OpeningDesign/CTR/XC_struct/calculation_report/ramp_wall/resLC/text/sectReport.tex

\begin{center}

\end{center}
\begin{center}

\end{center}
\newpage

\input{ramp_wall/resLC/text/sections/EBwallRCSects1.tex}
\begin{center}

\end{center}
\begin{center}

\end{center}
\input{ramp_wall/resLC/text/sections/EBwallRCSects2.tex}
\begin{center}

\end{center}
\begin{center}

\end{center}
\input{ramp_wall/resLC/text/sections/WBwallRCSects1.tex}
\begin{center}

\end{center}
\begin{center}

\end{center}
\input{ramp_wall/resLC/text/sections/WBwallRCSects2.tex}
\begin{center}

\end{center}
\begin{center}

\end{center}
\input{ramp_wall/resLC/text/sections/E1FwallRCSects1.tex}
\begin{center}

\end{center}
\begin{center}

\end{center}
\input{ramp_wall/resLC/text/sections/E1FwallRCSects2.tex}
\begin{center}

\end{center}
\begin{center}

\end{center}
\input{ramp_wall/resLC/text/sections/W1FwallRCSects1.tex}
\begin{center}

\end{center}
\begin{center}

\end{center}
\input{ramp_wall/resLC/text/sections/W1FwallRCSects2.tex}
\begin{center}

\end{center}
\begin{center}

\end{center}
\input{ramp_wall/resLC/text/sections/S1FwallRCSects1.tex}
\begin{center}

\end{center}
\begin{center}

\end{center}
\input{ramp_wall/resLC/text/sections/S1FwallRCSects2.tex}
\begin{center}

\end{center}
\begin{center}

\end{center}
