OpeningDesign/CTR/XC_struct/xc_models/wood_structure/stud_wall_design/anchor_bolts/regular_walls_anchor_bolts.ods

Anchor bolts for regular walls
5/8” GALV. BENT ANCHOR BOLT
@ 4’ O.C. (WITHIN 8” OF EVERY CORNER)
7” MIN. EMBEDMENT
