OpeningDesign/CTR/CA/Site Reports and Photos/20200724/20200724 - CTR - Site Report.md

<p align="right" style="" >

</p>

## The Current: Site Report: 07.24.2020

- Holddowns at the 2nd and 3rd floors, for both the east and west stair need to be installed.

- The inspector, will most likely require that this 'dead space' under the stairs be closed off with drywall.  Will most likely require a spinkler as well.  Confirm with Fire Protection engineer.
  
  - 

- Bear concrete slab on 3"x3"x1/4" galv angle attached with 5/8"x5" galv. anchor bolts at 24" o.c."
  
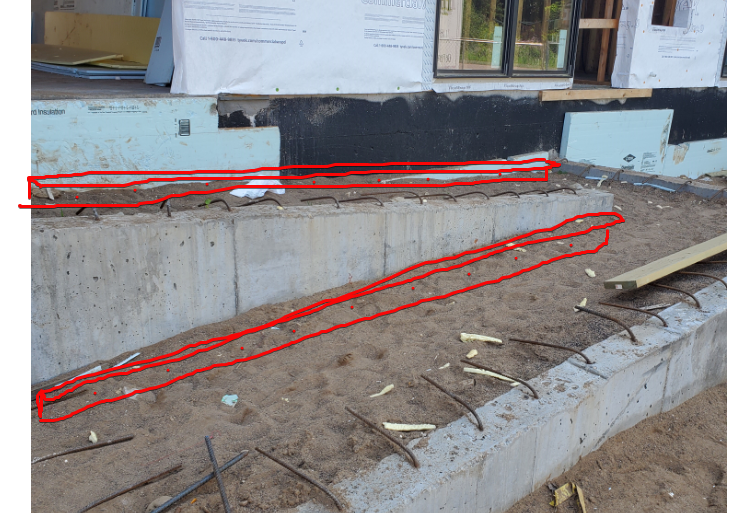
[picture p158: CA/Site Reports and Photos/20200724/2020-07-27_12-56-12_ApplicationFrameHostPhotosApplicationFrameHost.png]
  - 

- Assure the following clearances at Restroom 114
  
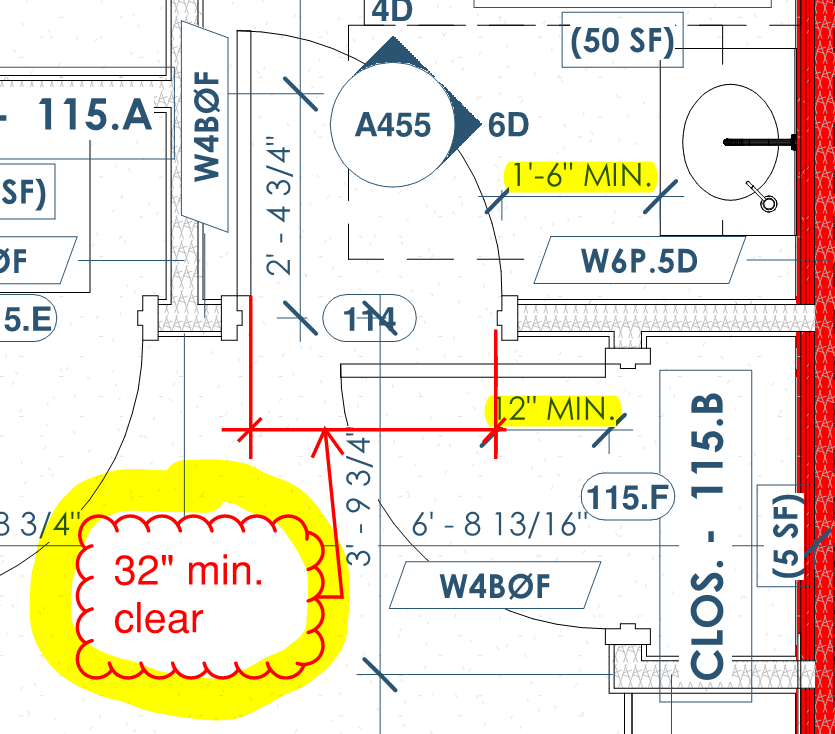
[picture p159: CA/Site Reports and Photos/20200724/2020-07-27_13-22-51_Revu_CTR_Binder_-_Bluebeam_Revu_x64Revu.png]
  - 

- Furr out wall to hide steel on the north elevation
  
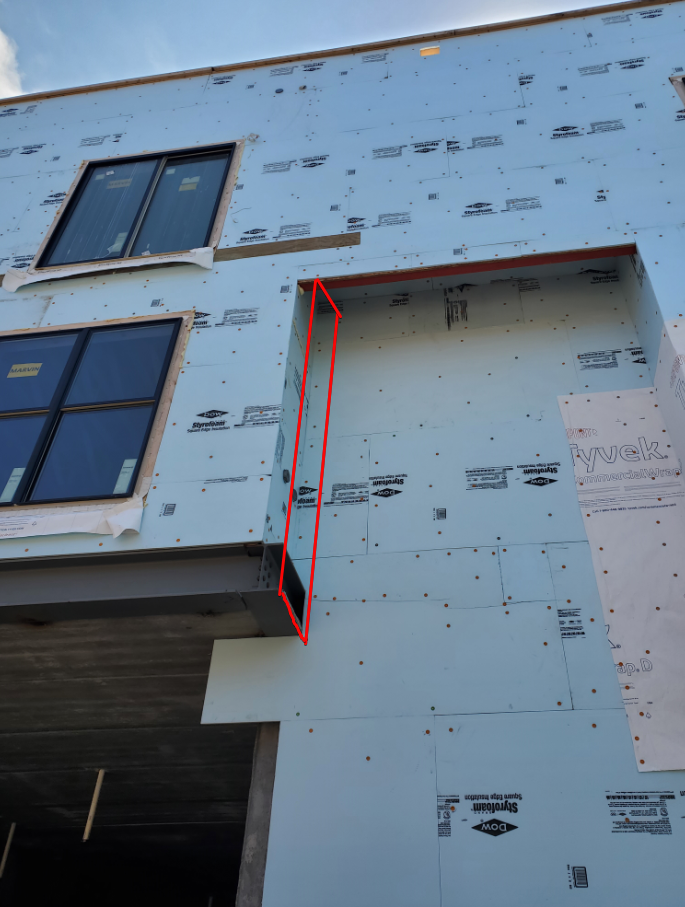
[picture p160: CA/Site Reports and Photos/20200724/2020-07-27_12-47-06_ApplicationFrameHost2020-07-24_13.30.31.jpg_‎-_PhotosApplicationFrameHost.png]
  - 

- Clean all the exposed CMU with wire brush to remove smears of surface mortar. 
  
  - 2020-07-24 13.21.52.jpg

- tighten bolts at all hold downs
  
  - 2020-07-24 13.18.43.jpg

- Missing fasteners at a few hanger locations throughout the various stair well stringers.
  
  - 2020-07-24 12.11.58.jpg

- Please take care to cover exposed concrete and/or CMU from over spray of stair paint. 
  
  - 2020-07-24 13.45.47.jpg

  ---
  
  ### 
  
  ### Outstanding from previous site report.

- Add additional sistered studs at column near LVL at elevator on 1st floor
  
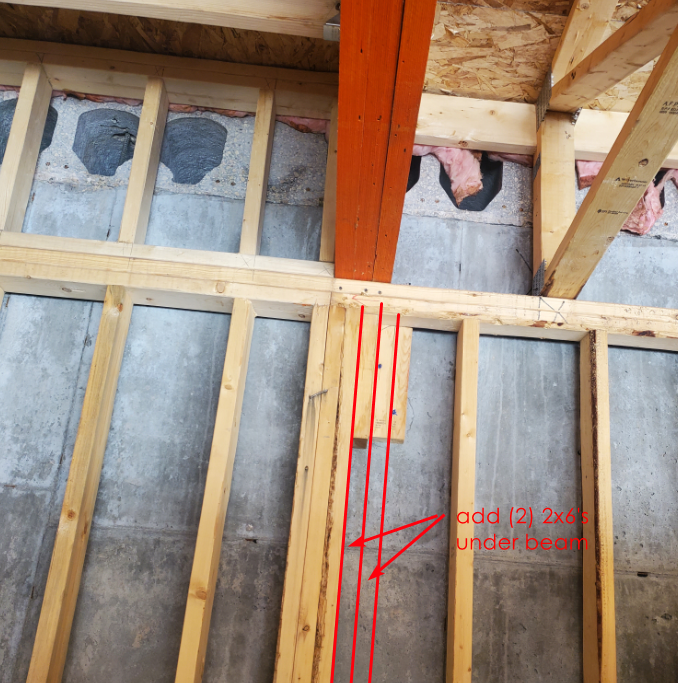
[picture p161: CA/Site Reports and Photos/20200724/2020-05-18-17-37-17-image.png]
  - 
  
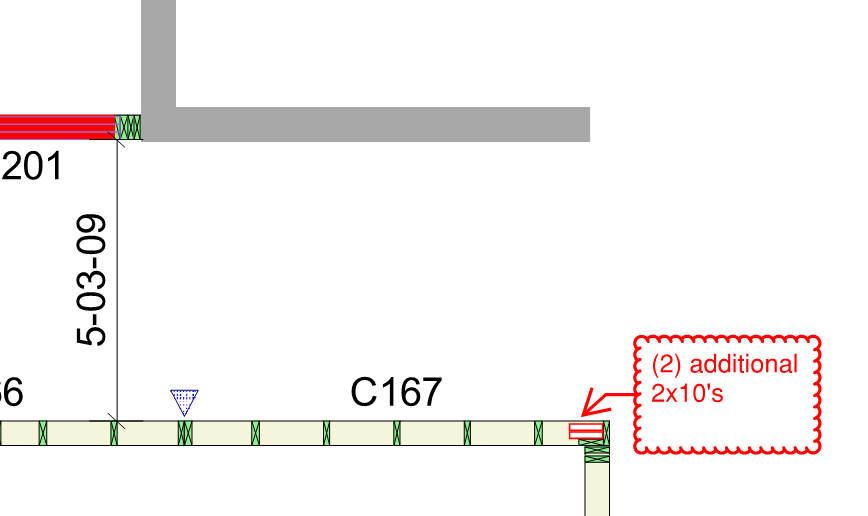
[picture p162: CA/Site Reports and Photos/20200724/2020-05-18-22-09-55-image.png]
  - 

- Add (2) additinal 2x10 at the following corner (near elevator) at both the 2nd and 3rd floors to transfer load down to 2nd floor steel beam
  
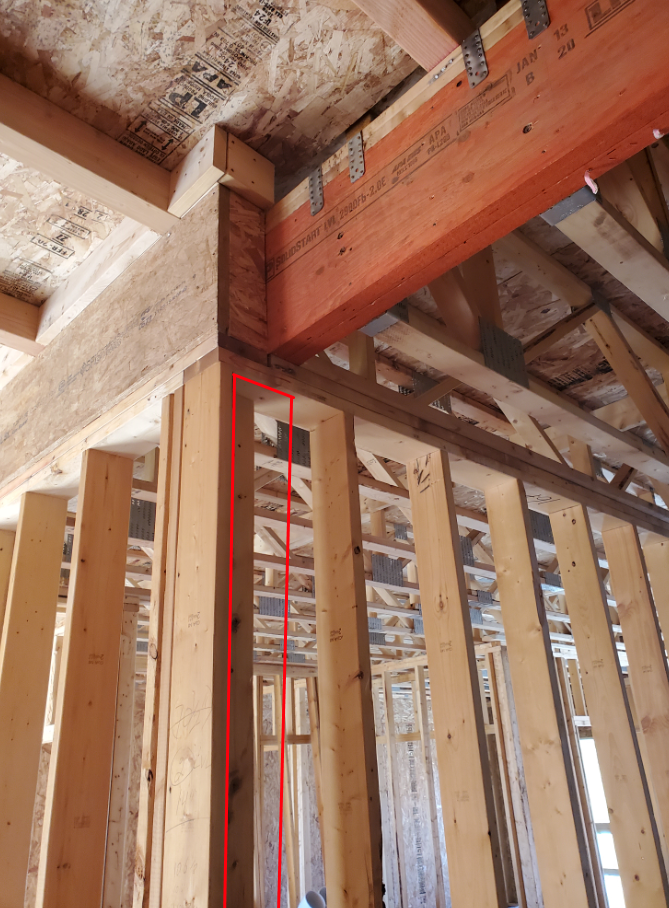
[picture p163: CA/Site Reports and Photos/20200724/2020-05-18-22-13-13-image.png]
  - 

- Add 2x ledger at elevator CMU to support floor sheathing
  
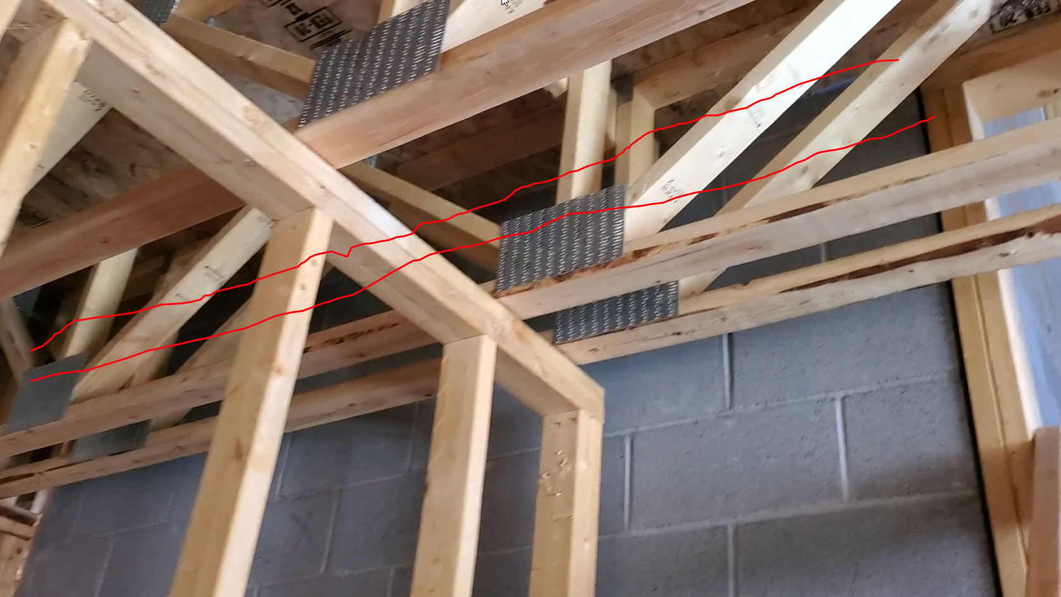
[picture p164: CA/Site Reports and Photos/20200724/2020-05-18-23-53-49-image.png]
  - 
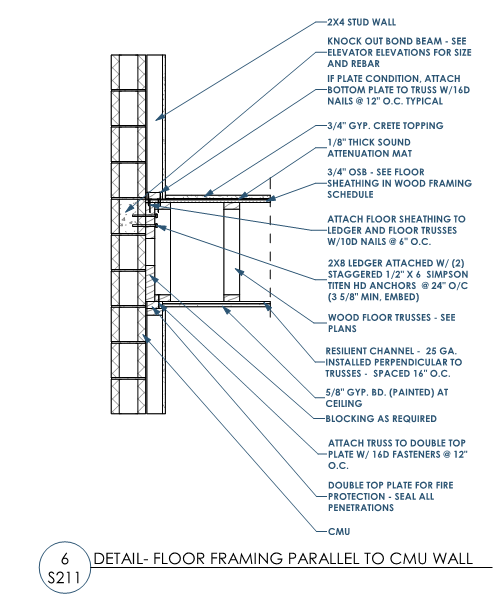
[picture p165: CA/Site Reports and Photos/20200724/2020-05-18-23-55-31-image.png]
  -
