OpeningDesign/CTR/CA/Site Reports and Photos/20200515/20200515 - CTR - Site Report.md

<p align="right" style="" >

</p>

## The Current: Site Report: 05.15.2020

- There were a number of conditions throughout the project where the girder truss that supports the jack trusses at the corner conditons was not sistered together (or it doesn't appear they were) as outlined in the truss shops.  See truss shops for exact detail for sistering

- There was a number of holddowns throughout the project that were missing.  Confirmed with GC that they are still in the process of installing
  
  <!--
  
  - Holddowns were not installed at the shear wall between U106 and U119.
  
  - Holddowns not installed on the west end of the shear wall between stair 108 and U110
  
  - No hold downs at shear wall between U126 and U124
  
  - missing holddowns at shearwall between U114 and U116
  
  - missing holddowns at shearwall between U114 and 105 and 104
  
  - missing holddowns at shearwall between 115 and U107
  
  - missing holddowns at shearwall between U125 and U123
  
  - missing holddowns at shearwall between U201 and 204
  
  - 
  -->

- Blocking above rim board needs (2) SDWS22500BD at each truss--all floors and at roof.  A number of locations only had (1) SDWS22500BD at each truss
  
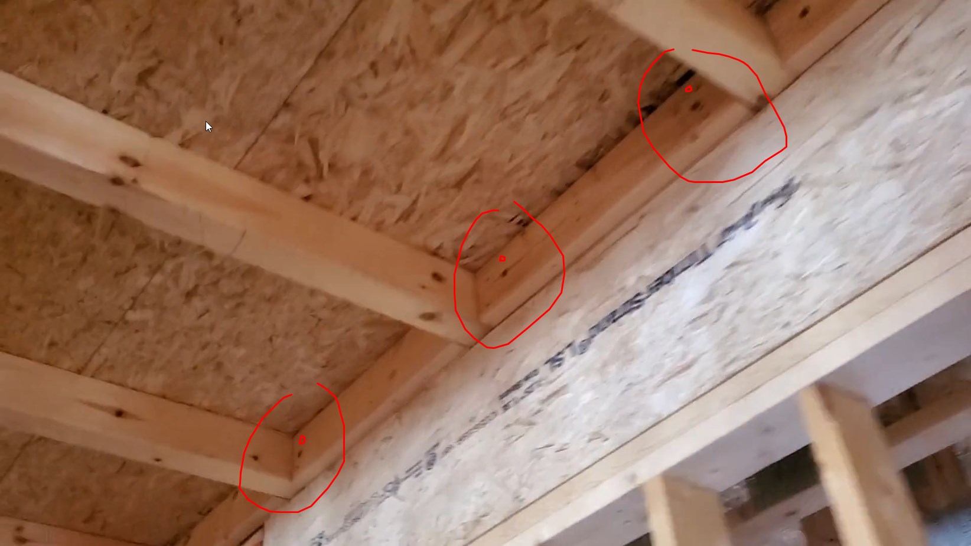
[picture p166: CA/Site Reports and Photos/20200515/vlc_YtFLORPniU.jpg]
  - 
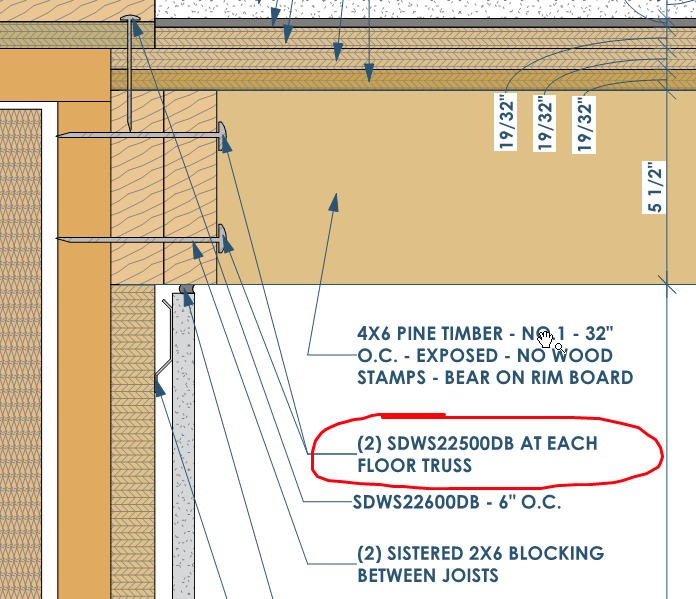
[picture p167: CA/Site Reports and Photos/20200515/2020-05-18-16-49-54-image.png]
  - 

- Install a built-up column of at least (3) 2x6's at all LVL beams throughout project.  Example condition...
  
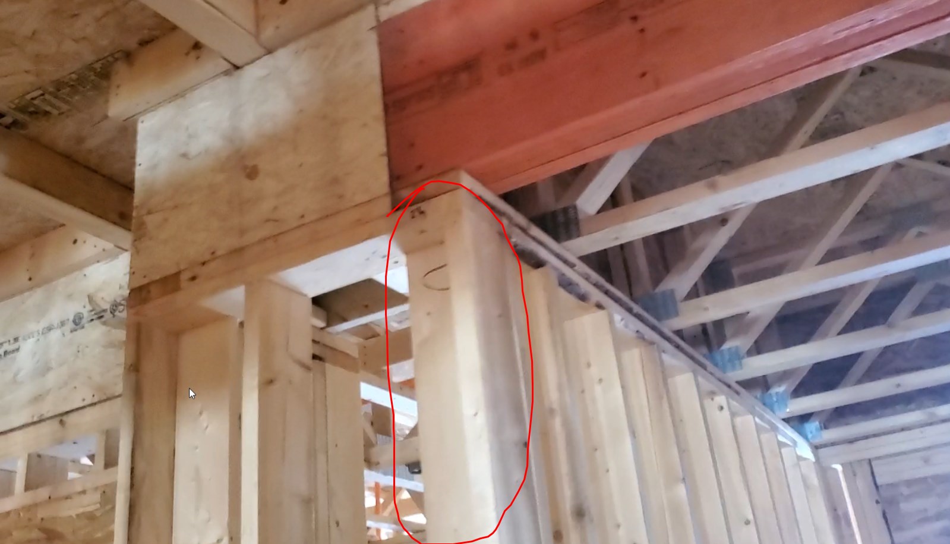
[picture p168: CA/Site Reports and Photos/20200515/ApplicationFrameHost_BQc5Hp7vTn.jpg]
  - 
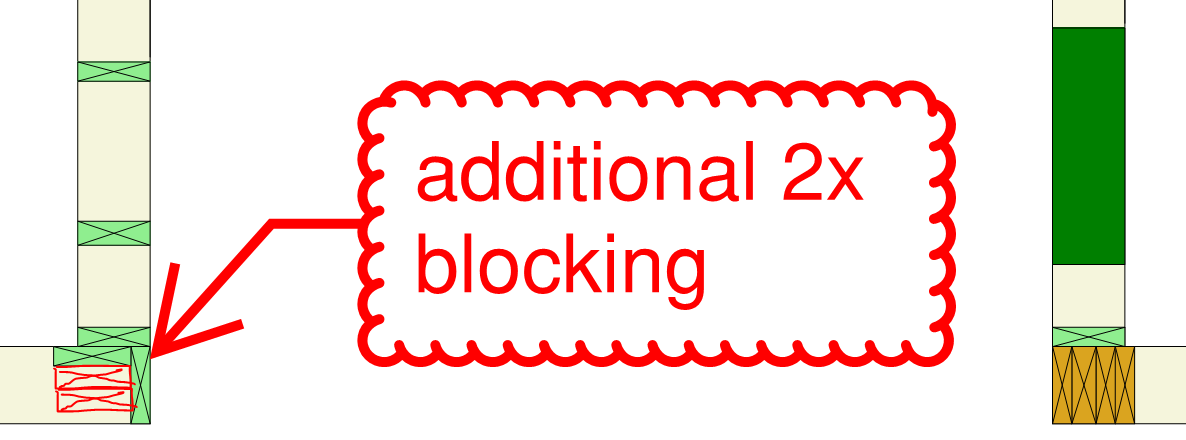
[picture p169: CA/Site Reports and Photos/20200515/2020-05-19-13-23-34-image.png]
  - 

- At Stairs
  
  - need (3) SDWS22600DB - SDWS STRUCTURAL SCREWS @ EACHVERTICAL STUD at the ledgers that bear multiple joists
  
  - need (2) SDWS22600DB - SDWS STRUCTURAL SCREWS @ EACH VERTICAL STUD at ledgers that do not bear joists
  
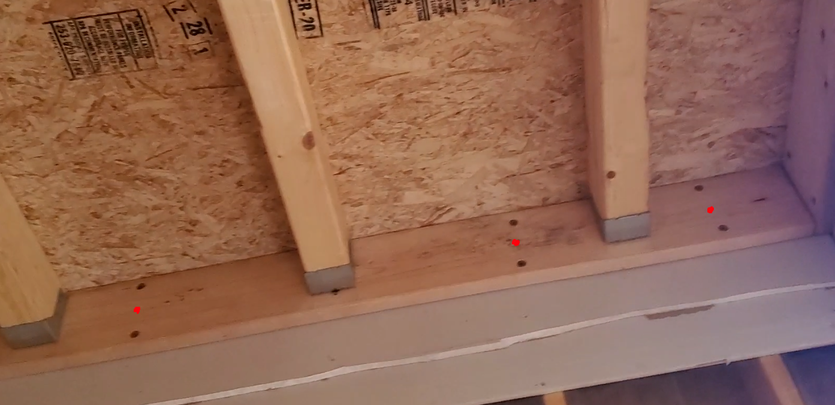
[picture p170: CA/Site Reports and Photos/20200515/vlc_ktL7A223v1.png]
  - 
  
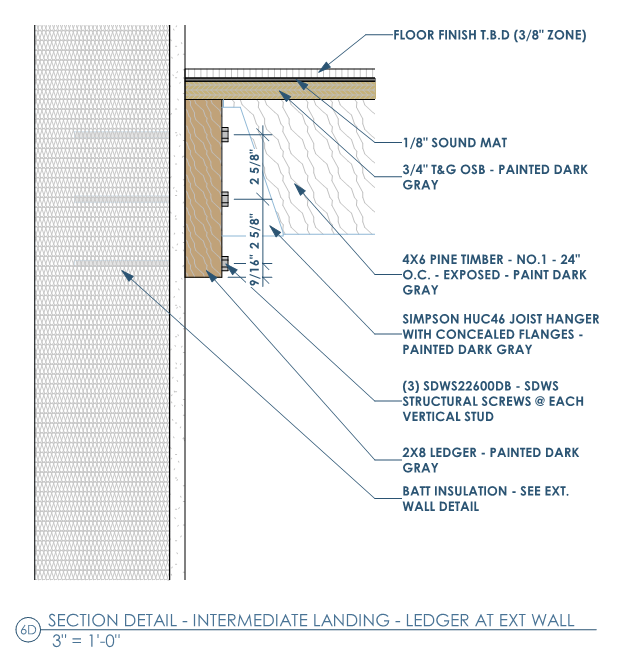
[picture p171: CA/Site Reports and Photos/20200515/Revu_8T4KtlkG9r.png]
  - 

- Add additional sistered studs at column near LVL at elevator on 1st floor
  
  - 

- At 3rd floor stair: Not enough room to slide (2) layers of drywall and 1/2" resilent channel between truss and stud.  Either move the truss or wrap truss with (2) layers of 5/8" Gyp. Bd--to continue 2hr wall up to deck.
  
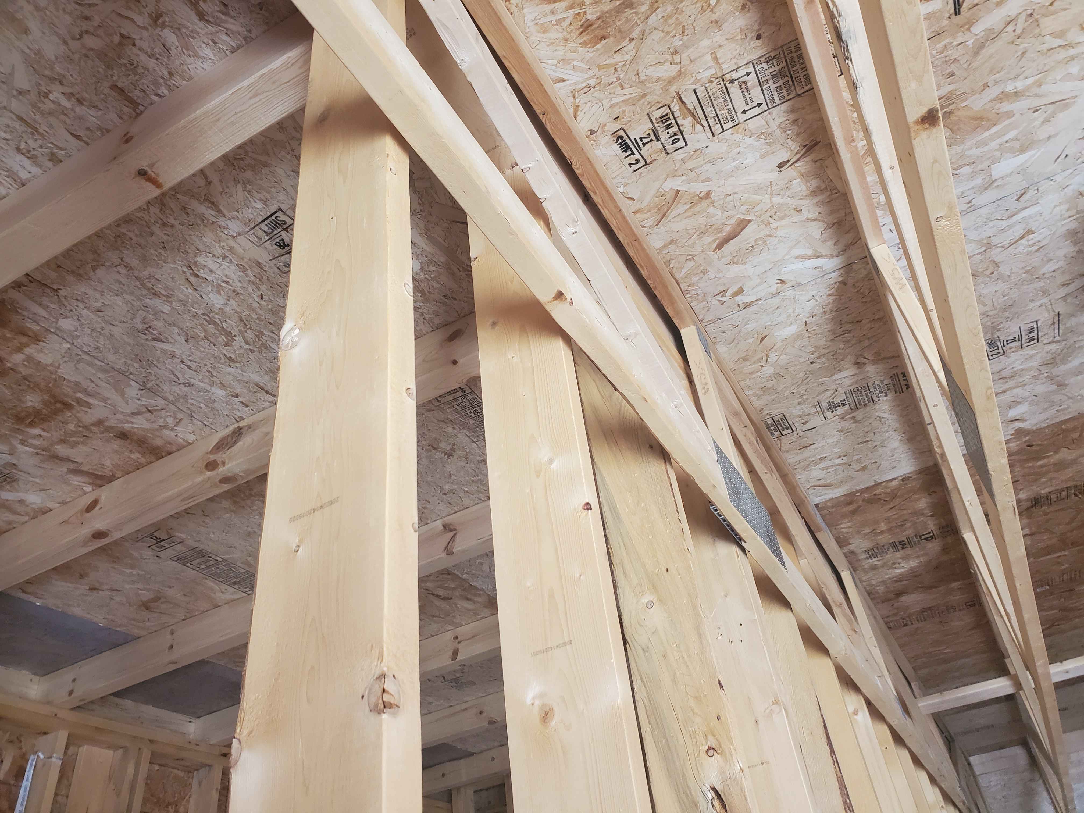
[picture p172: CA/Site Reports and Photos/20200515/14.13.54-3rd floor at roof near stair.jpg]
  - 

- Spacing of 4x6's at roof at/near stair is incorrect.  Need to be 24" o.c. at stair. 16" o.c. outside stair at corrido--to support the condensing units on the roof.
  
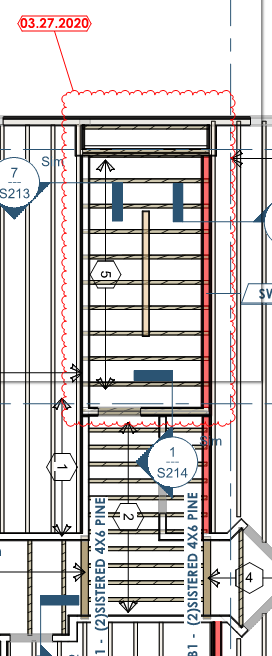
[picture p173: CA/Site Reports and Photos/20200515/2020-05-18-21-44-04-image.png]
  - 
  
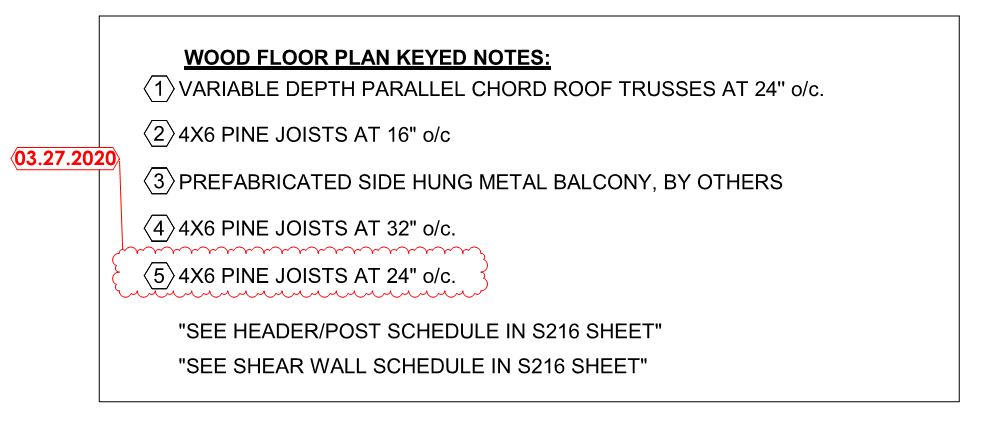
[picture p174: CA/Site Reports and Photos/20200515/2020-05-18-21-44-25-image.png]
  - 

- Add (2) additinal 2x10 at the following corner (near elevator) at both the 2nd and 3rd floors to transfer load down to 2nd floor steel beam
  
  - 
  - 

- Blocking at these conditions, similar to hallway, for the drywall to die into
  
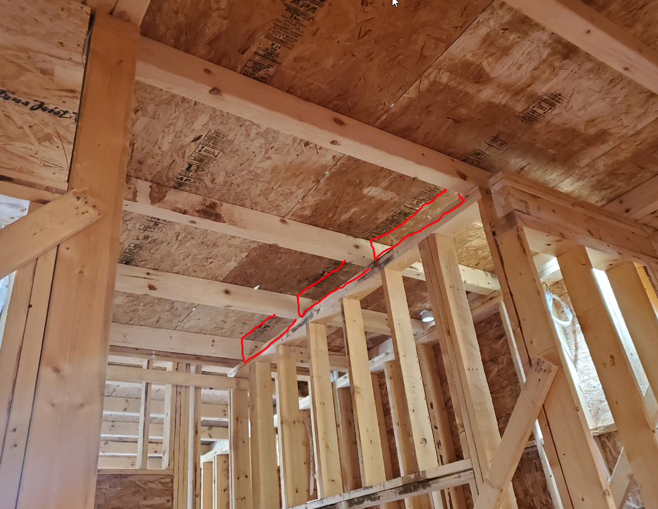
[picture p175: CA/Site Reports and Photos/20200515/2020-05-18-22-15-47-image.png]
  - 

- Blocking at entry to support load of balcony load down through wall studs
  
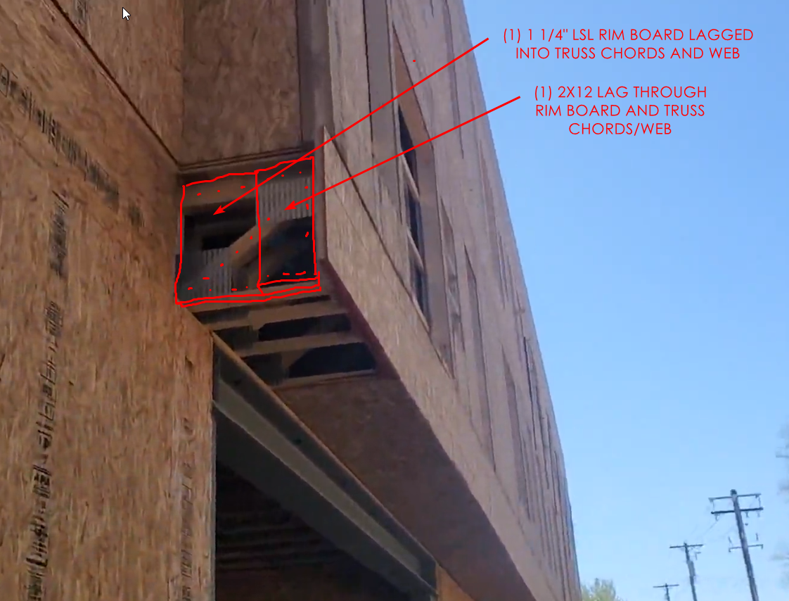
[picture p176: CA/Site Reports and Photos/20200515/vlc_qVF9NKEfCI.png]
  - 

- Add 2x ledger at elevator CMU to support floor sheathing
  
  - 
  - 

- Roof trusses need tie downs at all conditions on exterior and interior bearing walls--install was in progress.

<!--stackedit_data:
eyJoaXN0b3J5IjpbLTUzNzYwNjM1LDExMzk2NjQyMzYsMjA5MD
QwMTIwNCwyMTQ1ODQxNjcyLC0xMDkzMzQxMTMyXX0=
-->
