OpeningDesign/CTR/XC_struct/calculation_report/ramp_wall/resLC/text/report_resSimplLC.tex

\begin{figure}
\begin{center}
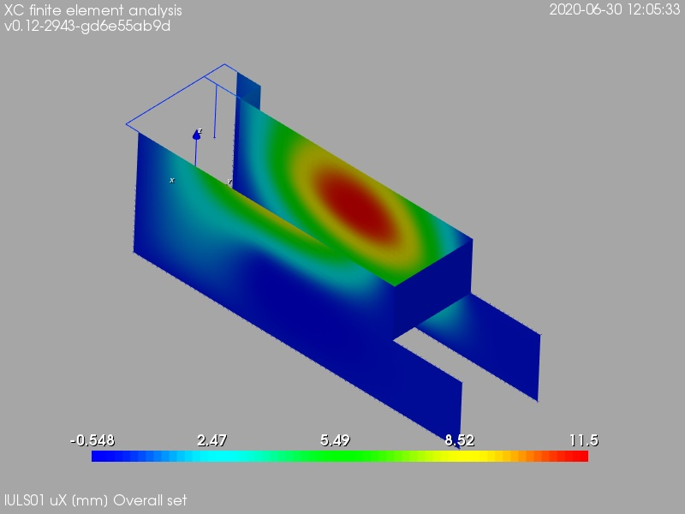
[picture p177: XC_struct/calculation_report/ramp_wall/resLC/text/graphics/resSimplLC/lULS01overallSetuX.jpg]

\caption{ULS01. Overall set, displacement in global X direction, [mm]}
\end{center}
\end{figure}
\begin{figure}
\begin{center}
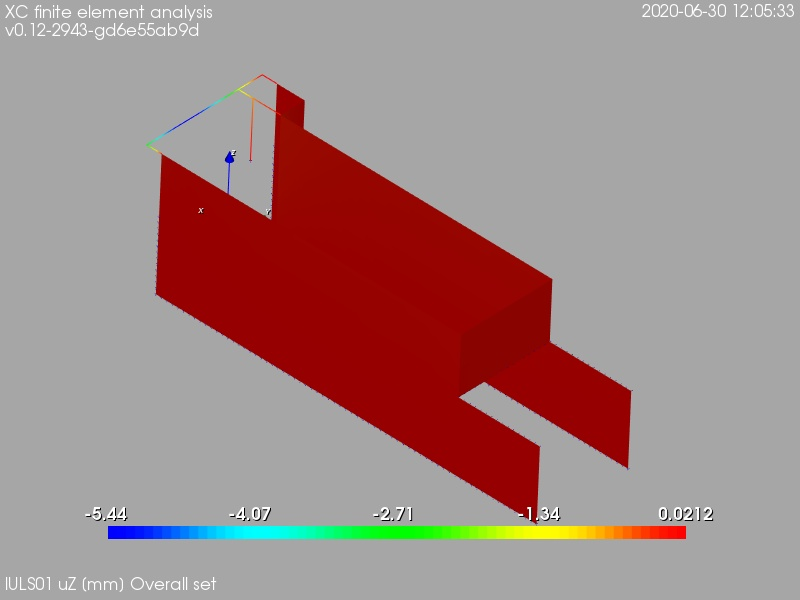
[picture p178: XC_struct/calculation_report/ramp_wall/resLC/text/graphics/resSimplLC/lULS01overallSetuZ.jpg]

\caption{ULS01. Overall set, displacement in global Z direction, [mm]}
\end{center}
\end{figure}
\begin{figure}
\begin{center}
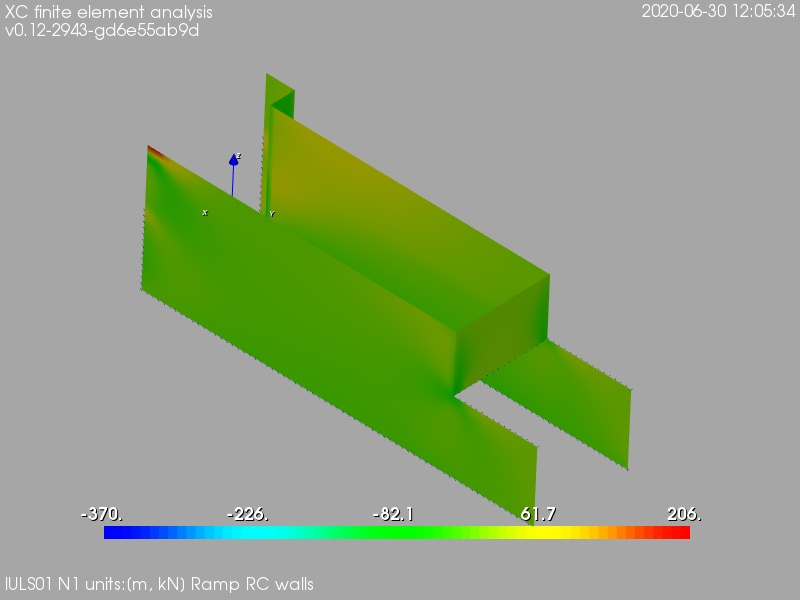
[picture p179: XC_struct/calculation_report/ramp_wall/resLC/text/graphics/resSimplLC/lULS01wallsN1.jpg]

\caption{ULS01. Ramp rc walls, internal axial force in local direction 1, units:[m, kN]}
\end{center}
\end{figure}
\begin{figure}
\begin{center}
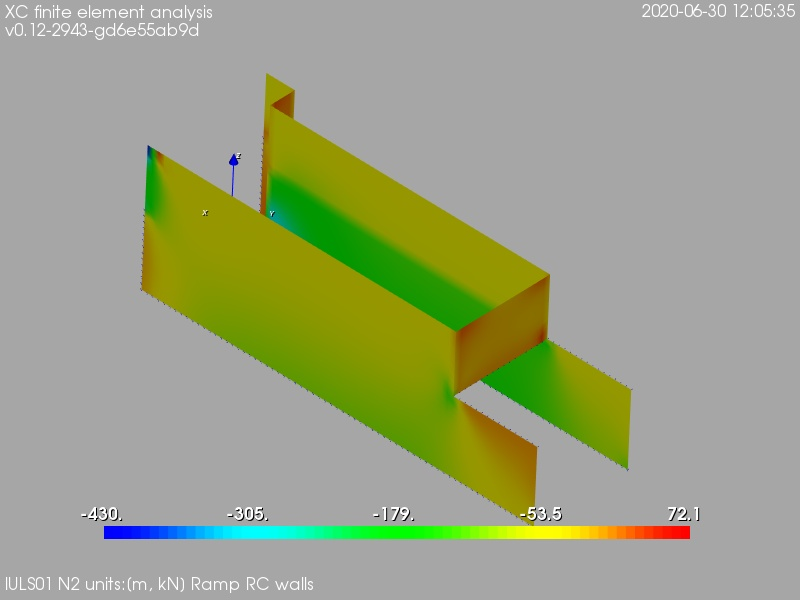
[picture p180: XC_struct/calculation_report/ramp_wall/resLC/text/graphics/resSimplLC/lULS01wallsN2.jpg]

\caption{ULS01. Ramp rc walls, internal axial force in local direction 2, units:[m, kN]}
\end{center}
\end{figure}
\begin{figure}
\begin{center}
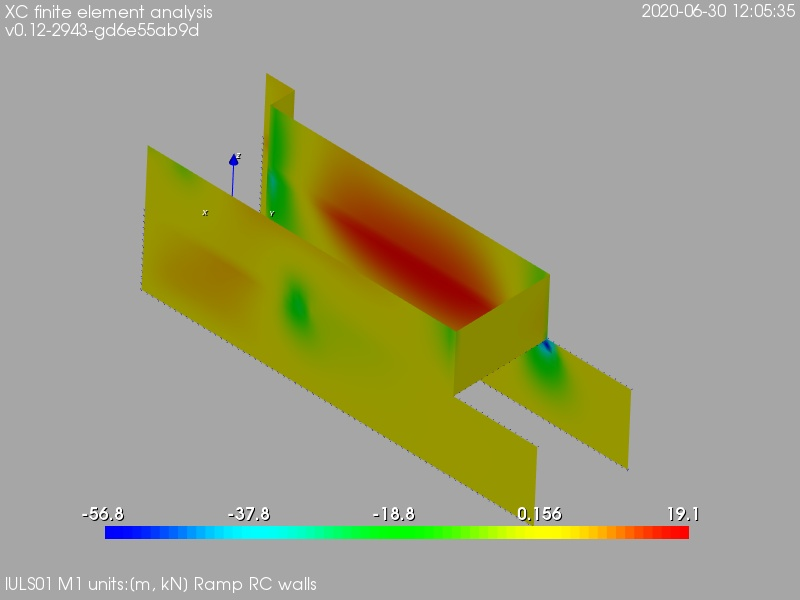
[picture p181: XC_struct/calculation_report/ramp_wall/resLC/text/graphics/resSimplLC/lULS01wallsM1.jpg]

\caption{ULS01. Ramp rc walls, bending moment about local axis 1, units:[m, kN]}
\end{center}
\end{figure}
\begin{figure}
\begin{center}
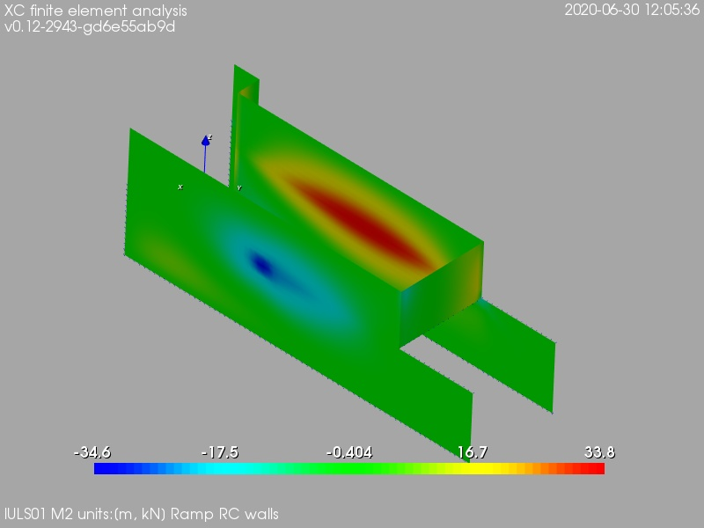
[picture p182: XC_struct/calculation_report/ramp_wall/resLC/text/graphics/resSimplLC/lULS01wallsM2.jpg]

\caption{ULS01. Ramp rc walls, bending moment about local axis 2, units:[m, kN]}
\end{center}
\end{figure}
\begin{figure}
\begin{center}
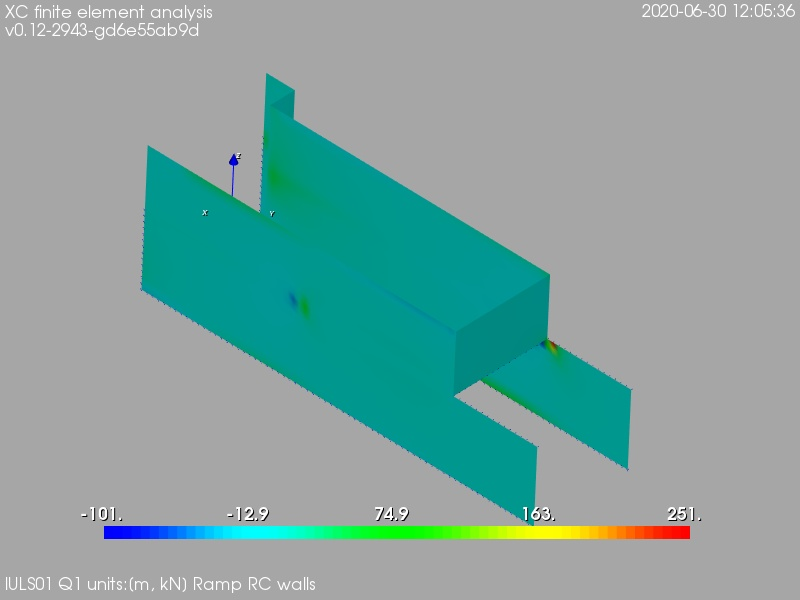
[picture p183: XC_struct/calculation_report/ramp_wall/resLC/text/graphics/resSimplLC/lULS01wallsQ1.jpg]

\caption{ULS01. Ramp rc walls, internal shear force in local direction 1, units:[m, kN]}
\end{center}
\end{figure}
\begin{figure}
\begin{center}
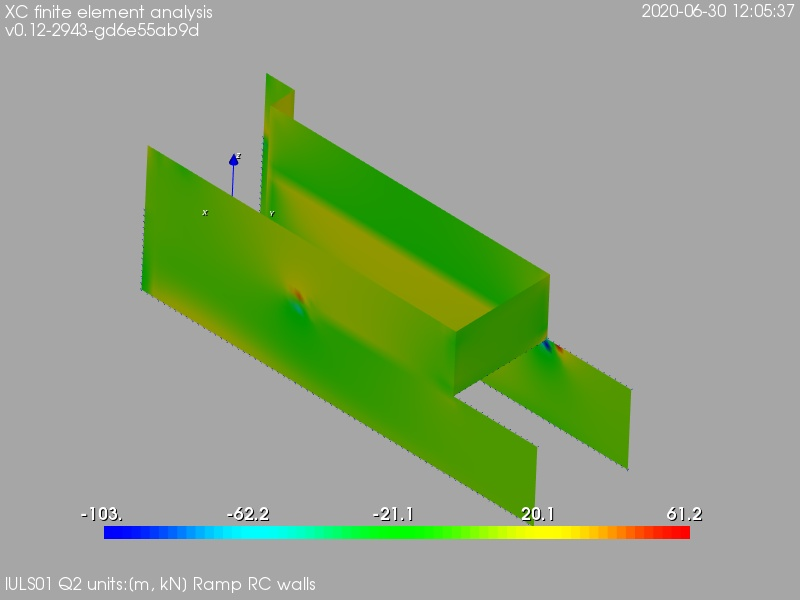
[picture p184: XC_struct/calculation_report/ramp_wall/resLC/text/graphics/resSimplLC/lULS01wallsQ2.jpg]

\caption{ULS01. Ramp rc walls, internal shear force in local direction 2, units:[m, kN]}
\end{center}
\end{figure}
\begin{figure}
\begin{center}
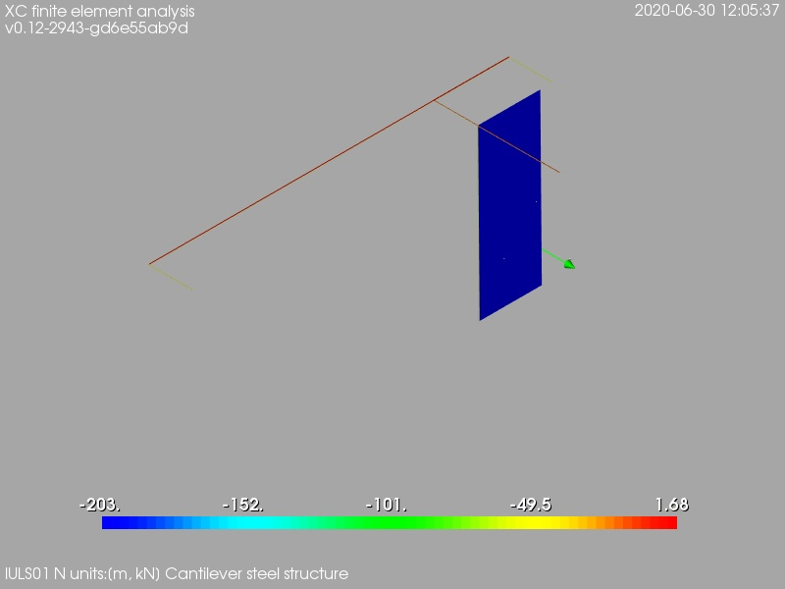
[picture p185: XC_struct/calculation_report/ramp_wall/resLC/text/graphics/resSimplLC/lULS01steelMembersN.jpg]

\caption{ULS01. Cantilever steel structure, internal axial force, units:[m, kN]}
\end{center}
\end{figure}
\begin{figure}
\begin{center}
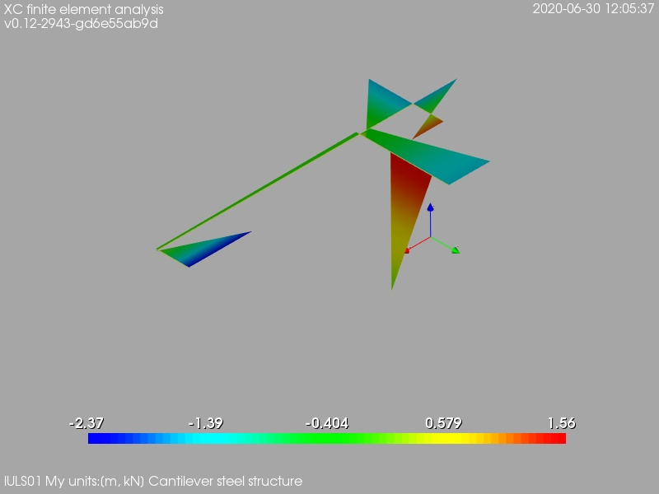
[picture p186: XC_struct/calculation_report/ramp_wall/resLC/text/graphics/resSimplLC/lULS01steelMembersMy.jpg]

\caption{ULS01. Cantilever steel structure, bending moment about local axis y, units:[m, kN]}
\end{center}
\end{figure}
\begin{figure}
\begin{center}
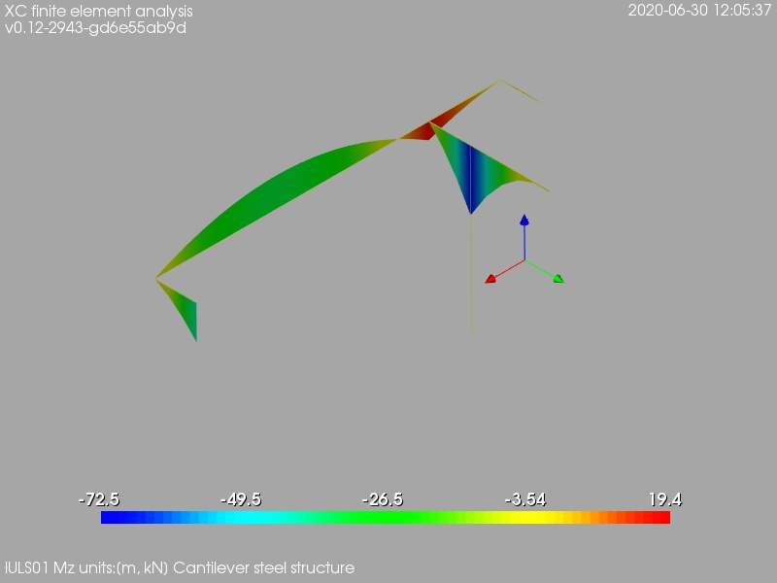
[picture p187: XC_struct/calculation_report/ramp_wall/resLC/text/graphics/resSimplLC/lULS01steelMembersMz.jpg]

\caption{ULS01. Cantilever steel structure, bending moment about local axis z, units:[m, kN]}
\end{center}
\end{figure}
\begin{figure}
\begin{center}
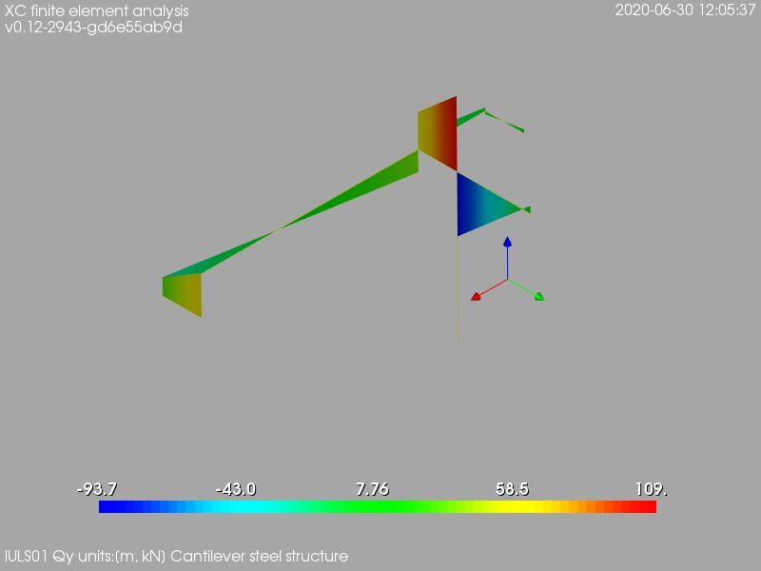
[picture p188: XC_struct/calculation_report/ramp_wall/resLC/text/graphics/resSimplLC/lULS01steelMembersQy.jpg]

\caption{ULS01. Cantilever steel structure, internal shear force in local direction y, units:[m, kN]}
\end{center}
\end{figure}
\begin{figure}
\begin{center}
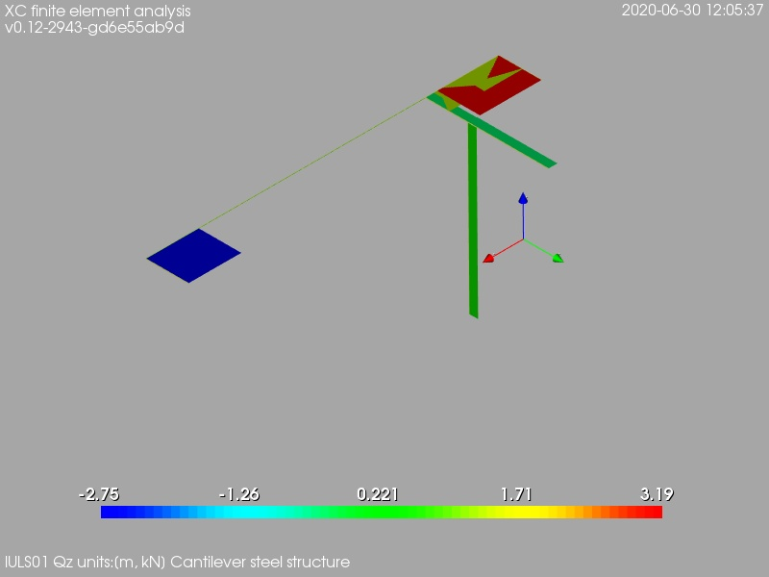
[picture p189: XC_struct/calculation_report/ramp_wall/resLC/text/graphics/resSimplLC/lULS01steelMembersQz.jpg]

\caption{ULS01. Cantilever steel structure, internal shear force in local direction z, units:[m, kN]}
\end{center}
\end{figure}
\clearpage
\begin{figure}
\begin{center}
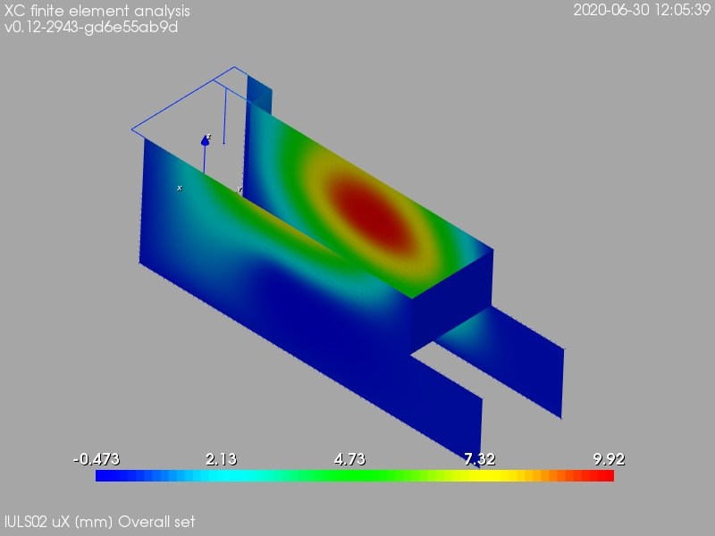
[picture p190: XC_struct/calculation_report/ramp_wall/resLC/text/graphics/resSimplLC/lULS02overallSetuX.jpg]

\caption{ULS02. Overall set, displacement in global X direction, [mm]}
\end{center}
\end{figure}
\begin{figure}
\begin{center}
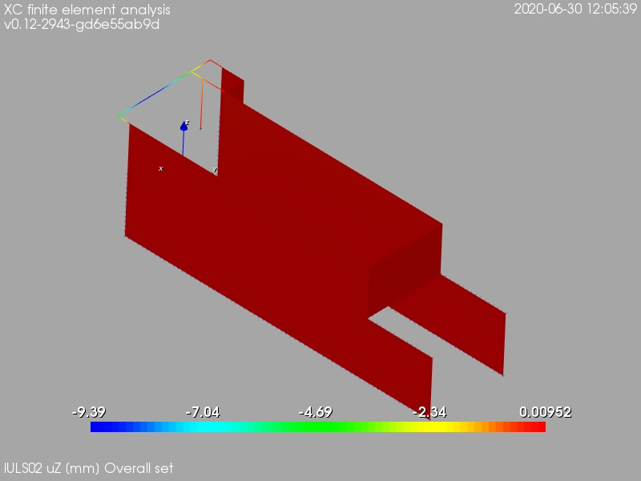
[picture p191: XC_struct/calculation_report/ramp_wall/resLC/text/graphics/resSimplLC/lULS02overallSetuZ.jpg]

\caption{ULS02. Overall set, displacement in global Z direction, [mm]}
\end{center}
\end{figure}
\begin{figure}
\begin{center}
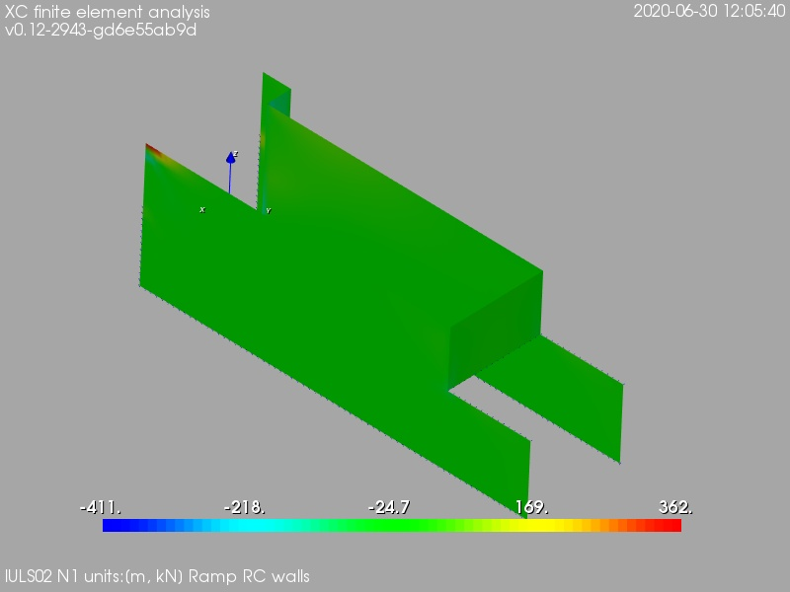
[picture p192: XC_struct/calculation_report/ramp_wall/resLC/text/graphics/resSimplLC/lULS02wallsN1.jpg]

\caption{ULS02. Ramp rc walls, internal axial force in local direction 1, units:[m, kN]}
\end{center}
\end{figure}
\begin{figure}
\begin{center}
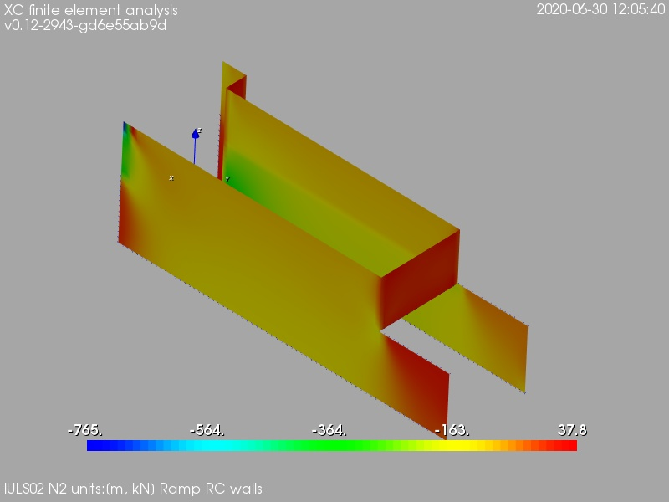
[picture p193: XC_struct/calculation_report/ramp_wall/resLC/text/graphics/resSimplLC/lULS02wallsN2.jpg]

\caption{ULS02. Ramp rc walls, internal axial force in local direction 2, units:[m, kN]}
\end{center}
\end{figure}
\begin{figure}
\begin{center}
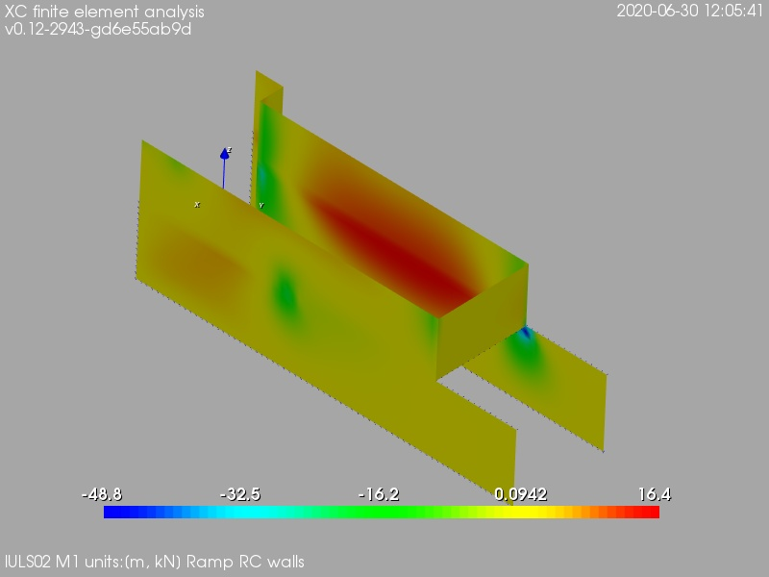
[picture p194: XC_struct/calculation_report/ramp_wall/resLC/text/graphics/resSimplLC/lULS02wallsM1.jpg]

\caption{ULS02. Ramp rc walls, bending moment about local axis 1, units:[m, kN]}
\end{center}
\end{figure}
\begin{figure}
\begin{center}
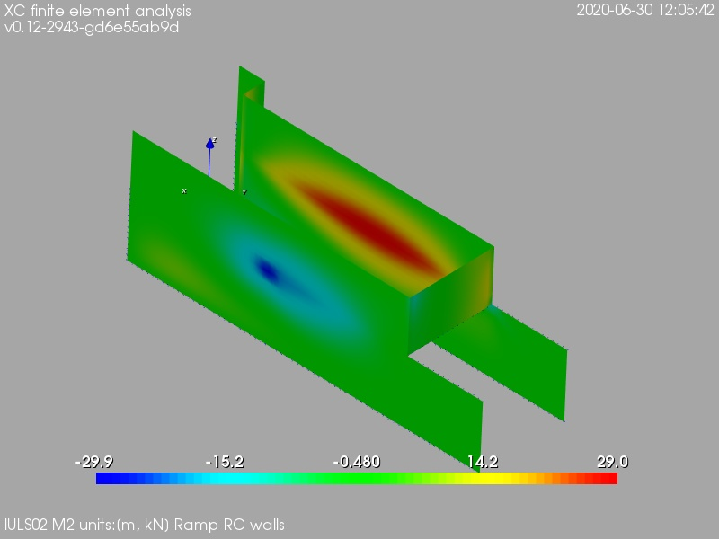
[picture p195: XC_struct/calculation_report/ramp_wall/resLC/text/graphics/resSimplLC/lULS02wallsM2.jpg]

\caption{ULS02. Ramp rc walls, bending moment about local axis 2, units:[m, kN]}
\end{center}
\end{figure}
\begin{figure}
\begin{center}
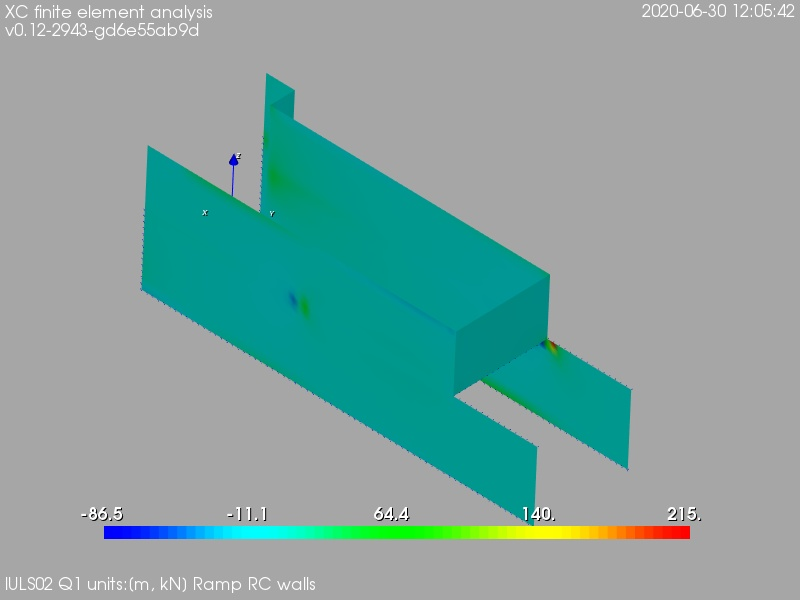
[picture p196: XC_struct/calculation_report/ramp_wall/resLC/text/graphics/resSimplLC/lULS02wallsQ1.jpg]

\caption{ULS02. Ramp rc walls, internal shear force in local direction 1, units:[m, kN]}
\end{center}
\end{figure}
\begin{figure}
\begin{center}
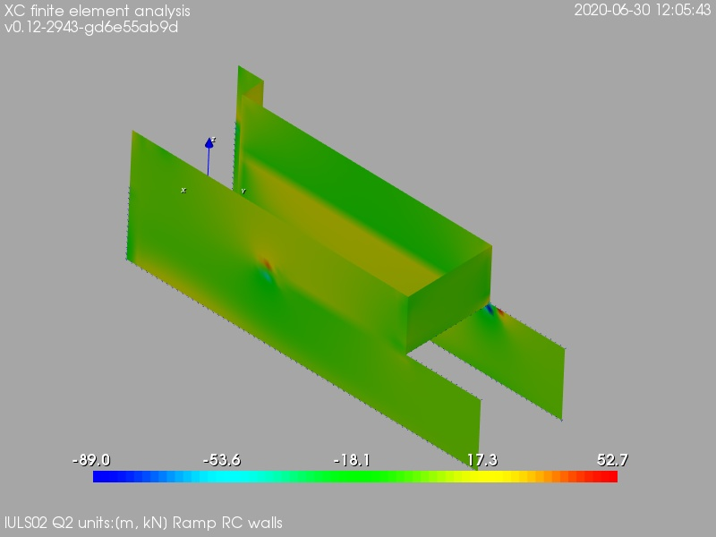
[picture p197: XC_struct/calculation_report/ramp_wall/resLC/text/graphics/resSimplLC/lULS02wallsQ2.jpg]

\caption{ULS02. Ramp rc walls, internal shear force in local direction 2, units:[m, kN]}
\end{center}
\end{figure}
\begin{figure}
\begin{center}
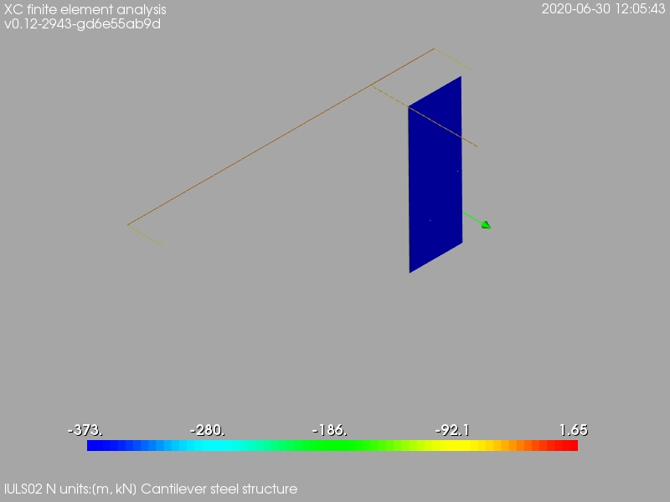
[picture p198: XC_struct/calculation_report/ramp_wall/resLC/text/graphics/resSimplLC/lULS02steelMembersN.jpg]

\caption{ULS02. Cantilever steel structure, internal axial force, units:[m, kN]}
\end{center}
\end{figure}
\begin{figure}
\begin{center}
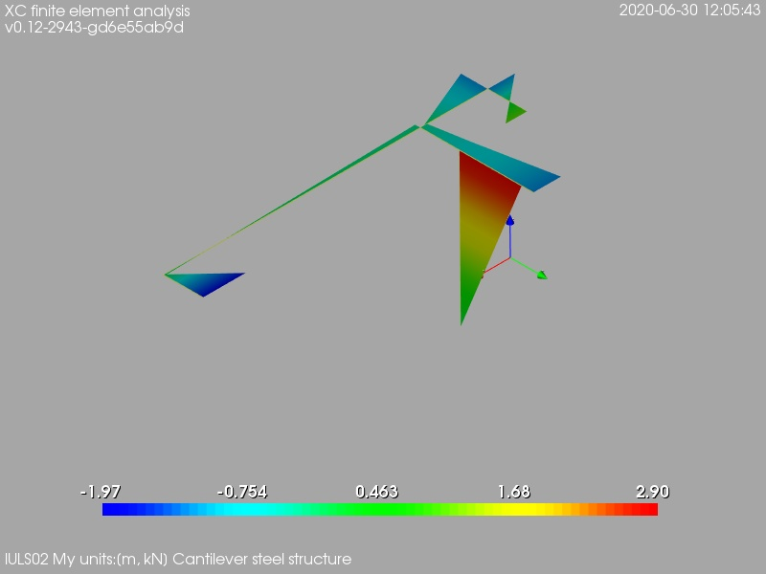
[picture p199: XC_struct/calculation_report/ramp_wall/resLC/text/graphics/resSimplLC/lULS02steelMembersMy.jpg]

\caption{ULS02. Cantilever steel structure, bending moment about local axis y, units:[m, kN]}
\end{center}
\end{figure}
\begin{figure}
\begin{center}
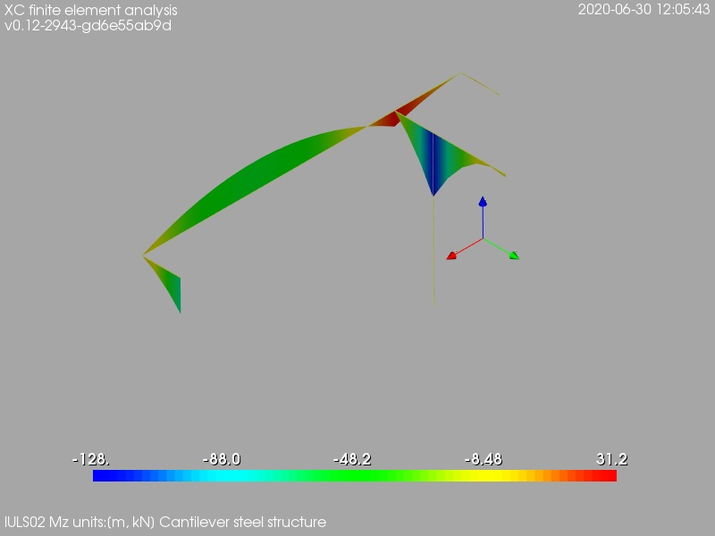
[picture p200: XC_struct/calculation_report/ramp_wall/resLC/text/graphics/resSimplLC/lULS02steelMembersMz.jpg]

\caption{ULS02. Cantilever steel structure, bending moment about local axis z, units:[m, kN]}
\end{center}
\end{figure}
\begin{figure}
\begin{center}
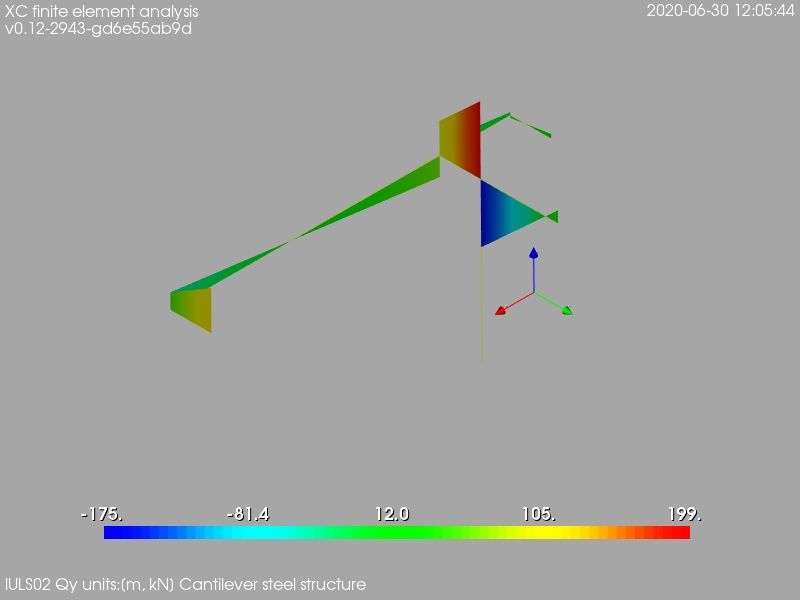
[picture p201: XC_struct/calculation_report/ramp_wall/resLC/text/graphics/resSimplLC/lULS02steelMembersQy.jpg]

\caption{ULS02. Cantilever steel structure, internal shear force in local direction y, units:[m, kN]}
\end{center}
\end{figure}
\begin{figure}
\begin{center}
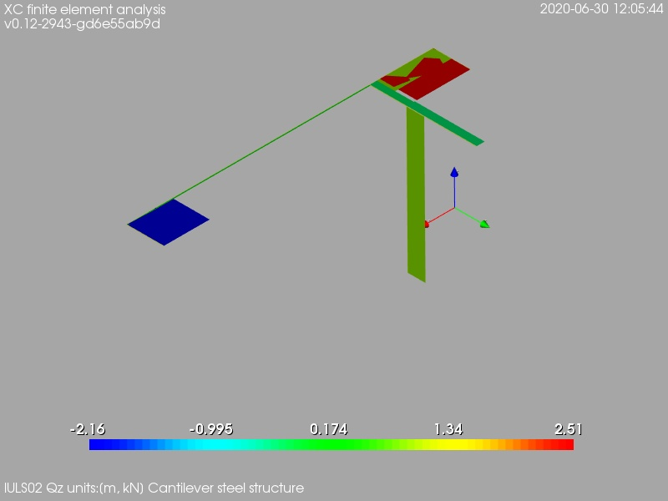
[picture p202: XC_struct/calculation_report/ramp_wall/resLC/text/graphics/resSimplLC/lULS02steelMembersQz.jpg]

\caption{ULS02. Cantilever steel structure, internal shear force in local direction z, units:[m, kN]}
\end{center}
\end{figure}
\clearpage
\begin{figure}
\begin{center}
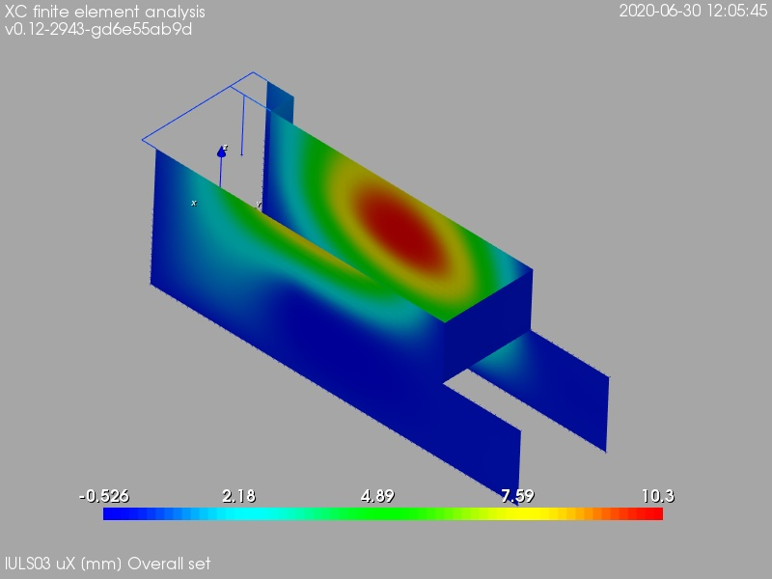
[picture p203: XC_struct/calculation_report/ramp_wall/resLC/text/graphics/resSimplLC/lULS03overallSetuX.jpg]

\caption{ULS03. Overall set, displacement in global X direction, [mm]}
\end{center}
\end{figure}
\begin{figure}
\begin{center}
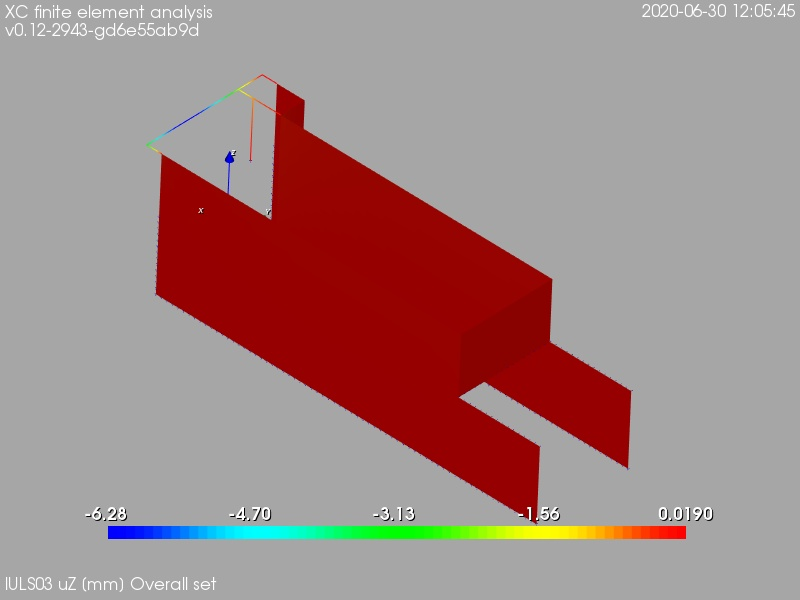
[picture p204: XC_struct/calculation_report/ramp_wall/resLC/text/graphics/resSimplLC/lULS03overallSetuZ.jpg]

\caption{ULS03. Overall set, displacement in global Z direction, [mm]}
\end{center}
\end{figure}
\begin{figure}
\begin{center}
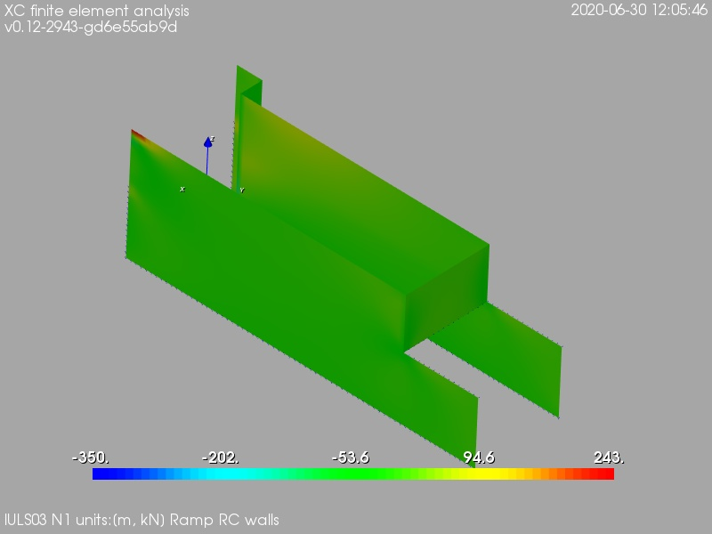
[picture p205: XC_struct/calculation_report/ramp_wall/resLC/text/graphics/resSimplLC/lULS03wallsN1.jpg]

\caption{ULS03. Ramp rc walls, internal axial force in local direction 1, units:[m, kN]}
\end{center}
\end{figure}
\begin{figure}
\begin{center}
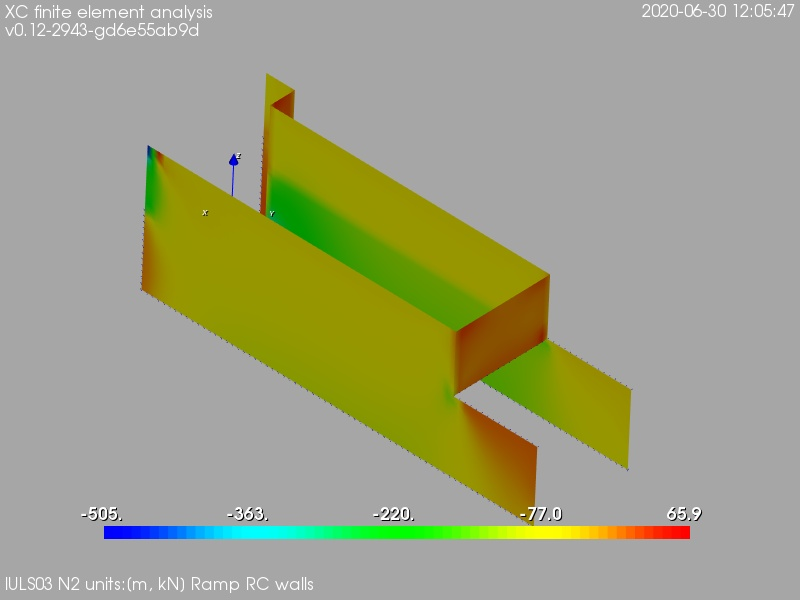
[picture p206: XC_struct/calculation_report/ramp_wall/resLC/text/graphics/resSimplLC/lULS03wallsN2.jpg]

\caption{ULS03. Ramp rc walls, internal axial force in local direction 2, units:[m, kN]}
\end{center}
\end{figure}
\begin{figure}
\begin{center}
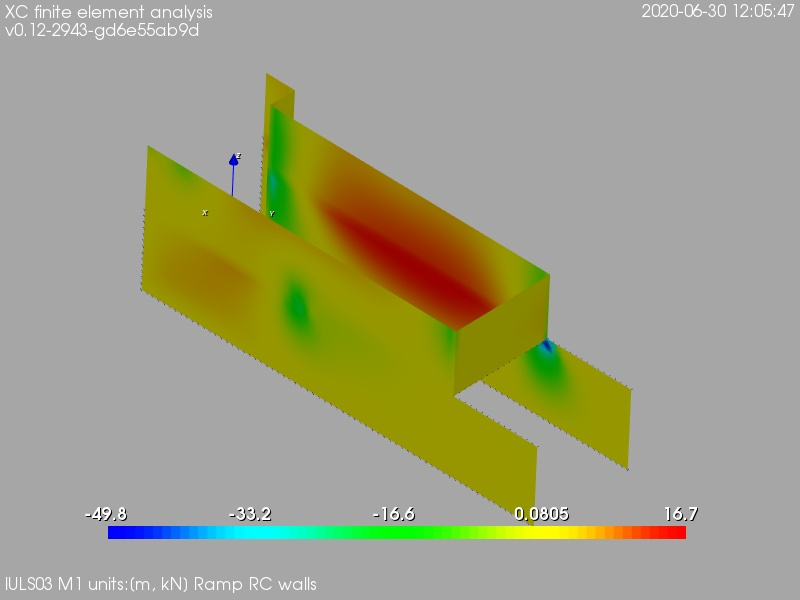
[picture p207: XC_struct/calculation_report/ramp_wall/resLC/text/graphics/resSimplLC/lULS03wallsM1.jpg]

\caption{ULS03. Ramp rc walls, bending moment about local axis 1, units:[m, kN]}
\end{center}
\end{figure}
\begin{figure}
\begin{center}
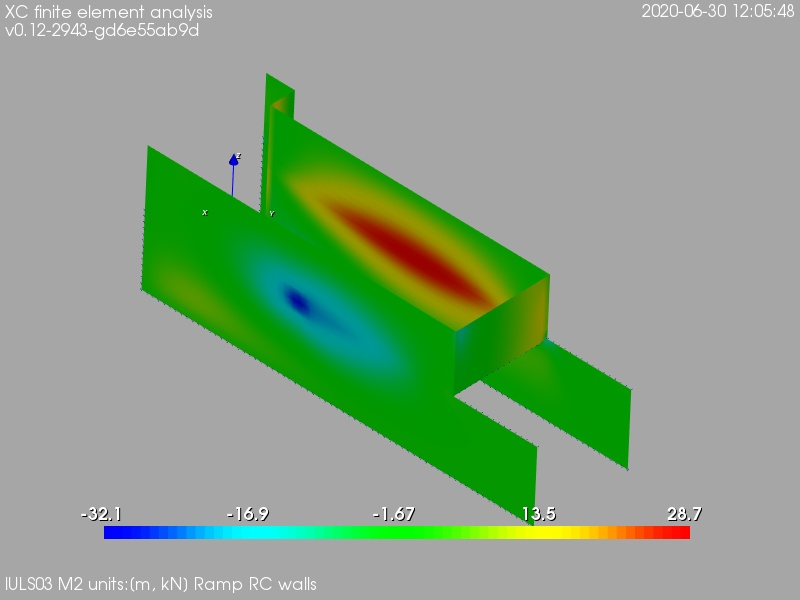
[picture p208: XC_struct/calculation_report/ramp_wall/resLC/text/graphics/resSimplLC/lULS03wallsM2.jpg]

\caption{ULS03. Ramp rc walls, bending moment about local axis 2, units:[m, kN]}
\end{center}
\end{figure}
\begin{figure}
\begin{center}
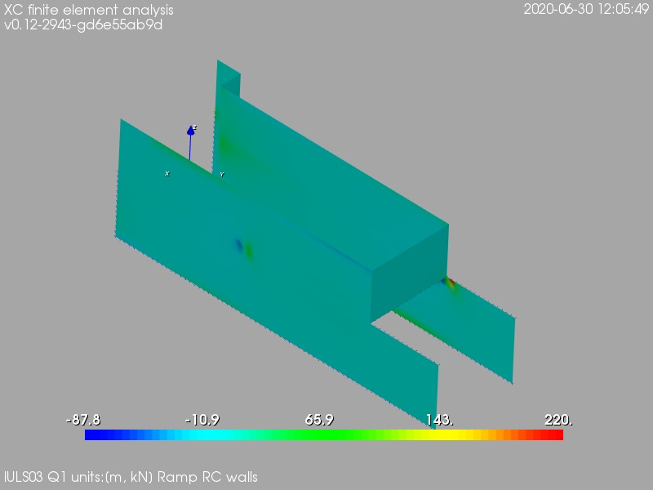
[picture p209: XC_struct/calculation_report/ramp_wall/resLC/text/graphics/resSimplLC/lULS03wallsQ1.jpg]

\caption{ULS03. Ramp rc walls, internal shear force in local direction 1, units:[m, kN]}
\end{center}
\end{figure}
\begin{figure}
\begin{center}
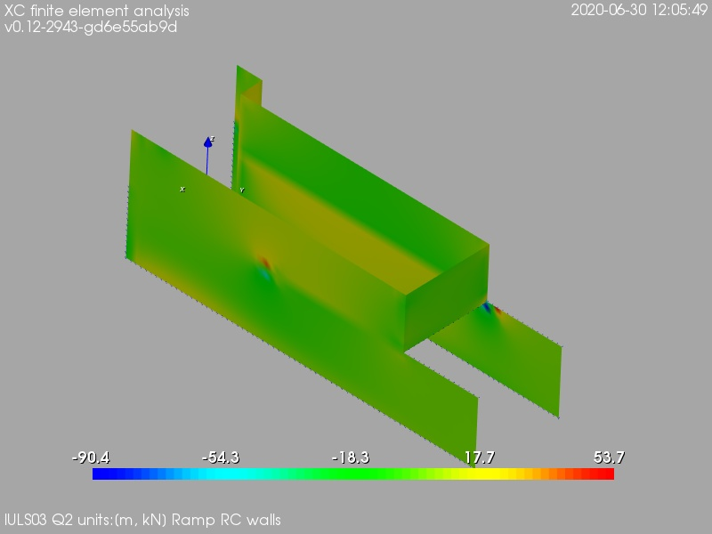
[picture p210: XC_struct/calculation_report/ramp_wall/resLC/text/graphics/resSimplLC/lULS03wallsQ2.jpg]

\caption{ULS03. Ramp rc walls, internal shear force in local direction 2, units:[m, kN]}
\end{center}
\end{figure}
\begin{figure}
\begin{center}
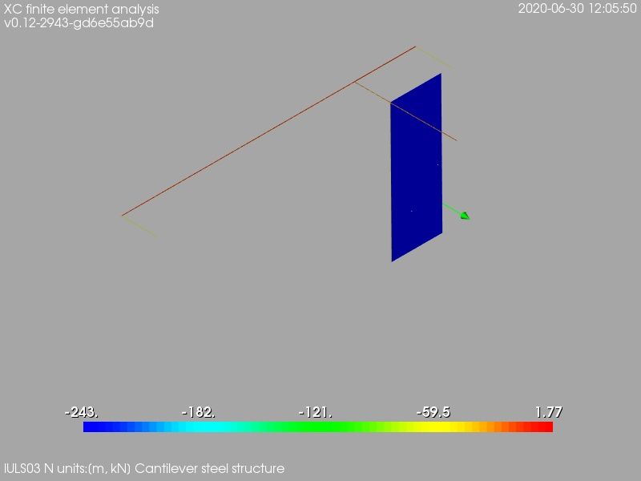
[picture p211: XC_struct/calculation_report/ramp_wall/resLC/text/graphics/resSimplLC/lULS03steelMembersN.jpg]

\caption{ULS03. Cantilever steel structure, internal axial force, units:[m, kN]}
\end{center}
\end{figure}
\begin{figure}
\begin{center}
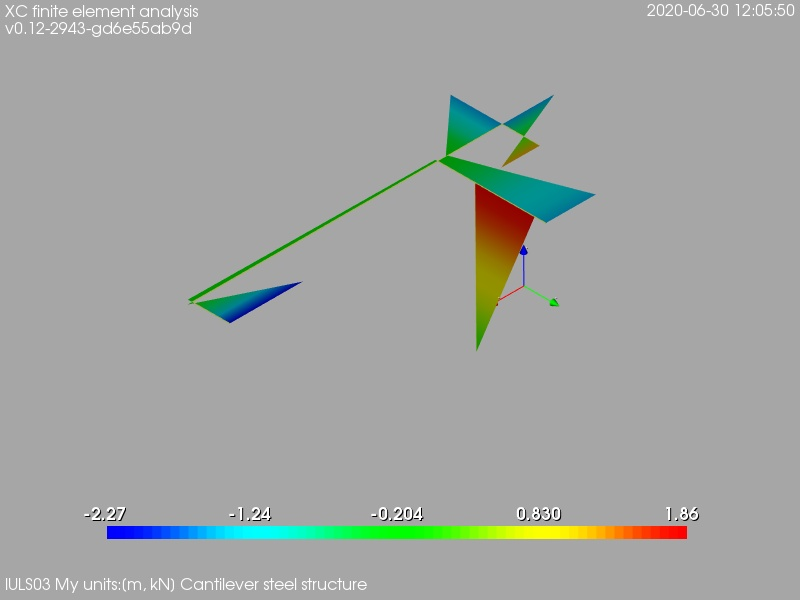
[picture p212: XC_struct/calculation_report/ramp_wall/resLC/text/graphics/resSimplLC/lULS03steelMembersMy.jpg]

\caption{ULS03. Cantilever steel structure, bending moment about local axis y, units:[m, kN]}
\end{center}
\end{figure}
\begin{figure}
\begin{center}
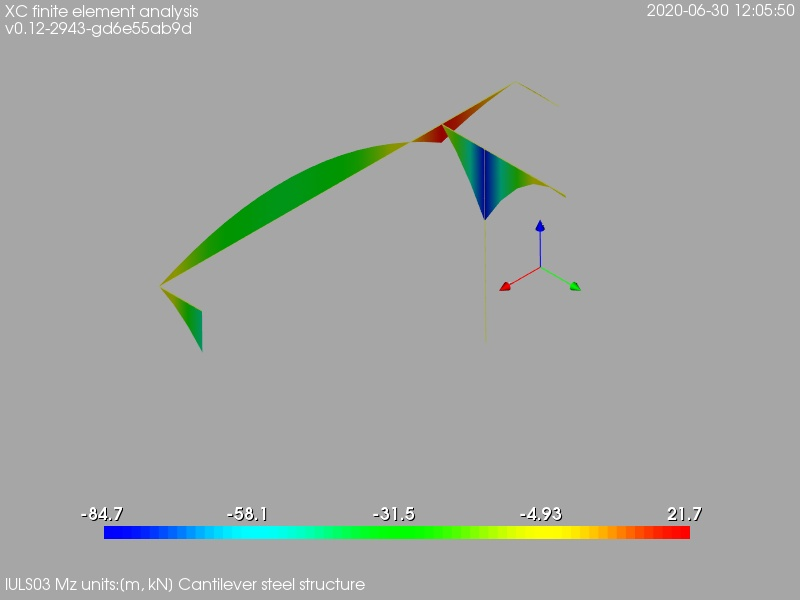
[picture p213: XC_struct/calculation_report/ramp_wall/resLC/text/graphics/resSimplLC/lULS03steelMembersMz.jpg]

\caption{ULS03. Cantilever steel structure, bending moment about local axis z, units:[m, kN]}
\end{center}
\end{figure}
\begin{figure}
\begin{center}
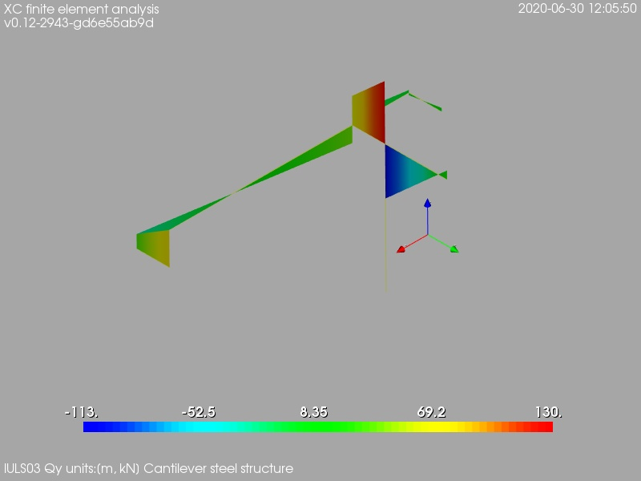
[picture p214: XC_struct/calculation_report/ramp_wall/resLC/text/graphics/resSimplLC/lULS03steelMembersQy.jpg]

\caption{ULS03. Cantilever steel structure, internal shear force in local direction y, units:[m, kN]}
\end{center}
\end{figure}
\begin{figure}
\begin{center}
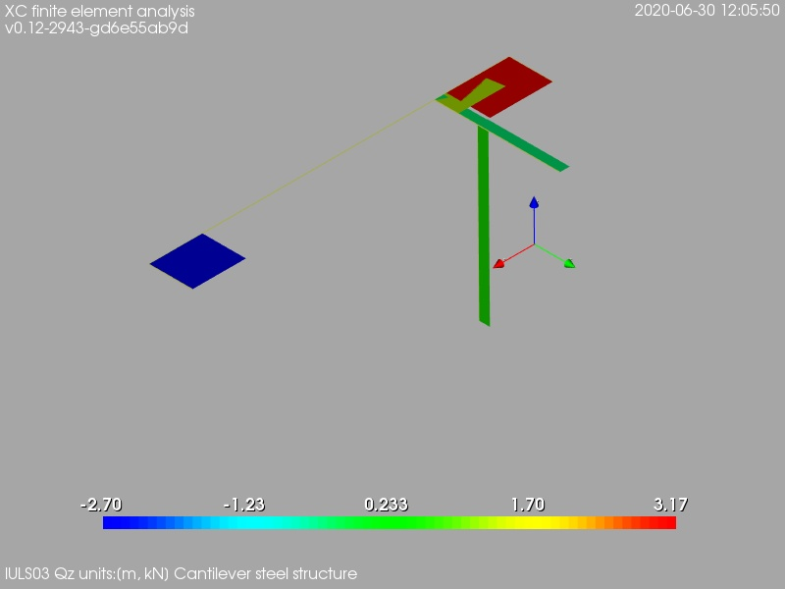
[picture p215: XC_struct/calculation_report/ramp_wall/resLC/text/graphics/resSimplLC/lULS03steelMembersQz.jpg]

\caption{ULS03. Cantilever steel structure, internal shear force in local direction z, units:[m, kN]}
\end{center}
\end{figure}
\clearpage
\begin{figure}
\begin{center}
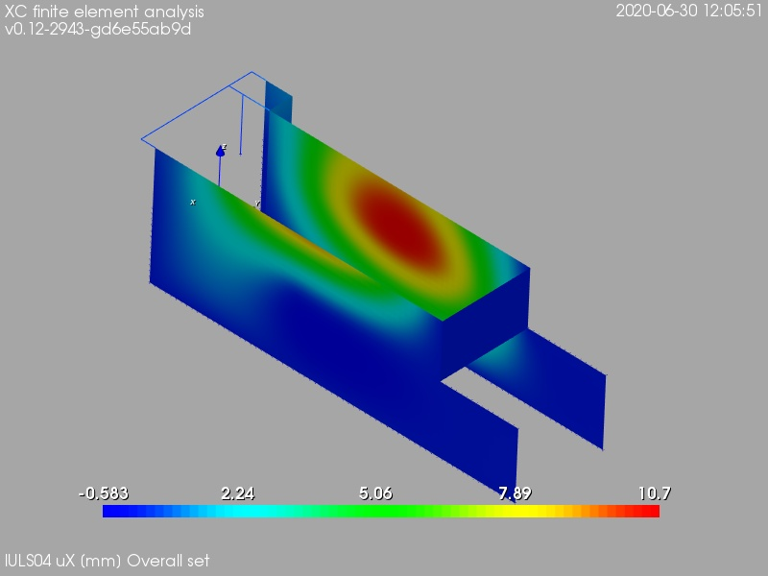
[picture p216: XC_struct/calculation_report/ramp_wall/resLC/text/graphics/resSimplLC/lULS04overallSetuX.jpg]

\caption{ULS04. Overall set, displacement in global X direction, [mm]}
\end{center}
\end{figure}
\begin{figure}
\begin{center}
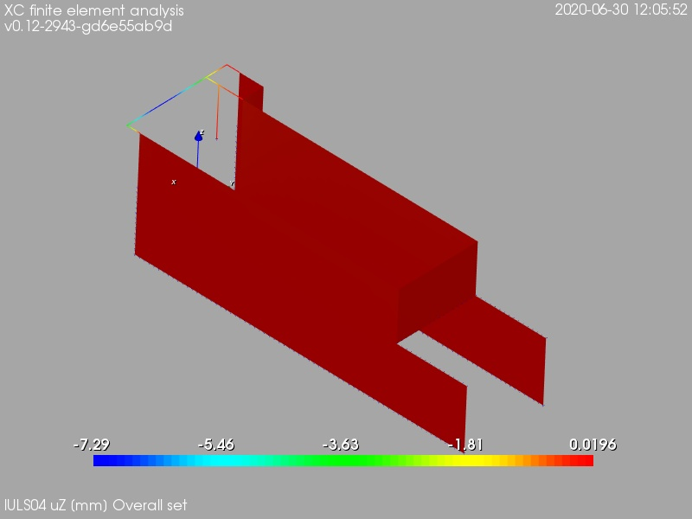
[picture p217: XC_struct/calculation_report/ramp_wall/resLC/text/graphics/resSimplLC/lULS04overallSetuZ.jpg]

\caption{ULS04. Overall set, displacement in global Z direction, [mm]}
\end{center}
\end{figure}
\begin{figure}
\begin{center}
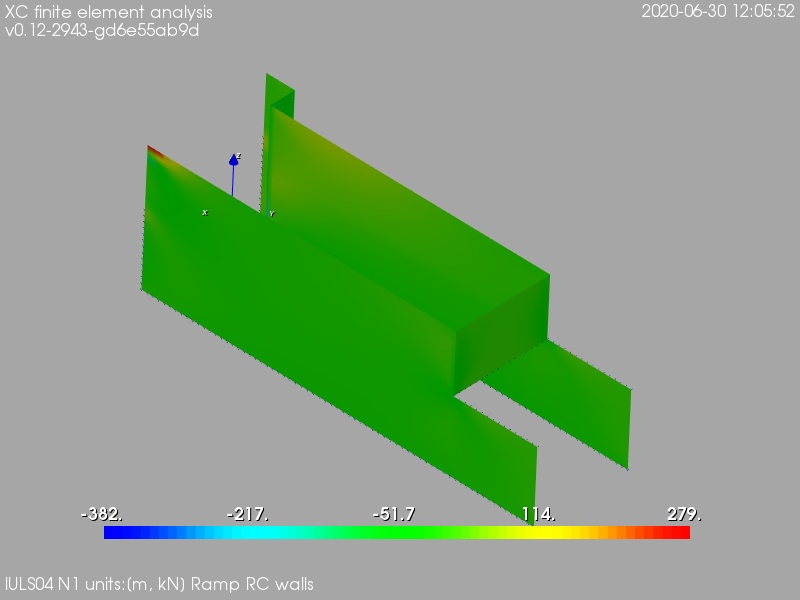
[picture p218: XC_struct/calculation_report/ramp_wall/resLC/text/graphics/resSimplLC/lULS04wallsN1.jpg]

\caption{ULS04. Ramp rc walls, internal axial force in local direction 1, units:[m, kN]}
\end{center}
\end{figure}
\begin{figure}
\begin{center}
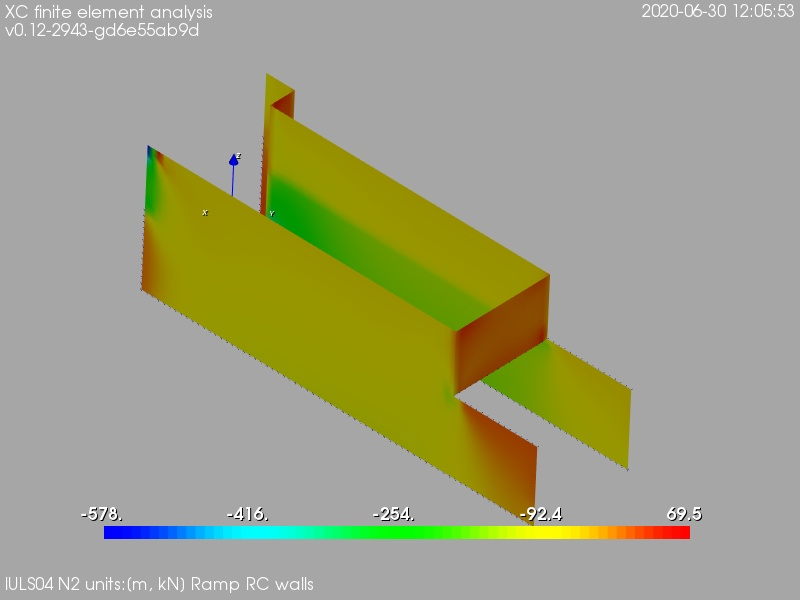
[picture p219: XC_struct/calculation_report/ramp_wall/resLC/text/graphics/resSimplLC/lULS04wallsN2.jpg]

\caption{ULS04. Ramp rc walls, internal axial force in local direction 2, units:[m, kN]}
\end{center}
\end{figure}
\begin{figure}
\begin{center}
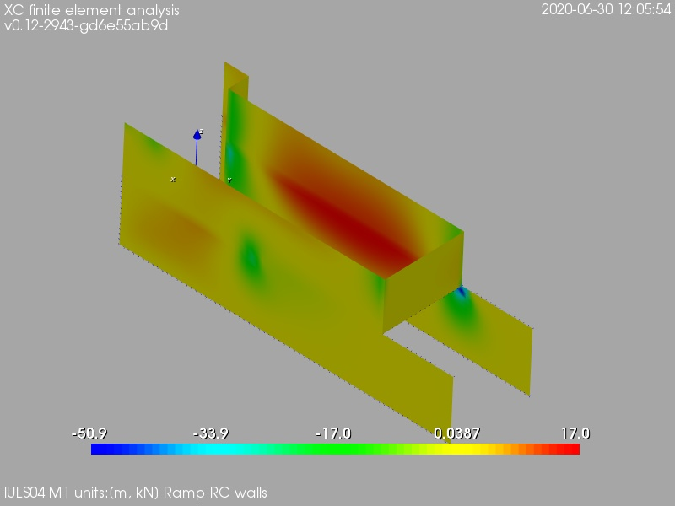
[picture p220: XC_struct/calculation_report/ramp_wall/resLC/text/graphics/resSimplLC/lULS04wallsM1.jpg]

\caption{ULS04. Ramp rc walls, bending moment about local axis 1, units:[m, kN]}
\end{center}
\end{figure}
\begin{figure}
\begin{center}
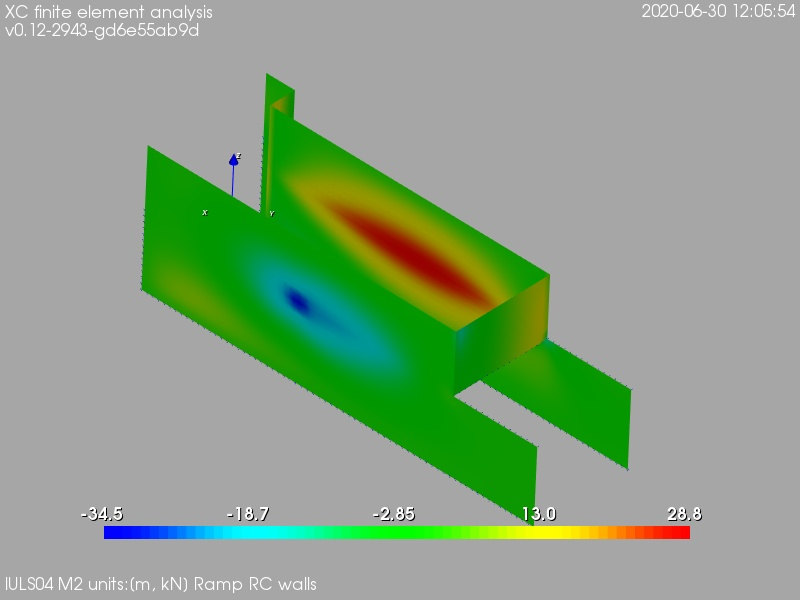
[picture p221: XC_struct/calculation_report/ramp_wall/resLC/text/graphics/resSimplLC/lULS04wallsM2.jpg]

\caption{ULS04. Ramp rc walls, bending moment about local axis 2, units:[m, kN]}
\end{center}
\end{figure}
\begin{figure}
\begin{center}
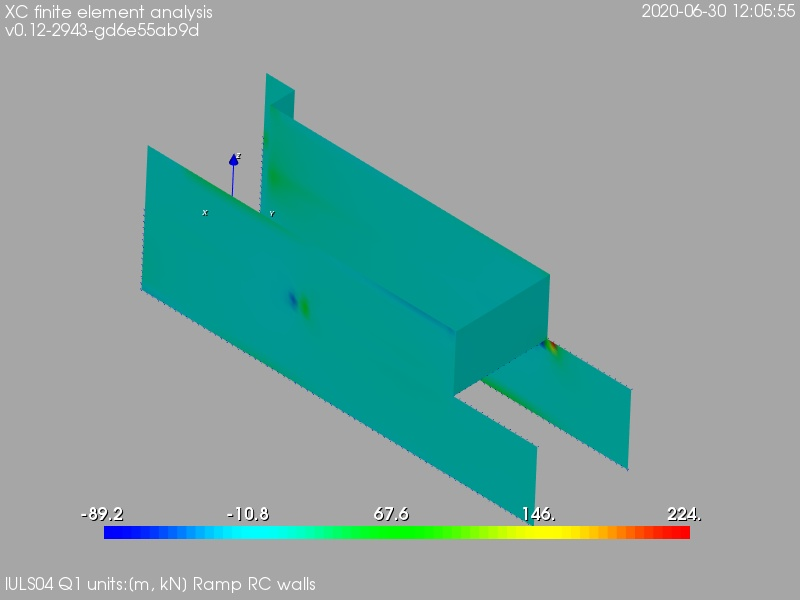
[picture p222: XC_struct/calculation_report/ramp_wall/resLC/text/graphics/resSimplLC/lULS04wallsQ1.jpg]

\caption{ULS04. Ramp rc walls, internal shear force in local direction 1, units:[m, kN]}
\end{center}
\end{figure}
\begin{figure}
\begin{center}
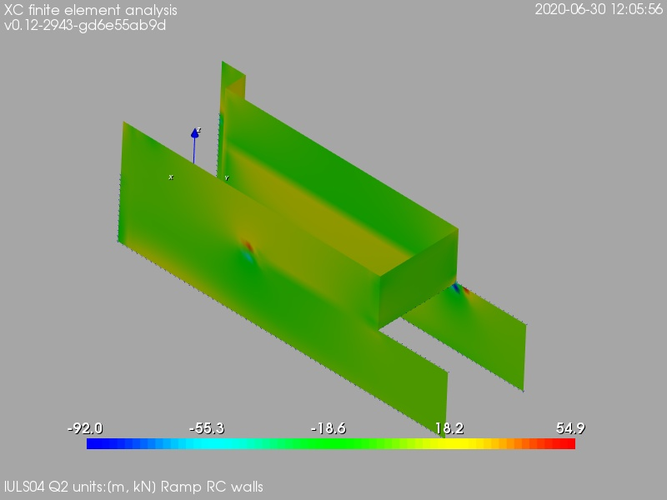
[picture p223: XC_struct/calculation_report/ramp_wall/resLC/text/graphics/resSimplLC/lULS04wallsQ2.jpg]

\caption{ULS04. Ramp rc walls, internal shear force in local direction 2, units:[m, kN]}
\end{center}
\end{figure}
\begin{figure}
\begin{center}
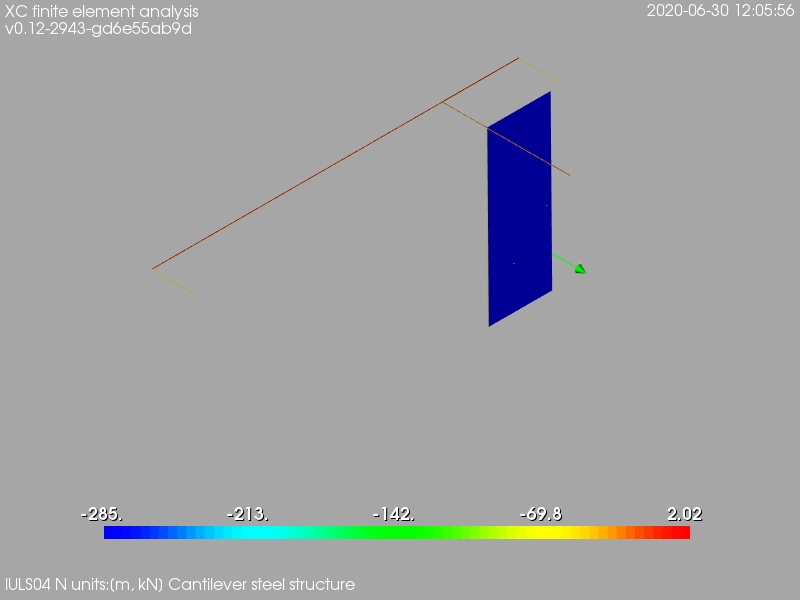
[picture p224: XC_struct/calculation_report/ramp_wall/resLC/text/graphics/resSimplLC/lULS04steelMembersN.jpg]

\caption{ULS04. Cantilever steel structure, internal axial force, units:[m, kN]}
\end{center}
\end{figure}
\begin{figure}
\begin{center}
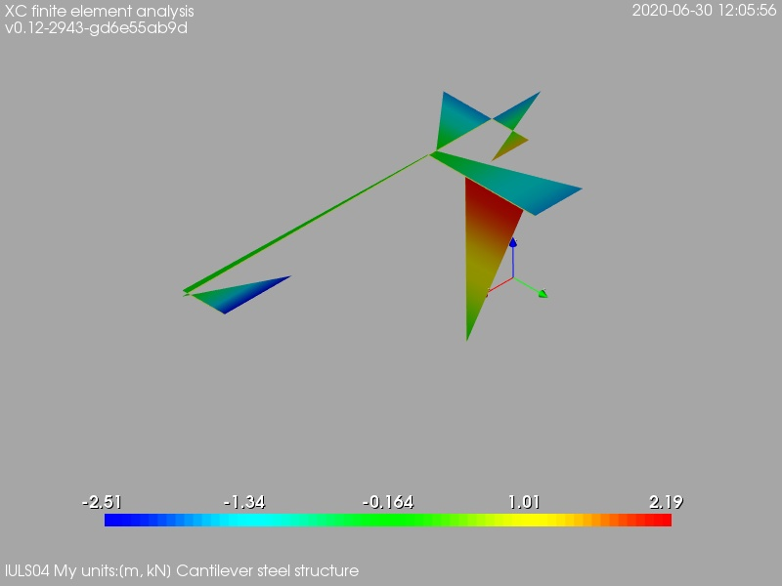
[picture p225: XC_struct/calculation_report/ramp_wall/resLC/text/graphics/resSimplLC/lULS04steelMembersMy.jpg]

\caption{ULS04. Cantilever steel structure, bending moment about local axis y, units:[m, kN]}
\end{center}
\end{figure}
\begin{figure}
\begin{center}
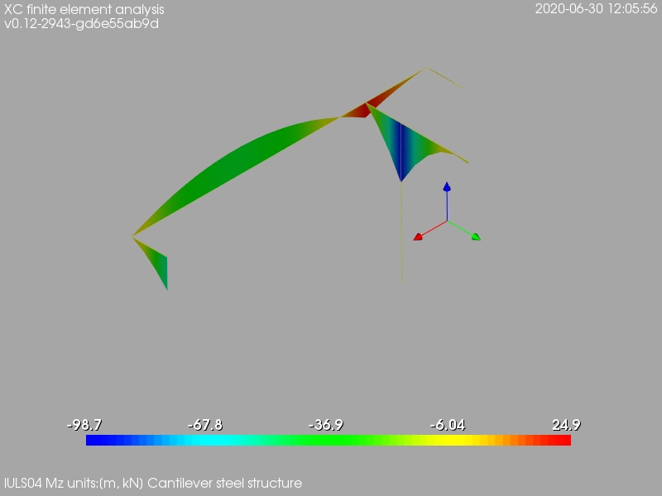
[picture p226: XC_struct/calculation_report/ramp_wall/resLC/text/graphics/resSimplLC/lULS04steelMembersMz.jpg]

\caption{ULS04. Cantilever steel structure, bending moment about local axis z, units:[m, kN]}
\end{center}
\end{figure}
\begin{figure}
\begin{center}
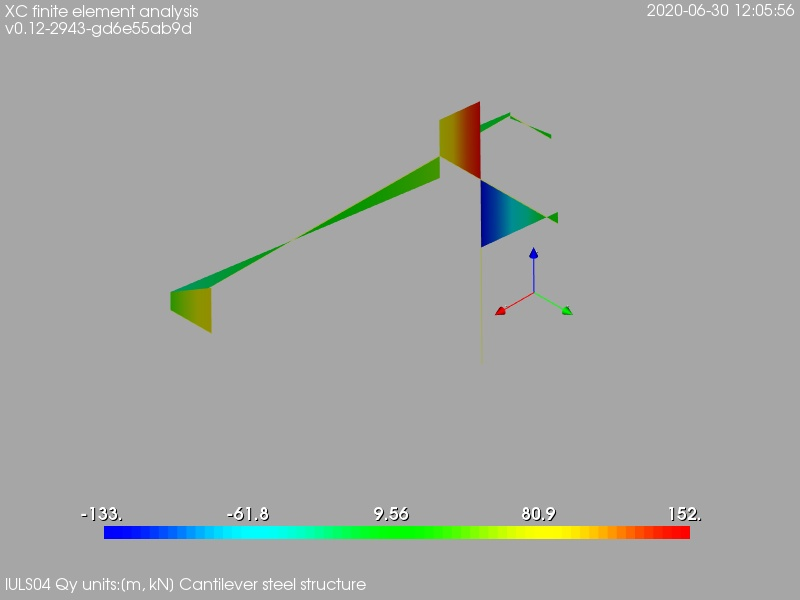
[picture p227: XC_struct/calculation_report/ramp_wall/resLC/text/graphics/resSimplLC/lULS04steelMembersQy.jpg]

\caption{ULS04. Cantilever steel structure, internal shear force in local direction y, units:[m, kN]}
\end{center}
\end{figure}
\begin{figure}
\begin{center}
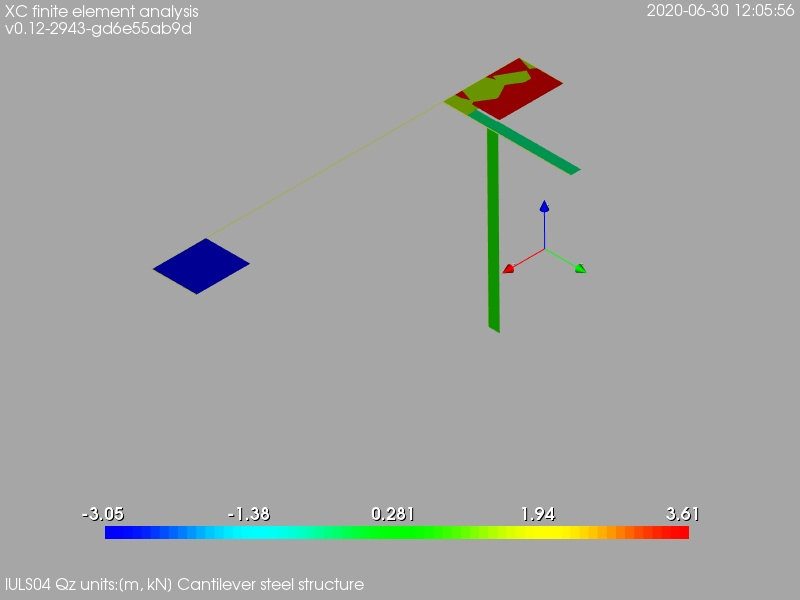
[picture p228: XC_struct/calculation_report/ramp_wall/resLC/text/graphics/resSimplLC/lULS04steelMembersQz.jpg]

\caption{ULS04. Cantilever steel structure, internal shear force in local direction z, units:[m, kN]}
\end{center}
\end{figure}
\clearpage
\begin{figure}
\begin{center}
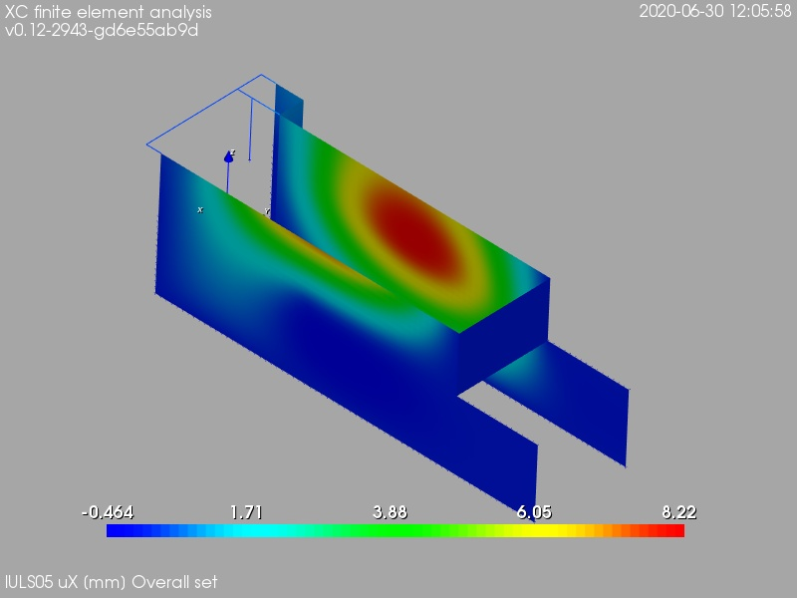
[picture p229: XC_struct/calculation_report/ramp_wall/resLC/text/graphics/resSimplLC/lULS05overallSetuX.jpg]

\caption{ULS05. Overall set, displacement in global X direction, [mm]}
\end{center}
\end{figure}
\begin{figure}
\begin{center}
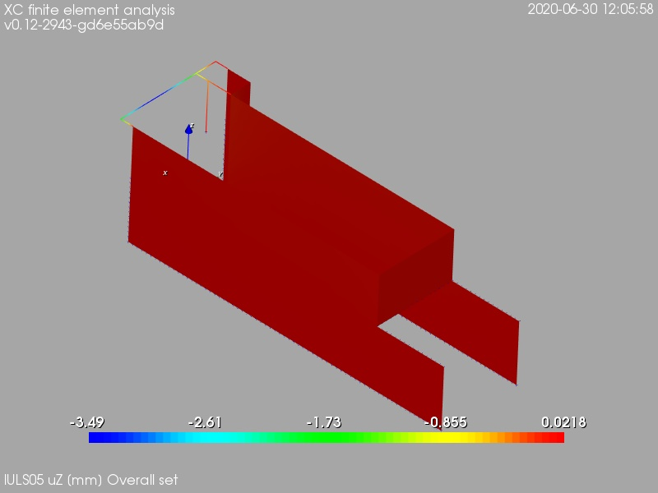
[picture p230: XC_struct/calculation_report/ramp_wall/resLC/text/graphics/resSimplLC/lULS05overallSetuZ.jpg]

\caption{ULS05. Overall set, displacement in global Z direction, [mm]}
\end{center}
\end{figure}
\begin{figure}
\begin{center}
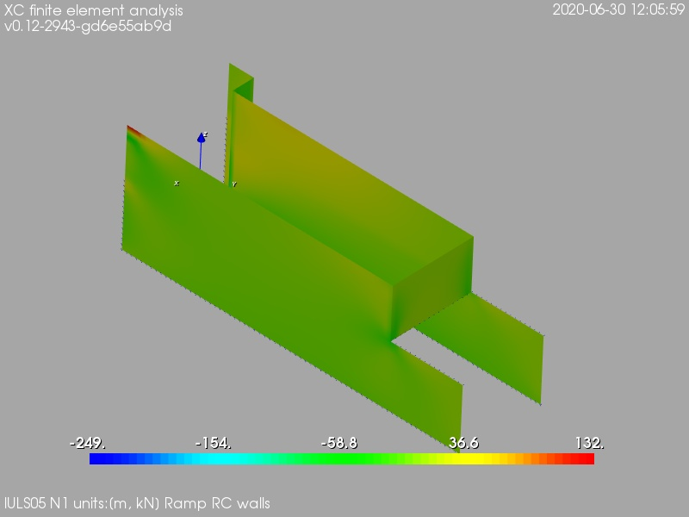
[picture p231: XC_struct/calculation_report/ramp_wall/resLC/text/graphics/resSimplLC/lULS05wallsN1.jpg]

\caption{ULS05. Ramp rc walls, internal axial force in local direction 1, units:[m, kN]}
\end{center}
\end{figure}
\begin{figure}
\begin{center}
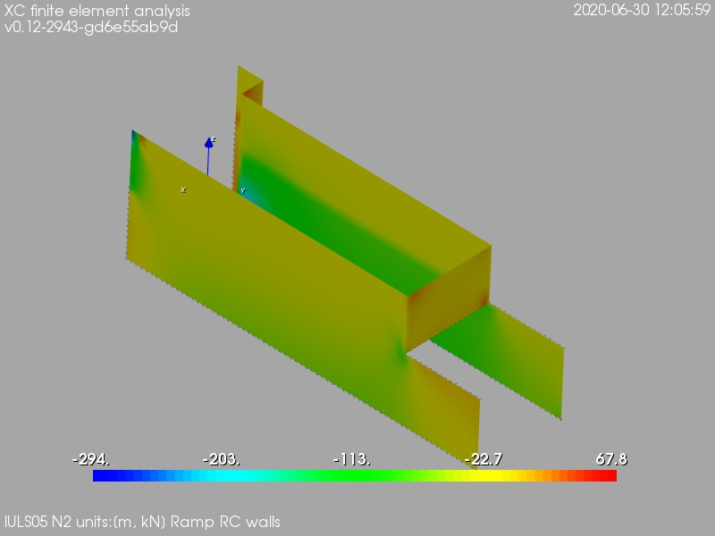
[picture p232: XC_struct/calculation_report/ramp_wall/resLC/text/graphics/resSimplLC/lULS05wallsN2.jpg]

\caption{ULS05. Ramp rc walls, internal axial force in local direction 2, units:[m, kN]}
\end{center}
\end{figure}
\begin{figure}
\begin{center}
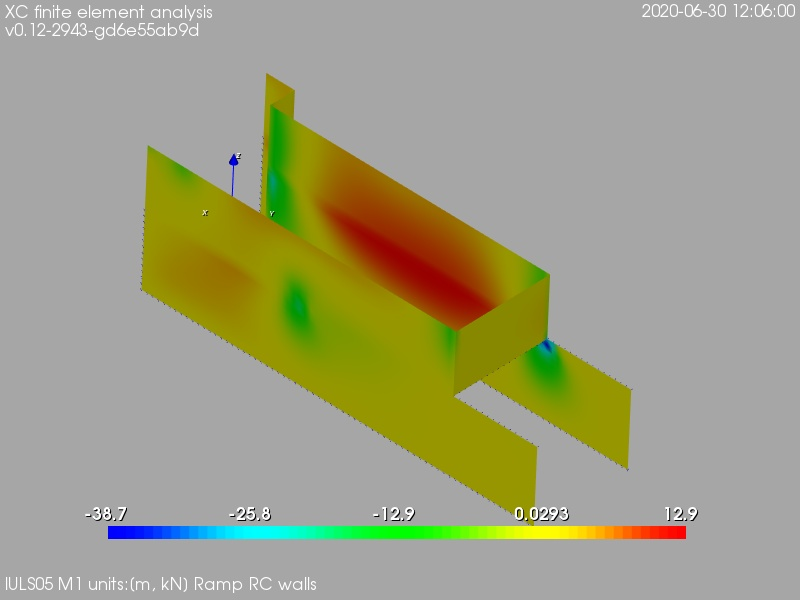
[picture p233: XC_struct/calculation_report/ramp_wall/resLC/text/graphics/resSimplLC/lULS05wallsM1.jpg]

\caption{ULS05. Ramp rc walls, bending moment about local axis 1, units:[m, kN]}
\end{center}
\end{figure}
\begin{figure}
\begin{center}
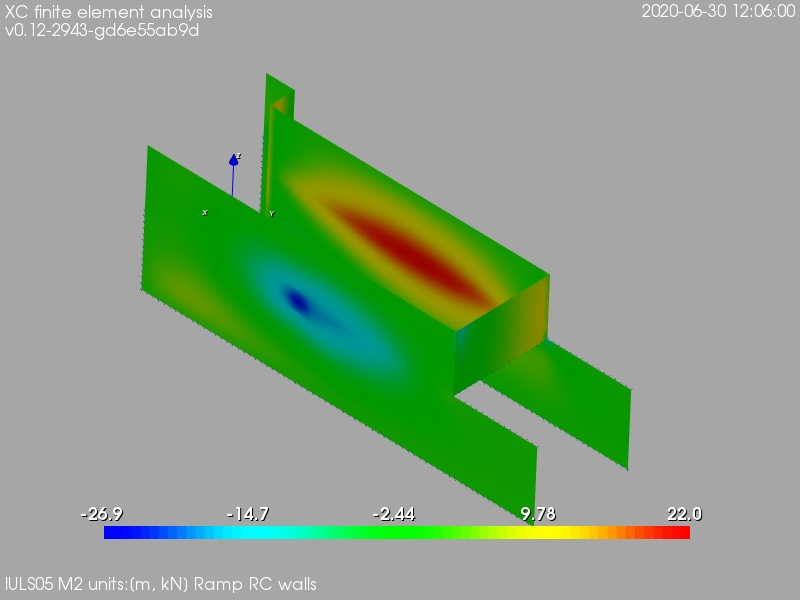
[picture p234: XC_struct/calculation_report/ramp_wall/resLC/text/graphics/resSimplLC/lULS05wallsM2.jpg]

\caption{ULS05. Ramp rc walls, bending moment about local axis 2, units:[m, kN]}
\end{center}
\end{figure}
\begin{figure}
\begin{center}
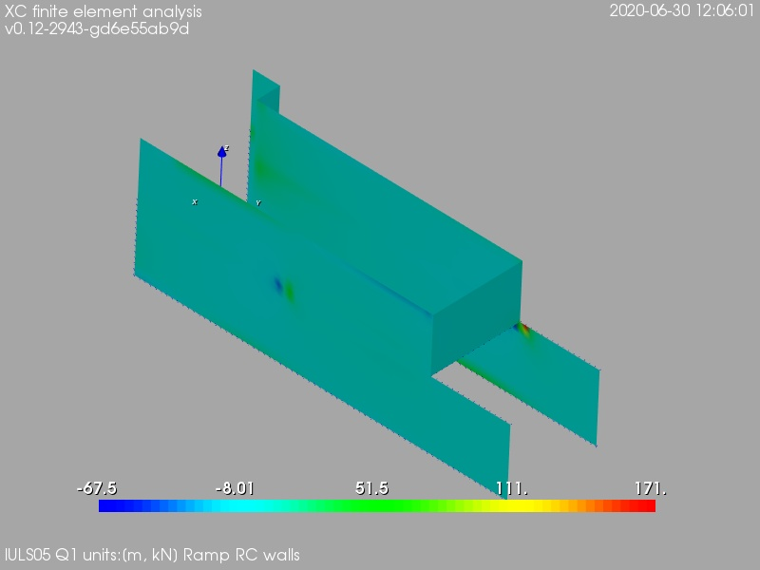
[picture p235: XC_struct/calculation_report/ramp_wall/resLC/text/graphics/resSimplLC/lULS05wallsQ1.jpg]

\caption{ULS05. Ramp rc walls, internal shear force in local direction 1, units:[m, kN]}
\end{center}
\end{figure}
\begin{figure}
\begin{center}
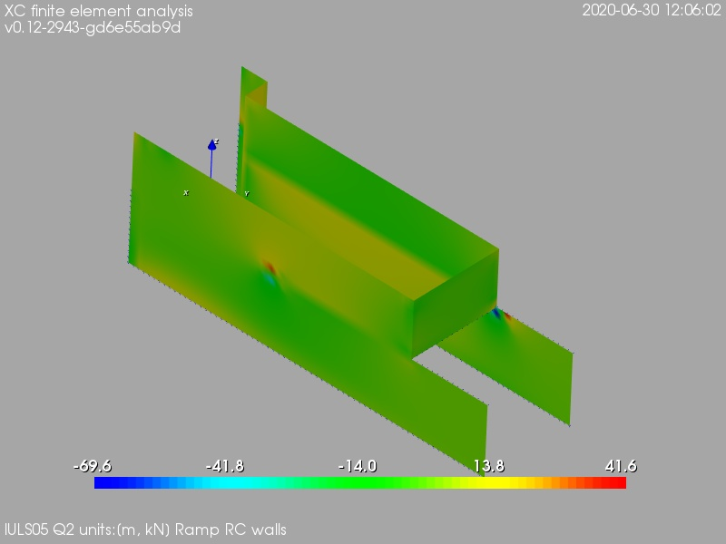
[picture p236: XC_struct/calculation_report/ramp_wall/resLC/text/graphics/resSimplLC/lULS05wallsQ2.jpg]

\caption{ULS05. Ramp rc walls, internal shear force in local direction 2, units:[m, kN]}
\end{center}
\end{figure}
\begin{figure}
\begin{center}
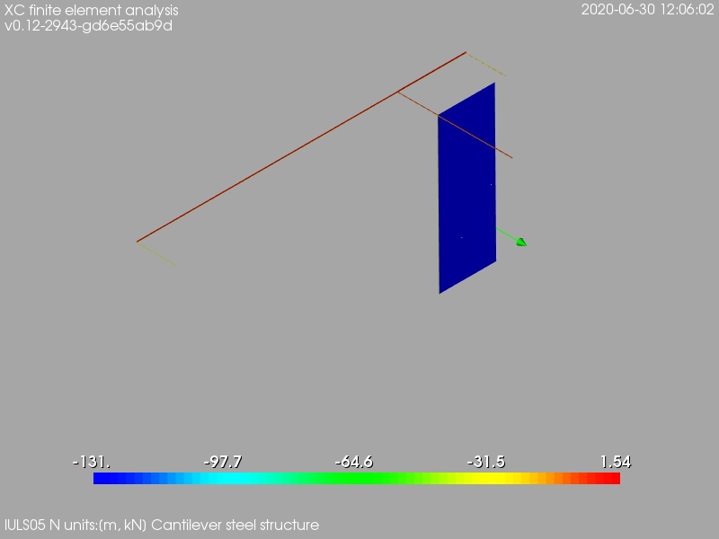
[picture p237: XC_struct/calculation_report/ramp_wall/resLC/text/graphics/resSimplLC/lULS05steelMembersN.jpg]

\caption{ULS05. Cantilever steel structure, internal axial force, units:[m, kN]}
\end{center}
\end{figure}
\begin{figure}
\begin{center}
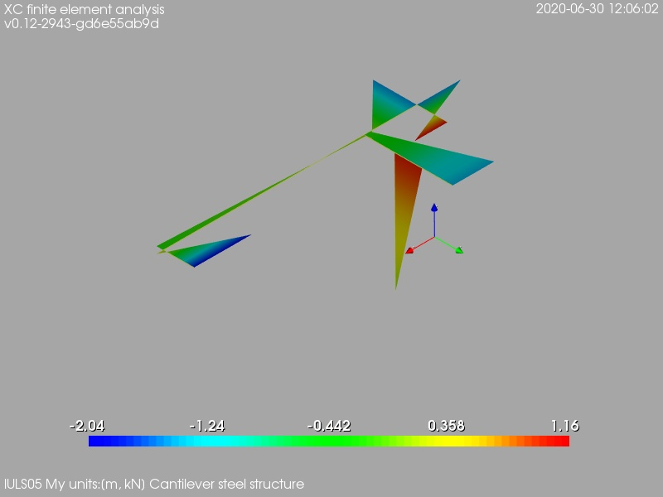
[picture p238: XC_struct/calculation_report/ramp_wall/resLC/text/graphics/resSimplLC/lULS05steelMembersMy.jpg]

\caption{ULS05. Cantilever steel structure, bending moment about local axis y, units:[m, kN]}
\end{center}
\end{figure}
\begin{figure}
\begin{center}
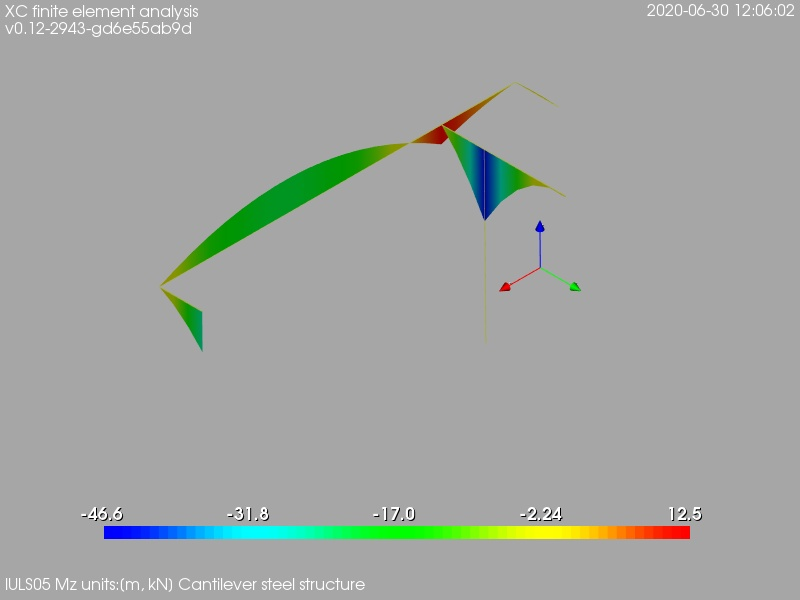
[picture p239: XC_struct/calculation_report/ramp_wall/resLC/text/graphics/resSimplLC/lULS05steelMembersMz.jpg]

\caption{ULS05. Cantilever steel structure, bending moment about local axis z, units:[m, kN]}
\end{center}
\end{figure}
\begin{figure}
\begin{center}
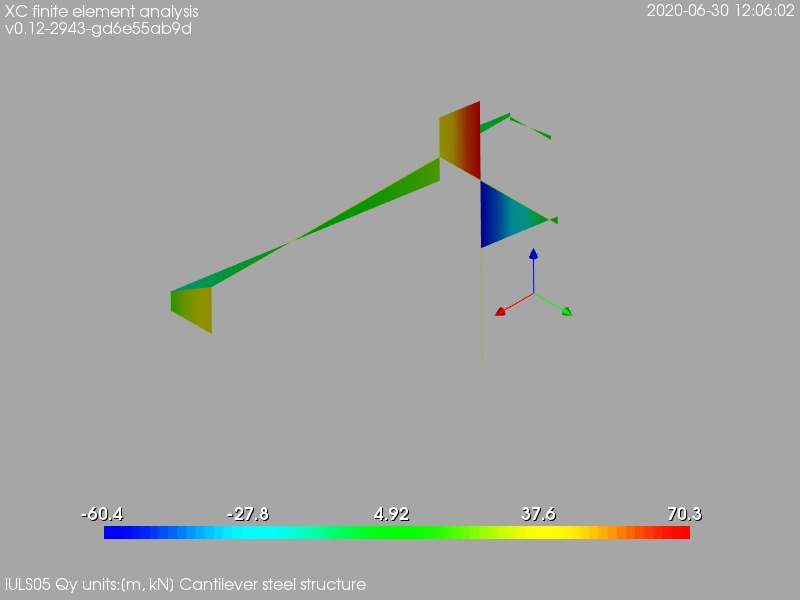
[picture p240: XC_struct/calculation_report/ramp_wall/resLC/text/graphics/resSimplLC/lULS05steelMembersQy.jpg]

\caption{ULS05. Cantilever steel structure, internal shear force in local direction y, units:[m, kN]}
\end{center}
\end{figure}
\begin{figure}
\begin{center}
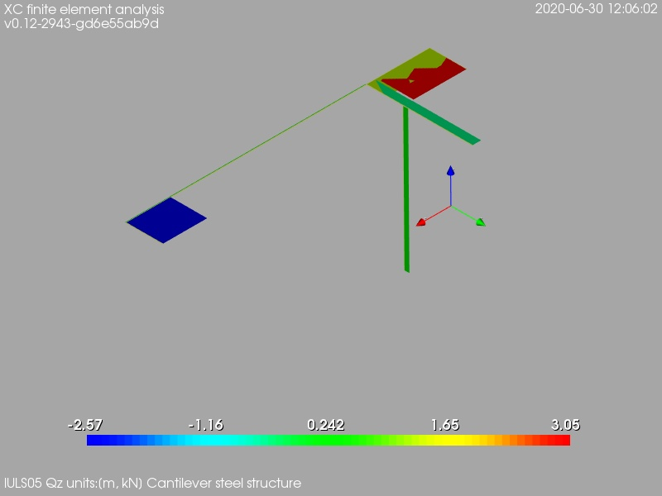
[picture p241: XC_struct/calculation_report/ramp_wall/resLC/text/graphics/resSimplLC/lULS05steelMembersQz.jpg]

\caption{ULS05. Cantilever steel structure, internal shear force in local direction z, units:[m, kN]}
\end{center}
\end{figure}
\clearpage
