OpeningDesign/CTR/XC_struct/calculation_report/ramp_wall/resLC/text/report_shearULS.tex

\begin{figure}
\begin{center}

\caption{ULS shear check. Ramp rc walls, efficiency, section 1}
\end{center}
\end{figure}
\begin{figure}
\begin{center}

\caption{ULS shear check. Ramp rc walls, efficiency, section 2}
\end{center}
\end{figure}
\begin{figure}
\begin{center}

\caption{ULS shear check. Ramp rc walls, internal axial force, section 1}
\end{center}
\end{figure}
\begin{figure}
\begin{center}

\caption{ULS shear check. Ramp rc walls, internal axial force, section 2}
\end{center}
\end{figure}
\begin{figure}
\begin{center}

\caption{ULS shear check. Ramp rc walls, bending moment about local axis y, section 1}
\end{center}
\end{figure}
\begin{figure}
\begin{center}

\caption{ULS shear check. Ramp rc walls, bending moment about local axis y, section 2}
\end{center}
\end{figure}
\begin{figure}
\begin{center}
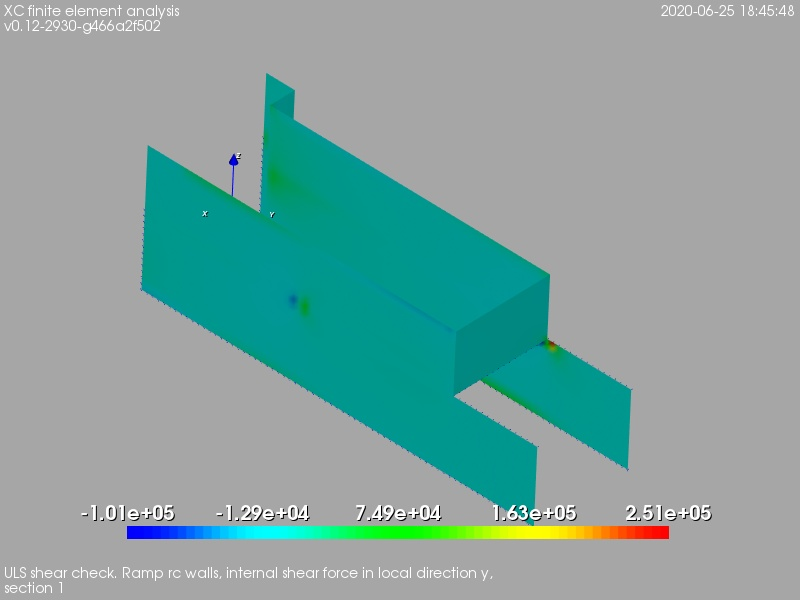
[picture p242: XC_struct/calculation_report/ramp_wall/resLC/text/graphics/shearULS/wallsVySect1.jpg]

\caption{ULS shear check. Ramp rc walls, internal shear force in local direction y, section 1}
\end{center}
\end{figure}
\begin{figure}
\begin{center}
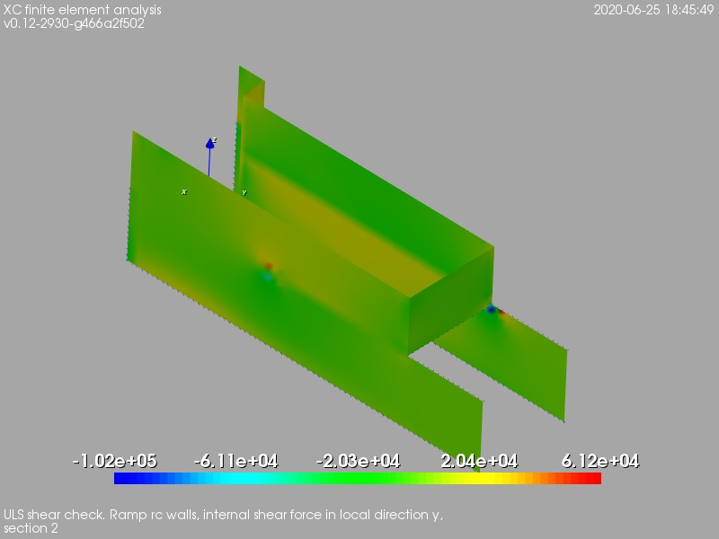
[picture p243: XC_struct/calculation_report/ramp_wall/resLC/text/graphics/shearULS/wallsVySect2.jpg]

\caption{ULS shear check. Ramp rc walls, internal shear force in local direction y, section 2}
\end{center}
\end{figure}
\begin{figure}
\begin{center}
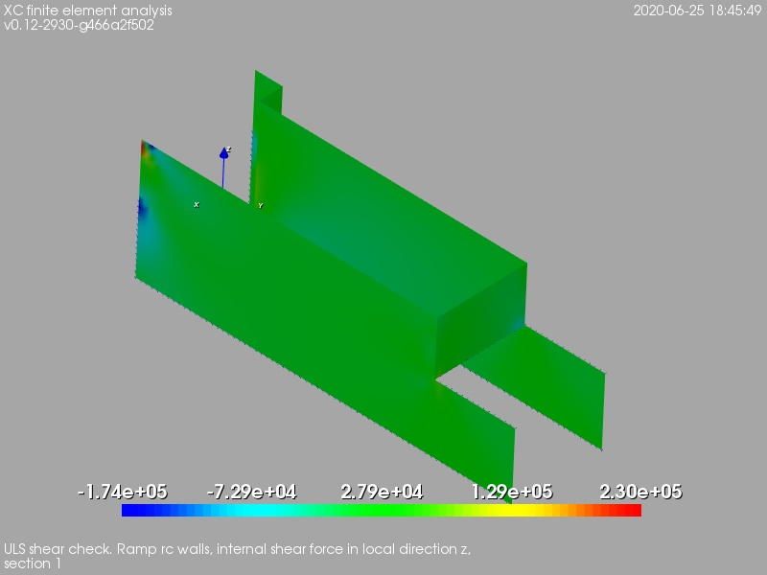
[picture p244: XC_struct/calculation_report/ramp_wall/resLC/text/graphics/shearULS/wallsVzSect1.jpg]

\caption{ULS shear check. Ramp rc walls, internal shear force in local direction z, section 1}
\end{center}
\end{figure}
\begin{figure}
\begin{center}
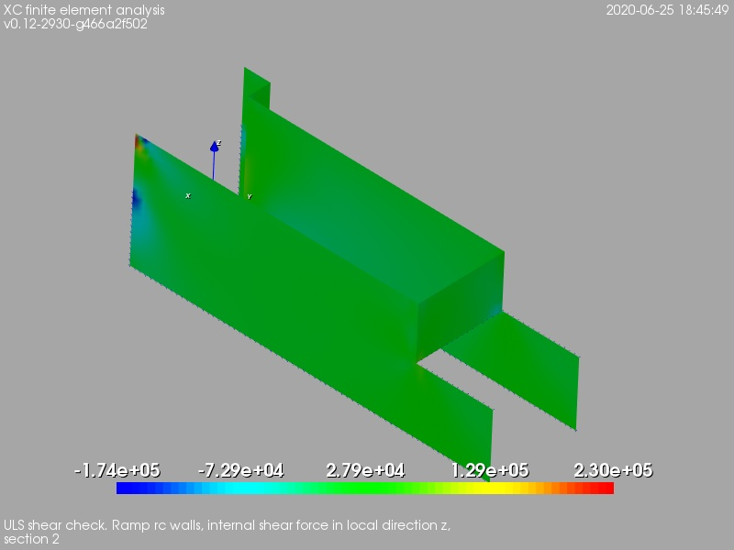
[picture p245: XC_struct/calculation_report/ramp_wall/resLC/text/graphics/shearULS/wallsVzSect2.jpg]

\caption{ULS shear check. Ramp rc walls, internal shear force in local direction z, section 2}
\end{center}
\end{figure}
