OpeningDesign/CTR/Most Current Set/Full size sheets/CTR - ARCH & STRUCT Drawings.md

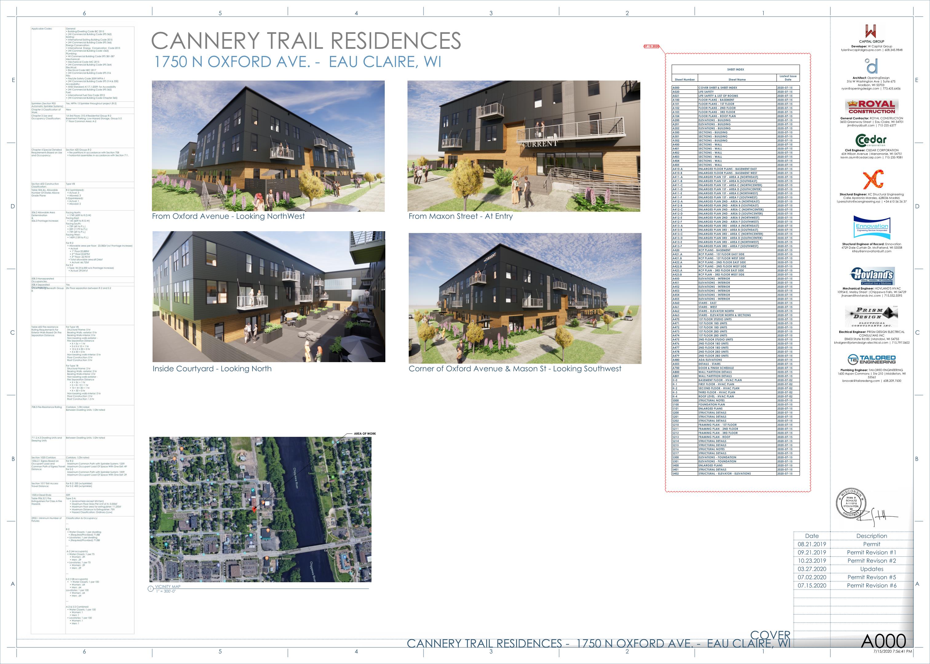
[picture p246: Most Current Set/Full size sheets/jpgs/001.jpg]

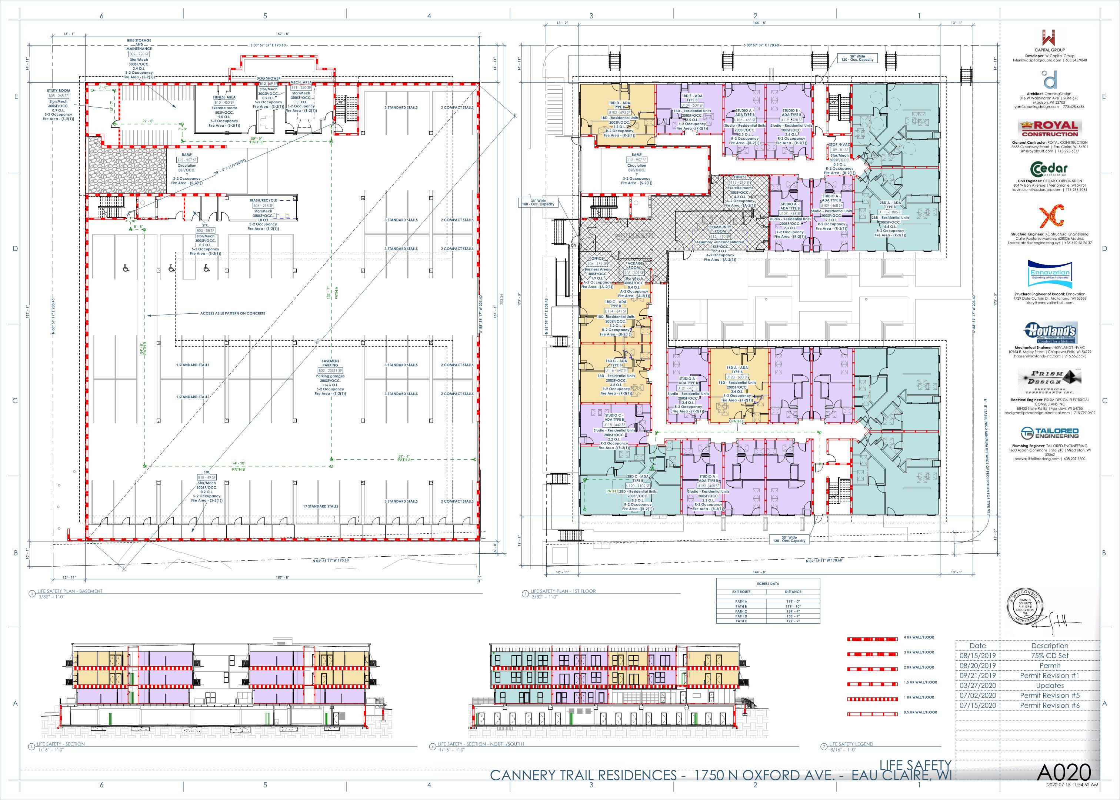
[picture p247: Most Current Set/Full size sheets/jpgs/002.jpg]

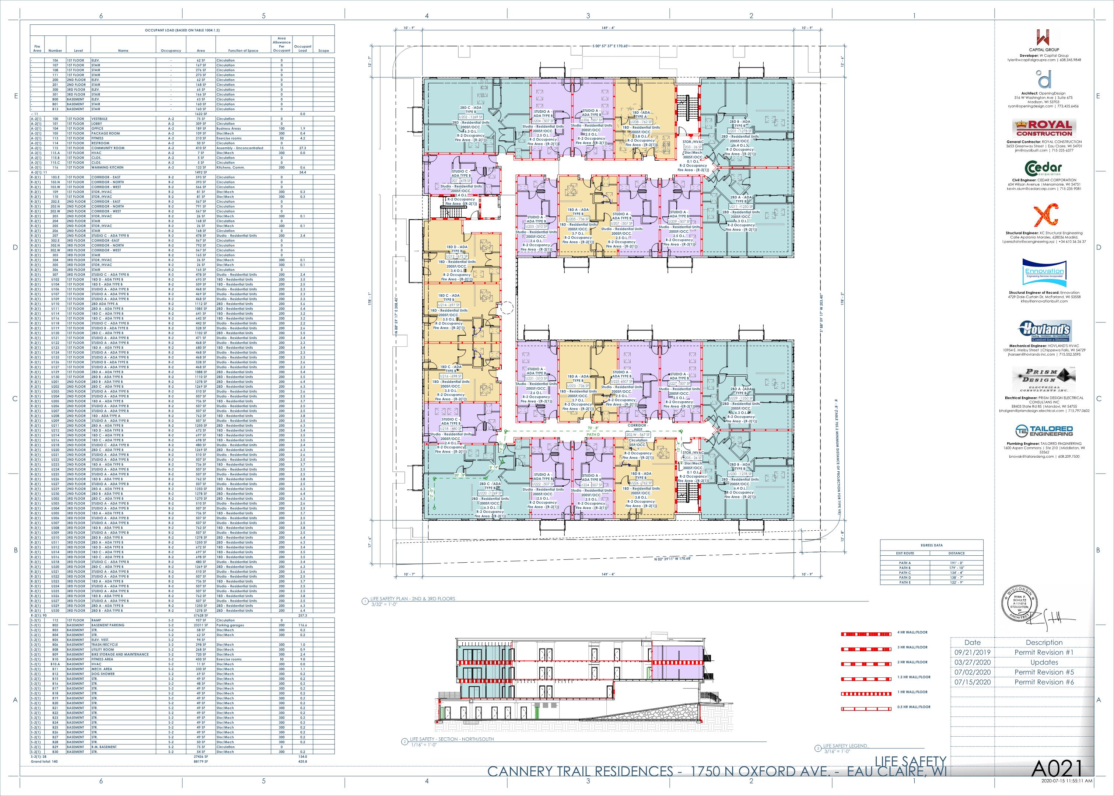
[picture p248: Most Current Set/Full size sheets/jpgs/003.jpg]

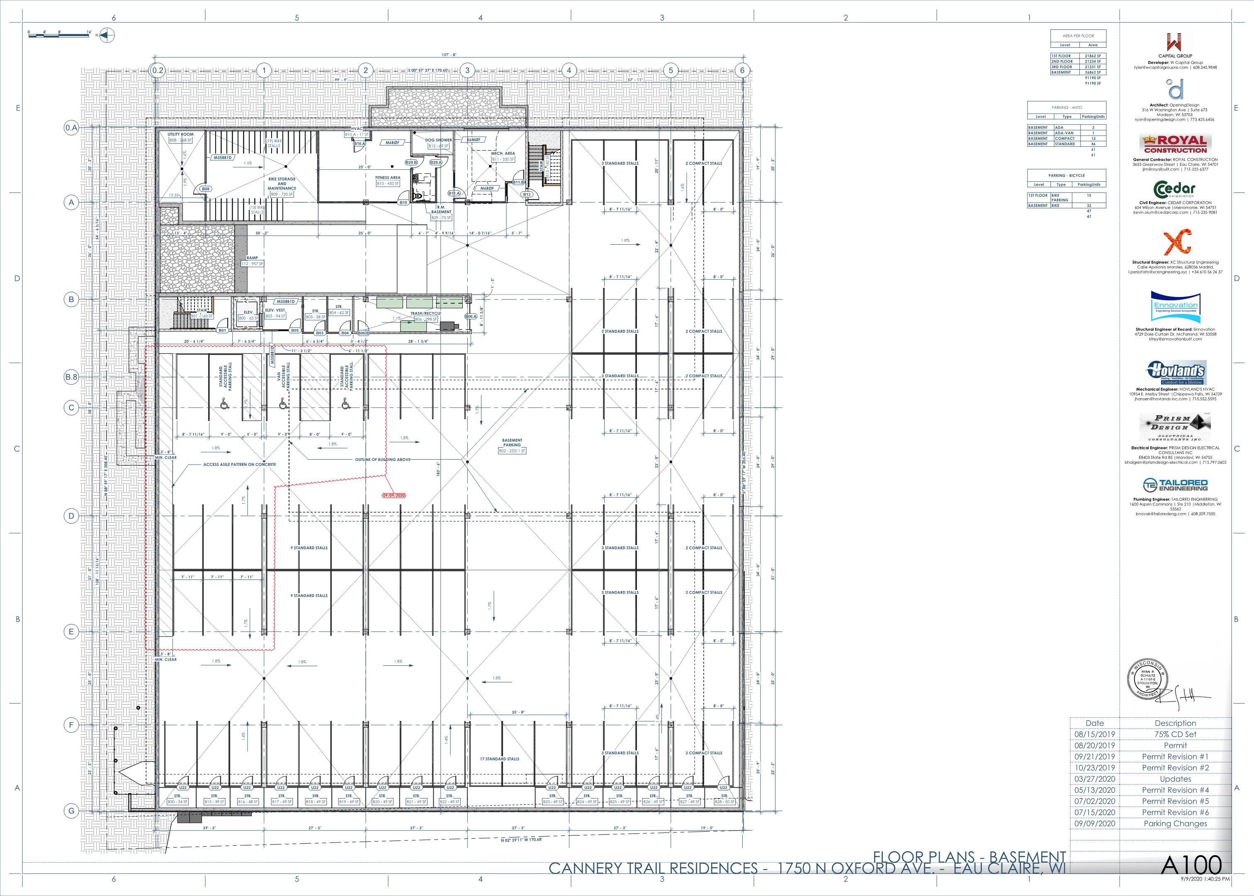
[picture p249: Most Current Set/Full size sheets/jpgs/004.jpg]

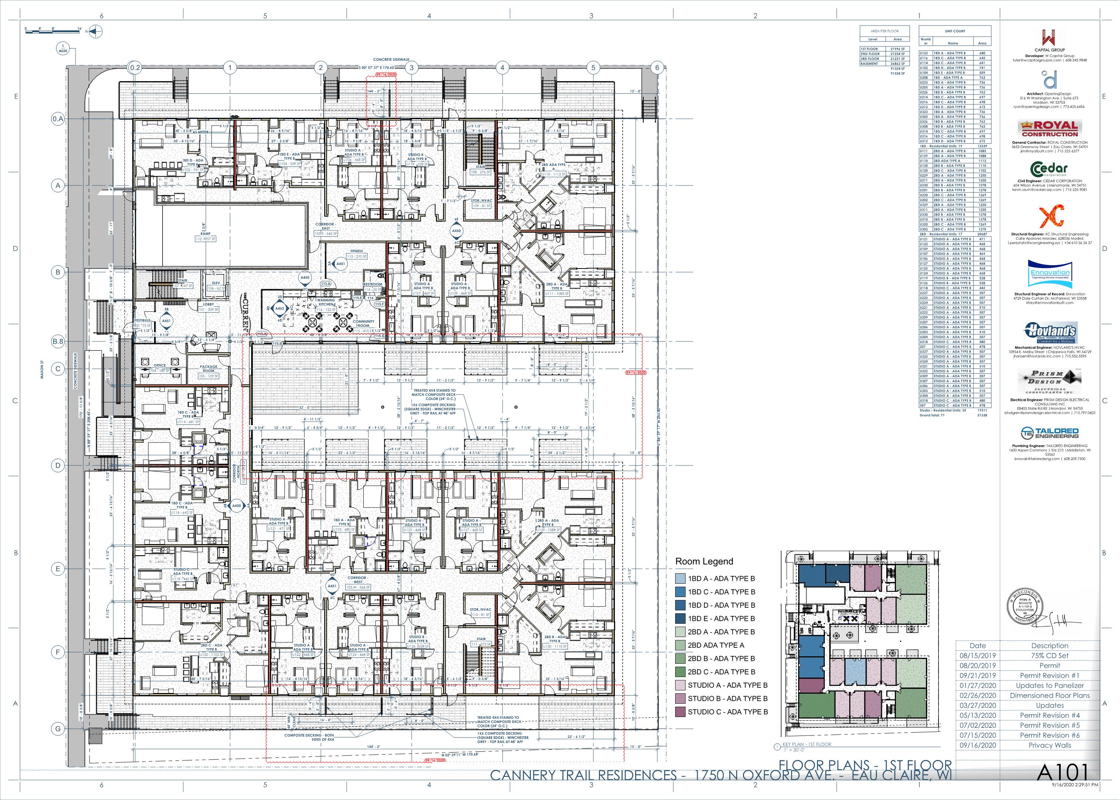
[picture p250: Most Current Set/Full size sheets/jpgs/005.jpg]

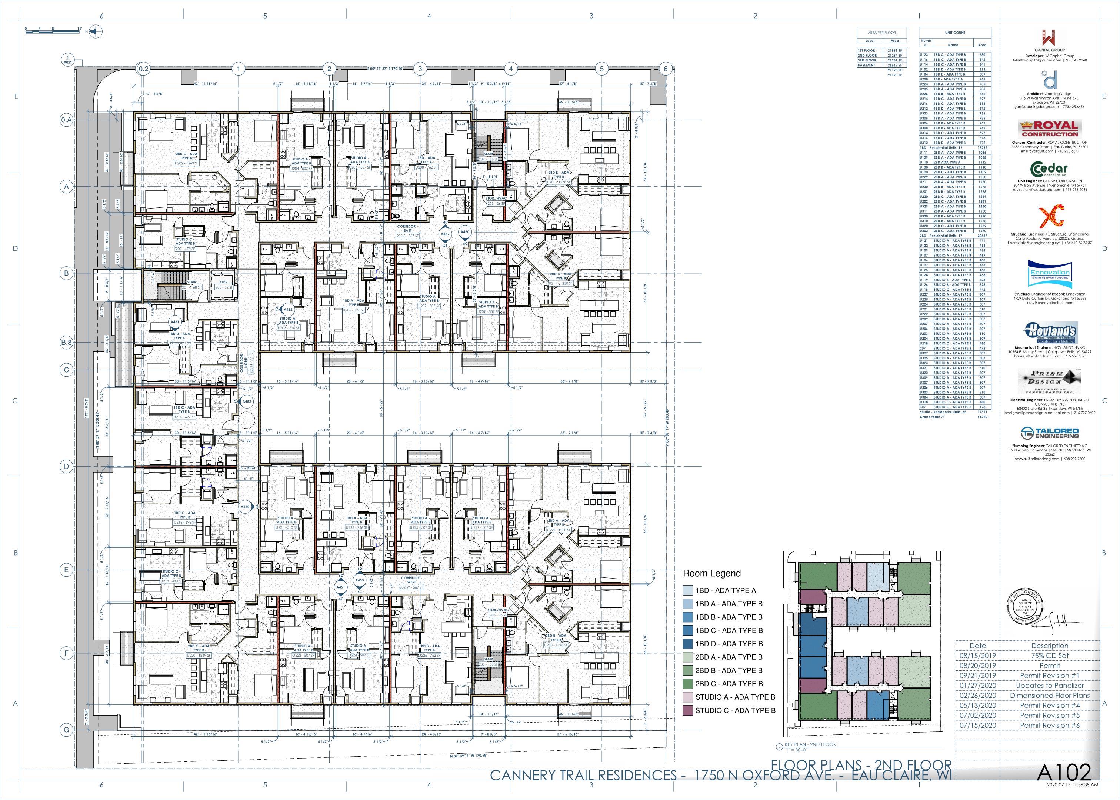
[picture p251: Most Current Set/Full size sheets/jpgs/006.jpg]

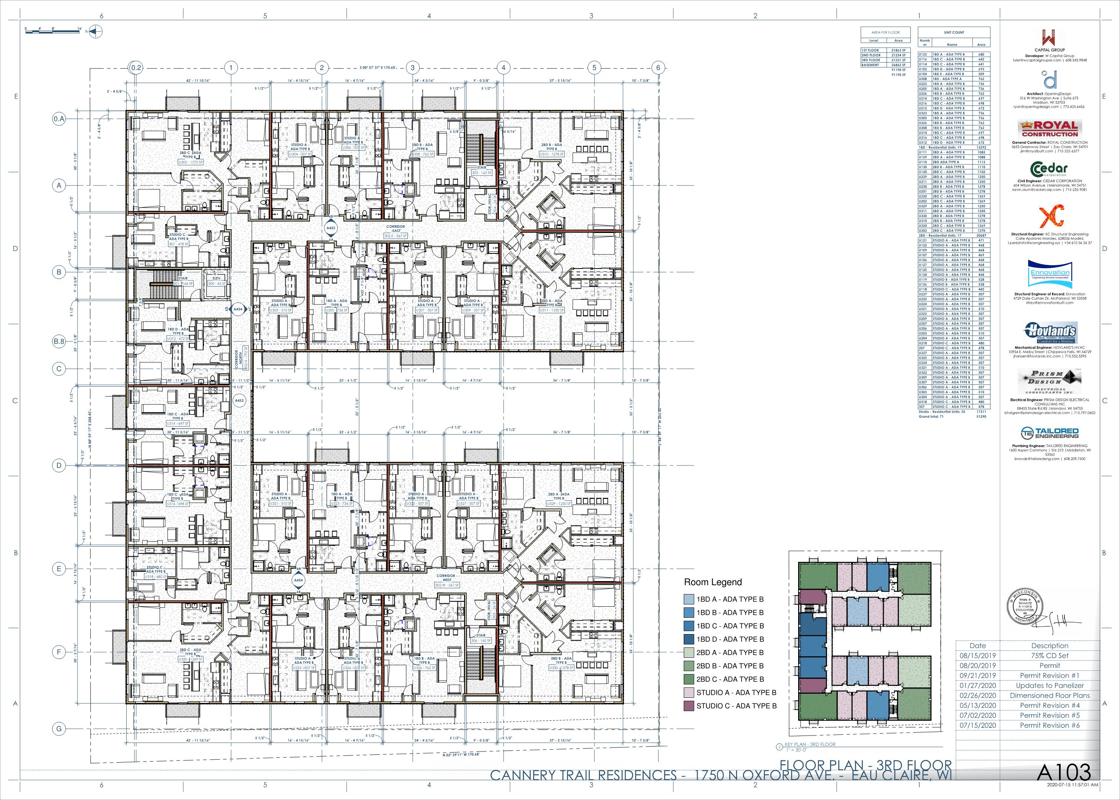
[picture p252: Most Current Set/Full size sheets/jpgs/007.jpg]

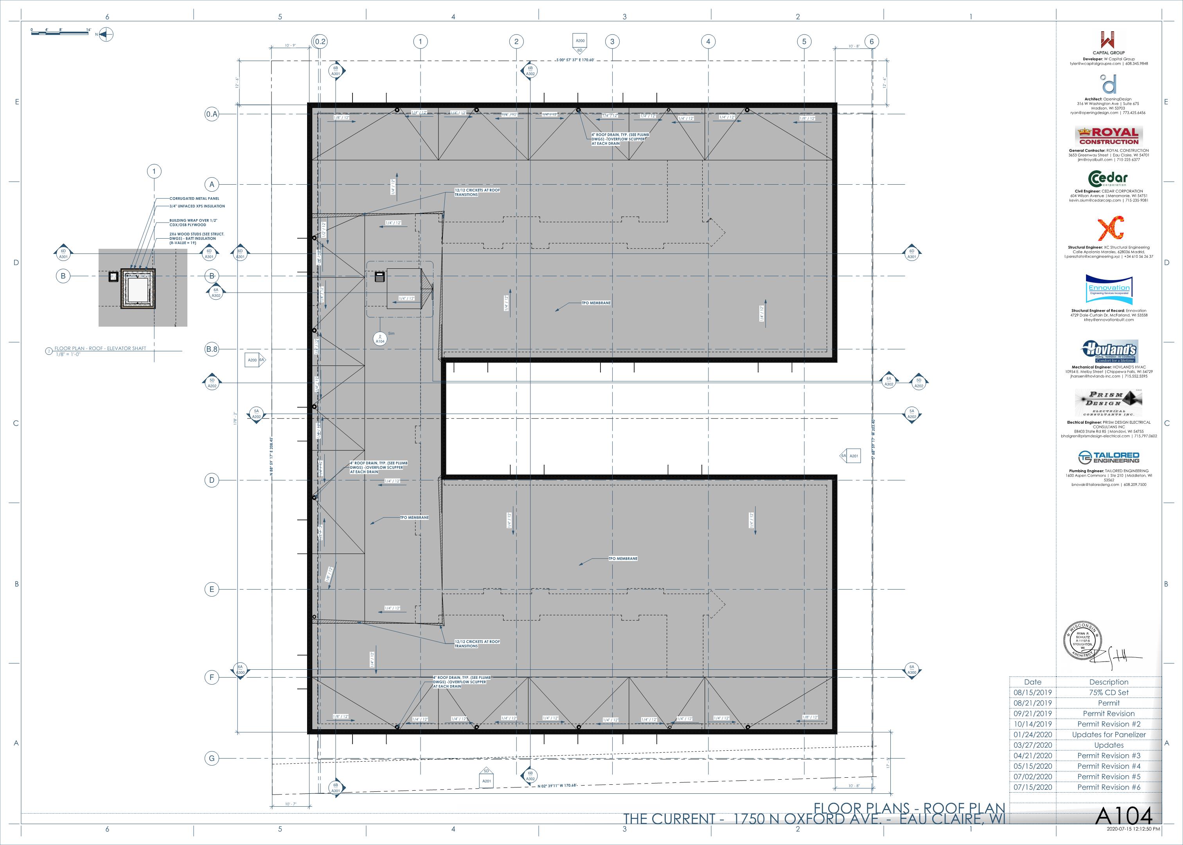
[picture p253: Most Current Set/Full size sheets/jpgs/008.jpg]

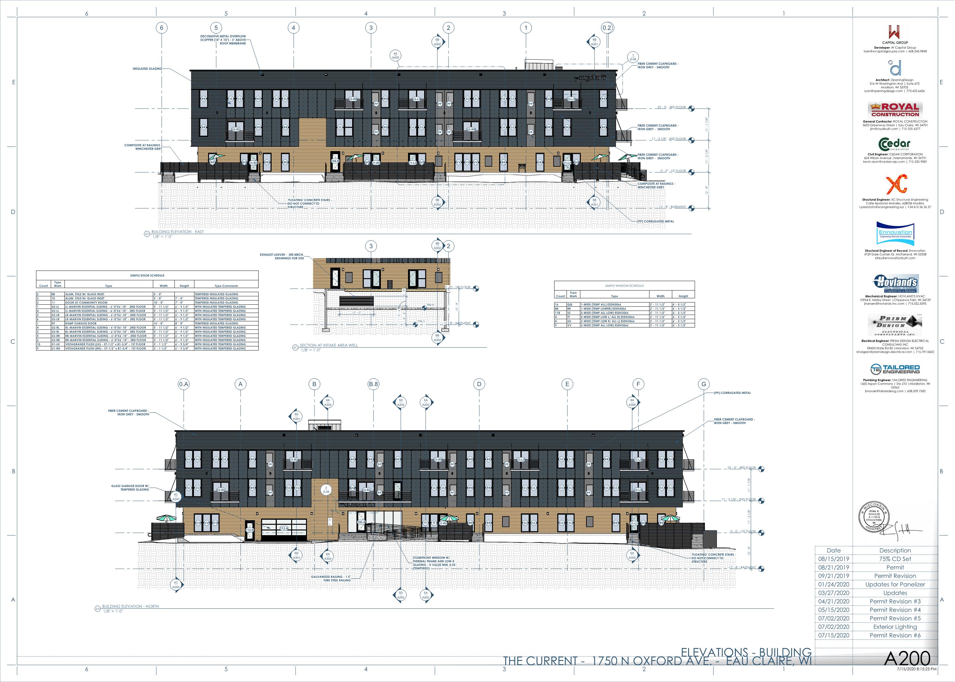
[picture p254: Most Current Set/Full size sheets/jpgs/009.jpg]

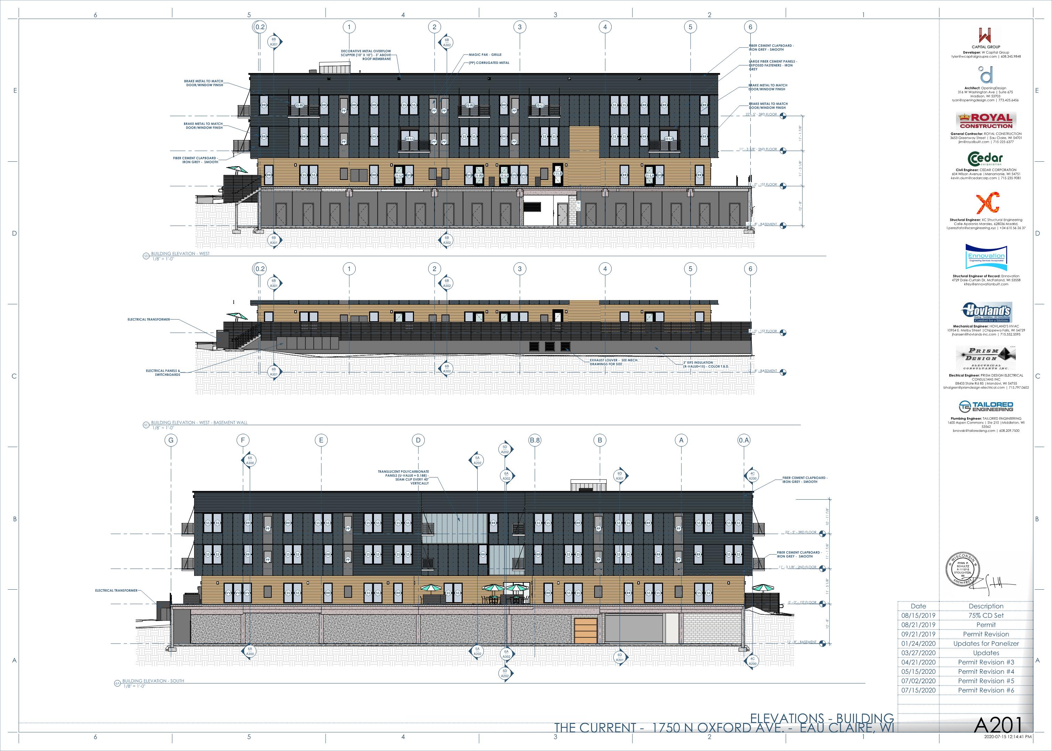
[picture p255: Most Current Set/Full size sheets/jpgs/010.jpg]

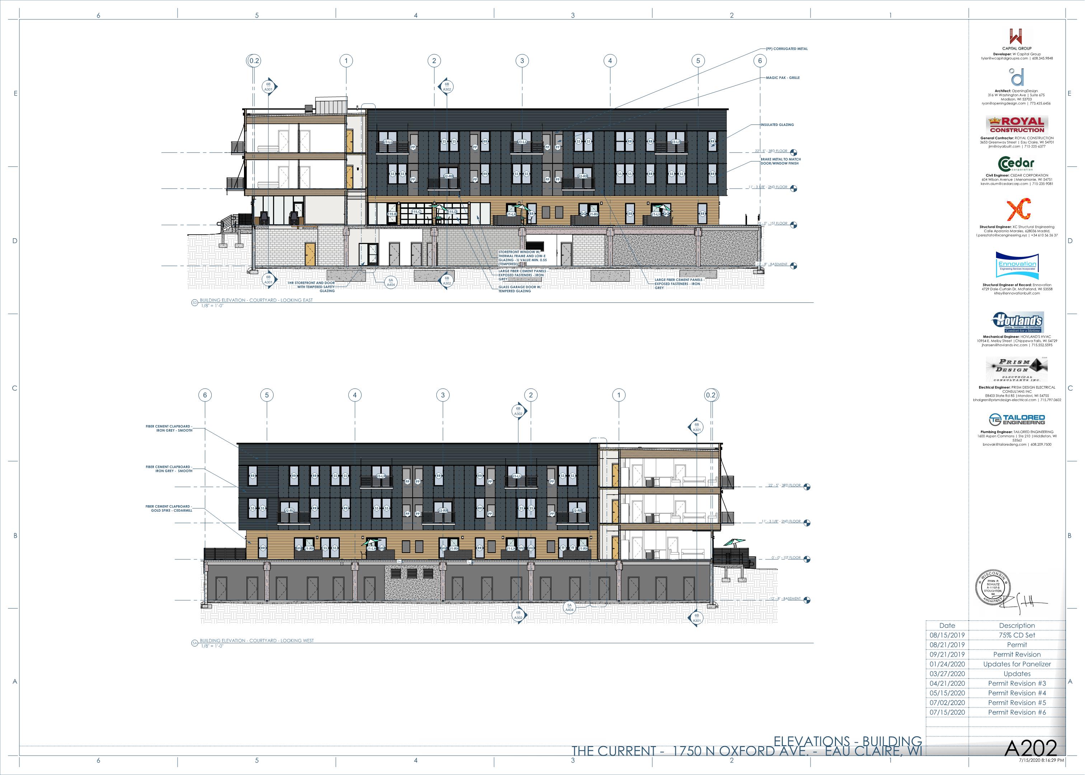
[picture p256: Most Current Set/Full size sheets/jpgs/011.jpg]

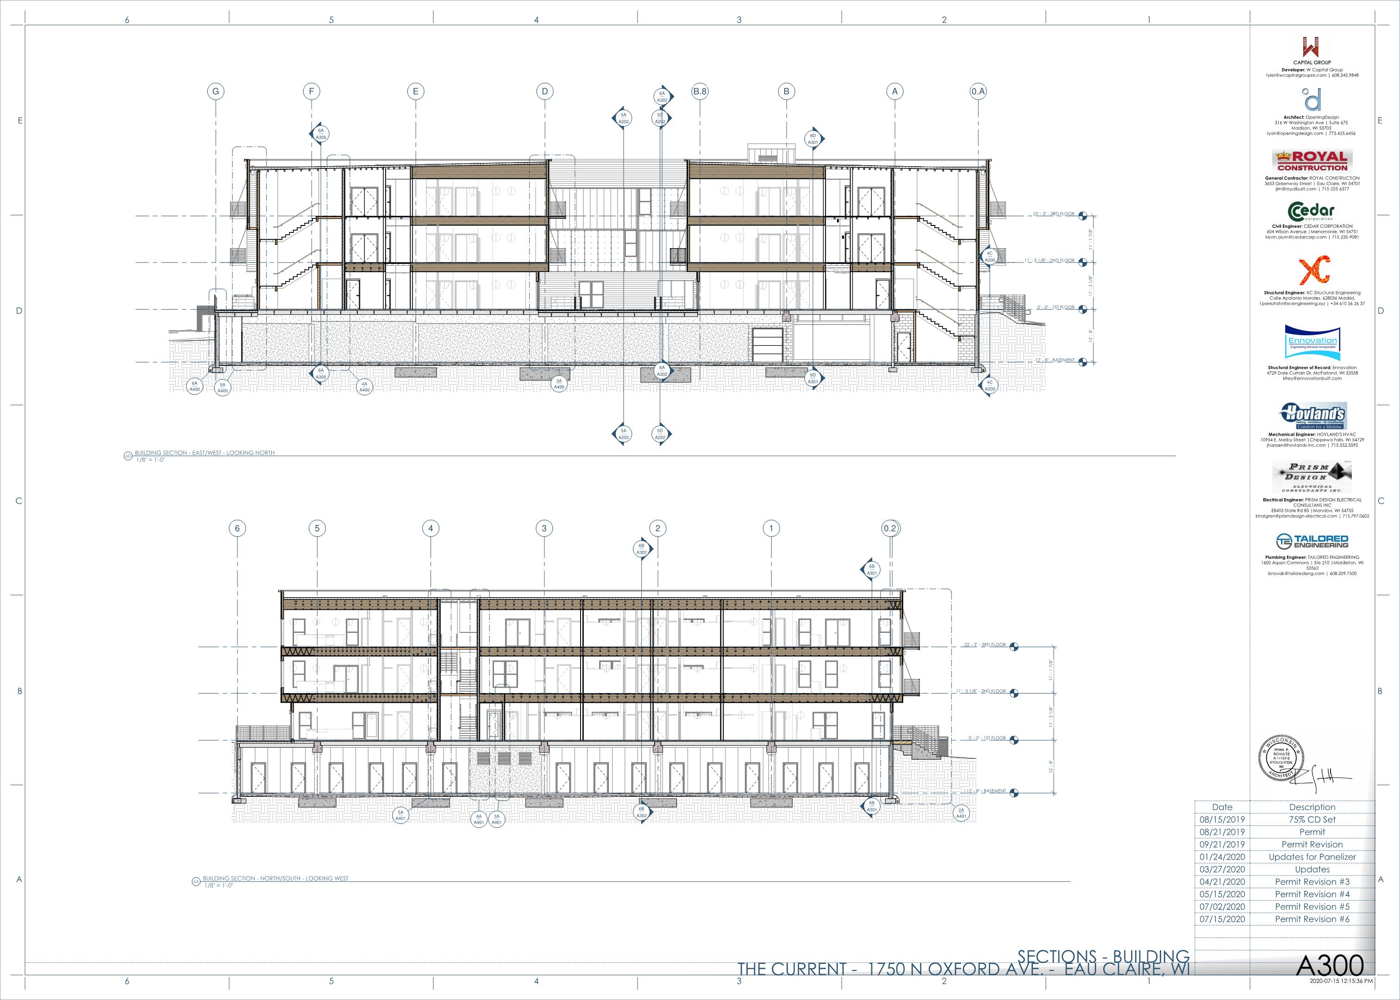
[picture p257: Most Current Set/Full size sheets/jpgs/012.jpg]

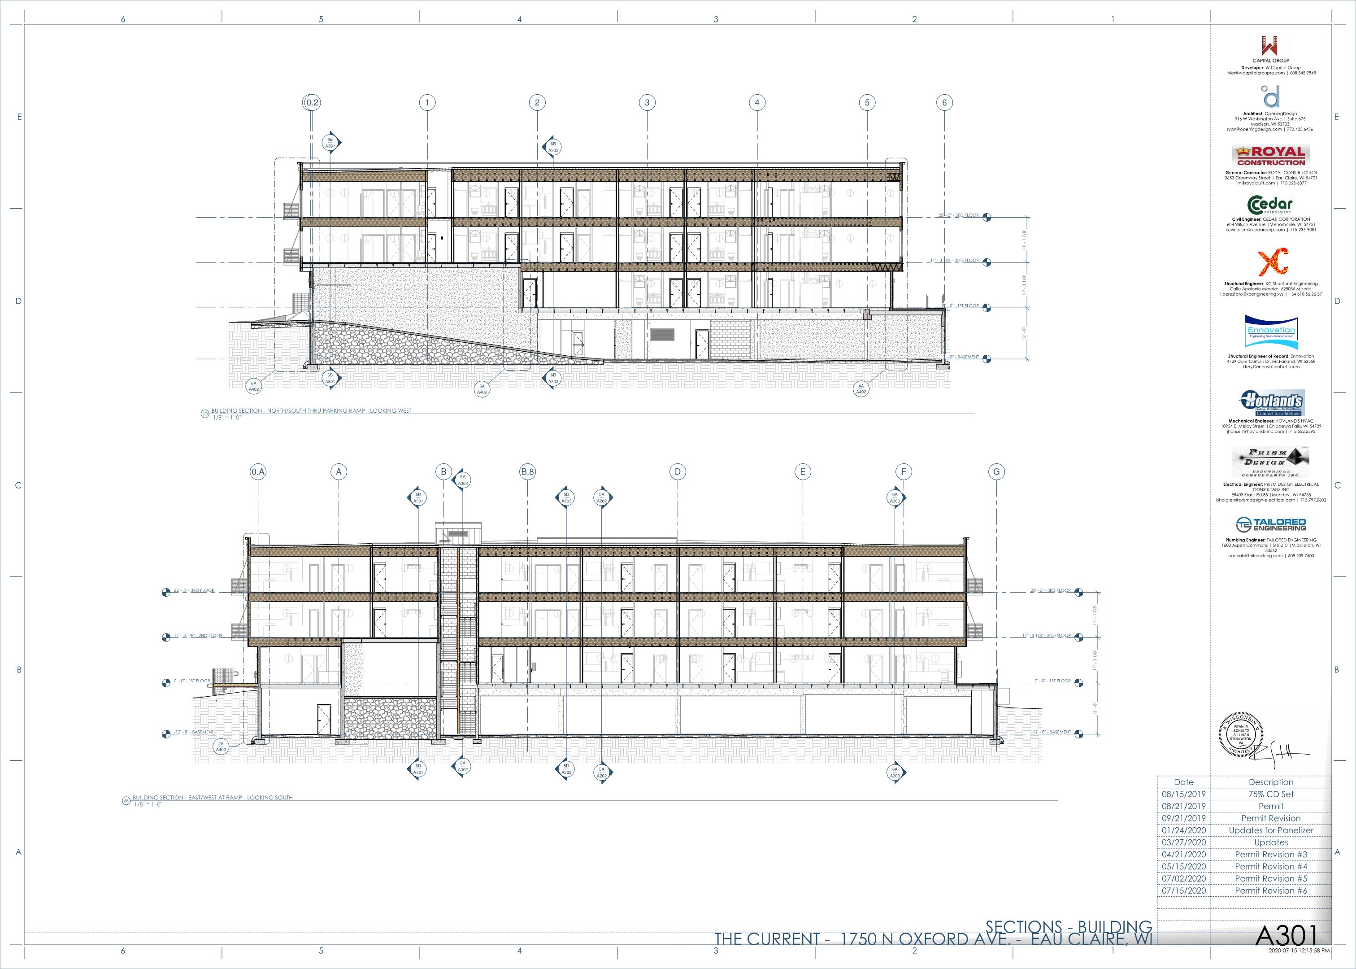
[picture p258: Most Current Set/Full size sheets/jpgs/013.jpg]

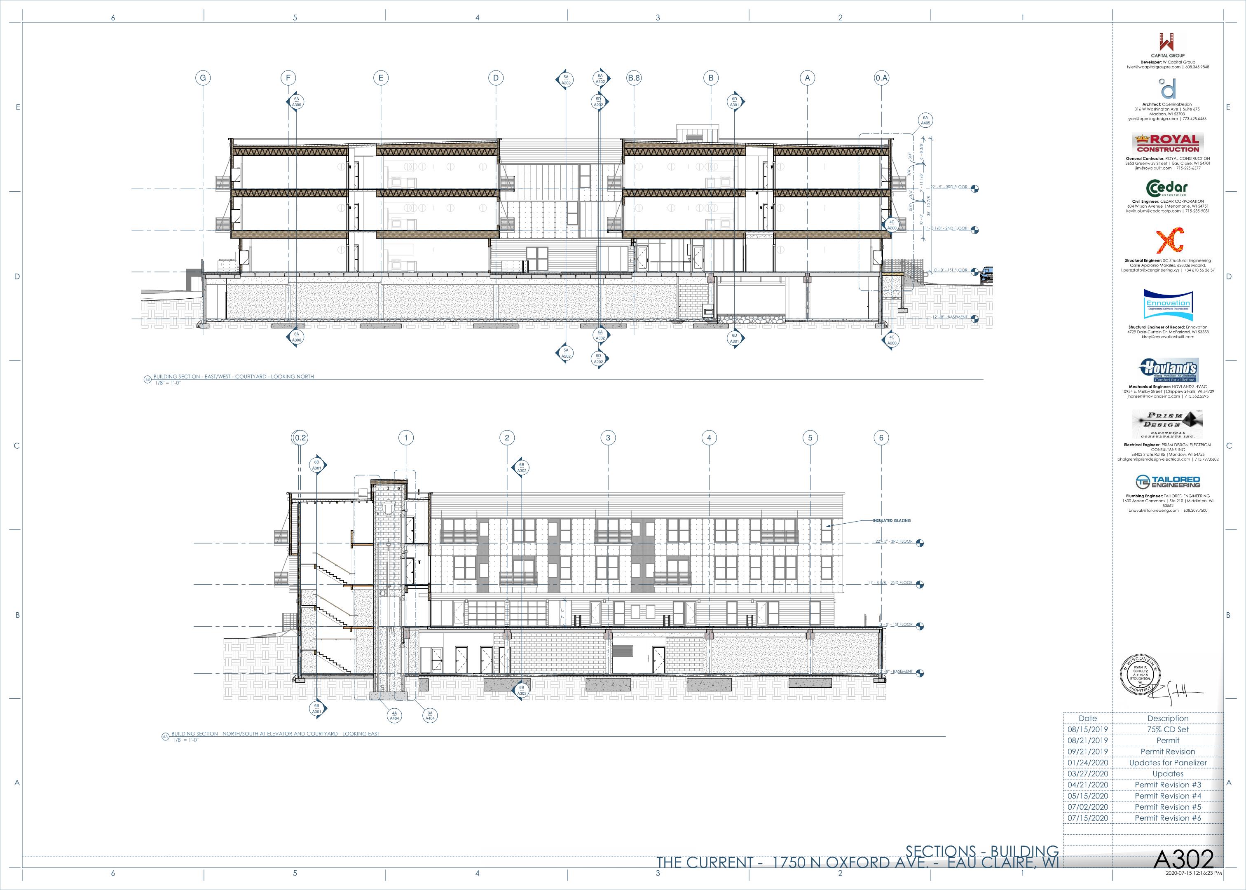
[picture p259: Most Current Set/Full size sheets/jpgs/014.jpg]

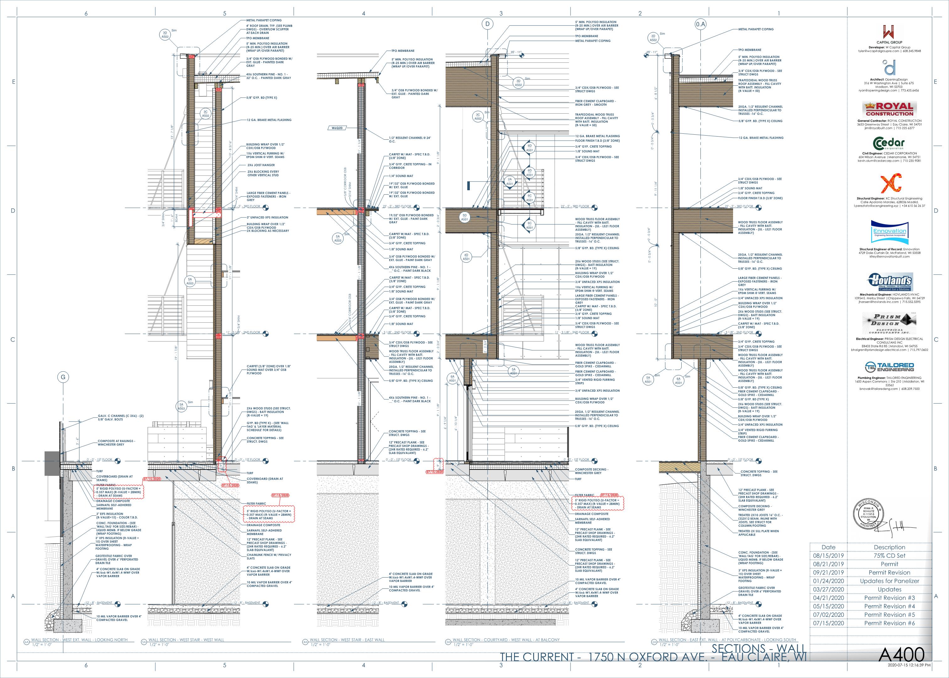
[picture p260: Most Current Set/Full size sheets/jpgs/015.jpg]

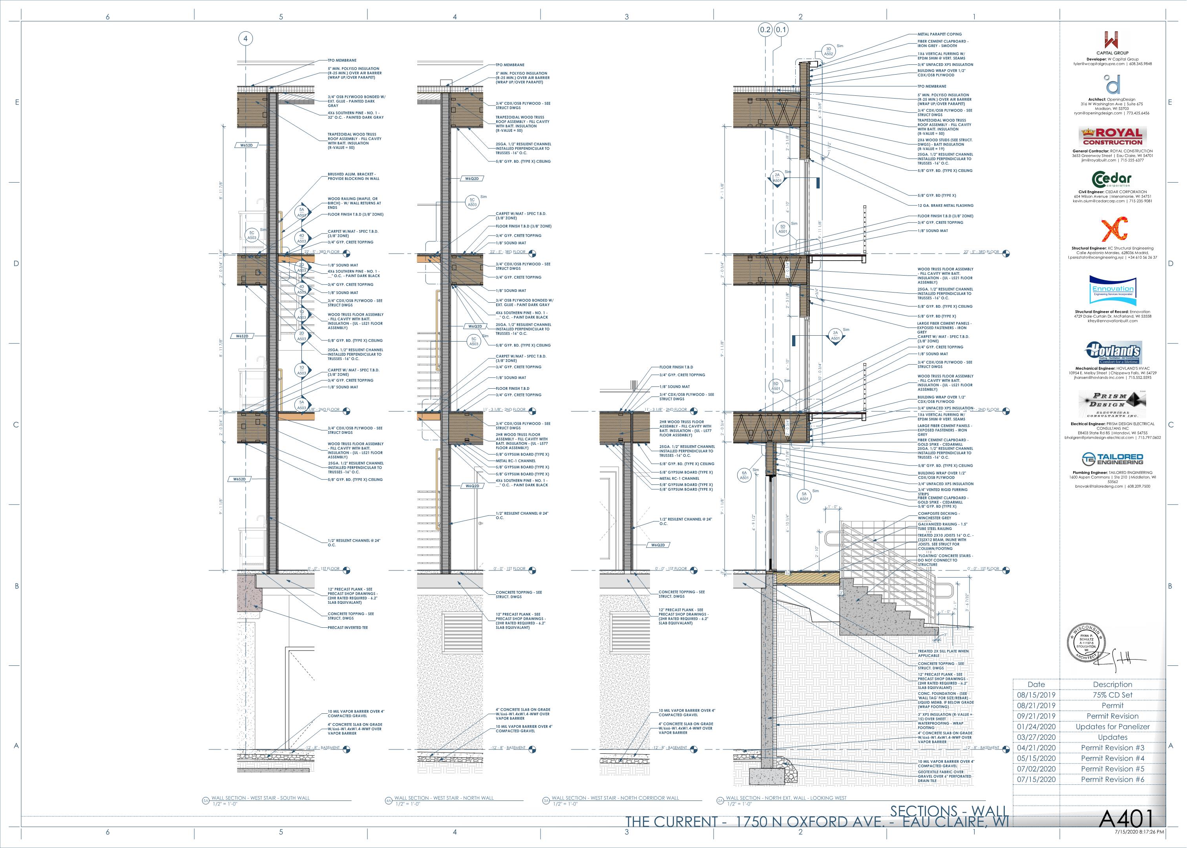
[picture p261: Most Current Set/Full size sheets/jpgs/016.jpg]

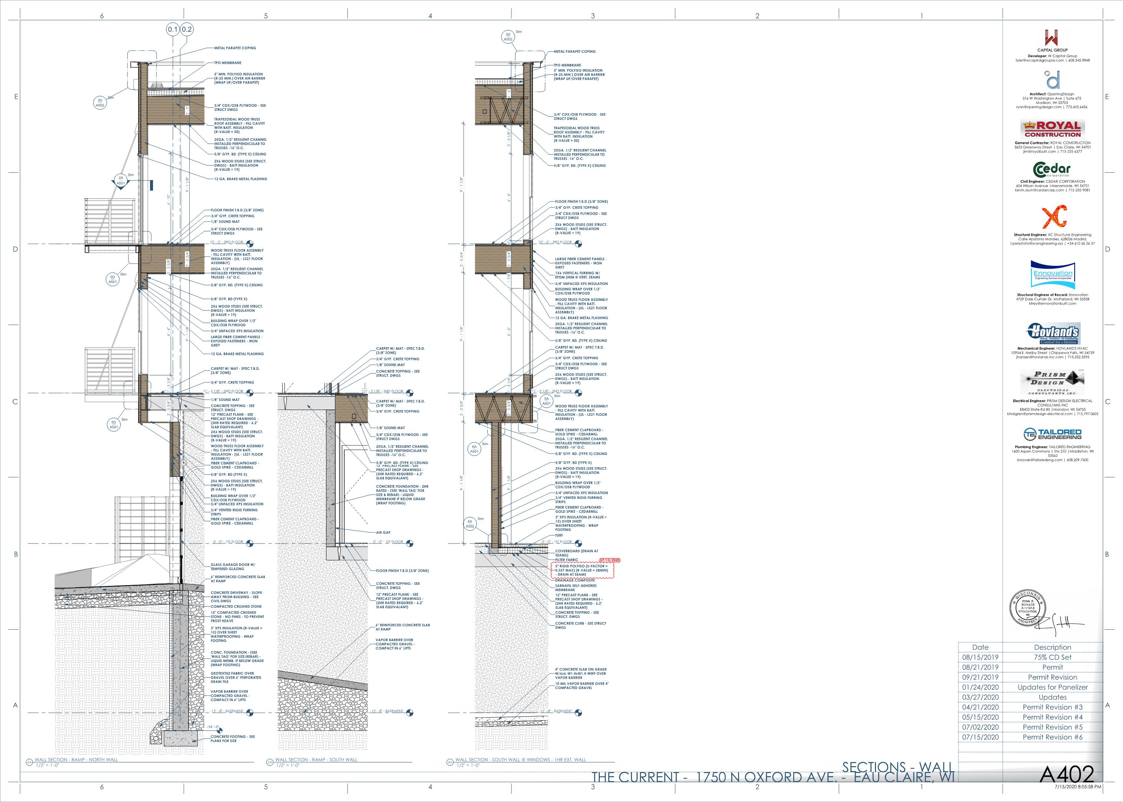
[picture p262: Most Current Set/Full size sheets/jpgs/017.jpg]

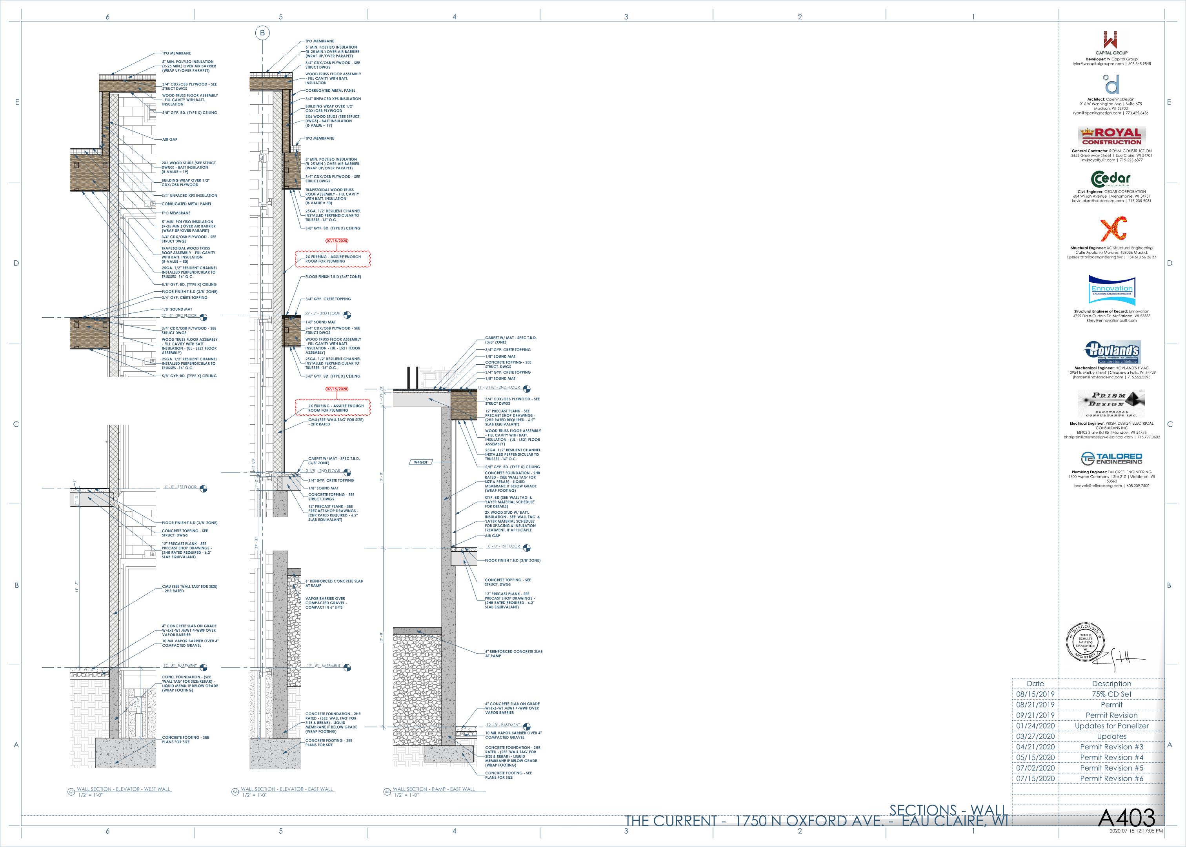
[picture p263: Most Current Set/Full size sheets/jpgs/018.jpg]

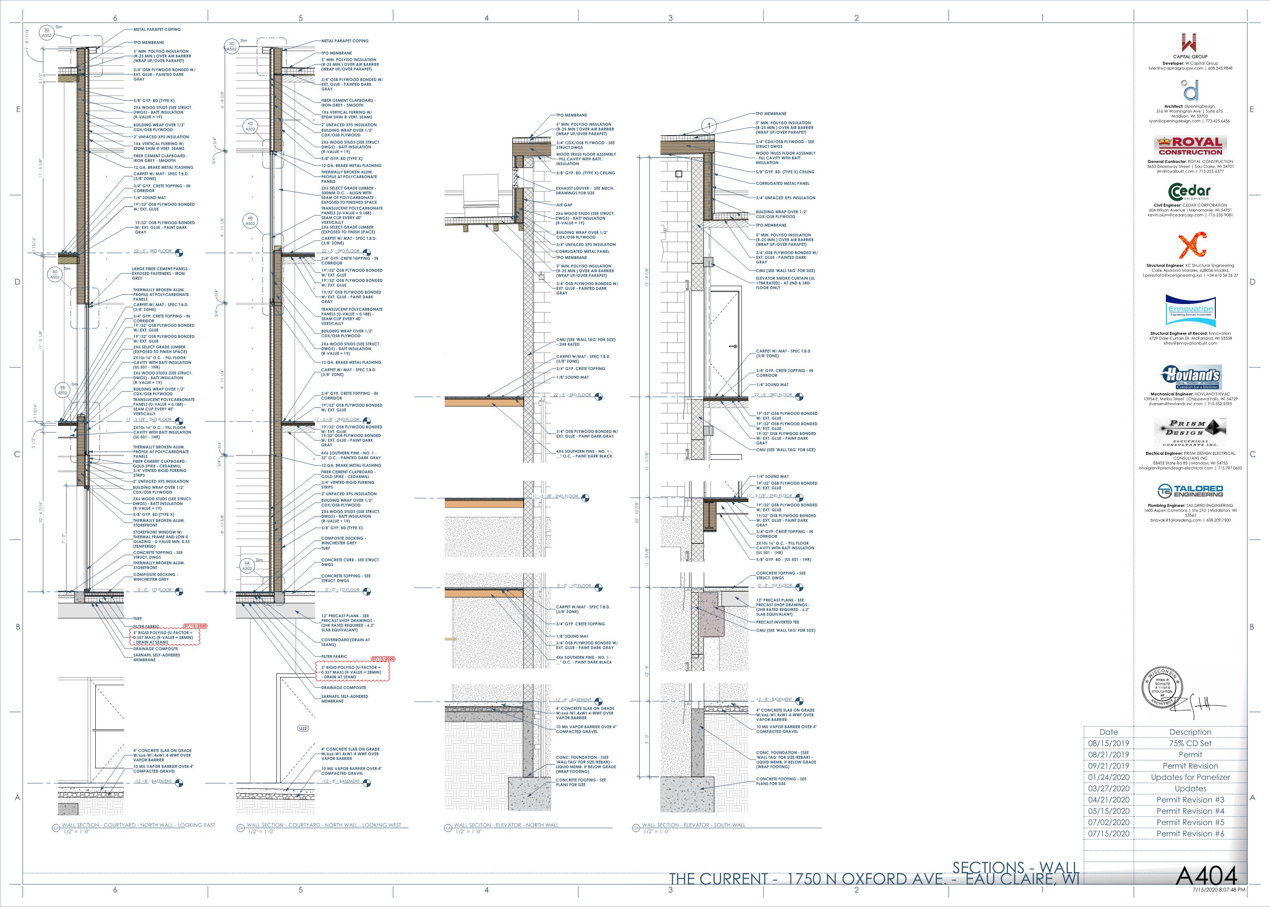
[picture p264: Most Current Set/Full size sheets/jpgs/019.jpg]

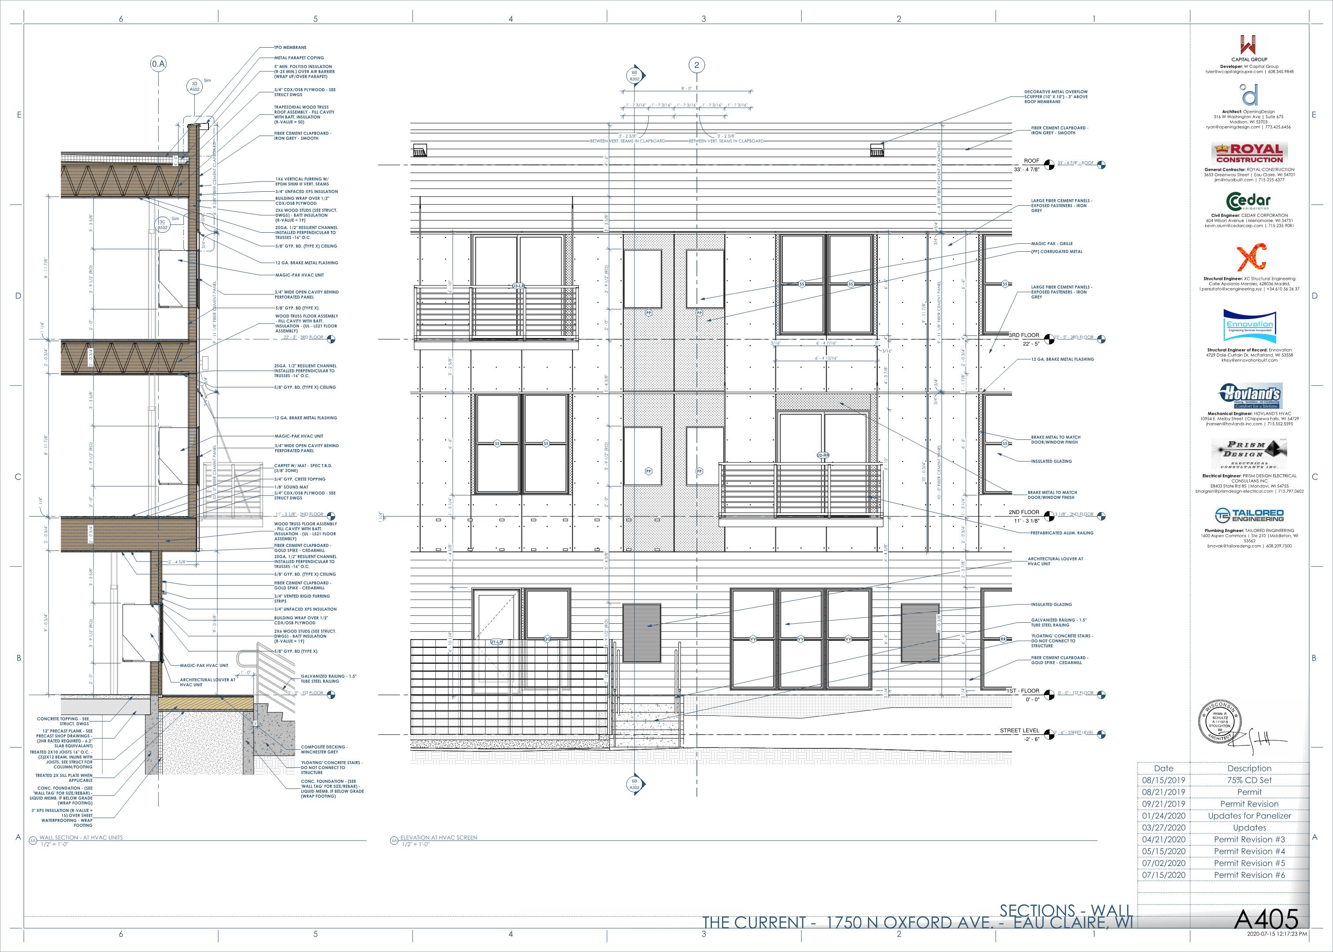
[picture p265: Most Current Set/Full size sheets/jpgs/020.jpg]

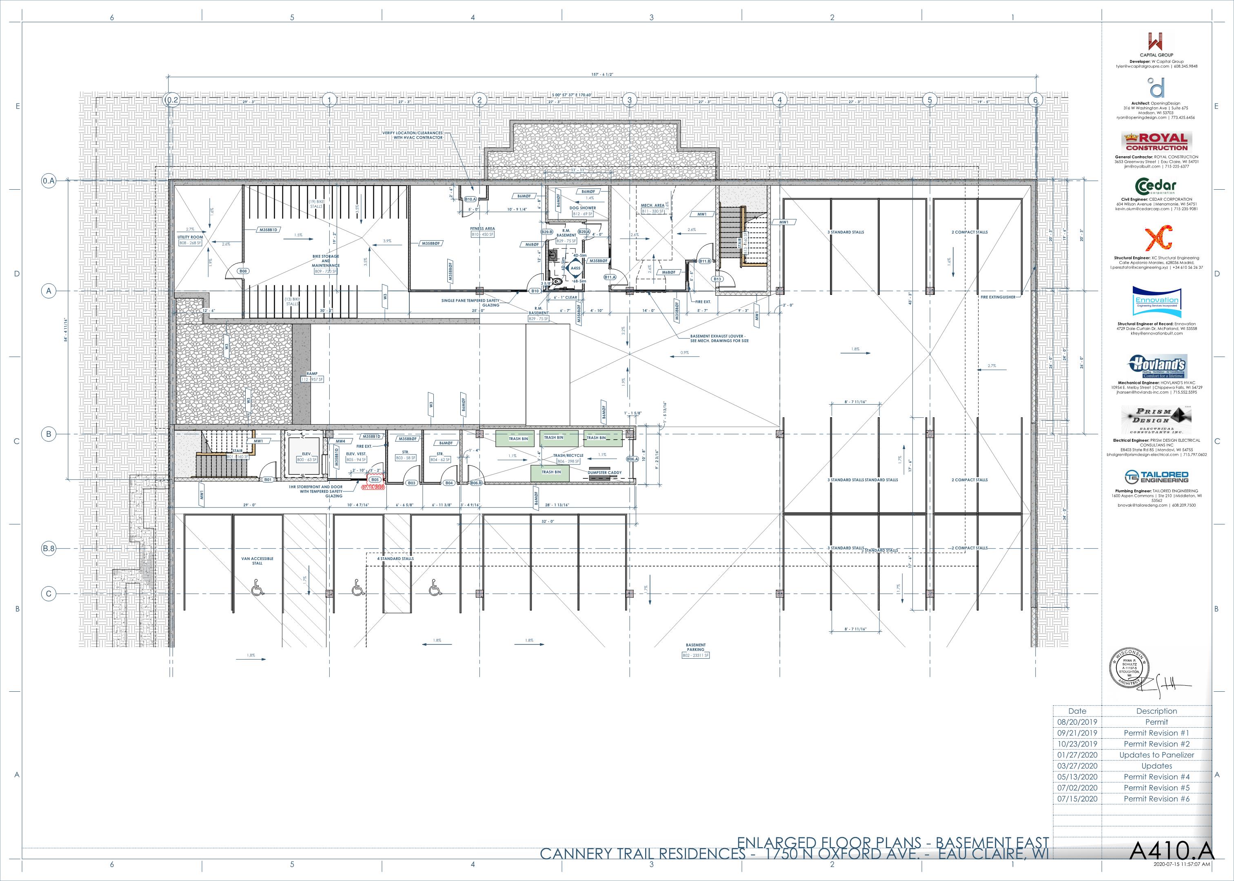
[picture p266: Most Current Set/Full size sheets/jpgs/021.jpg]

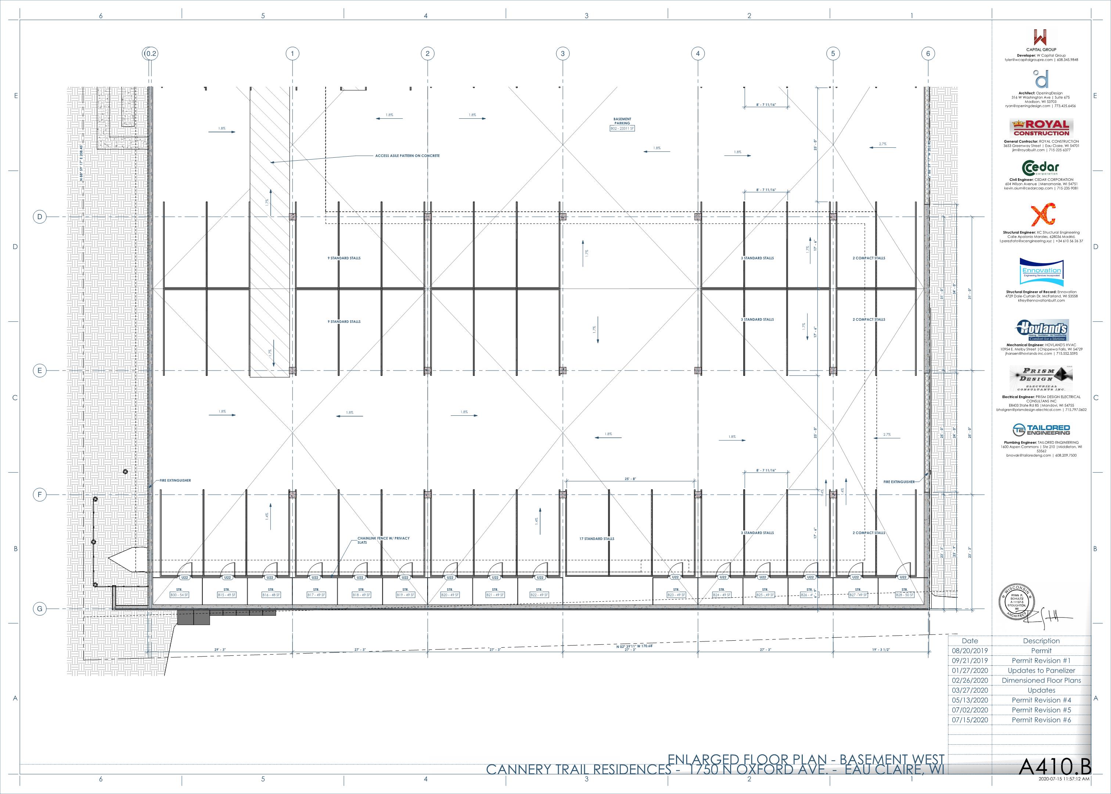
[picture p267: Most Current Set/Full size sheets/jpgs/022.jpg]

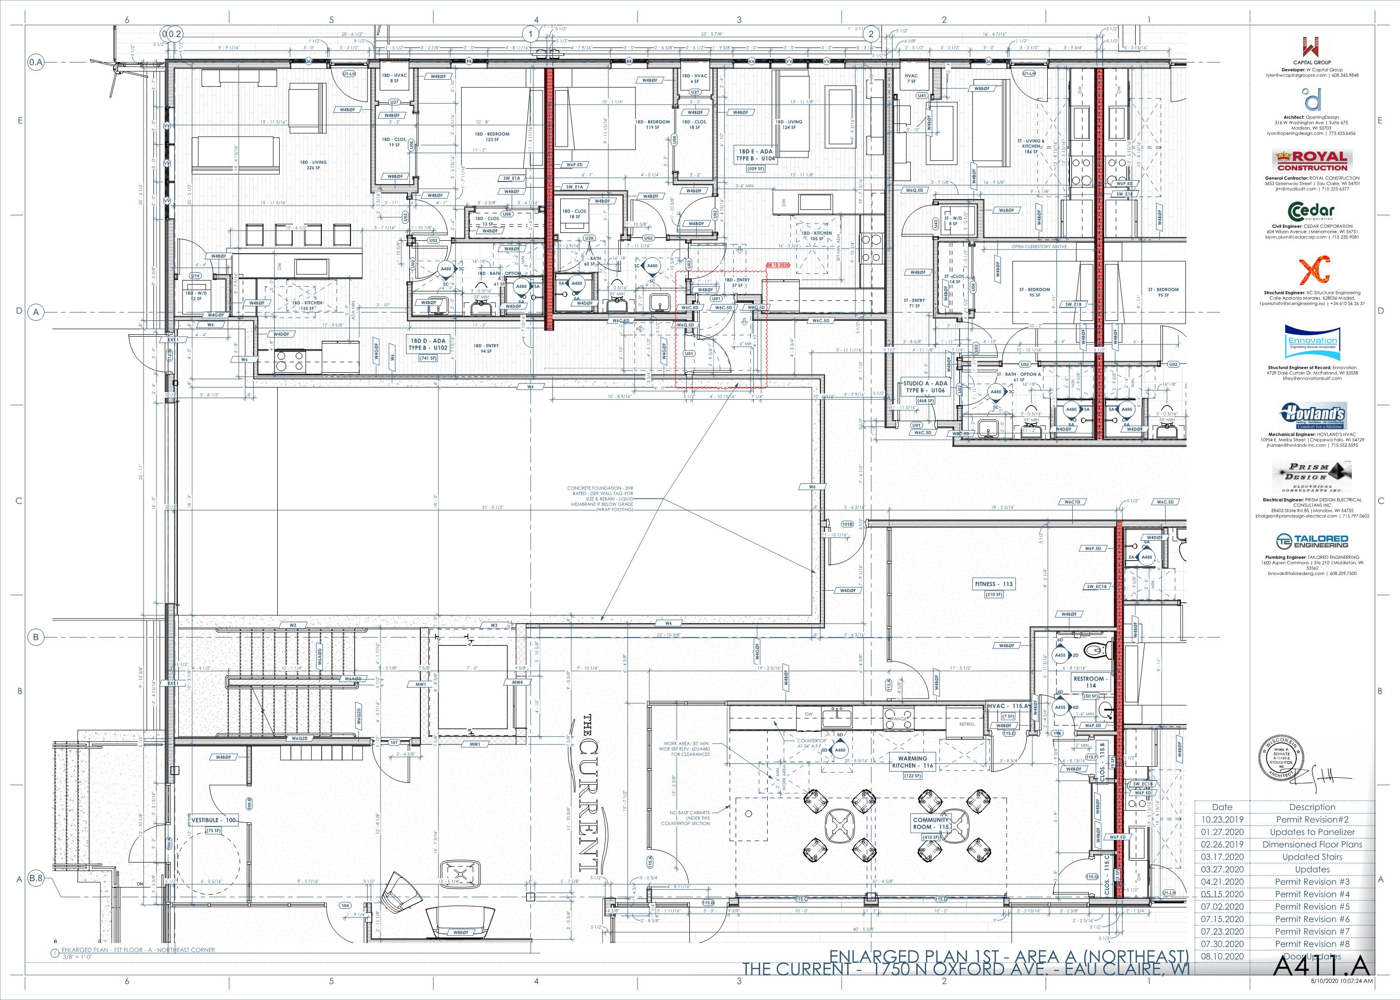
[picture p268: Most Current Set/Full size sheets/jpgs/023.jpg]

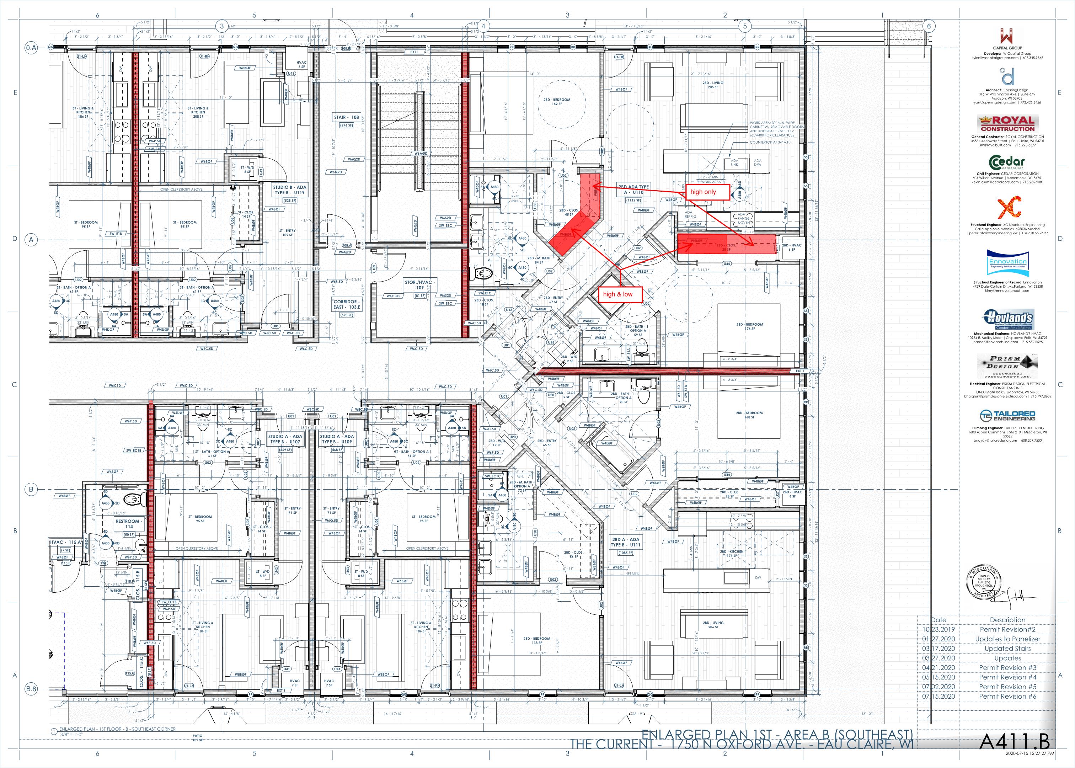
[picture p269: Most Current Set/Full size sheets/jpgs/024.jpg]

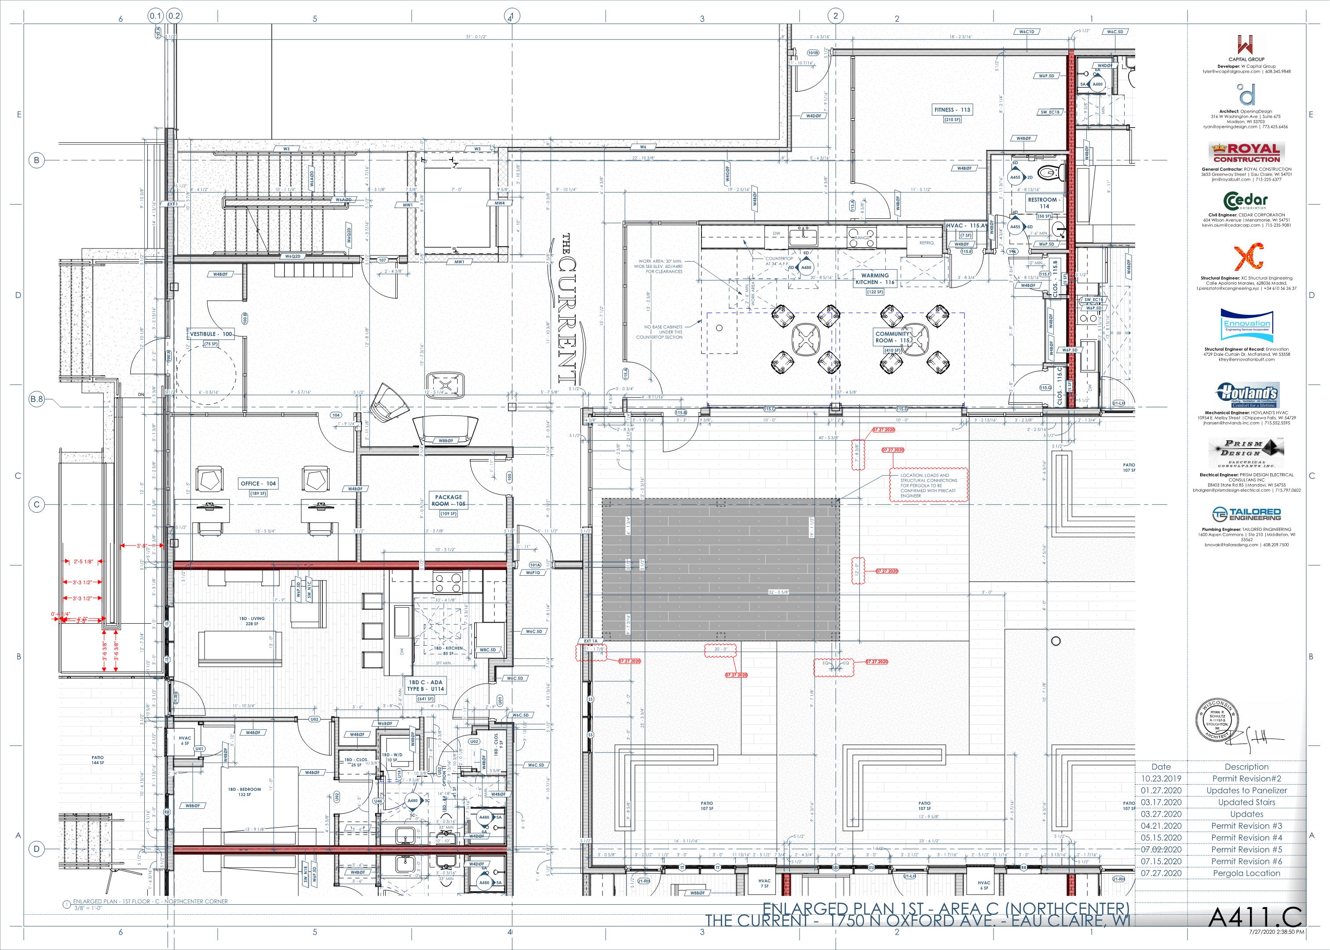
[picture p270: Most Current Set/Full size sheets/jpgs/025.jpg]

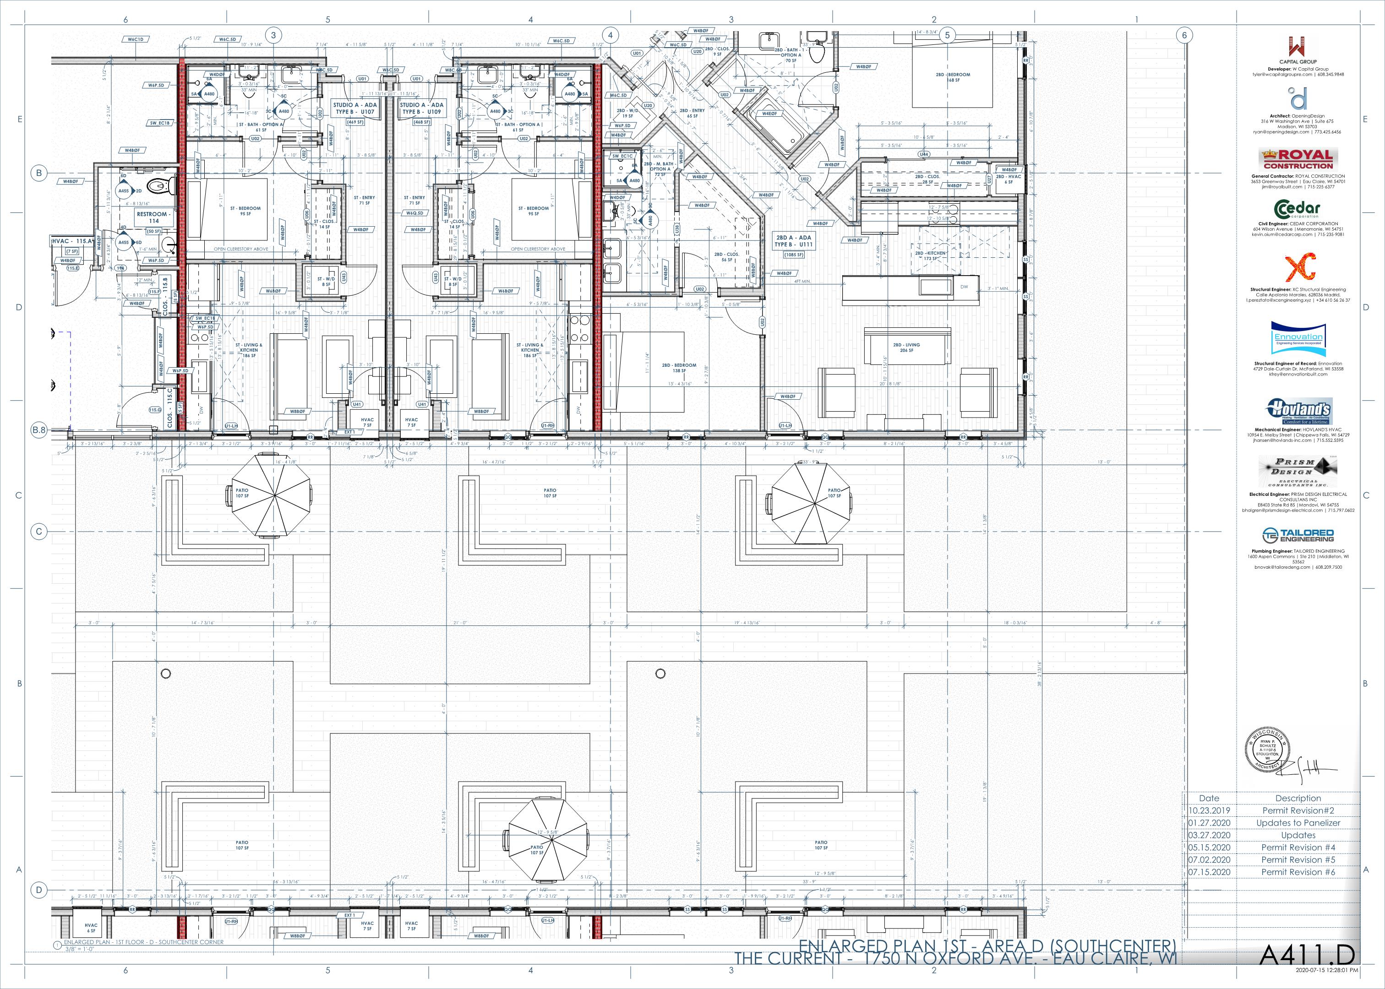
[picture p271: Most Current Set/Full size sheets/jpgs/026.jpg]

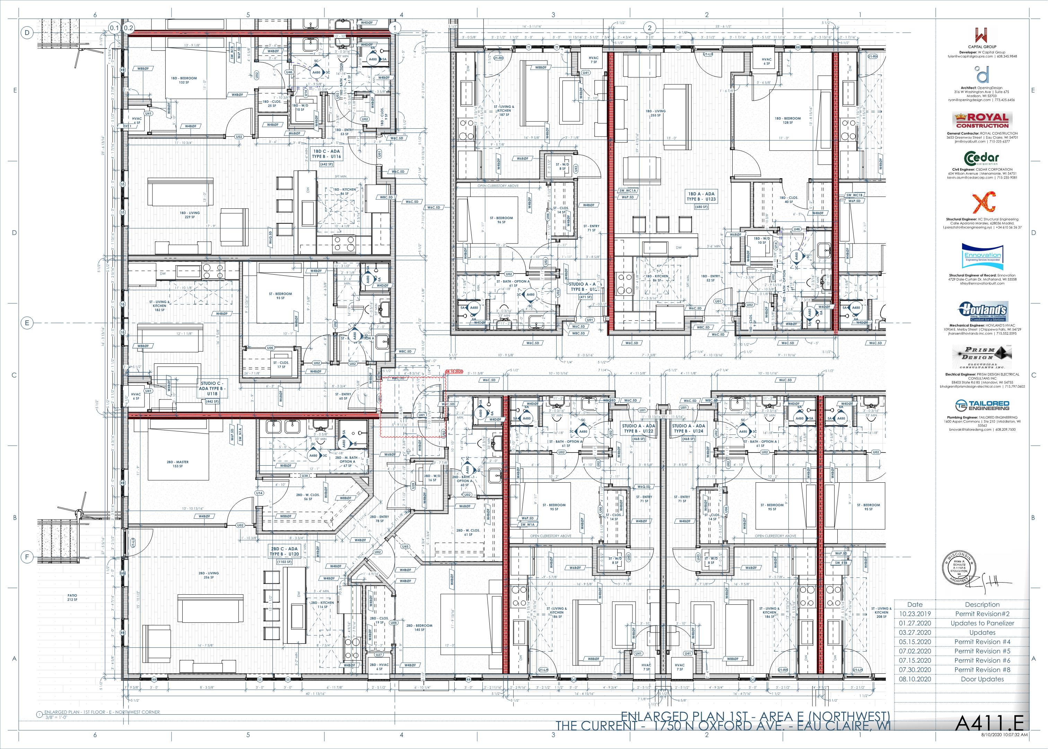
[picture p272: Most Current Set/Full size sheets/jpgs/027.jpg]

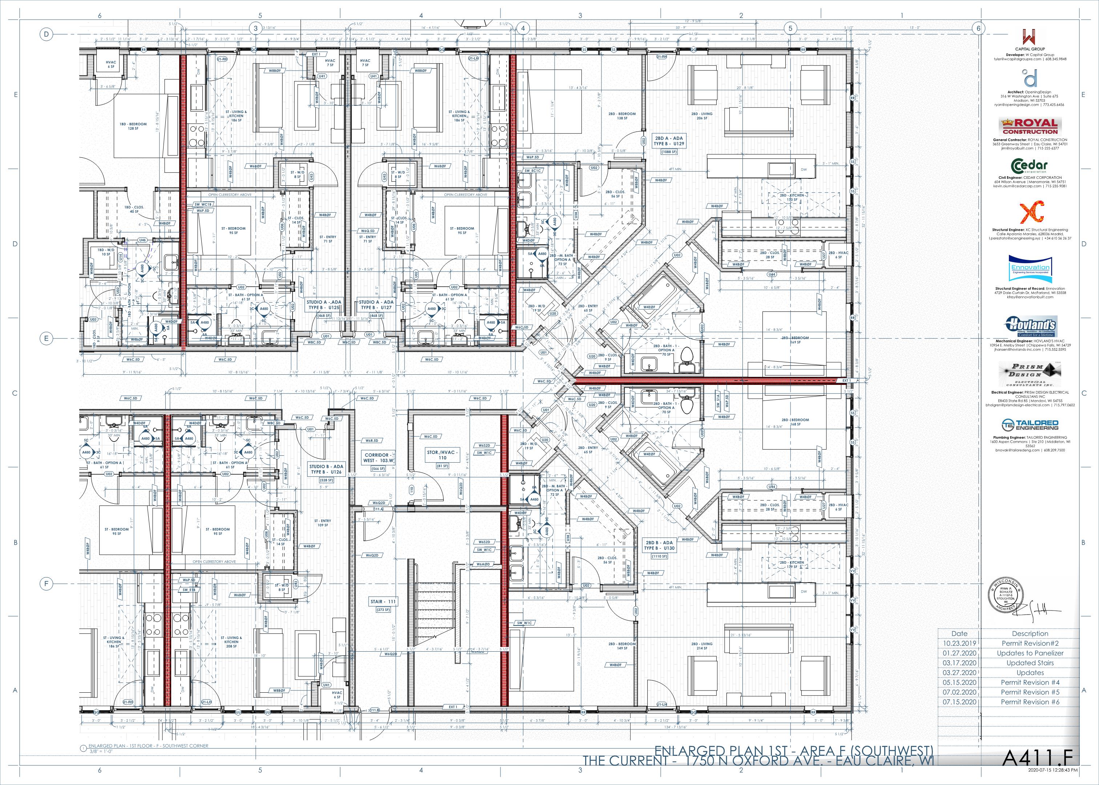
[picture p273: Most Current Set/Full size sheets/jpgs/028.jpg]

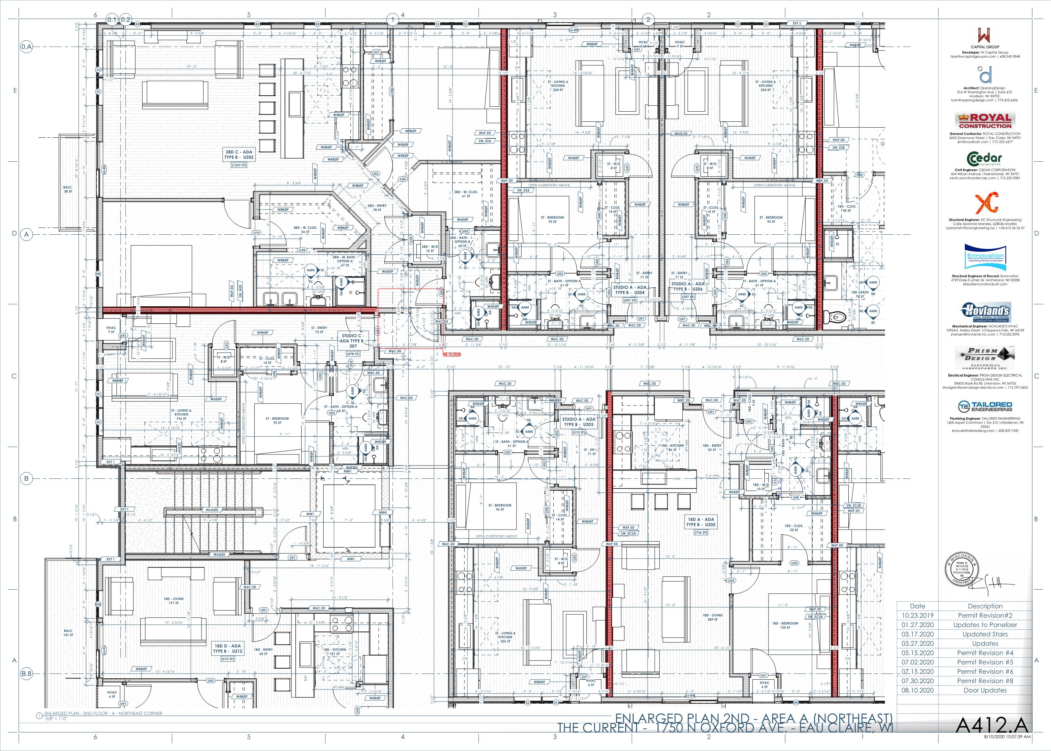
[picture p274: Most Current Set/Full size sheets/jpgs/029.jpg]

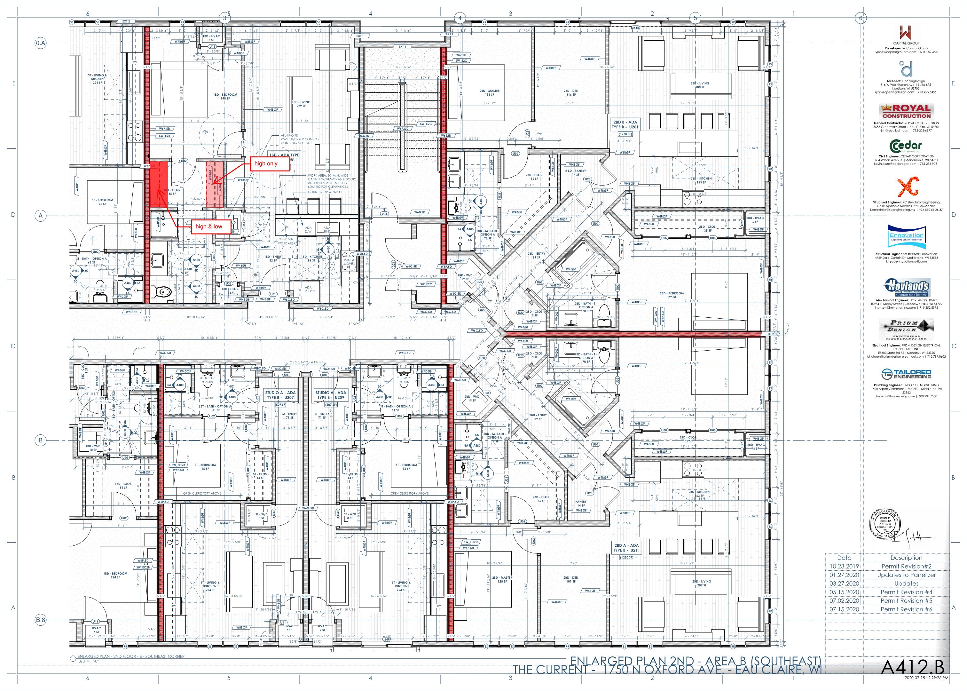
[picture p275: Most Current Set/Full size sheets/jpgs/030.jpg]

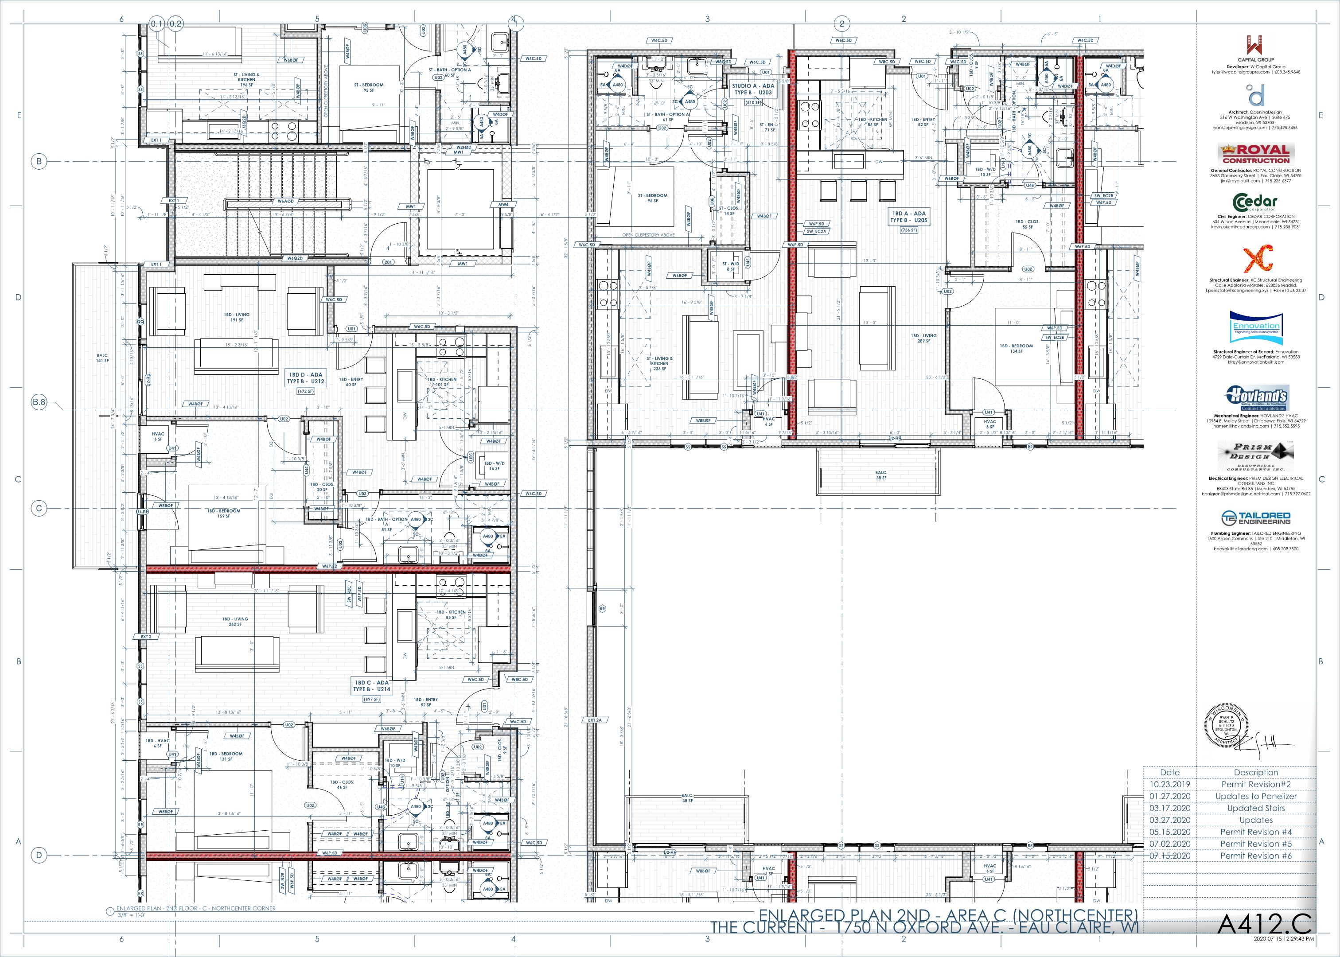
[picture p276: Most Current Set/Full size sheets/jpgs/031.jpg]

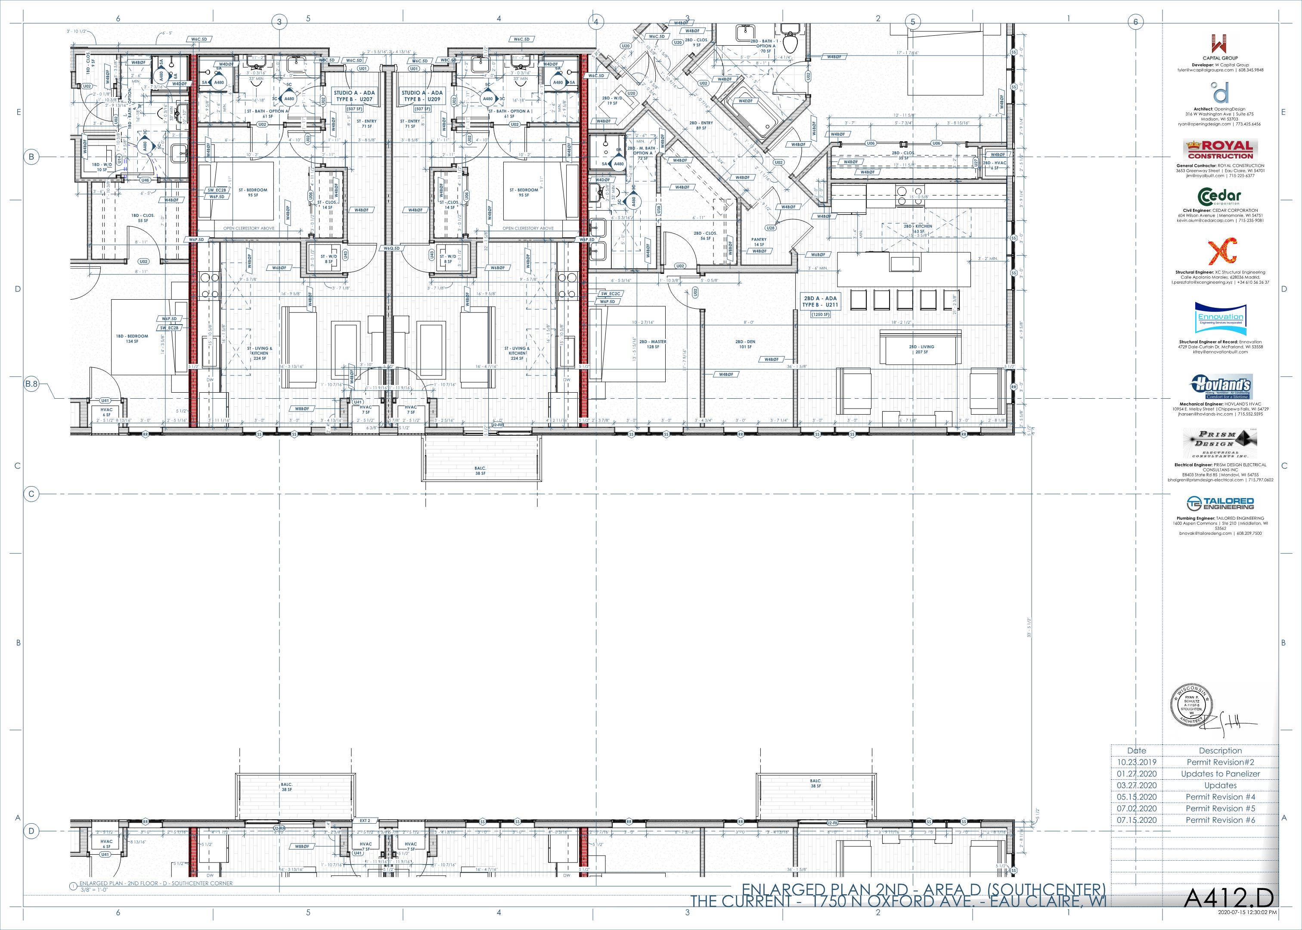
[picture p277: Most Current Set/Full size sheets/jpgs/032.jpg]

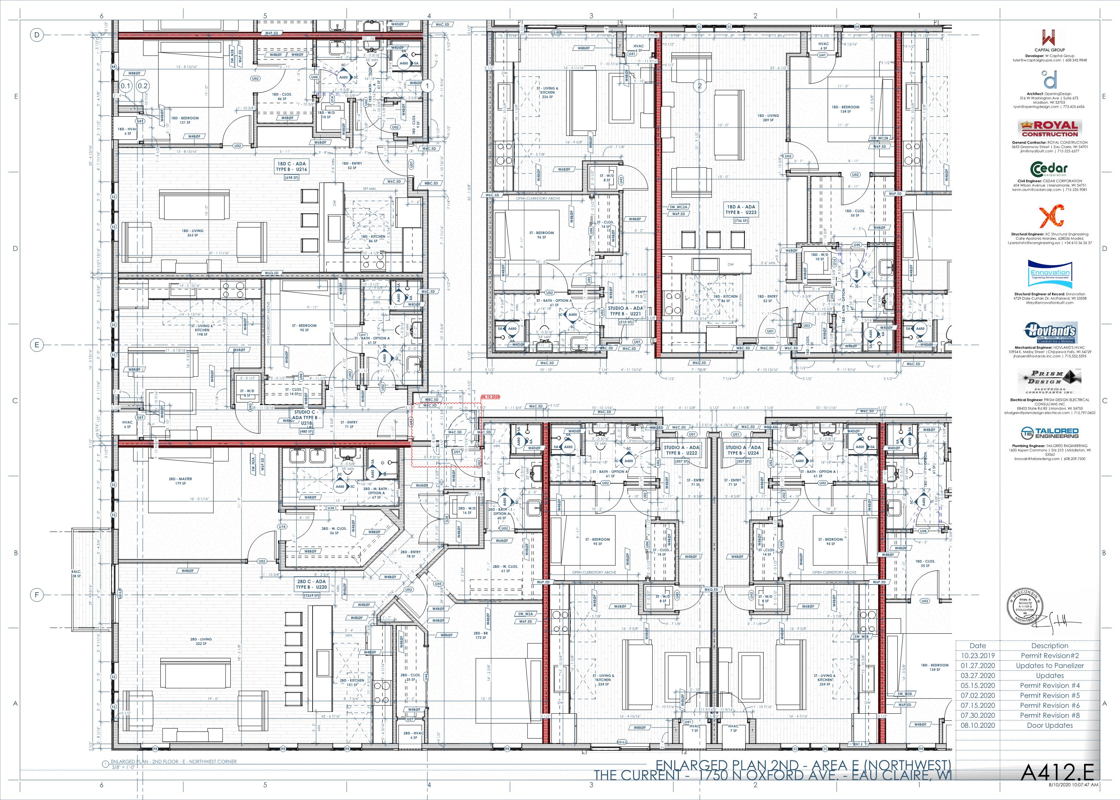
[picture p278: Most Current Set/Full size sheets/jpgs/033.jpg]

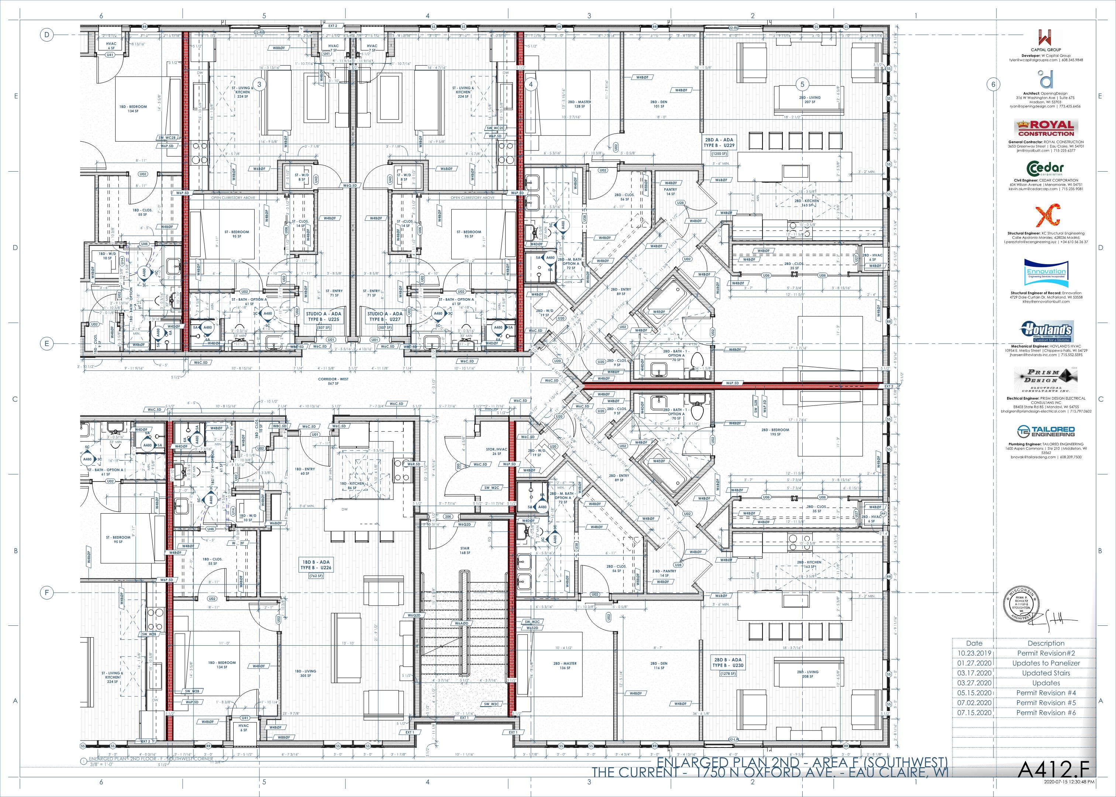
[picture p279: Most Current Set/Full size sheets/jpgs/034.jpg]

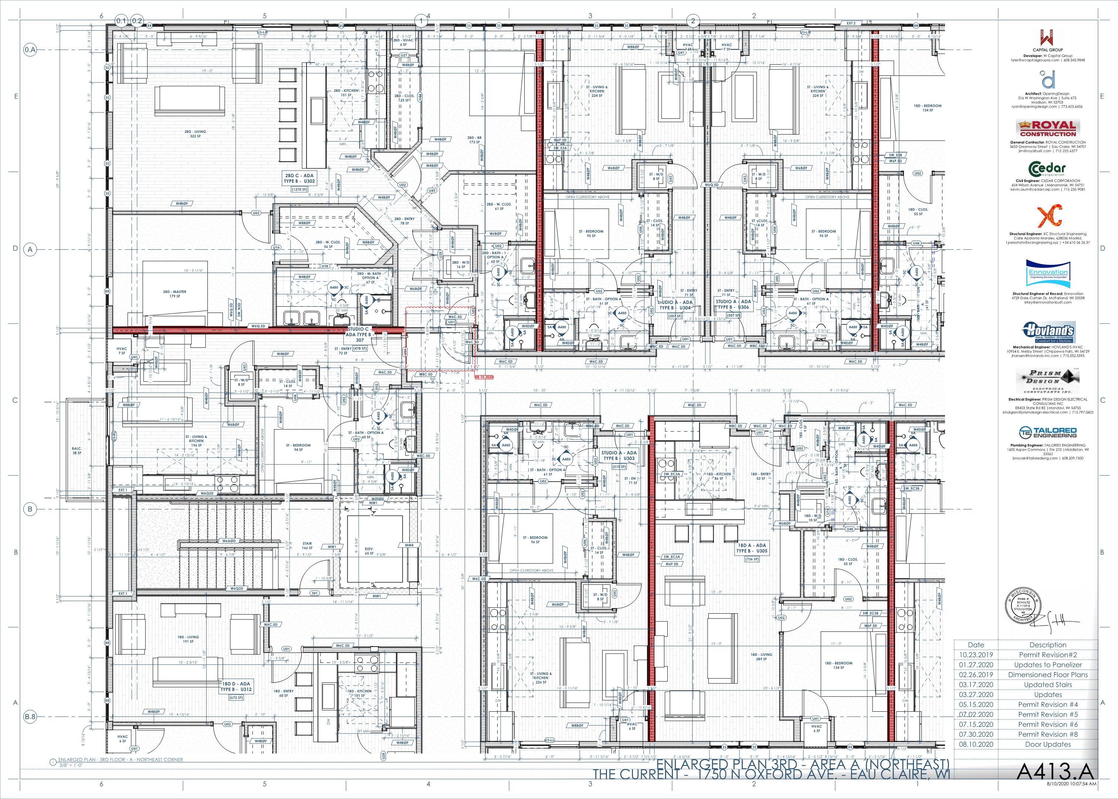
[picture p280: Most Current Set/Full size sheets/jpgs/035.jpg]

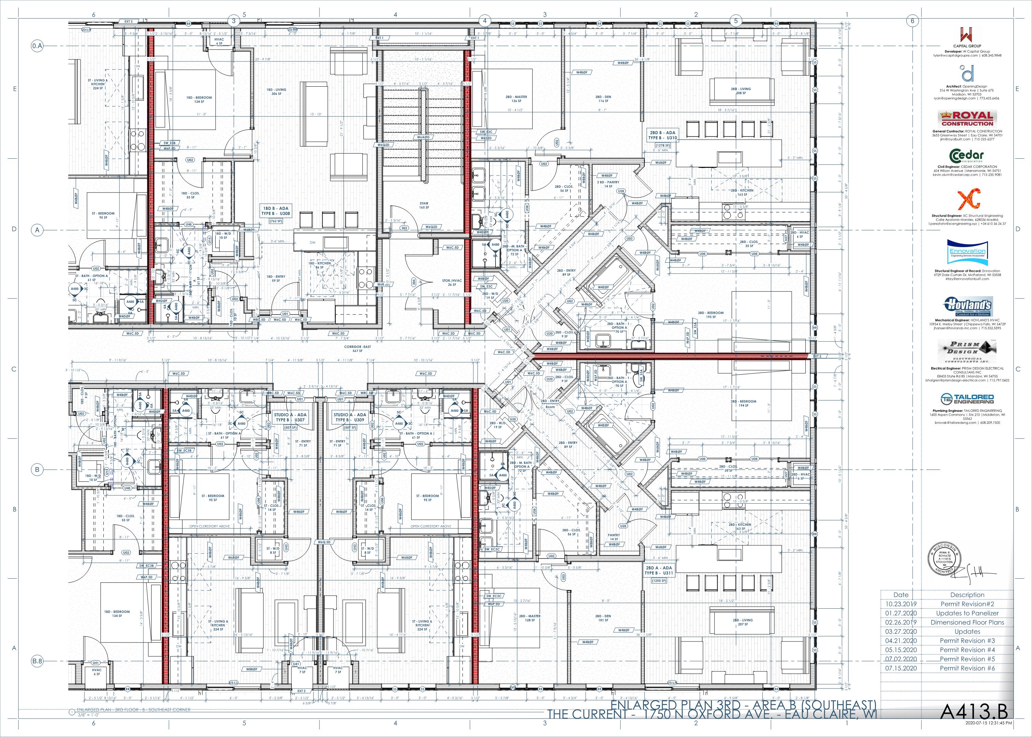
[picture p281: Most Current Set/Full size sheets/jpgs/036.jpg]

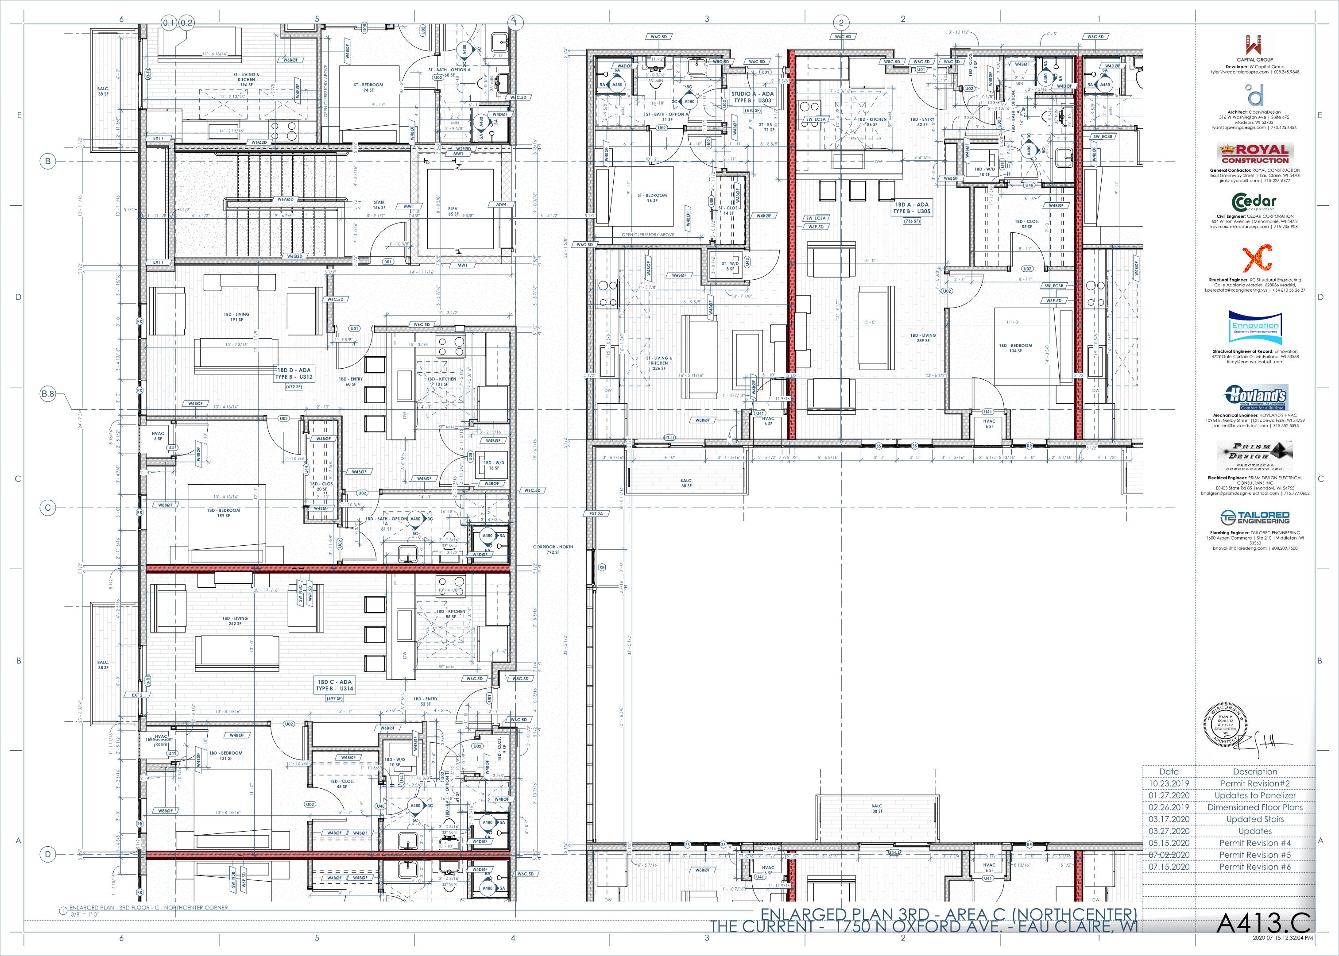
[picture p282: Most Current Set/Full size sheets/jpgs/037.jpg]

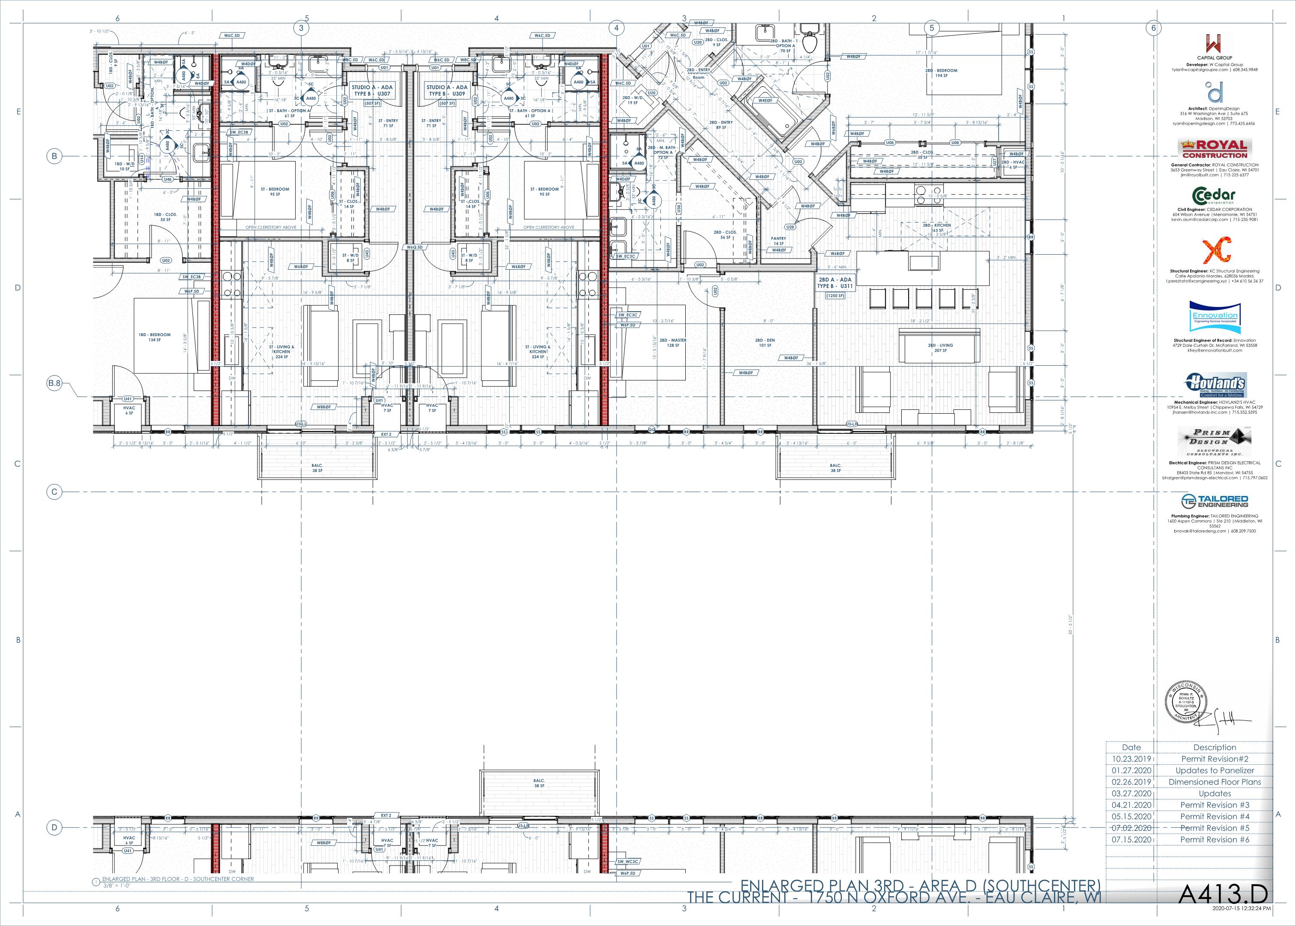
[picture p283: Most Current Set/Full size sheets/jpgs/038.jpg]

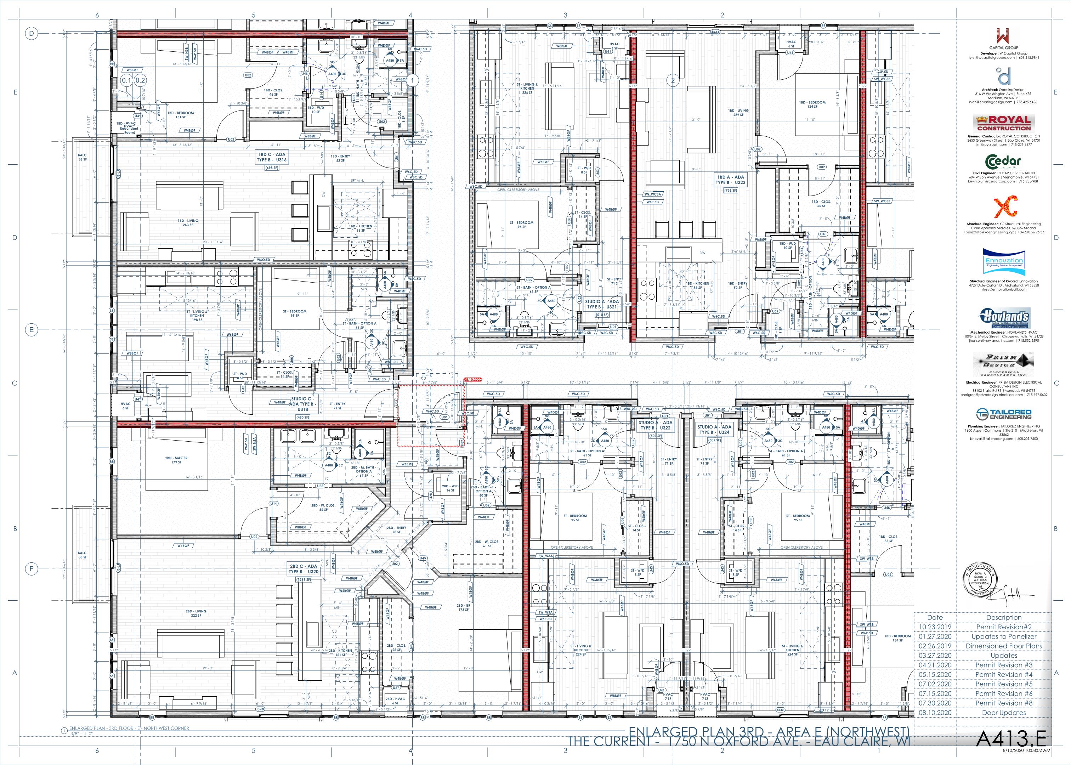
[picture p284: Most Current Set/Full size sheets/jpgs/039.jpg]

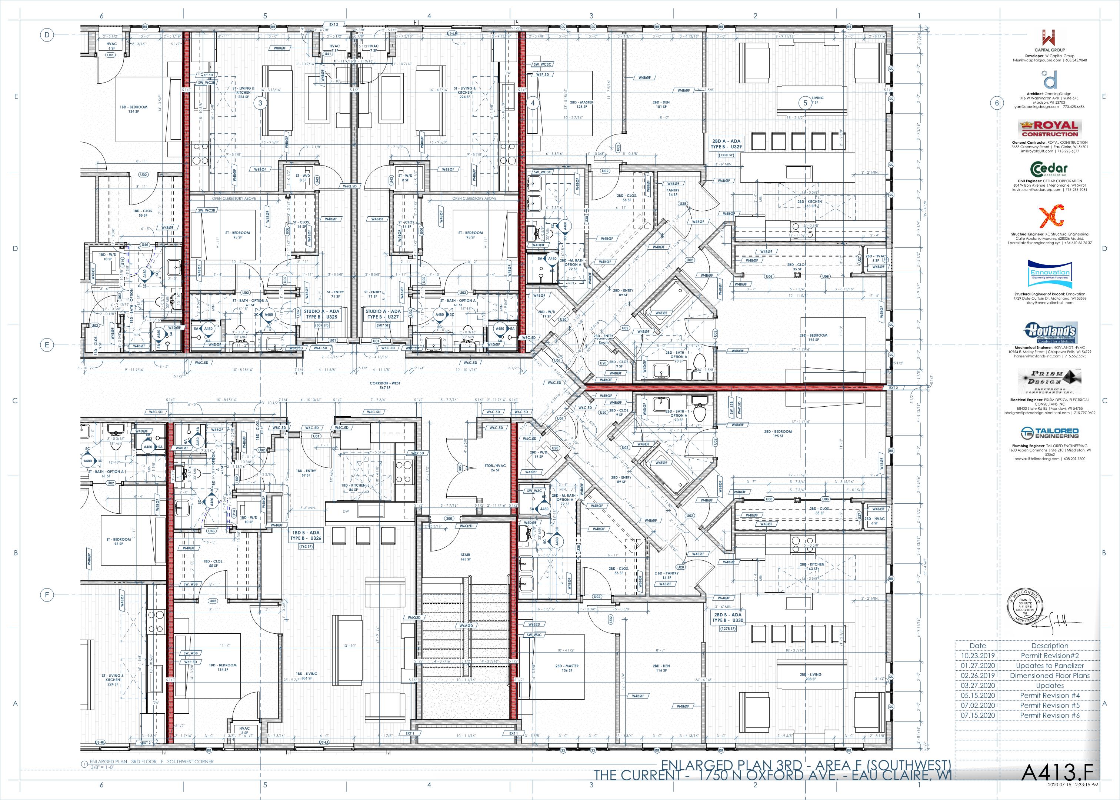
[picture p285: Most Current Set/Full size sheets/jpgs/040.jpg]

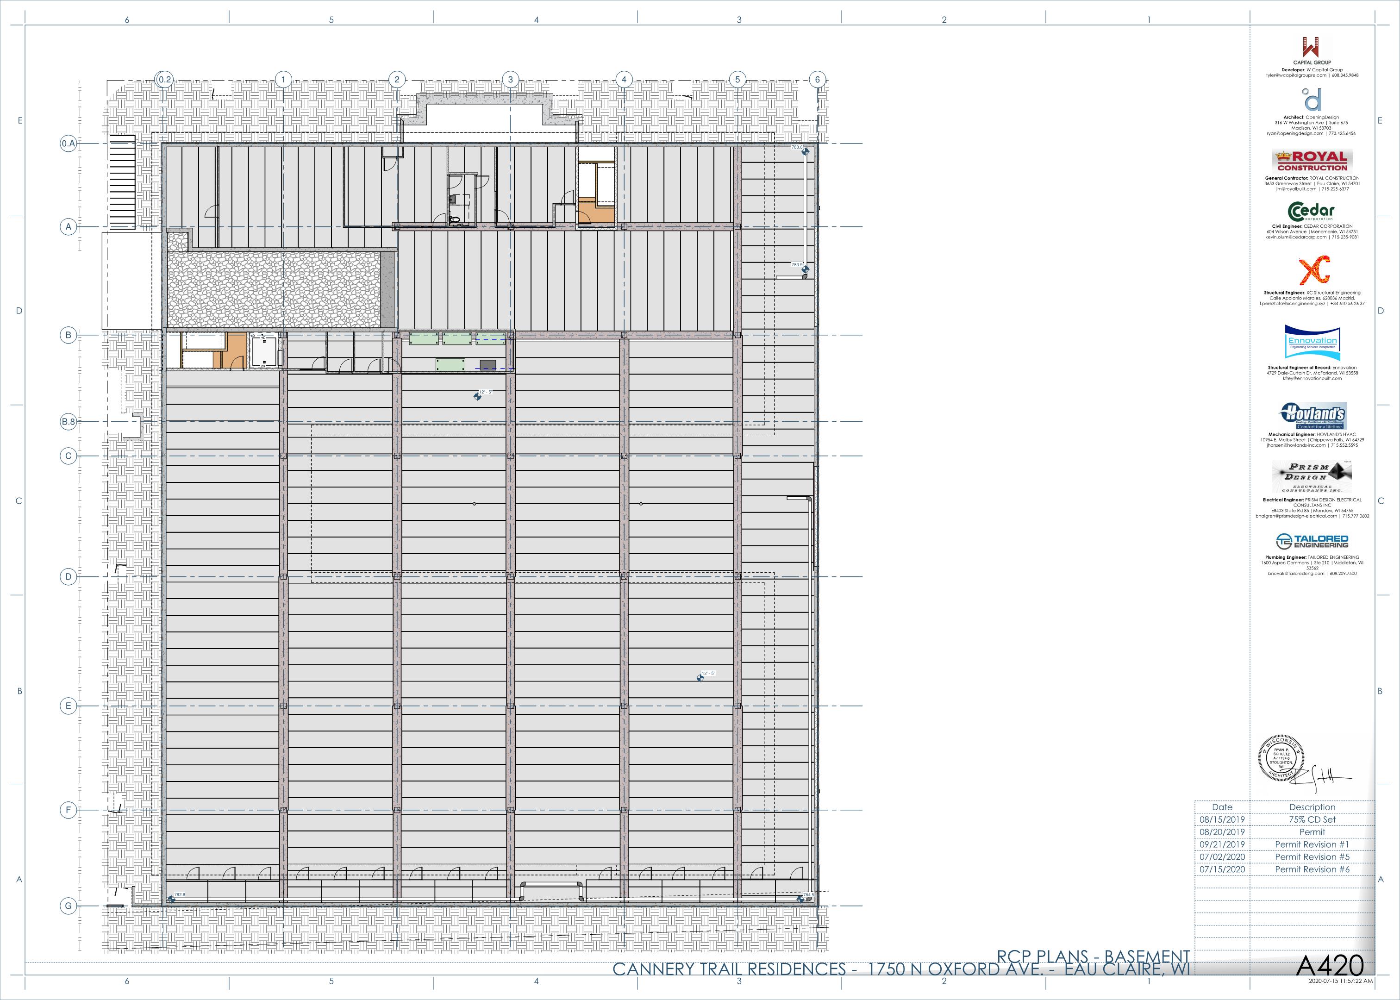
[picture p286: Most Current Set/Full size sheets/jpgs/041.jpg]

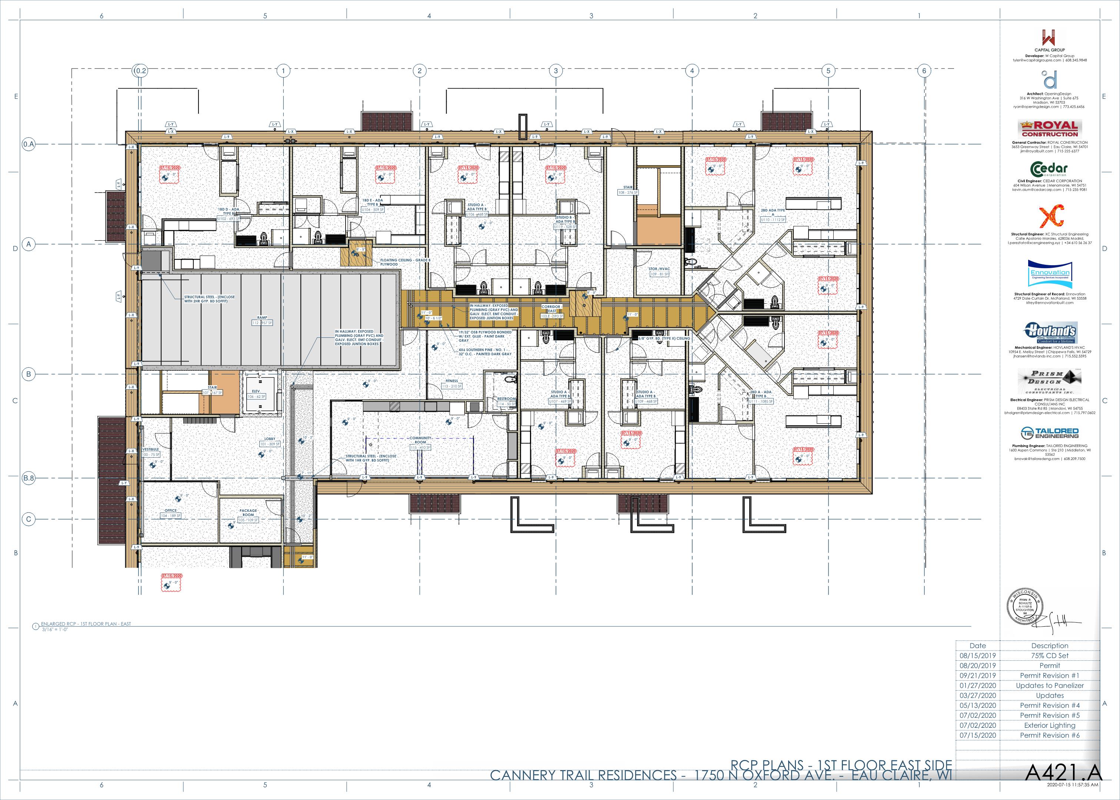
[picture p287: Most Current Set/Full size sheets/jpgs/042.jpg]

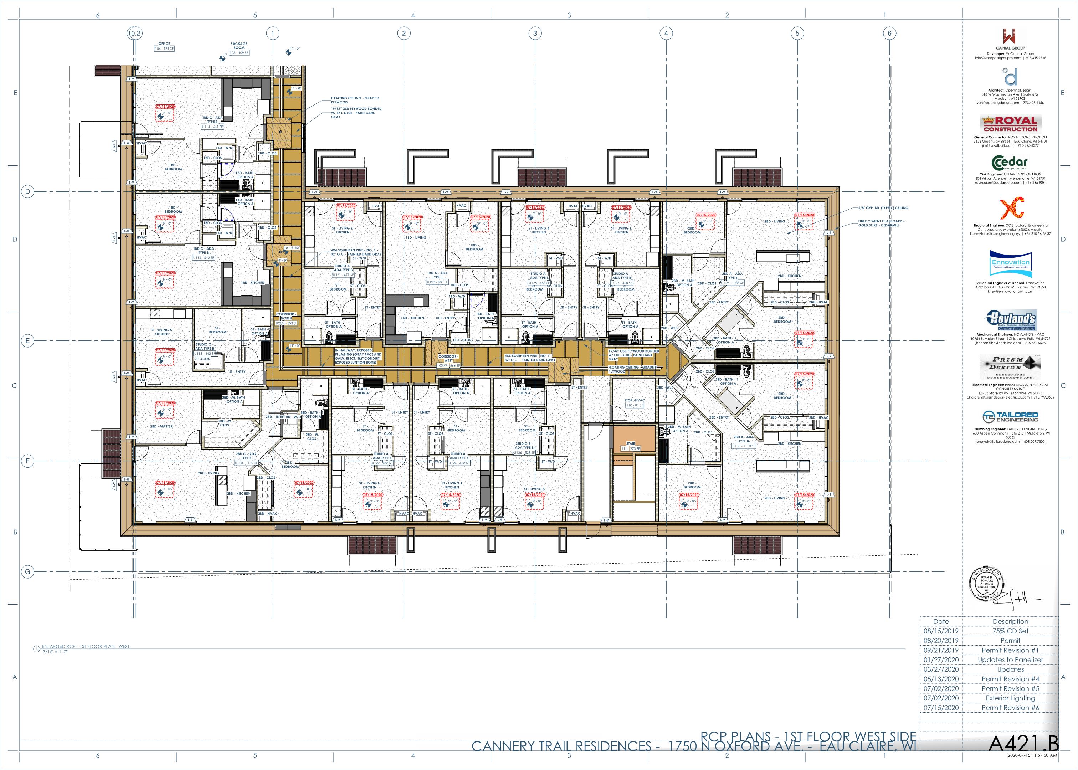
[picture p288: Most Current Set/Full size sheets/jpgs/043.jpg]

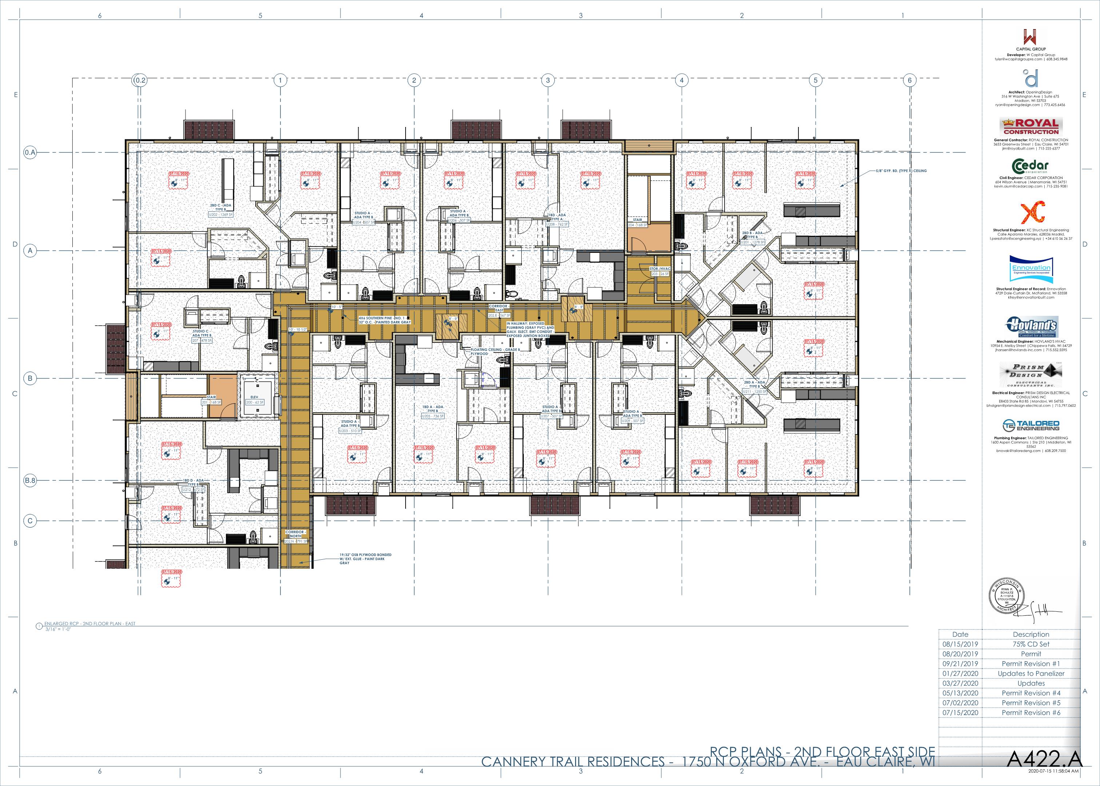
[picture p289: Most Current Set/Full size sheets/jpgs/044.jpg]

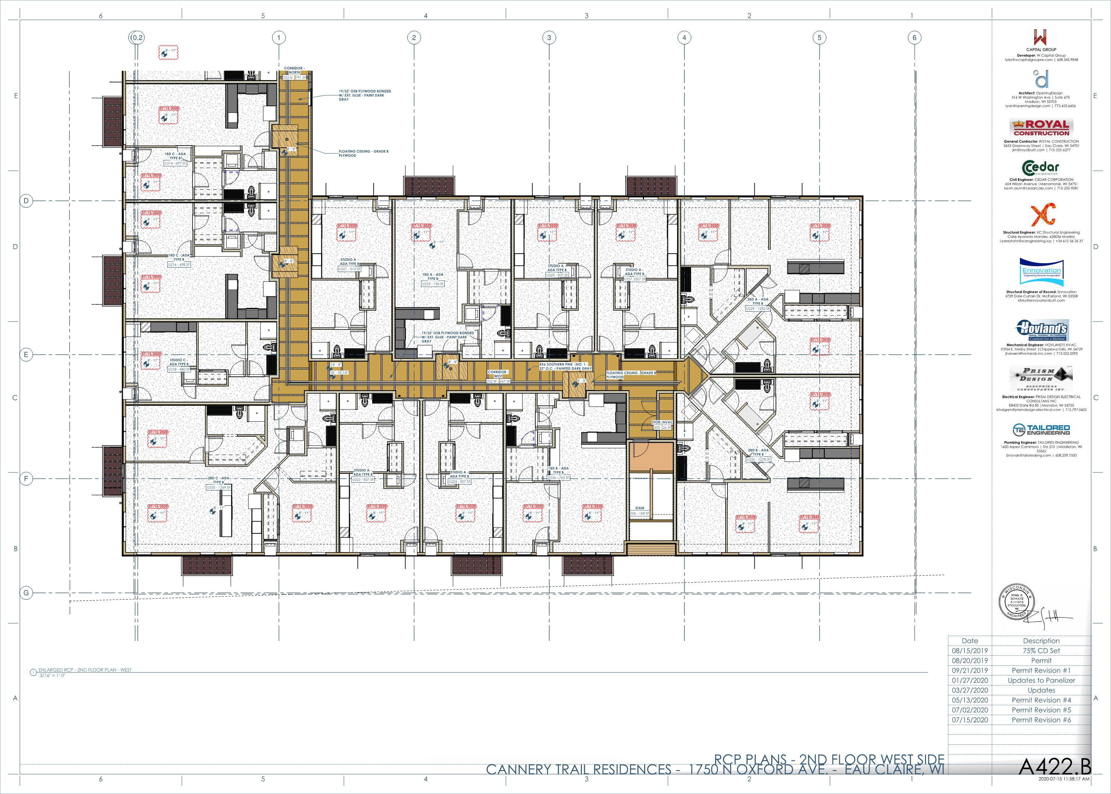
[picture p290: Most Current Set/Full size sheets/jpgs/045.jpg]

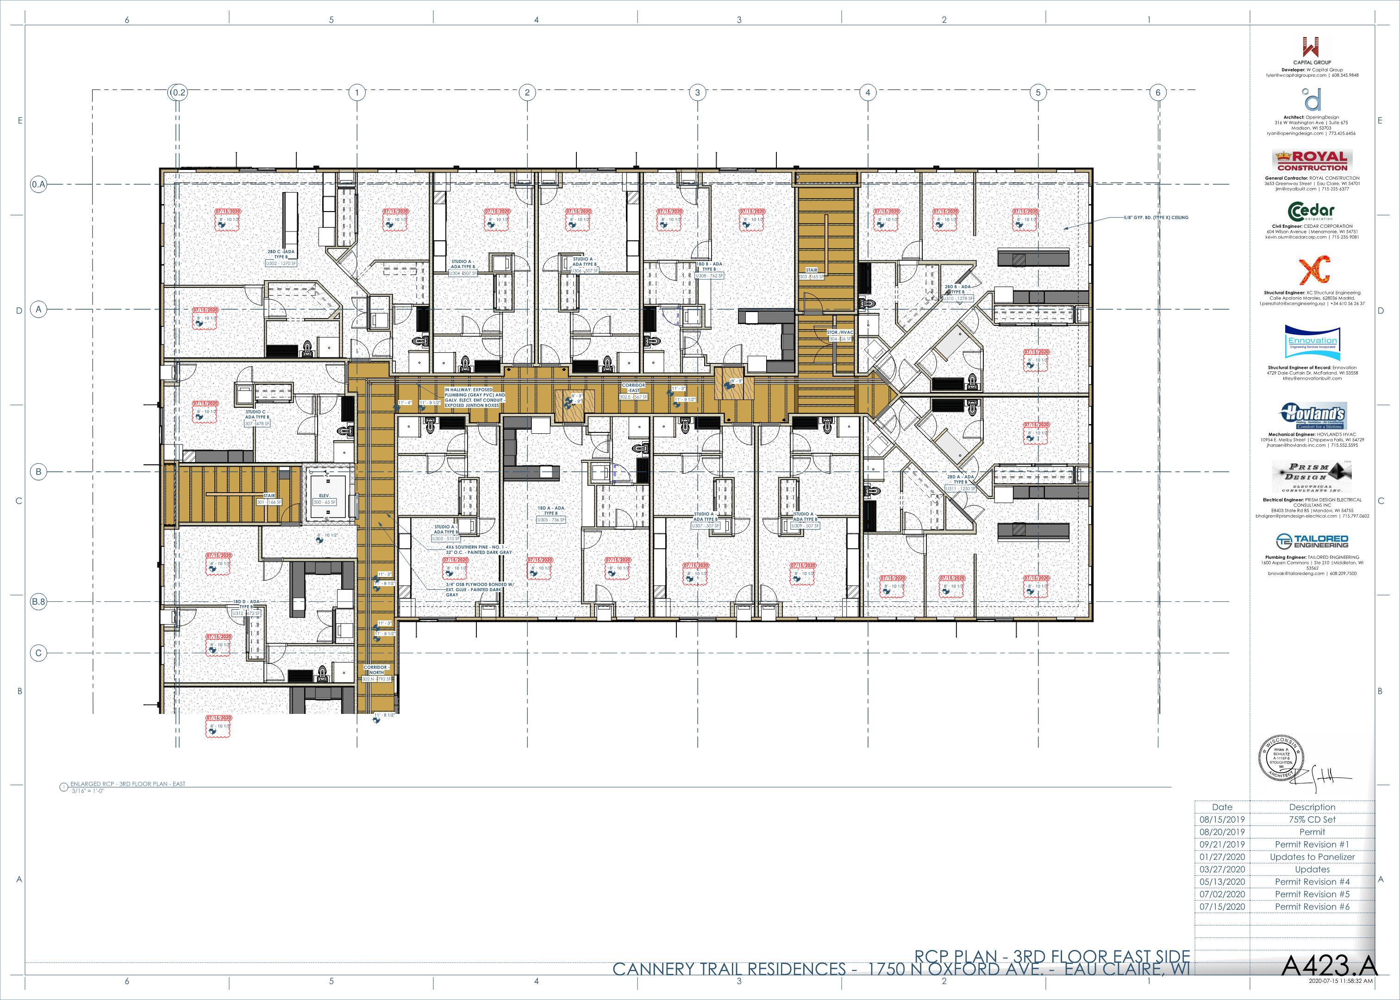
[picture p291: Most Current Set/Full size sheets/jpgs/046.jpg]

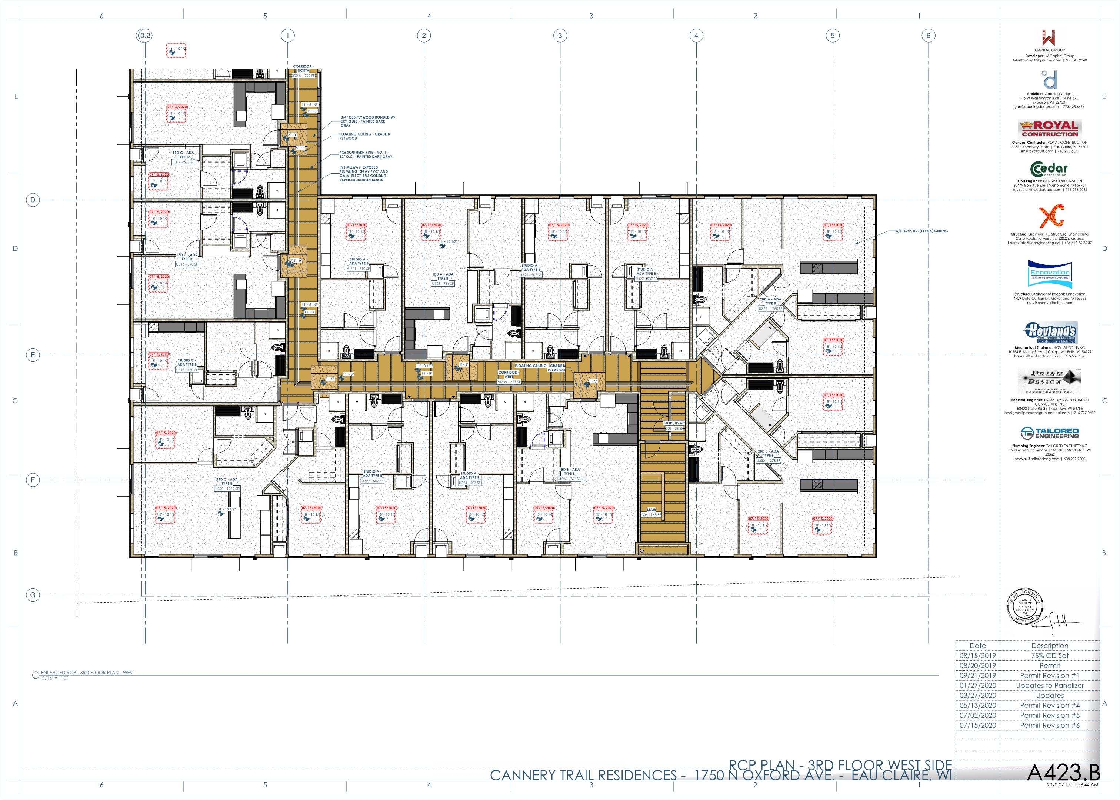
[picture p292: Most Current Set/Full size sheets/jpgs/047.jpg]

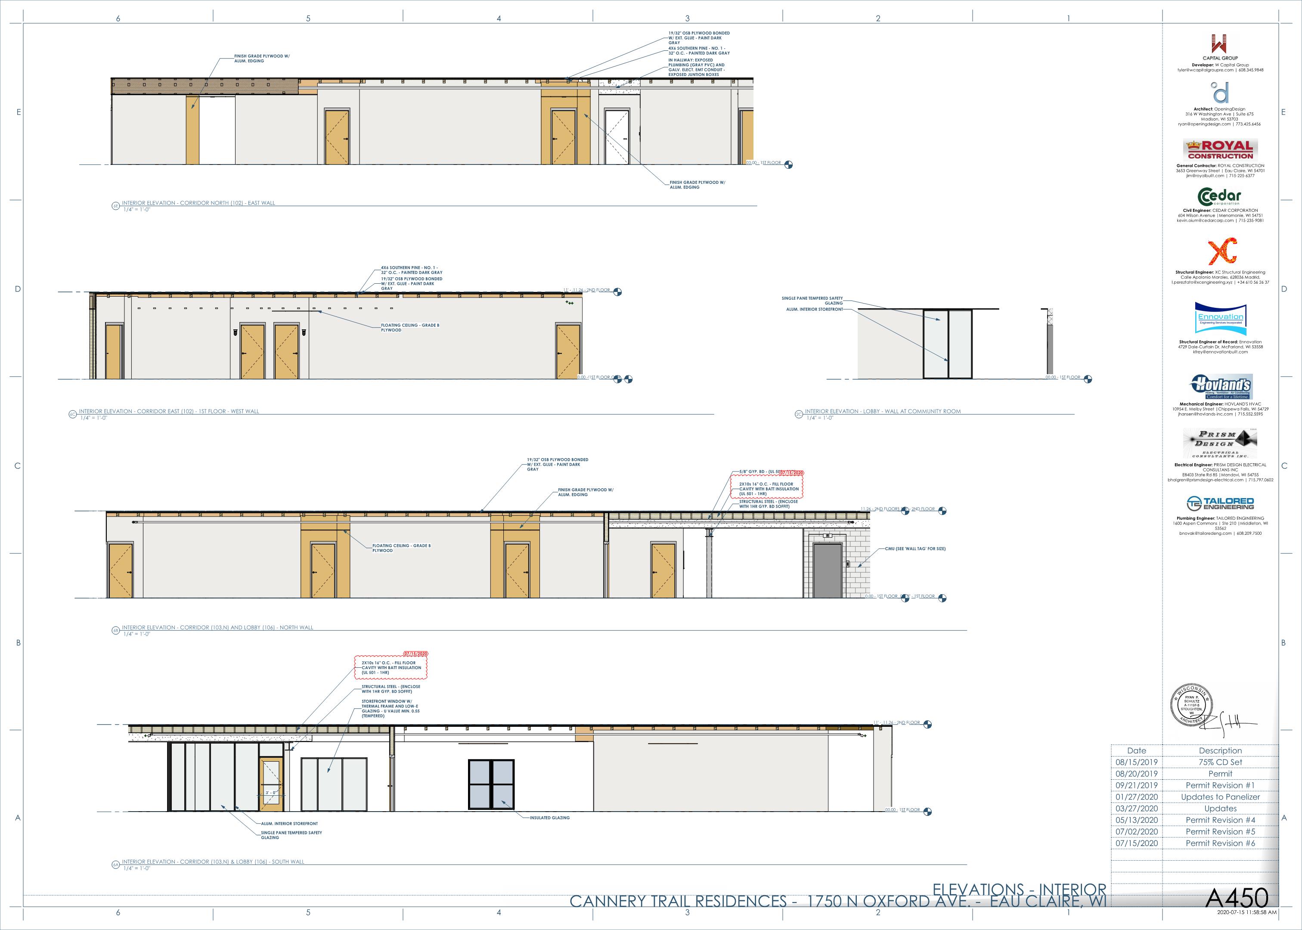
[picture p293: Most Current Set/Full size sheets/jpgs/048.jpg]

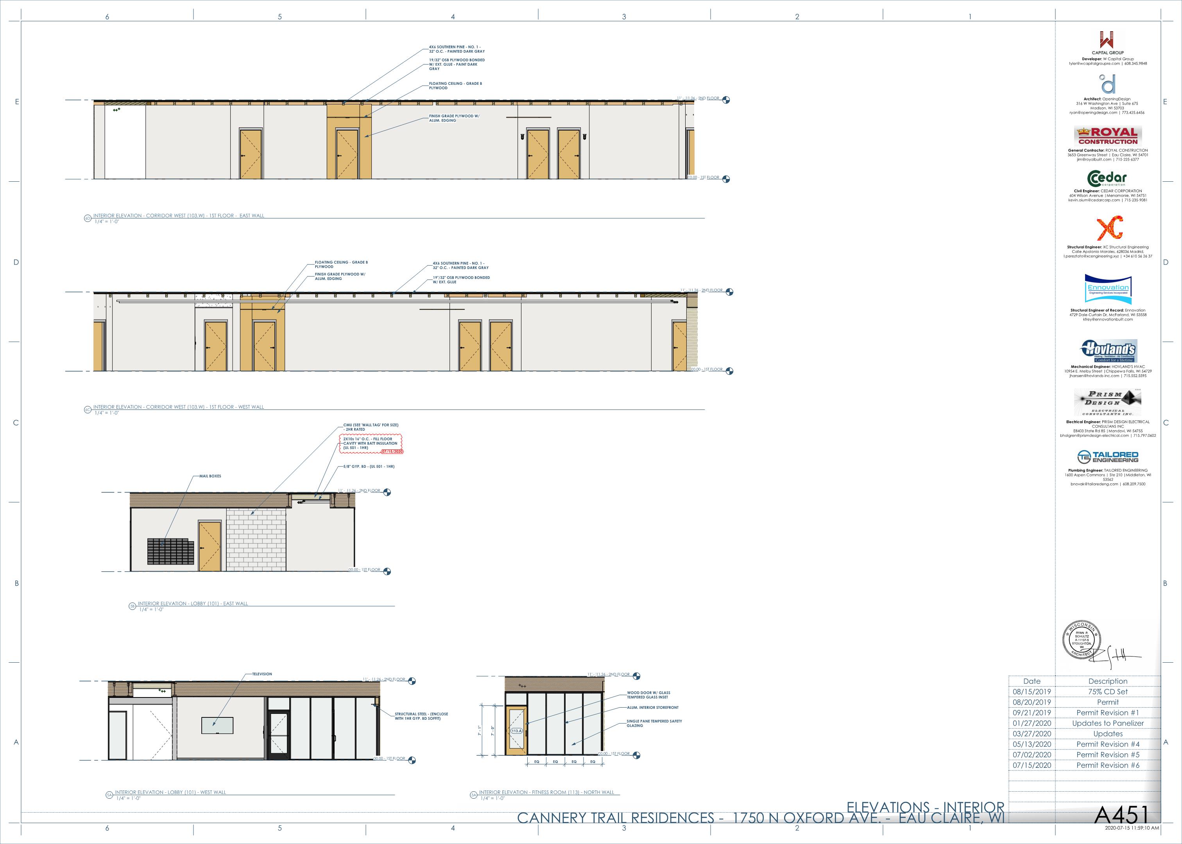
[picture p294: Most Current Set/Full size sheets/jpgs/049.jpg]

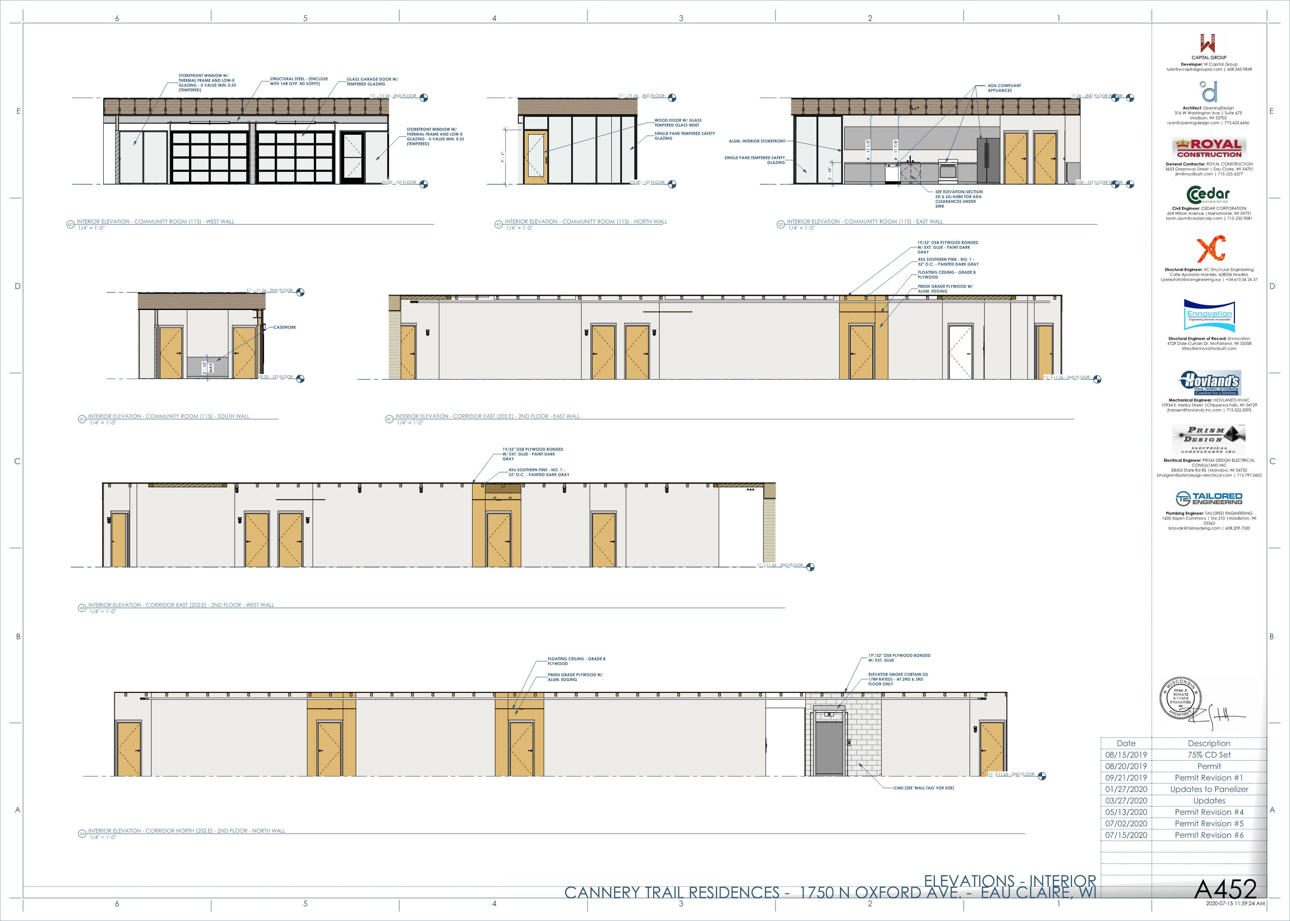
[picture p295: Most Current Set/Full size sheets/jpgs/050.jpg]

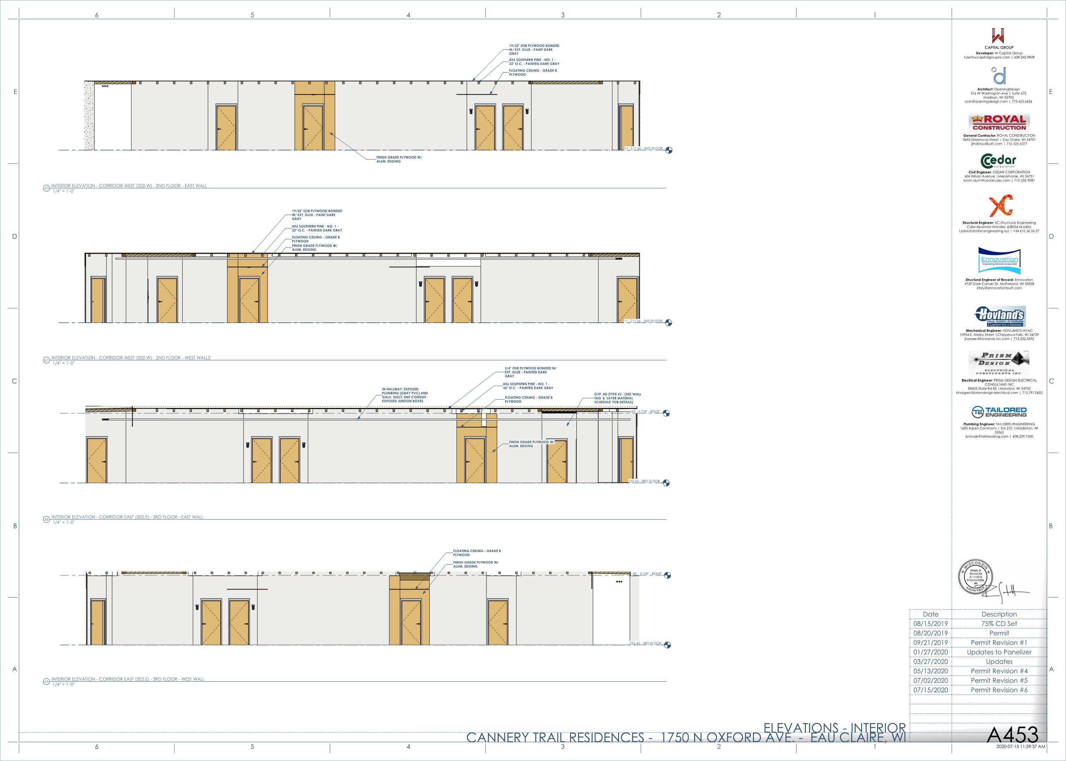
[picture p296: Most Current Set/Full size sheets/jpgs/051.jpg]

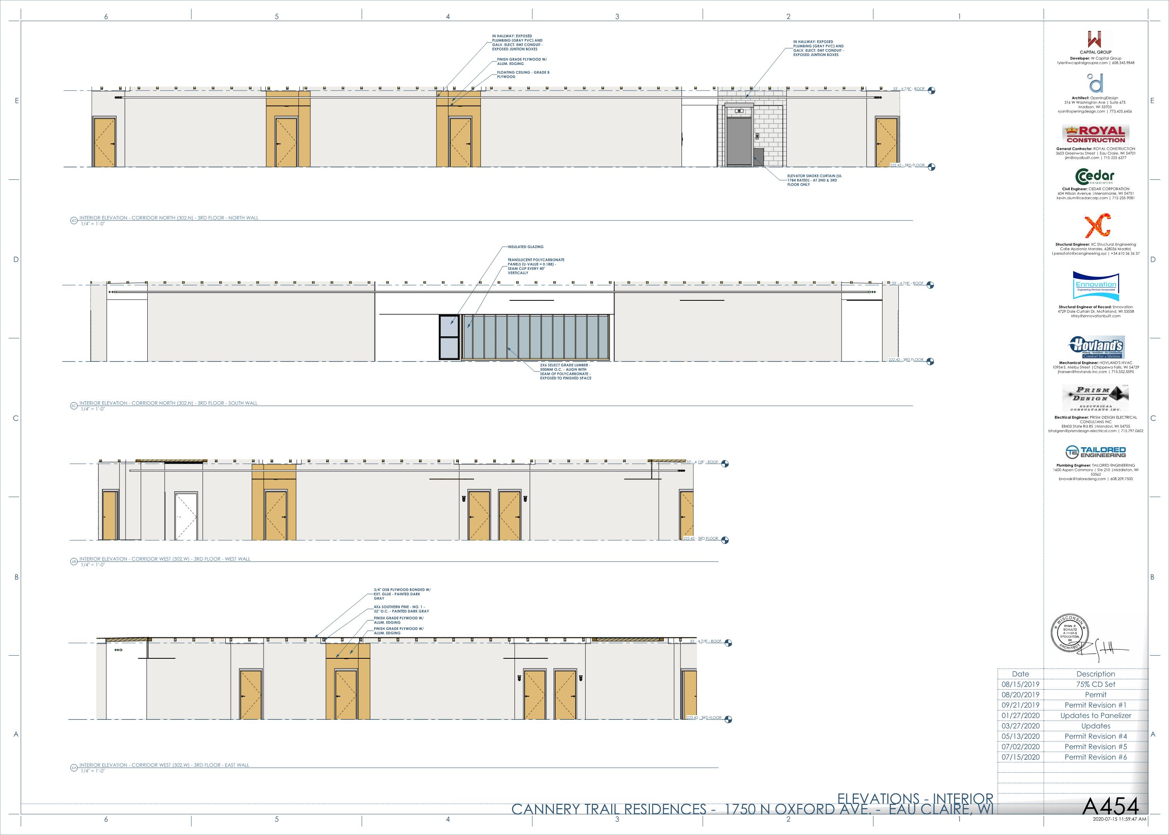
[picture p297: Most Current Set/Full size sheets/jpgs/052.jpg]

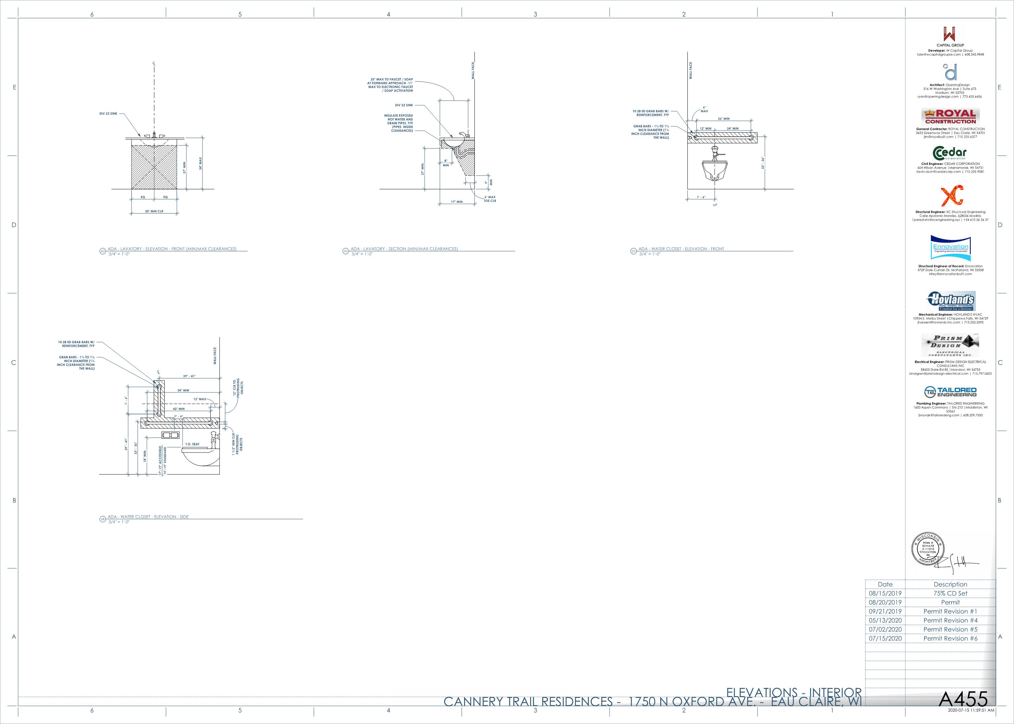
[picture p298: Most Current Set/Full size sheets/jpgs/053.jpg]

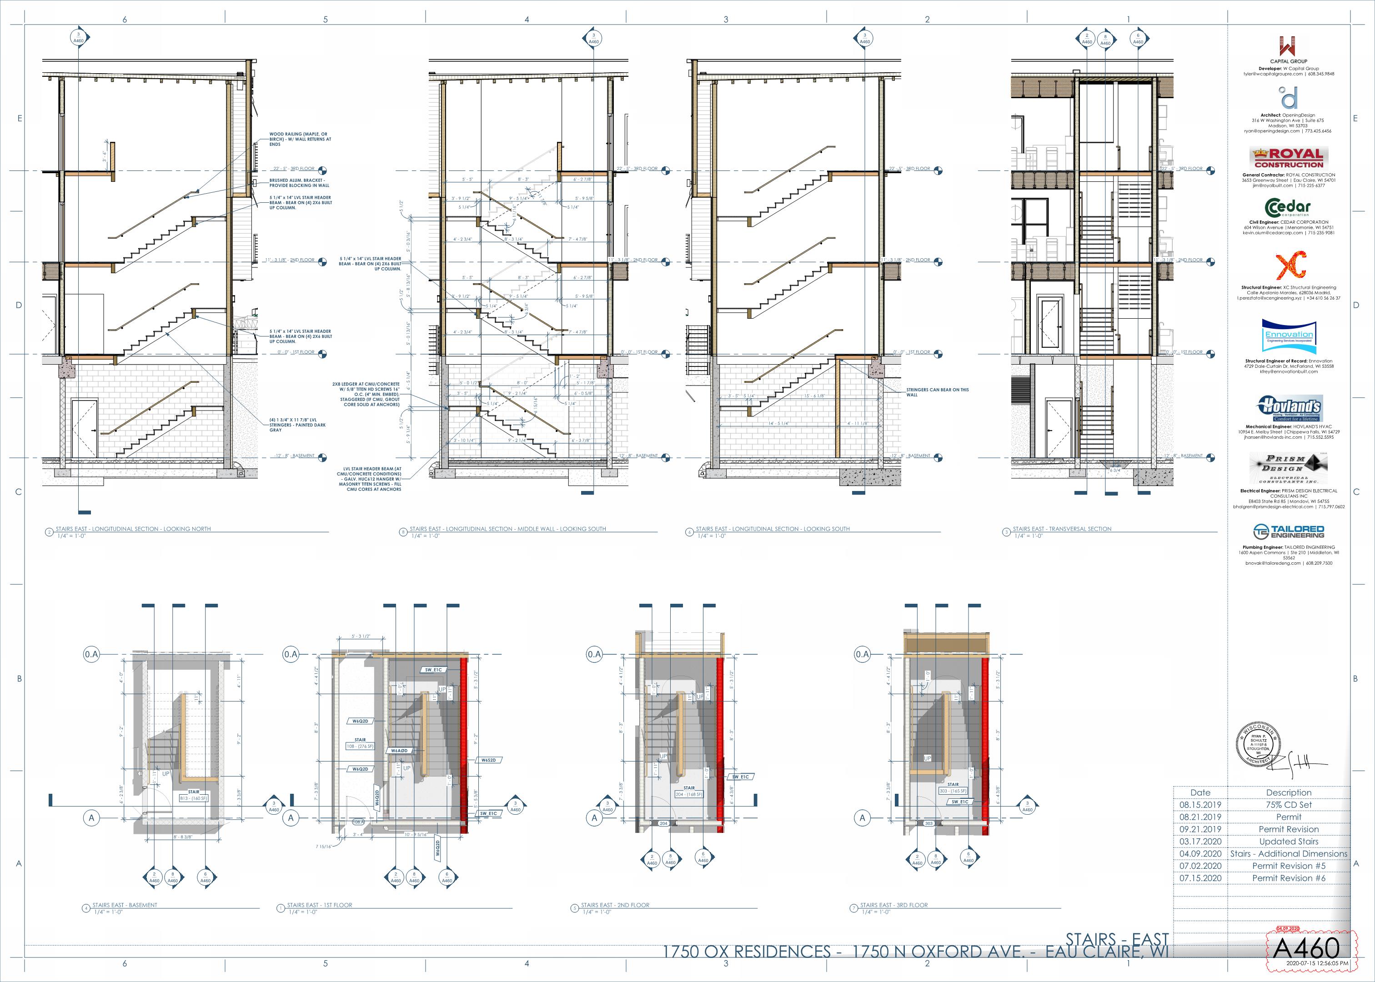
[picture p299: Most Current Set/Full size sheets/jpgs/054.jpg]

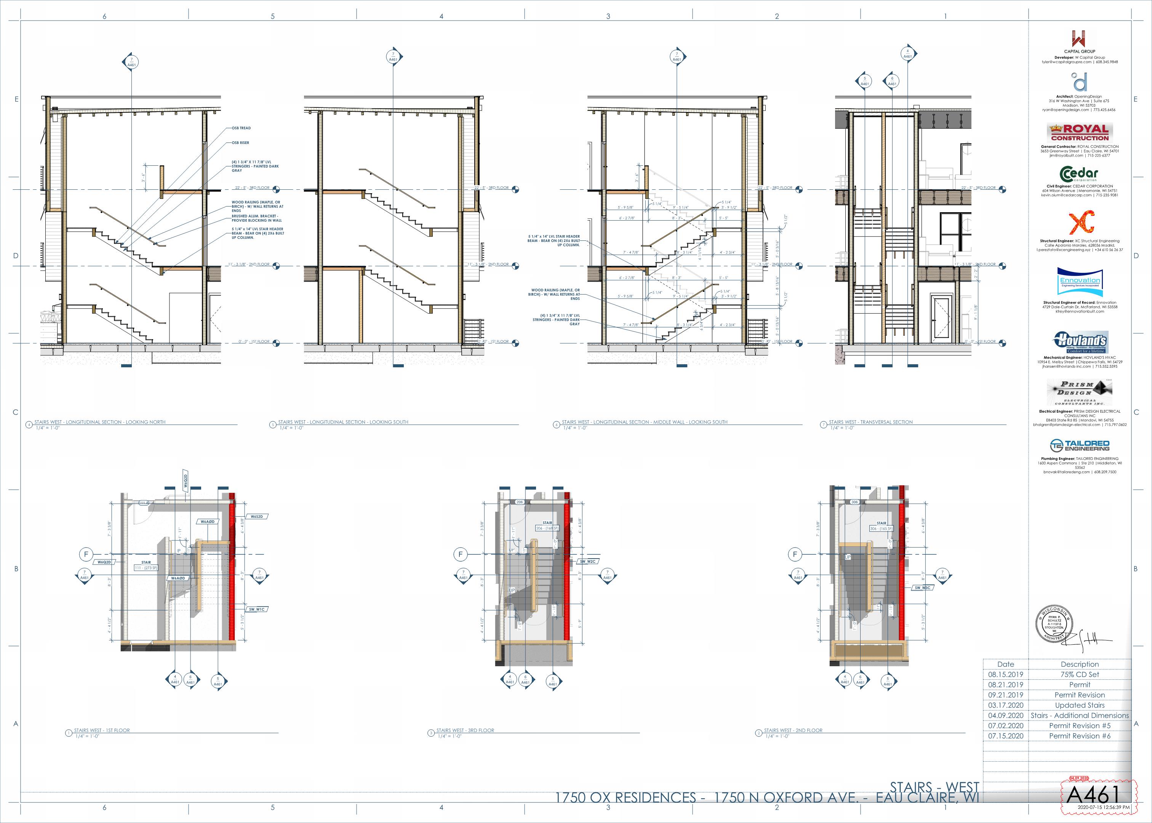
[picture p300: Most Current Set/Full size sheets/jpgs/055.jpg]

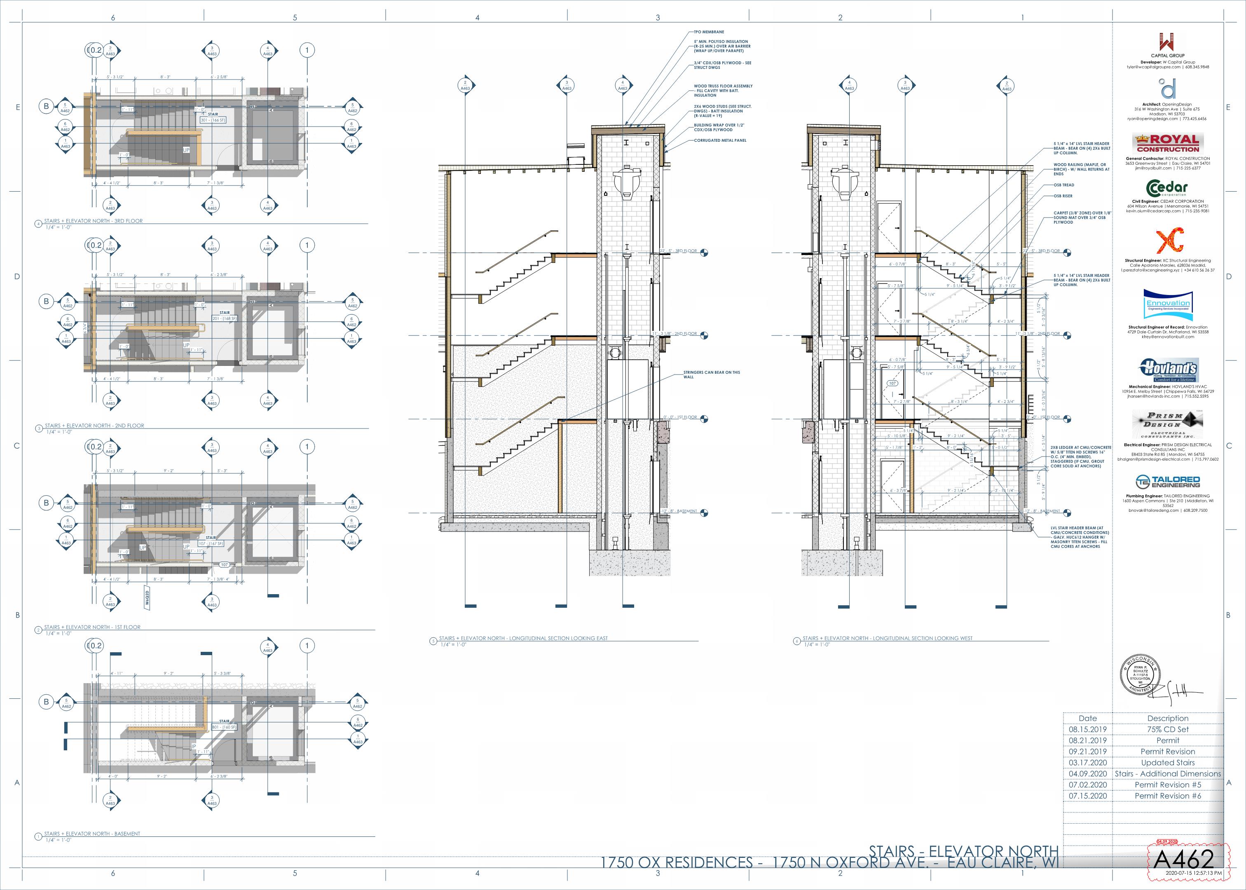
[picture p301: Most Current Set/Full size sheets/jpgs/056.jpg]

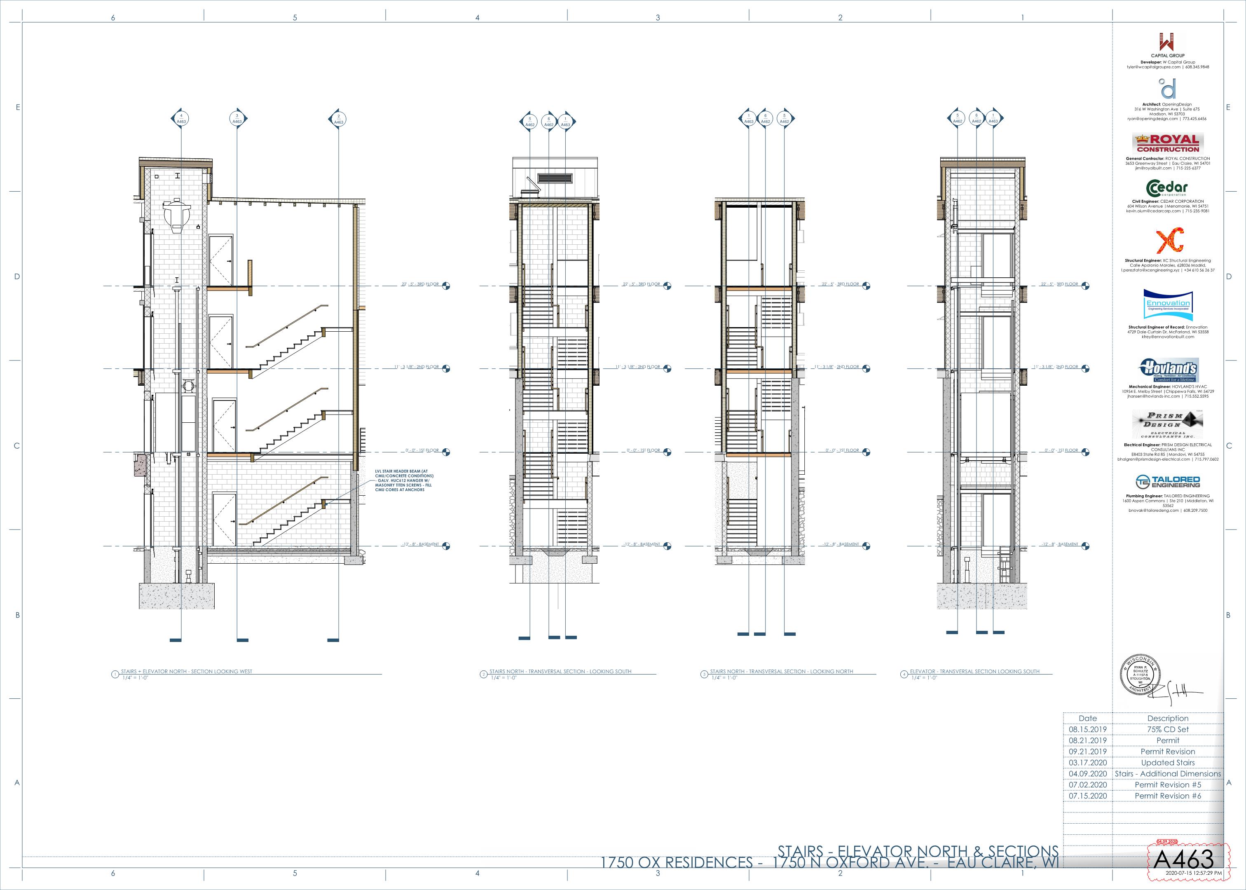
[picture p302: Most Current Set/Full size sheets/jpgs/057.jpg]

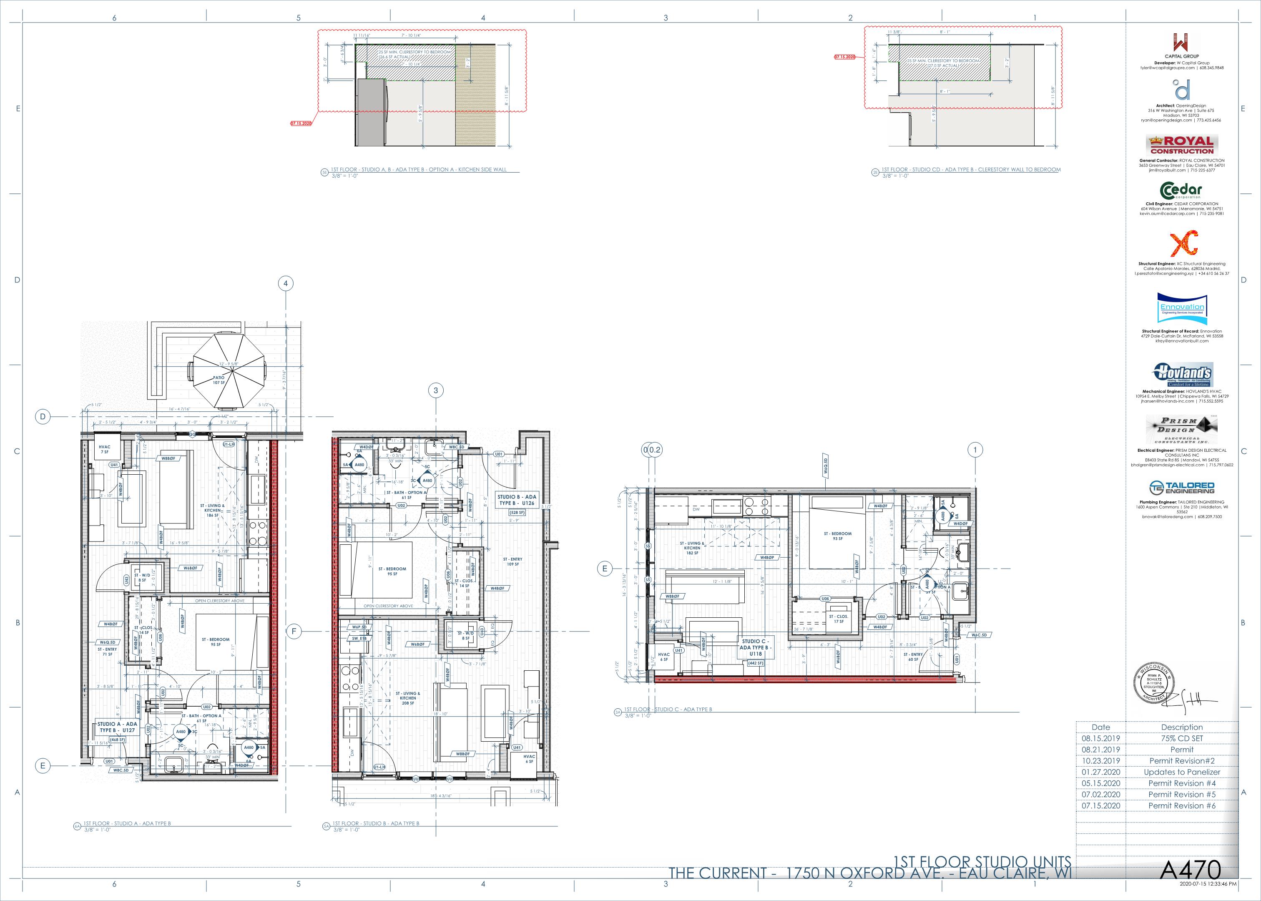
[picture p303: Most Current Set/Full size sheets/jpgs/058.jpg]

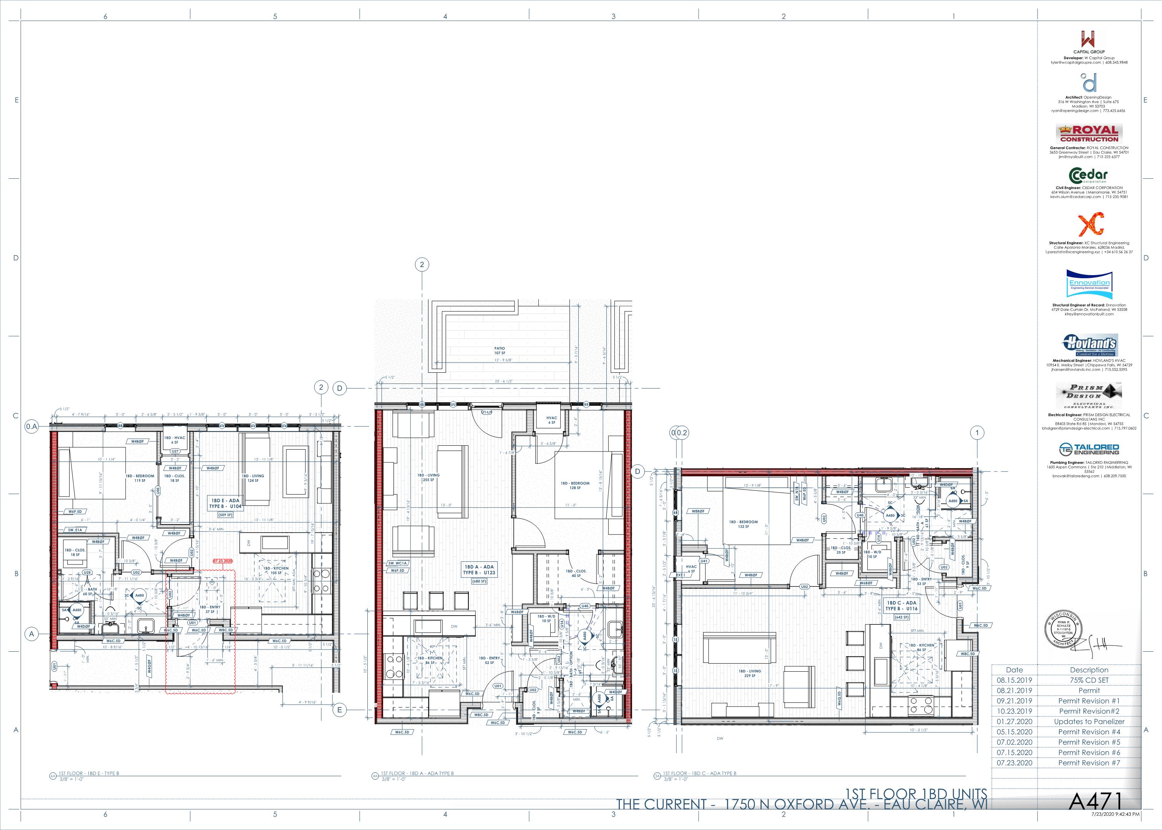
[picture p304: Most Current Set/Full size sheets/jpgs/059.jpg]

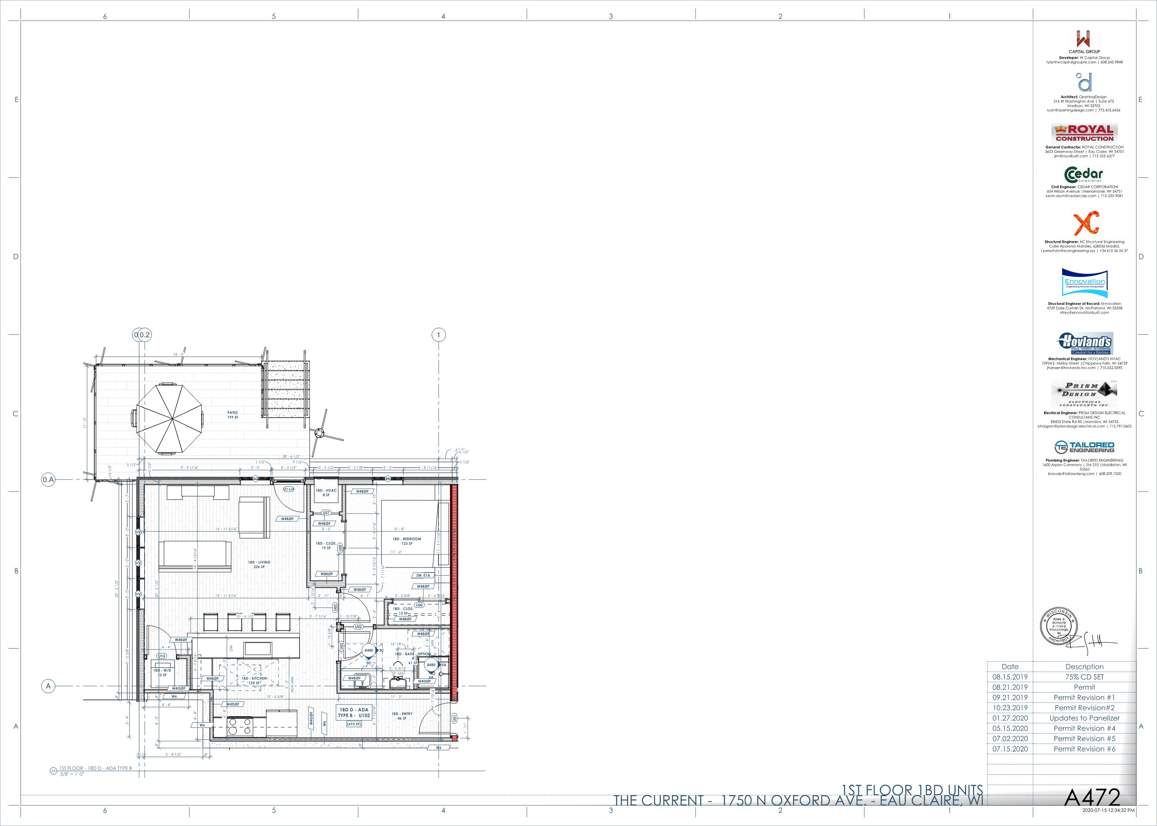
[picture p305: Most Current Set/Full size sheets/jpgs/060.jpg]

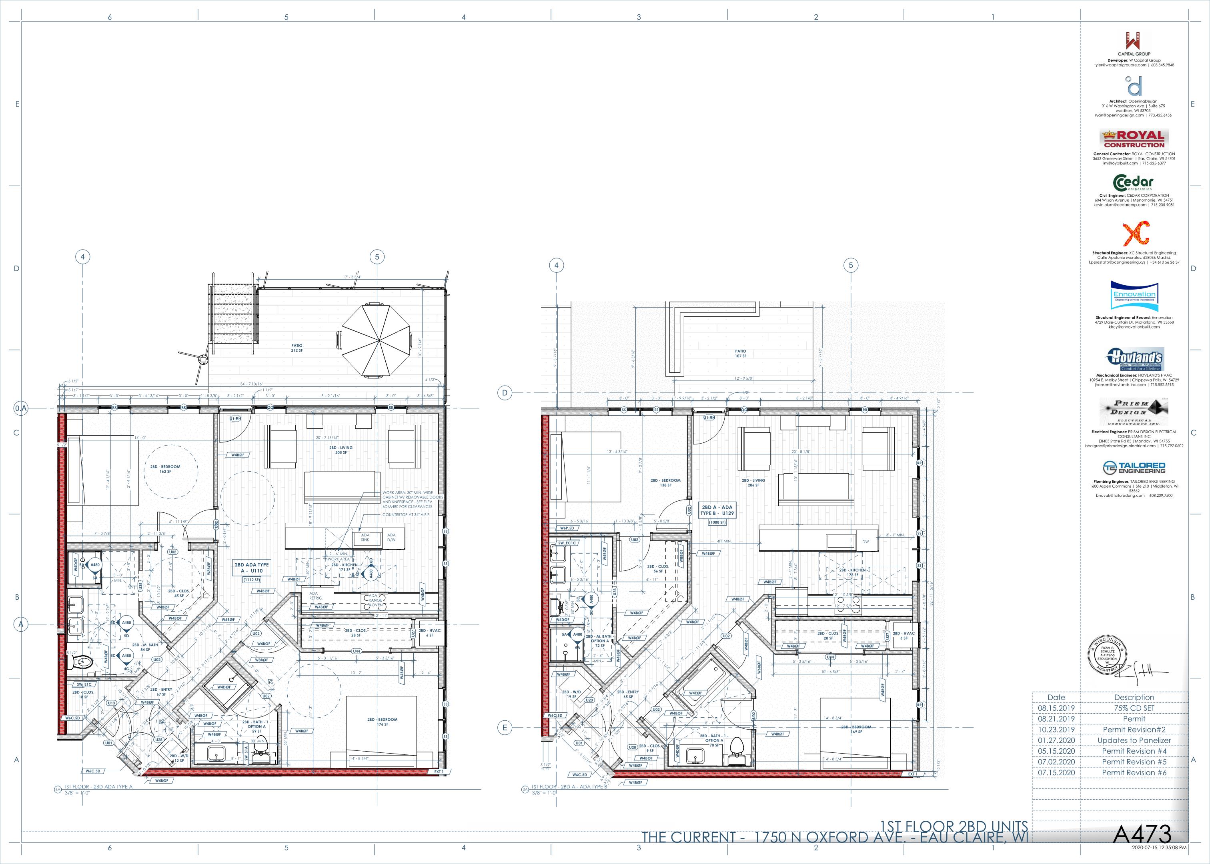
[picture p306: Most Current Set/Full size sheets/jpgs/061.jpg]
