OpeningDesign/CTR/Transfer/20200127 - from owner - room numbering/CTR1 Numbered Floor Plan.docx

1st Floor

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

2nd Floor

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

3rd Floor

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
