OpeningDesign/CTR/Transfer/20200617 - from STRUCT - estimated hours for permit revisions/20200617_oxapp_update_calculations_report.ods

Structural |  |  | Hours
 | 1 | Redesign of the foundation following precast change. | 7.50 | $562.50
 | 2 | Lintels on basement walls | 3.75 | $281.25
 | 3 | Stair towers structure modification | 5.50 | $412.50
 | 4 | Cantilevered corners modification | 6.75 | $506.25
 | 5 | Elevator well structure modification | 3.75 | $281.25
 | 6 | Steel structure on first floor (garage ramp, north facade and courtyard facade) | 8.50 | $637.50
 | 7 | Garage ramp RC walls. | 7.50 | $562.50
 | 8 | Corridor floor assembly composition | 3.00 | $225.00
 | 9 | Balconies connections. | 1.75 | $131.25
 |  |  | 48.00 | $3,600.00
 |  | Average Structural Billing Rate |  | $75.00
Architectural
 |  | Various items requested by the state after May 4th RFI letter (there was a lot of work to before the 4/21 submission, that technically could have been considered ‘additional services’ as well, but we have not included it here.) |  | $2,000.00
 |  | Total |  | $5,600.00
