OpeningDesign/CTR/XC_struct/xc_models/wood_structure/cantilevers/wood_cantilevers_design.ods

comb | floor | truss | Rx | Ry | Rz | Rx | Ry | Rz | truss | Rx | Ry | Rz | Rx | Ry | Rz
 |  | name | (kN) | (kN) | (kN) | (kN) | (kN) | (kN) | name | (kN) | (kN) | (kN) | (kN) | (kN) | (kN)
EQ1608 | roof | 3A | 0.00 | 0.00 | 1.07 | 0.00 | 0.00 | 1.08 | 3B | 0.00 | 0.00 | 1.06 | 0.00 | 0.00 | 1.07 | centerSpacing | 0.3048
EQ1609 | roof | 3A | 0.00 | 0.00 | 2.71 | 0.00 | 0.00 | 2.73 | 3B | 0.00 | 0.00 | 2.63 | 0.00 | 0.00 | 2.64
EQ1610 | roof | 3A | 0.00 | 0.00 | 4.51 | 0.00 | 0.00 | 4.52 | 3B | 0.00 | 0.00 | 4.35 | 0.00 | 0.00 | 4.37
EQ1611 | roof | 3A | 0.00 | 0.00 | 4.88 | 0.00 | 0.00 | 4.89 | 3B | 0.00 | 0.00 | 4.71 | 0.00 | 0.00 | 4.72
EQ1612 | roof | 3A | 0.00 | 0.00 | -0.23 | 0.00 | 0.00 | -0.22 | 3B | 0.00 | 0.00 | -0.19 | 0.00 | 0.00 | -0.18
EQ1613 | roof | 3A | 0.00 | 0.00 | 3.90 | 0.00 | 0.00 | 3.92 | 3B | 0.00 | 0.00 | 3.77 | 0.00 | 0.00 | 3.78
EQ1615 | roof | 3A | 0.00 | 0.00 | -0.66 | 0.00 | 0.00 | -0.65 | 3B | 0.00 | 0.00 | -0.62 | 0.00 | 0.00 | -0.61
EQ1608 | 2nd floor | 2A | 0.00 | 0.00 | 1.96 | 0.00 | 0.00 | 1.96 | 2B | 0.00 | 0.00 | 1.88 | 0.00 | 0.00 | 1.88
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
