OpeningDesign/CTR/XC_struct/xc_models/wood_structure/kurt_jack_trusses_proposal/loads_on_truss_girder.ods

Loads on girder truss
 |  | 0.22
Jack truss number | kN (uplift>0) | kips (uplift>0)
1 | 12.5 | 2.81
2 | 4.5 | 1.01
3 | 0.5 | 0.11
4 | 0.5 | 0.11
5 | 0.5 | 0.11
6 | 0.5 | 0.11
7 | 0.5 | 0.11
8 | 0.5 | 0.11
9 | 0.5 | 0.11
10 | 0.5 | 0.11
11 | 0.5 | 0.11
12 | 0.5 | 0.11
13 | 0.5 | 0.11
14 | 0.5 | 0.11
