OpeningDesign/CTR/XC_struct/xc_models/wood_structure/kurt_jack_trusses_proposal/loads_on_girder_truss.xlsx

Sheet: Sheet1
Loads on girder truss |  |  |  |  |  |  |  |  |  | 0.22
 |  | Dead load |  | Live load |  | Wind load |  | Snow load
 | ID | kN (uplift>0) | kips (uplift>0) | kN (uplift>0) | kips (uplift>0) | kN (uplift>0) | kips (uplift>0) | kN (uplift>0) | kips (uplift>0)
Jack truss number | 1 | 2.70 | 0.61 | -0.50 | -0.11 | 0.00 | 0.00 | 0.00 | 0.00
 | 2 | 2.70 | 0.61 | -0.50 | -0.11 | 0.00 | 0.00 | 0.00 | 0.00
 | 3 | 2.70 | 0.61 | -0.50 | -0.11 | 0.00 | 0.00 | 0.00 | 0.00
 | 4 | 2.70 | 0.61 | -0.50 | -0.11 | 0.00 | 0.00 | 0.00 | 0.00
 | 5 | 2.70 | 0.61 | -0.50 | -0.11 | 0.00 | 0.00 | 0.00 | 0.00
 | 6 | 2.70 | 0.61 | -0.50 | -0.11 | 0.00 | 0.00 | 0.00 | 0.00
 | 7 | 2.70 | 0.61 | -0.50 | -0.11 | 0.00 | 0.00 | 0.00 | 0.00
 | 8 | 2.70 | 0.61 | -0.50 | -0.11 | 0.00 | 0.00 | 0.00 | 0.00
 | 9 | 2.70 | 0.61 | -0.50 | -0.11 | 0.00 | 0.00 | 0.00 | 0.00
 | 10 | 2.70 | 0.61 | -0.50 | -0.11 | 0.00 | 0.00 | 0.00 | 0.00
 | 11 | 2.70 | 0.61 | -0.50 | -0.11 | 0.00 | 0.00 | 0.00 | 0.00
 | 12 | 2.70 | 0.61 | -0.50 | -0.11 | 0.00 | 0.00 | 0.00 | 0.00
 | 13 | 2.70 | 0.61 | -0.50 | -0.11 | 0.00 | 0.00 | 0.00 | 0.00
 | 14 | 2.70 | 0.61 | -0.50 | -0.11 | 0.00 | 0.00 | 0.00 | 0.00
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
