OpeningDesign/CTR/XC_struct/xc_models/wood_structure/joists/corridor_floor_fire_design/sheathing_fire_resistance.ods

Thickness |  | minutes | time assigned
in | mm |  | min/mm
19/32 | 15.08 | 15 | 0.99
3/4 | 19.05 | 19.15
1 | 25.4 | 25.54
1 1/8 | 28.58 | 28.73
 | 43.65625 |  | 1.71875
 | 45.24375 |  | 1.78125
