OpeningDesign/CTR/XC_struct/xc_models/wood_structure/steel_beams/courtyard_facade_steel_beams/courtyard_beam_splice_design_values.ods

Sheet: Sheet1
span | 8.31 | m | 27.25 | ft
x(M=0) | 2.08 | m | 6.84 | ft | 6 | 10.04
V(x=2.08m) | 185.00 | kN | 34.09 | ft | 34 | 1.04
 |  |  | 20.41 |  | 20 | 4.96
Mmax= | 100 | kN m | 73.76 | kip m
Vmax= | 185.00 | kN | 41.59 | kip
27 | 8.2296 | m
4.5 | 0.1143 | m
 | 8.3439 | m
27 | 8.2296 | m
3.5 | 0.0889 | m
 | 8.3185 | m
9 | 2.7432 | m
1.125 | 0.028575 | m
 | 2.771775 | m
4.16 | 13.65 |  | 13 | 7.77952755905512 | 7 | _

Sheet: Sheet2
pound2N | 4.45
foot2meter | 0.30
inch2meter | 0.03
