OpeningDesign/CTR/XC_struct/xc_models/wood_structure/stud_wall_design/bearing_wall_schedule_rev01.ods

BEARING WALL SCHEDULE
 |  | Stud dimensions | Spacing (in) | Top plates | Bottom plate | Truss spacing | Remarks
 |  | (in) | (in) |  |  | (in)
Facade | 1st floor | 2x6 | 16 | (2) 2x6” | 2x6” | 12/24
 | 2nd floor | 2x6 | 16 | (2) 2x6” | 2x6” | 12/24
 | 3rd floor | 2x6 | 19.2 | (2) 2x6” | 2x6” | 24
Interior | 1st floor | 2x6 | 12 | (2) 2x6” | 2x6” | 12/24
 | 2nd floor | 2x6 | 16 | (2) 2x6” | 2x6” | 24
 | 2nd floor | 2x6 | 12 | (2) 2x6” | 2x6” | 12 | S2A and S2B in the figure
 | 3rd floor | 2x6 | 16 | (2) 2x6” | 2x6” | 24
Materials:
 | Studs | SPRUCE-PIN-FIR (stud grade or better)
 | Plates | SPRUCE-PIN-FIR (#2 or better)
