OpeningDesign/CTR/XC_struct/xc_models/wood_structure/stud_wall_design/old/bearing_wall_schedule.ods

BEARING WALL SCHEDULE
 |  | Stud dimensions | Spacing (in) | Top plates | Bottom plate | Truss spacing | Remarks
 |  | (in) | (in) |  |  | (in)
Facade | 1st floor | 2x6 | 9.6 | (2) 2x6” | 2x6” | 12/24
 | 2nd floor | 2x6 | 9.6 | (2) 2x6” | 2x6” | 12/24
 | 3rd floor | 2x6 | 19.2 | (3) 2x6” | 2x6” | 24
Interior | 1st floor | 2x6 | 9.6 | (2) 2x6” | 2x6” | 12/24 | Rest of the bearing walls
 |  | 2x6 | 6.4 | (2) 2x6” | 2x6” | 12/24 | SW-S1A and SW-S1B
 | 2nd floor | 2x6 | 9.6 | (2) 2x6” | 2x6” | 12/24
 | 3rd floor | 2x6 | 19.2 | (3) 2x6” | 2x6” | 24
