OpeningDesign/CTR/XC_struct/xc_models/concrete_structure/old/XC3Dmodel/annex/text/report_resSimplLC.tex

\begin{figure}
\begin{center}

\caption{ULS01: 1.4*D. Columns, internal axial force [kN]}
\end{center}
\end{figure}
\begin{figure}
\begin{center}

\caption{ULS01: 1.4*D. Columns, bending moment about local axis y [m.kN]}
\end{center}
\end{figure}
\begin{figure}
\begin{center}

\caption{ULS01: 1.4*D. Columns, bending moment about local axis z [m.kN]}
\end{center}
\end{figure}
\begin{figure}
\begin{center}

\caption{ULS01: 1.4*D. Columns, internal shear force in local direction y [kN]}
\end{center}
\end{figure}
\begin{figure}
\begin{center}

\caption{ULS01: 1.4*D. Columns, internal shear force in local direction z [kN]}
\end{center}
\end{figure}
\clearpage
\begin{figure}
\begin{center}

\caption{ULS02_a: 1.2*D + 1.6*Lru + Lpu + 0.5*S. Columns, internal axial force [kN]}
\end{center}
\end{figure}
\begin{figure}
\begin{center}

\caption{ULS02_a: 1.2*D + 1.6*Lru + Lpu + 0.5*S. Columns, bending moment about local axis y [m.kN]}
\end{center}
\end{figure}
\begin{figure}
\begin{center}

\caption{ULS02_a: 1.2*D + 1.6*Lru + Lpu + 0.5*S. Columns, bending moment about local axis z [m.kN]}
\end{center}
\end{figure}
\begin{figure}
\begin{center}

\caption{ULS02_a: 1.2*D + 1.6*Lru + Lpu + 0.5*S. Columns, internal shear force in local direction y [kN]}
\end{center}
\end{figure}
\begin{figure}
\begin{center}

\caption{ULS02_a: 1.2*D + 1.6*Lru + Lpu + 0.5*S. Columns, internal shear force in local direction z [kN]}
\end{center}
\end{figure}
\clearpage
\begin{figure}
\begin{center}

\caption{ULS02_b: 1.2*D + 1.6*Lrs + Lps + 0.5*S. Columns, internal axial force [kN]}
\end{center}
\end{figure}
\begin{figure}
\begin{center}

\caption{ULS02_b: 1.2*D + 1.6*Lrs + Lps + 0.5*S. Columns, bending moment about local axis y [m.kN]}
\end{center}
\end{figure}
\begin{figure}
\begin{center}

\caption{ULS02_b: 1.2*D + 1.6*Lrs + Lps + 0.5*S. Columns, bending moment about local axis z [m.kN]}
\end{center}
\end{figure}
\begin{figure}
\begin{center}

\caption{ULS02_b: 1.2*D + 1.6*Lrs + Lps + 0.5*S. Columns, internal shear force in local direction y [kN]}
\end{center}
\end{figure}
\begin{figure}
\begin{center}

\caption{ULS02_b: 1.2*D + 1.6*Lrs + Lps + 0.5*S. Columns, internal shear force in local direction z [kN]}
\end{center}
\end{figure}
\clearpage
\begin{figure}
\begin{center}

\caption{ULS03_a: 1.2*D + 1.6*S + 0.5*Lru + Lpu. Columns, internal axial force [kN]}
\end{center}
\end{figure}
\begin{figure}
\begin{center}

\caption{ULS03_a: 1.2*D + 1.6*S + 0.5*Lru + Lpu. Columns, bending moment about local axis y [m.kN]}
\end{center}
\end{figure}
\begin{figure}
\begin{center}

\caption{ULS03_a: 1.2*D + 1.6*S + 0.5*Lru + Lpu. Columns, bending moment about local axis z [m.kN]}
\end{center}
\end{figure}
\begin{figure}
\begin{center}

\caption{ULS03_a: 1.2*D + 1.6*S + 0.5*Lru + Lpu. Columns, internal shear force in local direction y [kN]}
\end{center}
\end{figure}
\begin{figure}
\begin{center}

\caption{ULS03_a: 1.2*D + 1.6*S + 0.5*Lru + Lpu. Columns, internal shear force in local direction z [kN]}
\end{center}
\end{figure}
\clearpage
\begin{figure}
\begin{center}

\caption{ULS03_b: 1.2*D + 1.6*S + 0.5*Lrs + Lps. Columns, internal axial force [kN]}
\end{center}
\end{figure}
\begin{figure}
\begin{center}

\caption{ULS03_b: 1.2*D + 1.6*S + 0.5*Lrs + Lps. Columns, bending moment about local axis y [m.kN]}
\end{center}
\end{figure}
\begin{figure}
\begin{center}

\caption{ULS03_b: 1.2*D + 1.6*S + 0.5*Lrs + Lps. Columns, bending moment about local axis z [m.kN]}
\end{center}
\end{figure}
\begin{figure}
\begin{center}

\caption{ULS03_b: 1.2*D + 1.6*S + 0.5*Lrs + Lps. Columns, internal shear force in local direction y [kN]}
\end{center}
\end{figure}
\begin{figure}
\begin{center}

\caption{ULS03_b: 1.2*D + 1.6*S + 0.5*Lrs + Lps. Columns, internal shear force in local direction z [kN]}
\end{center}
\end{figure}
\clearpage
\begin{figure}
\begin{center}

\caption{ULS04_a: 1.2*D + 1.6*S + 0.5*W_WE. Columns, internal axial force [kN]}
\end{center}
\end{figure}
\begin{figure}
\begin{center}

\caption{ULS04_a: 1.2*D + 1.6*S + 0.5*W_WE. Columns, bending moment about local axis y [m.kN]}
\end{center}
\end{figure}
\begin{figure}
\begin{center}

\caption{ULS04_a: 1.2*D + 1.6*S + 0.5*W_WE. Columns, bending moment about local axis z [m.kN]}
\end{center}
\end{figure}
\begin{figure}
\begin{center}

\caption{ULS04_a: 1.2*D + 1.6*S + 0.5*W_WE. Columns, internal shear force in local direction y [kN]}
\end{center}
\end{figure}
\begin{figure}
\begin{center}

\caption{ULS04_a: 1.2*D + 1.6*S + 0.5*W_WE. Columns, internal shear force in local direction z [kN]}
\end{center}
\end{figure}
\clearpage
\begin{figure}
\begin{center}

\caption{ULS04_b: 1.2*D + 1.6*S + 0.5*W_NS. Columns, internal axial force [kN]}
\end{center}
\end{figure}
\begin{figure}
\begin{center}

\caption{ULS04_b: 1.2*D + 1.6*S + 0.5*W_NS. Columns, bending moment about local axis y [m.kN]}
\end{center}
\end{figure}
\begin{figure}
\begin{center}

\caption{ULS04_b: 1.2*D + 1.6*S + 0.5*W_NS. Columns, bending moment about local axis z [m.kN]}
\end{center}
\end{figure}
\begin{figure}
\begin{center}

\caption{ULS04_b: 1.2*D + 1.6*S + 0.5*W_NS. Columns, internal shear force in local direction y [kN]}
\end{center}
\end{figure}
\begin{figure}
\begin{center}

\caption{ULS04_b: 1.2*D + 1.6*S + 0.5*W_NS. Columns, internal shear force in local direction z [kN]}
\end{center}
\end{figure}
\clearpage
\begin{figure}
\begin{center}

\caption{ULS05_a: 1.2*D + W_WE + 0.5*Lru + Lpu. Columns, internal axial force [kN]}
\end{center}
\end{figure}
\begin{figure}
\begin{center}

\caption{ULS05_a: 1.2*D + W_WE + 0.5*Lru + Lpu. Columns, bending moment about local axis y [m.kN]}
\end{center}
\end{figure}
\begin{figure}
\begin{center}

\caption{ULS05_a: 1.2*D + W_WE + 0.5*Lru + Lpu. Columns, bending moment about local axis z [m.kN]}
\end{center}
\end{figure}
\begin{figure}
\begin{center}

\caption{ULS05_a: 1.2*D + W_WE + 0.5*Lru + Lpu. Columns, internal shear force in local direction y [kN]}
\end{center}
\end{figure}
\begin{figure}
\begin{center}

\caption{ULS05_a: 1.2*D + W_WE + 0.5*Lru + Lpu. Columns, internal shear force in local direction z [kN]}
\end{center}
\end{figure}
\clearpage
\begin{figure}
\begin{center}

\caption{ULS05_b: 1.2*D + W_NS + 0.5*Lru + Lpu. Columns, internal axial force [kN]}
\end{center}
\end{figure}
\begin{figure}
\begin{center}

\caption{ULS05_b: 1.2*D + W_NS + 0.5*Lru + Lpu. Columns, bending moment about local axis y [m.kN]}
\end{center}
\end{figure}
\begin{figure}
\begin{center}

\caption{ULS05_b: 1.2*D + W_NS + 0.5*Lru + Lpu. Columns, bending moment about local axis z [m.kN]}
\end{center}
\end{figure}
\begin{figure}
\begin{center}

\caption{ULS05_b: 1.2*D + W_NS + 0.5*Lru + Lpu. Columns, internal shear force in local direction y [kN]}
\end{center}
\end{figure}
\begin{figure}
\begin{center}

\caption{ULS05_b: 1.2*D + W_NS + 0.5*Lru + Lpu. Columns, internal shear force in local direction z [kN]}
\end{center}
\end{figure}
\clearpage
\begin{figure}
\begin{center}

\caption{ULS05_c: 1.2*D + W_WE + 0.5*Lrs + Lps. Columns, internal axial force [kN]}
\end{center}
\end{figure}
\begin{figure}
\begin{center}

\caption{ULS05_c: 1.2*D + W_WE + 0.5*Lrs + Lps. Columns, bending moment about local axis y [m.kN]}
\end{center}
\end{figure}
\begin{figure}
\begin{center}

\caption{ULS05_c: 1.2*D + W_WE + 0.5*Lrs + Lps. Columns, bending moment about local axis z [m.kN]}
\end{center}
\end{figure}
\begin{figure}
\begin{center}

\caption{ULS05_c: 1.2*D + W_WE + 0.5*Lrs + Lps. Columns, internal shear force in local direction y [kN]}
\end{center}
\end{figure}
\begin{figure}
\begin{center}

\caption{ULS05_c: 1.2*D + W_WE + 0.5*Lrs + Lps. Columns, internal shear force in local direction z [kN]}
\end{center}
\end{figure}
\clearpage
\begin{figure}
\begin{center}

\caption{ULS05_d: 1.2*D + W_NS + 0.5*Lrs + Lps. Columns, internal axial force [kN]}
\end{center}
\end{figure}
\begin{figure}
\begin{center}

\caption{ULS05_d: 1.2*D + W_NS + 0.5*Lrs + Lps. Columns, bending moment about local axis y [m.kN]}
\end{center}
\end{figure}
\begin{figure}
\begin{center}

\caption{ULS05_d: 1.2*D + W_NS + 0.5*Lrs + Lps. Columns, bending moment about local axis z [m.kN]}
\end{center}
\end{figure}
\begin{figure}
\begin{center}

\caption{ULS05_d: 1.2*D + W_NS + 0.5*Lrs + Lps. Columns, internal shear force in local direction y [kN]}
\end{center}
\end{figure}
\begin{figure}
\begin{center}

\caption{ULS05_d: 1.2*D + W_NS + 0.5*Lrs + Lps. Columns, internal shear force in local direction z [kN]}
\end{center}
\end{figure}
\clearpage
\begin{figure}
\begin{center}

\caption{ULS06_a: 1.2*D + 0.5*Lru + Lpu + 0.2*S. Columns, internal axial force [kN]}
\end{center}
\end{figure}
\begin{figure}
\begin{center}

\caption{ULS06_a: 1.2*D + 0.5*Lru + Lpu + 0.2*S. Columns, bending moment about local axis y [m.kN]}
\end{center}
\end{figure}
\begin{figure}
\begin{center}

\caption{ULS06_a: 1.2*D + 0.5*Lru + Lpu + 0.2*S. Columns, bending moment about local axis z [m.kN]}
\end{center}
\end{figure}
\begin{figure}
\begin{center}

\caption{ULS06_a: 1.2*D + 0.5*Lru + Lpu + 0.2*S. Columns, internal shear force in local direction y [kN]}
\end{center}
\end{figure}
\begin{figure}
\begin{center}

\caption{ULS06_a: 1.2*D + 0.5*Lru + Lpu + 0.2*S. Columns, internal shear force in local direction z [kN]}
\end{center}
\end{figure}
\clearpage
\begin{figure}
\begin{center}

\caption{ULS06_b: 1.2*D + 0.5*Lrs + Lps + 0.2*S. Columns, internal axial force [kN]}
\end{center}
\end{figure}
\begin{figure}
\begin{center}

\caption{ULS06_b: 1.2*D + 0.5*Lrs + Lps + 0.2*S. Columns, bending moment about local axis y [m.kN]}
\end{center}
\end{figure}
\begin{figure}
\begin{center}

\caption{ULS06_b: 1.2*D + 0.5*Lrs + Lps + 0.2*S. Columns, bending moment about local axis z [m.kN]}
\end{center}
\end{figure}
\begin{figure}
\begin{center}

\caption{ULS06_b: 1.2*D + 0.5*Lrs + Lps + 0.2*S. Columns, internal shear force in local direction y [kN]}
\end{center}
\end{figure}
\begin{figure}
\begin{center}

\caption{ULS06_b: 1.2*D + 0.5*Lrs + Lps + 0.2*S. Columns, internal shear force in local direction z [kN]}
\end{center}
\end{figure}
\clearpage
\begin{figure}
\begin{center}

\caption{ULS07_a: 0.9*D + W_WE. Columns, internal axial force [kN]}
\end{center}
\end{figure}
\begin{figure}
\begin{center}

\caption{ULS07_a: 0.9*D + W_WE. Columns, bending moment about local axis y [m.kN]}
\end{center}
\end{figure}
\begin{figure}
\begin{center}

\caption{ULS07_a: 0.9*D + W_WE. Columns, bending moment about local axis z [m.kN]}
\end{center}
\end{figure}
\begin{figure}
\begin{center}

\caption{ULS07_a: 0.9*D + W_WE. Columns, internal shear force in local direction y [kN]}
\end{center}
\end{figure}
\begin{figure}
\begin{center}

\caption{ULS07_a: 0.9*D + W_WE. Columns, internal shear force in local direction z [kN]}
\end{center}
\end{figure}
\clearpage
\begin{figure}
\begin{center}

\caption{ULS07_b: 0.9*D + W_NS. Columns, internal axial force [kN]}
\end{center}
\end{figure}
\begin{figure}
\begin{center}

\caption{ULS07_b: 0.9*D + W_NS. Columns, bending moment about local axis y [m.kN]}
\end{center}
\end{figure}
\begin{figure}
\begin{center}

\caption{ULS07_b: 0.9*D + W_NS. Columns, bending moment about local axis z [m.kN]}
\end{center}
\end{figure}
\begin{figure}
\begin{center}

\caption{ULS07_b: 0.9*D + W_NS. Columns, internal shear force in local direction y [kN]}
\end{center}
\end{figure}
\begin{figure}
\begin{center}

\caption{ULS07_b: 0.9*D + W_NS. Columns, internal shear force in local direction z [kN]}
\end{center}
\end{figure}
\clearpage
