OpeningDesign/CTR/CA/Site Reports and Photos/20200515/13.03.01.jpg

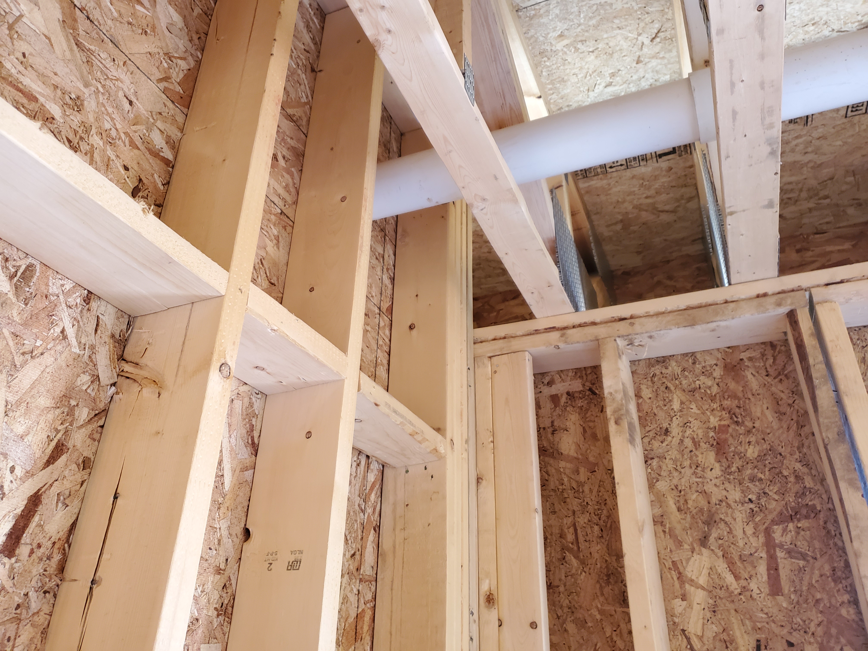
CA/Site Reports and Photos/20200515/13.03.01.jpg
