OpeningDesign/CTR/CA/Site Reports and Photos/20200515/13.20.18.jpg

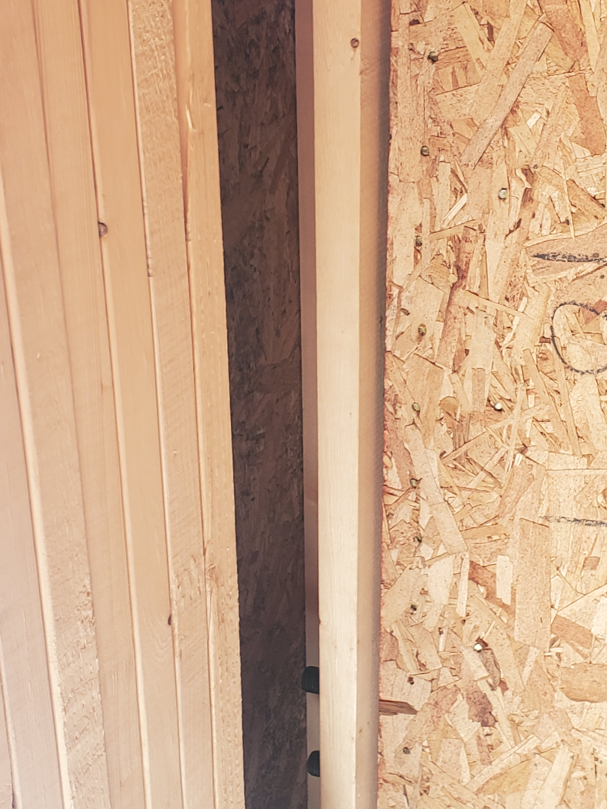
CA/Site Reports and Photos/20200515/13.20.18.jpg
