OpeningDesign/CTR/CA/Site Reports and Photos/20200515/14.42.18.jpg

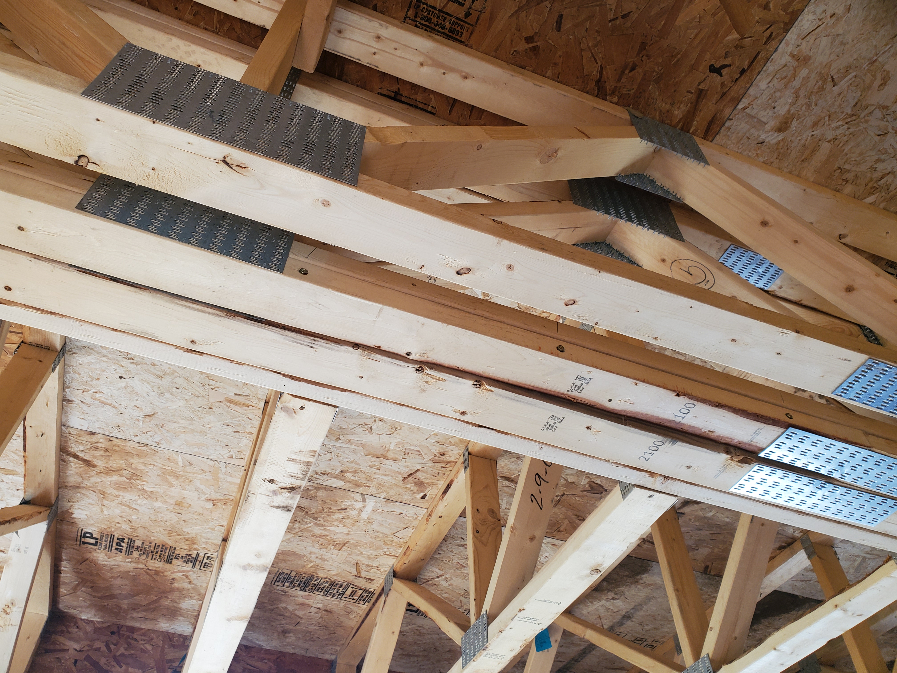
CA/Site Reports and Photos/20200515/14.42.18.jpg
