OpeningDesign/CTR/CA/Site Reports and Photos/20200515/Revu_bmbJe7giKS.png

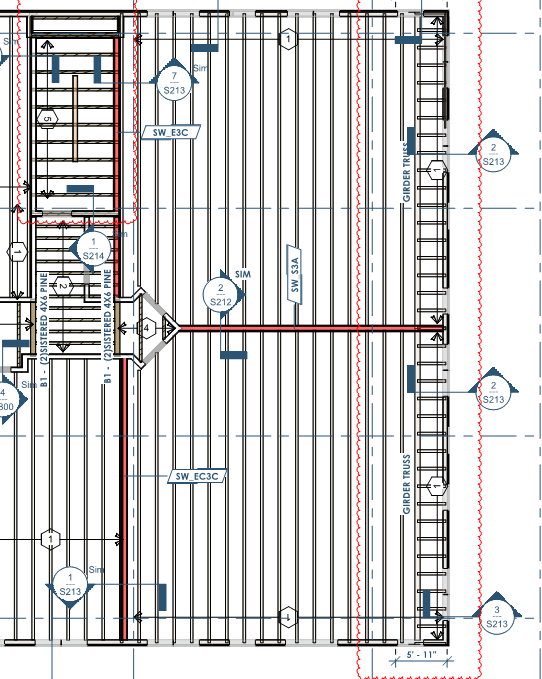
CA/Site Reports and Photos/20200515/Revu_bmbJe7giKS.png
