OpeningDesign/CTR/CA/Site Reports and Photos/20200515/Revu_uci1Lh8G25.png

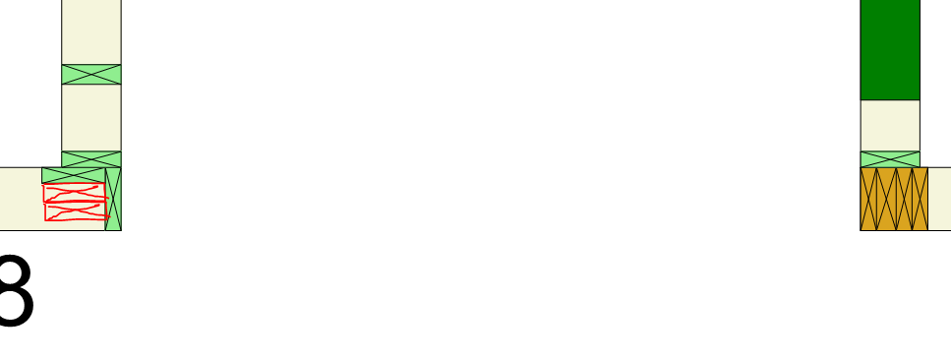
CA/Site Reports and Photos/20200515/Revu_uci1Lh8G25.png
