OpeningDesign/CTR/CA/Site Reports and Photos/20200915/2020-09-15 09.50.14.jpg

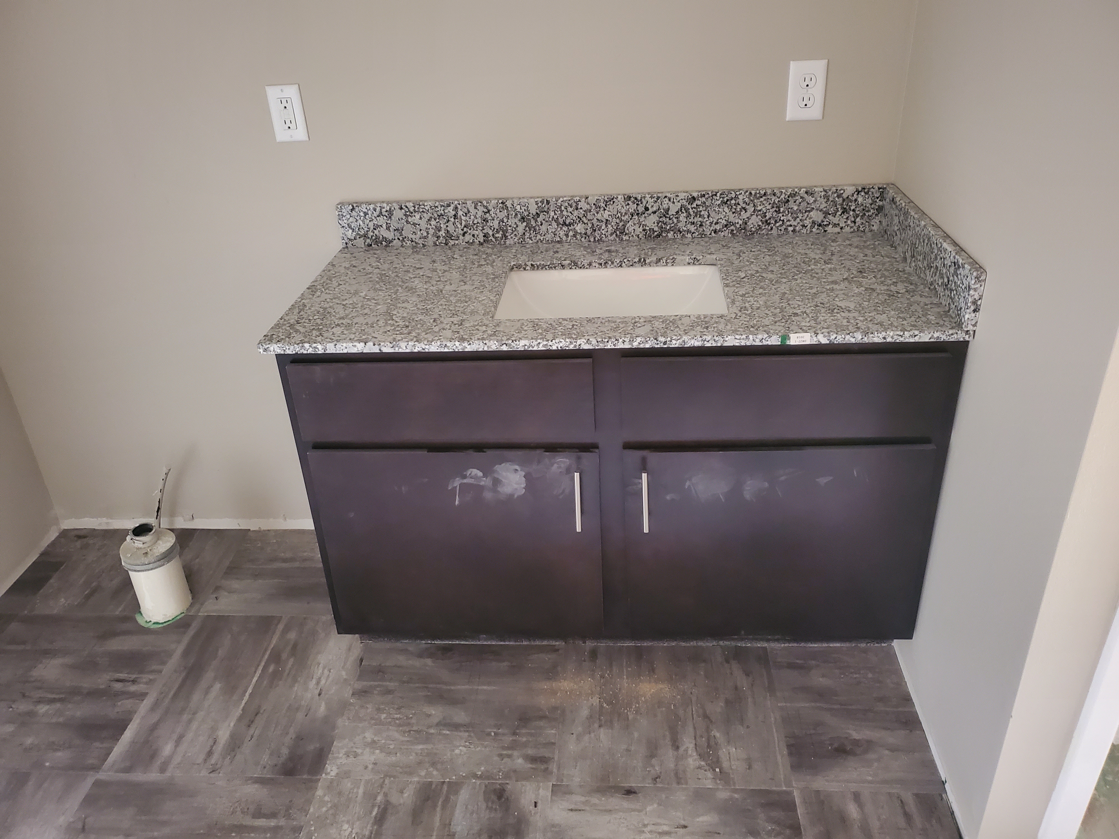
CA/Site Reports and Photos/20200915/2020-09-15 09.50.14.jpg
