OpeningDesign/CTR/CA/Site Reports and Photos/20200915/2020-09-15 11.01.18.jpg

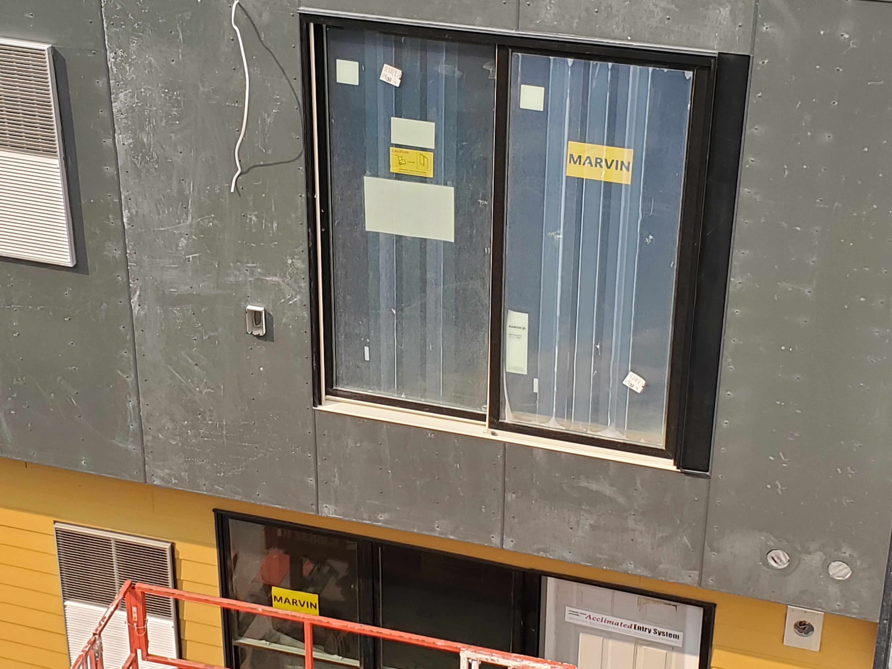
CA/Site Reports and Photos/20200915/2020-09-15 11.01.18.jpg
