OpeningDesign/CTR/CA/Site Reports and Photos/20201221/2020-12-21 12.20.01.jpg

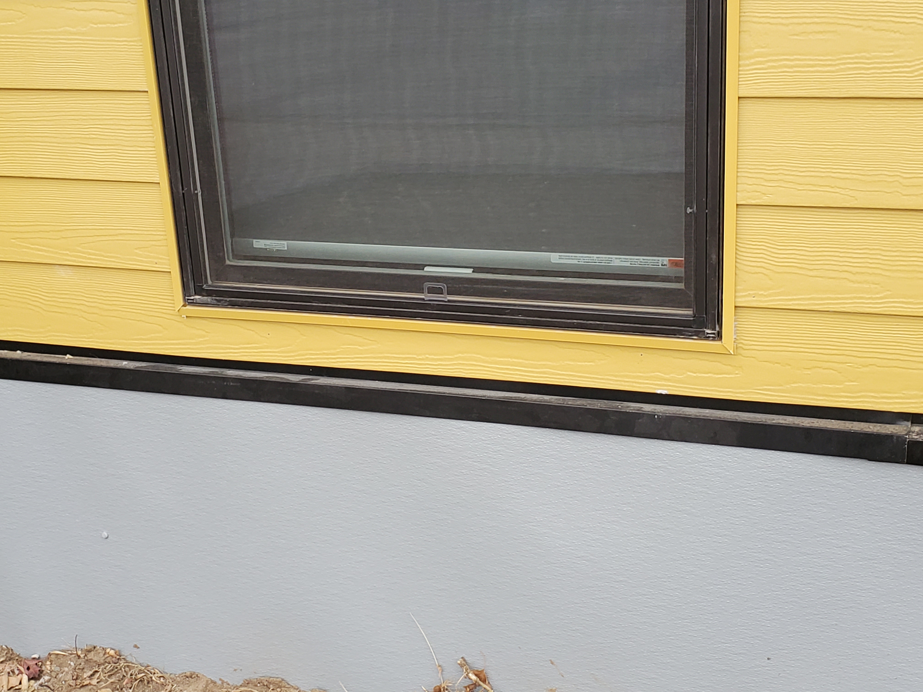
CA/Site Reports and Photos/20201221/2020-12-21 12.20.01.jpg
