OpeningDesign/CTR/CA/Site Reports and Photos/20201221/2020-12-21 13.04.47.jpg

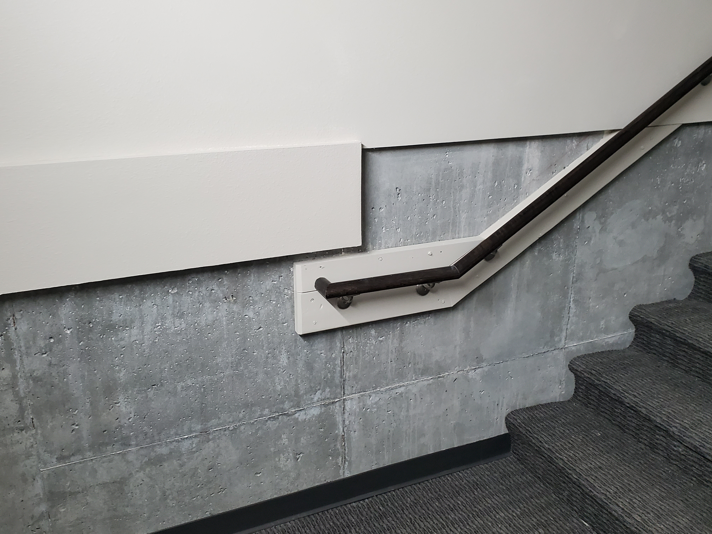
CA/Site Reports and Photos/20201221/2020-12-21 13.04.47.jpg
