OpeningDesign/CTR/CA/Site Reports and Photos/20201221/2020-12-21 13.48.09.jpg

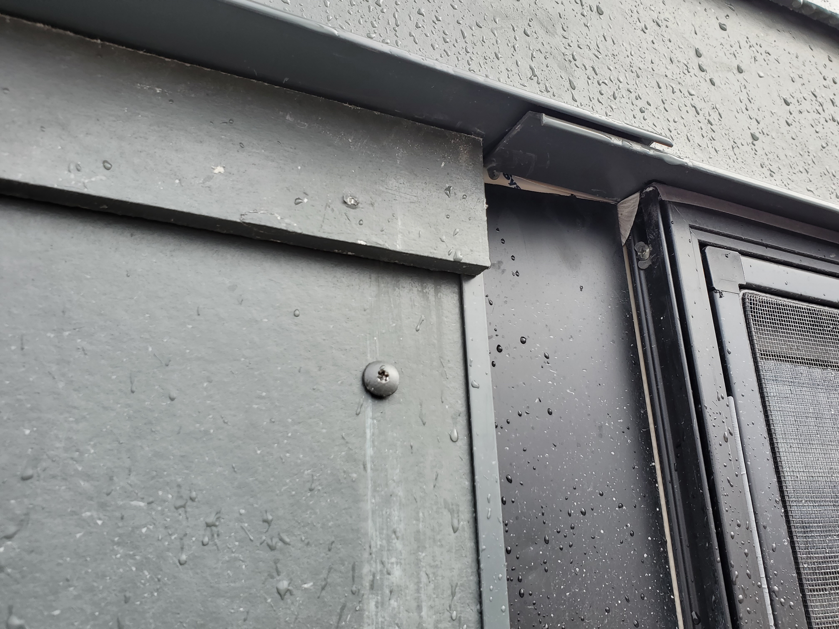
CA/Site Reports and Photos/20201221/2020-12-21 13.48.09.jpg
