OpeningDesign/CTR/CA/Site Reports and Photos/20201221/2020-12-21 13.49.53.jpg

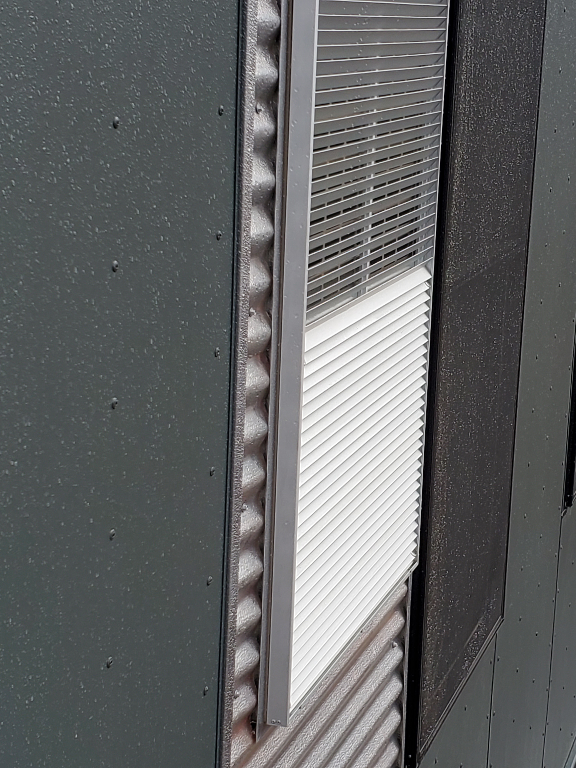
CA/Site Reports and Photos/20201221/2020-12-21 13.49.53.jpg
