OpeningDesign/CTR/CA/Site Reports and Photos/20201221/2020-12-21 13.51.48.jpg

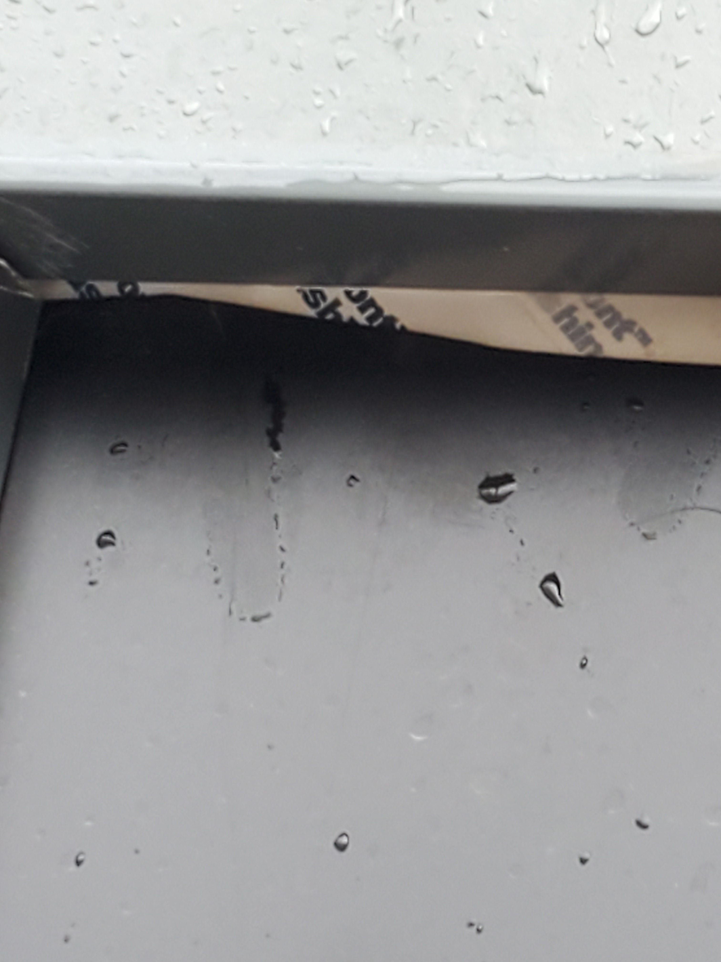
CA/Site Reports and Photos/20201221/2020-12-21 13.51.48.jpg
