OpeningDesign/CTR/CA/Site Reports and Photos/20201221/2020-12-21 14.37.02.jpg

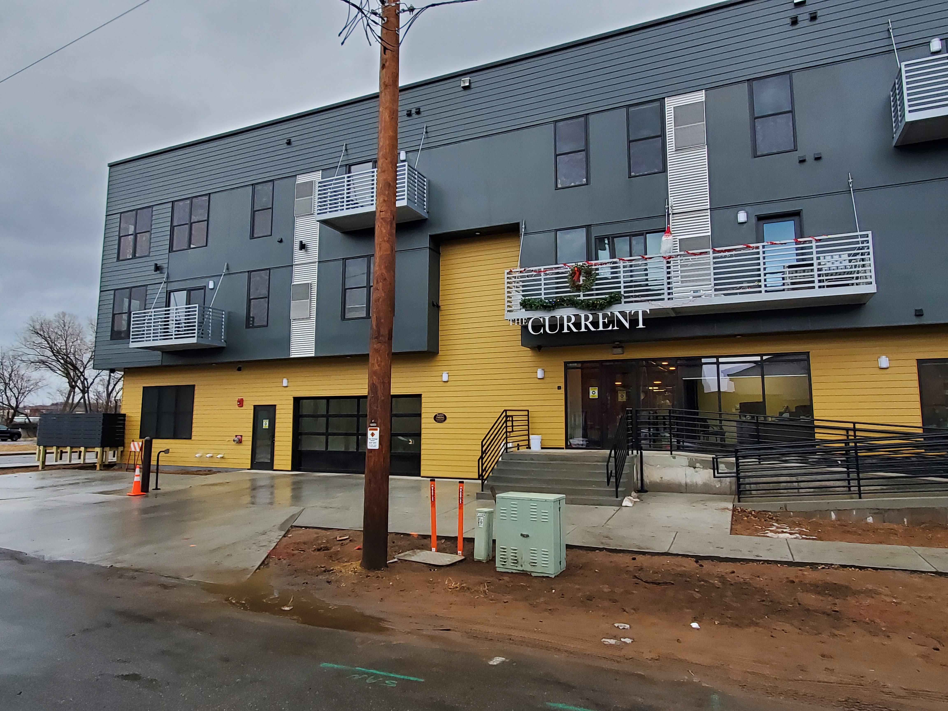
CA/Site Reports and Photos/20201221/2020-12-21 14.37.02.jpg
