OpeningDesign/CTR/CA/Site Reports and Photos/20201221/2020-12-21 14.38.17.jpg

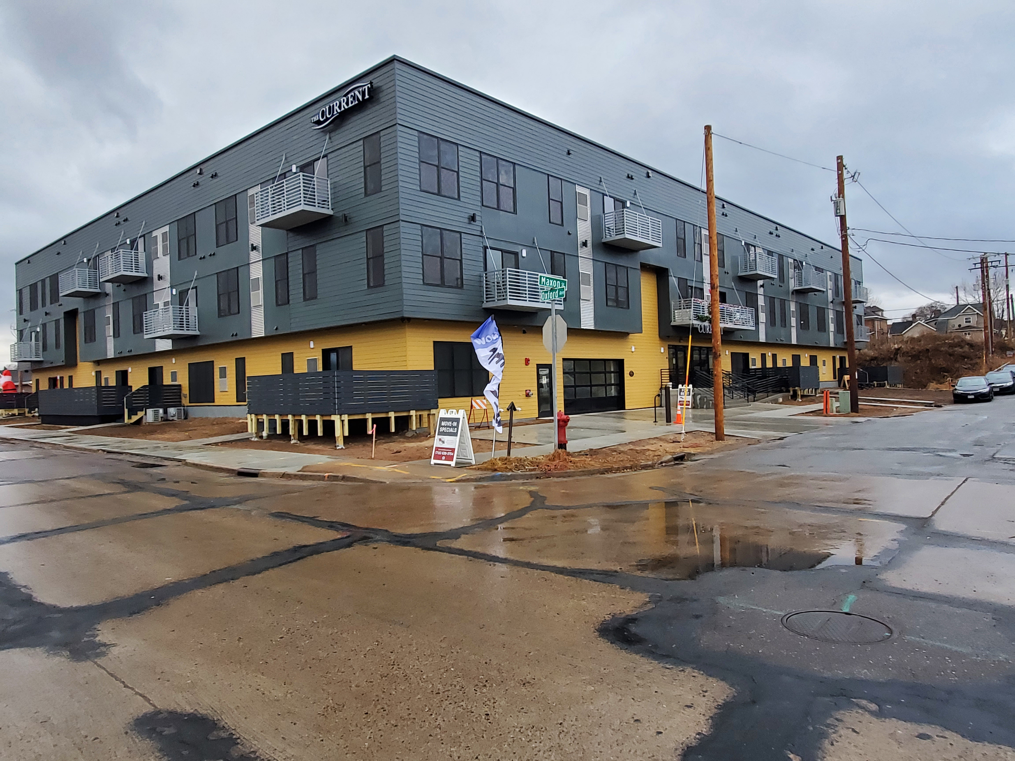
CA/Site Reports and Photos/20201221/2020-12-21 14.38.17.jpg
