OpeningDesign/CTR/CA/Site Reports and Photos/20201221/2020-12-21 14.40.38.jpg

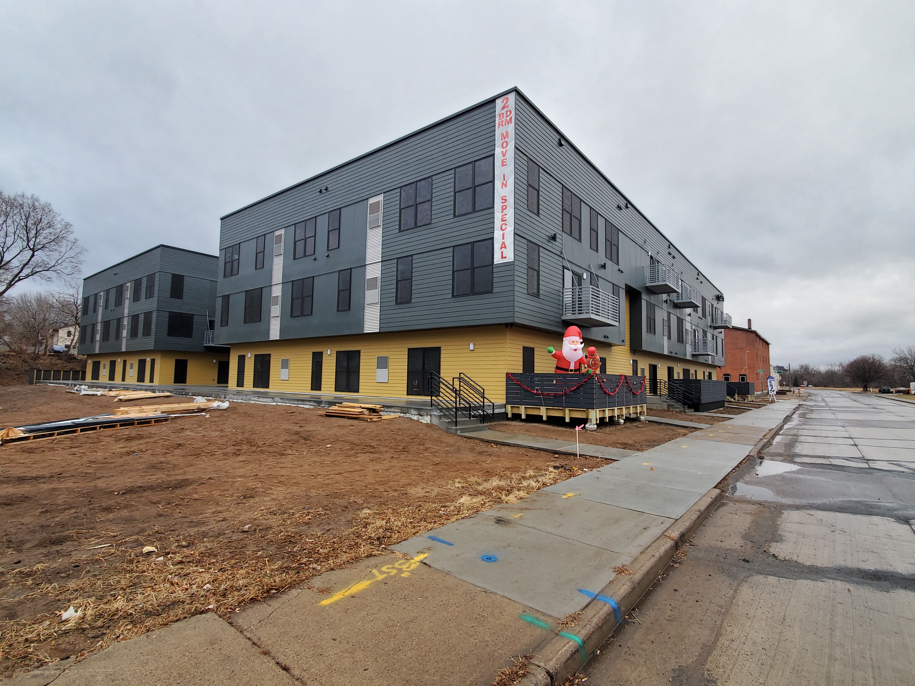
CA/Site Reports and Photos/20201221/2020-12-21 14.40.38.jpg
