OpeningDesign/CTR/CA/Site Reports and Photos/20201221/2020-12-21 14.42.26.jpg

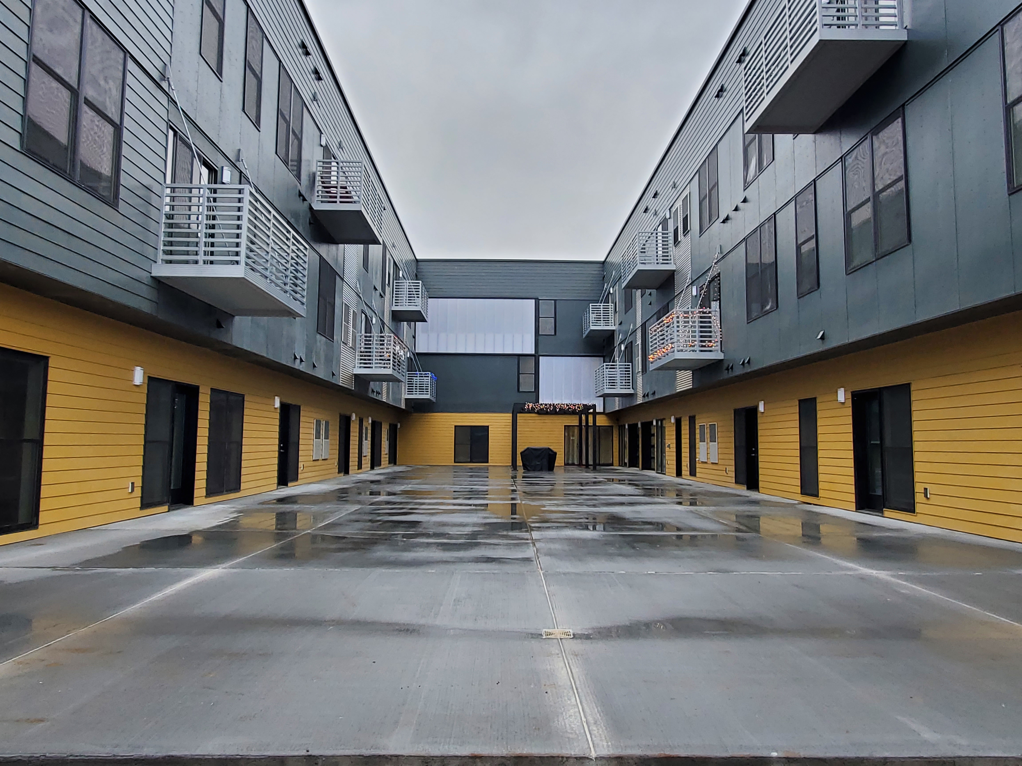
CA/Site Reports and Photos/20201221/2020-12-21 14.42.26.jpg
