OpeningDesign/CTR/CA/Site Reports and Photos/20201221/Refined/2020-12-21 14.42.16.jpg

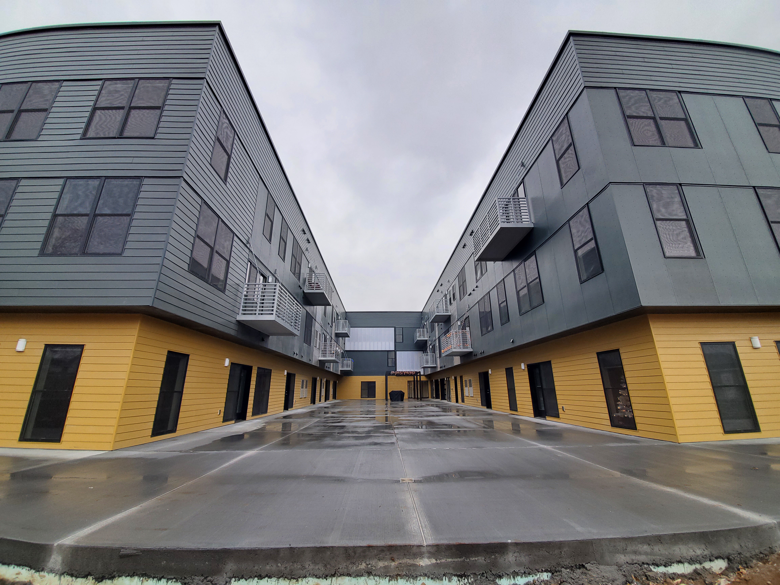
CA/Site Reports and Photos/20201221/Refined/2020-12-21 14.42.16.jpg
