OpeningDesign/CTR/Transfer/20181111 - to owner - for design review/2.jpg

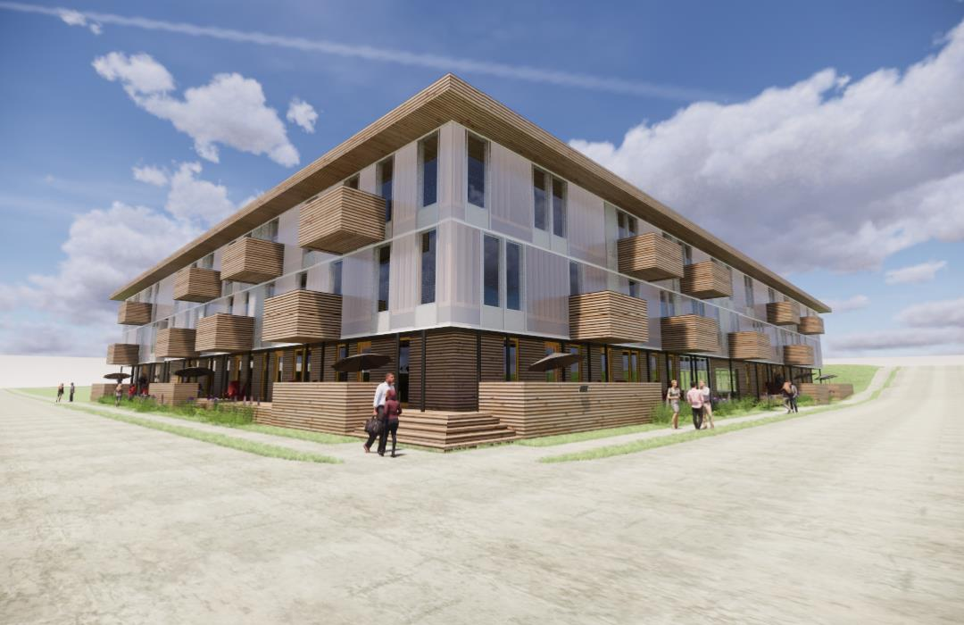
Transfer/20181111 - to owner - for design review/2.jpg
