OpeningDesign/CTR/Transfer/20181111 - to owner - for design review/20181111 - Cannery 2 Page 008.jpg

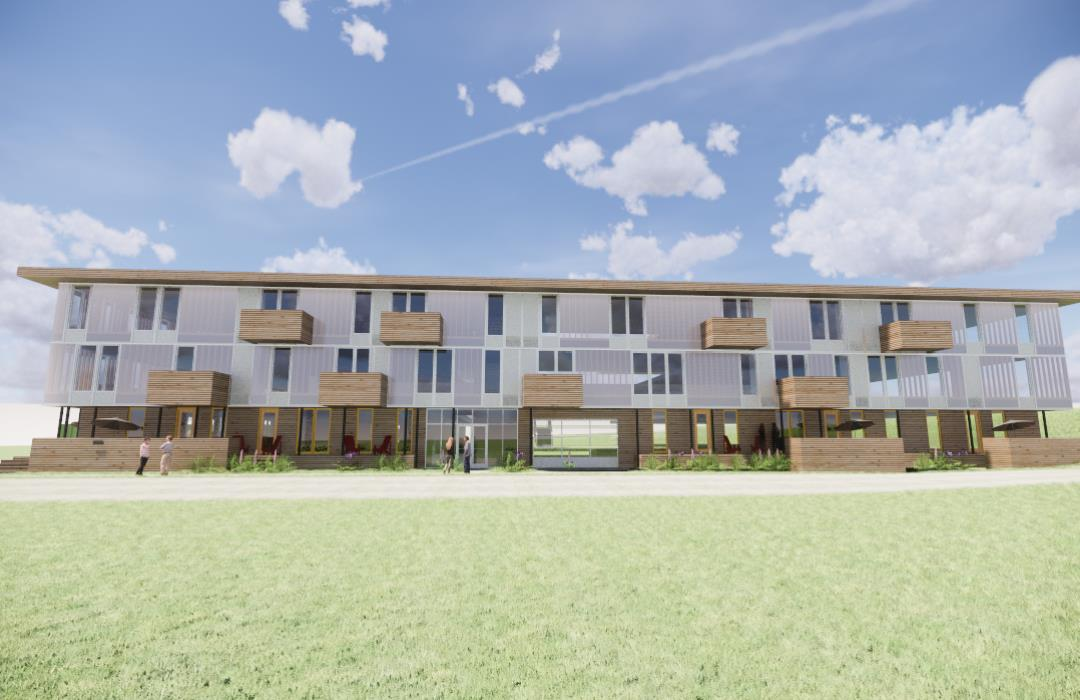
Transfer/20181111 - to owner - for design review/20181111 - Cannery 2 Page 008.jpg
