OpeningDesign/CTR/Transfer/20190529 - from Struct - Offset Precast Proposal/20190528_precast_panel Page 001.jpg

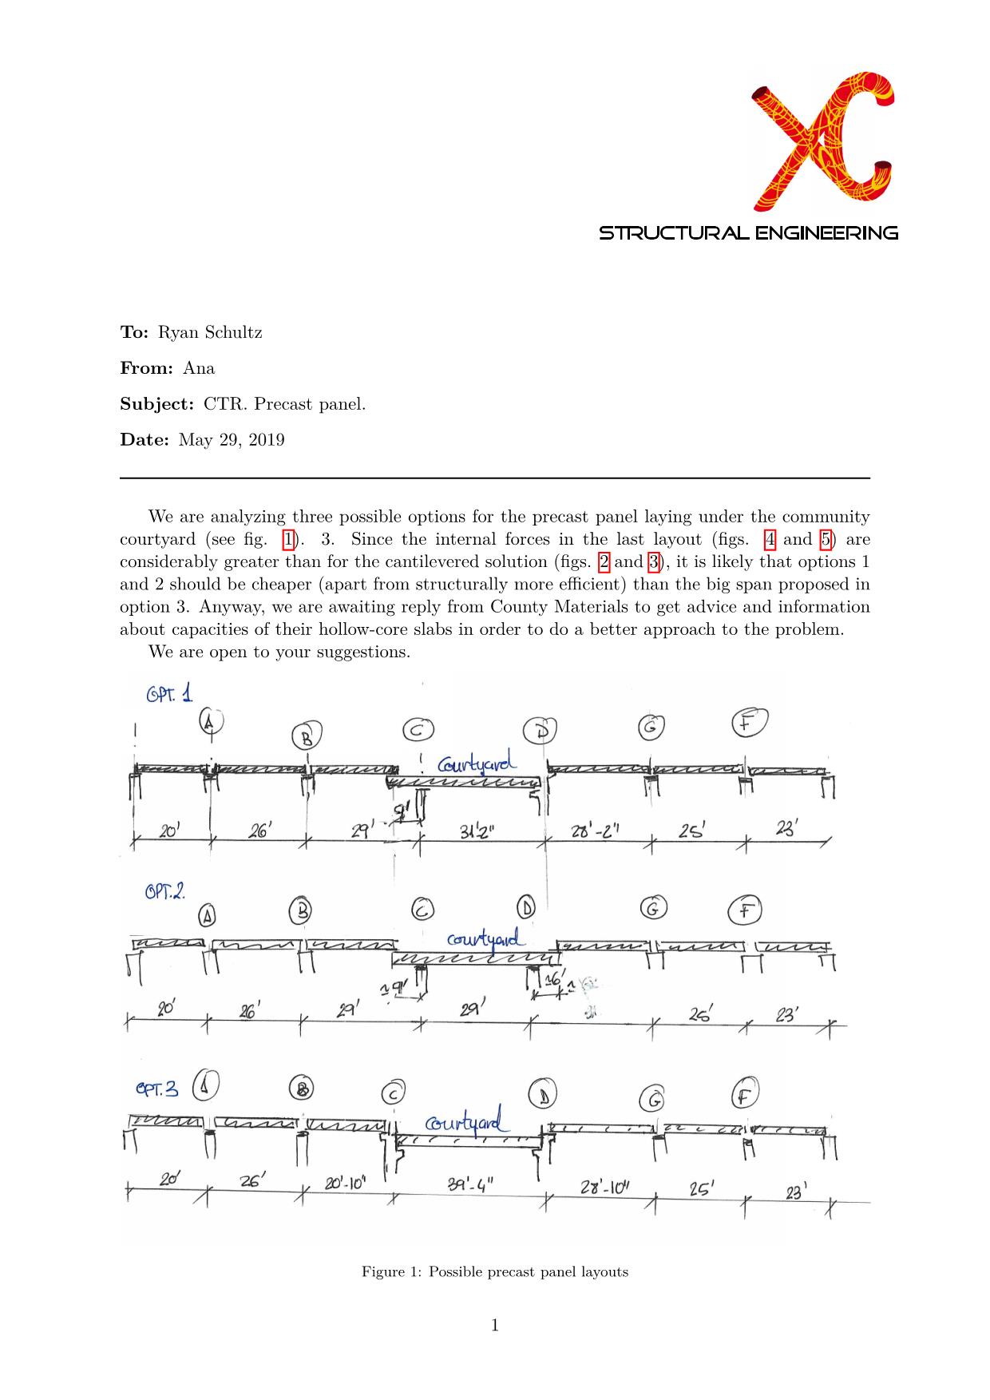
Transfer/20190529 - from Struct - Offset Precast Proposal/20190528_precast_panel Page 001.jpg
