OpeningDesign/CTR/Transfer/20190624 - to owner - review of revised designed - updated colors/20190625 - CTR Page 006.jpg

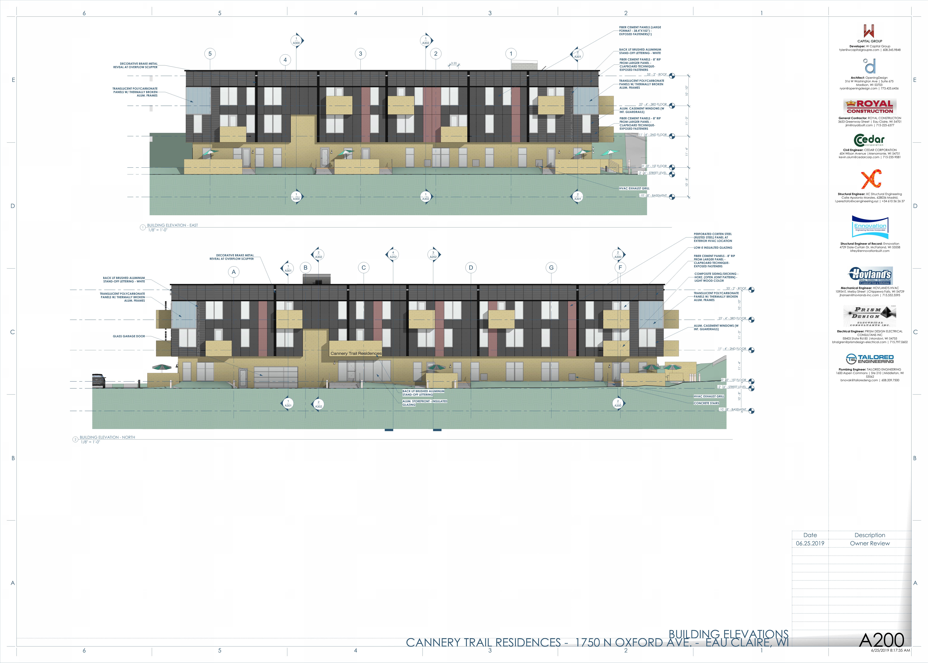
Transfer/20190624 - to owner - review of revised designed - updated colors/20190625 - CTR Page 006.jpg
