OpeningDesign/CTR/Transfer/20190725 - to Design team - cad backgrounds/20190725 - CTR - Progress Backgrounds Page 001.jpg

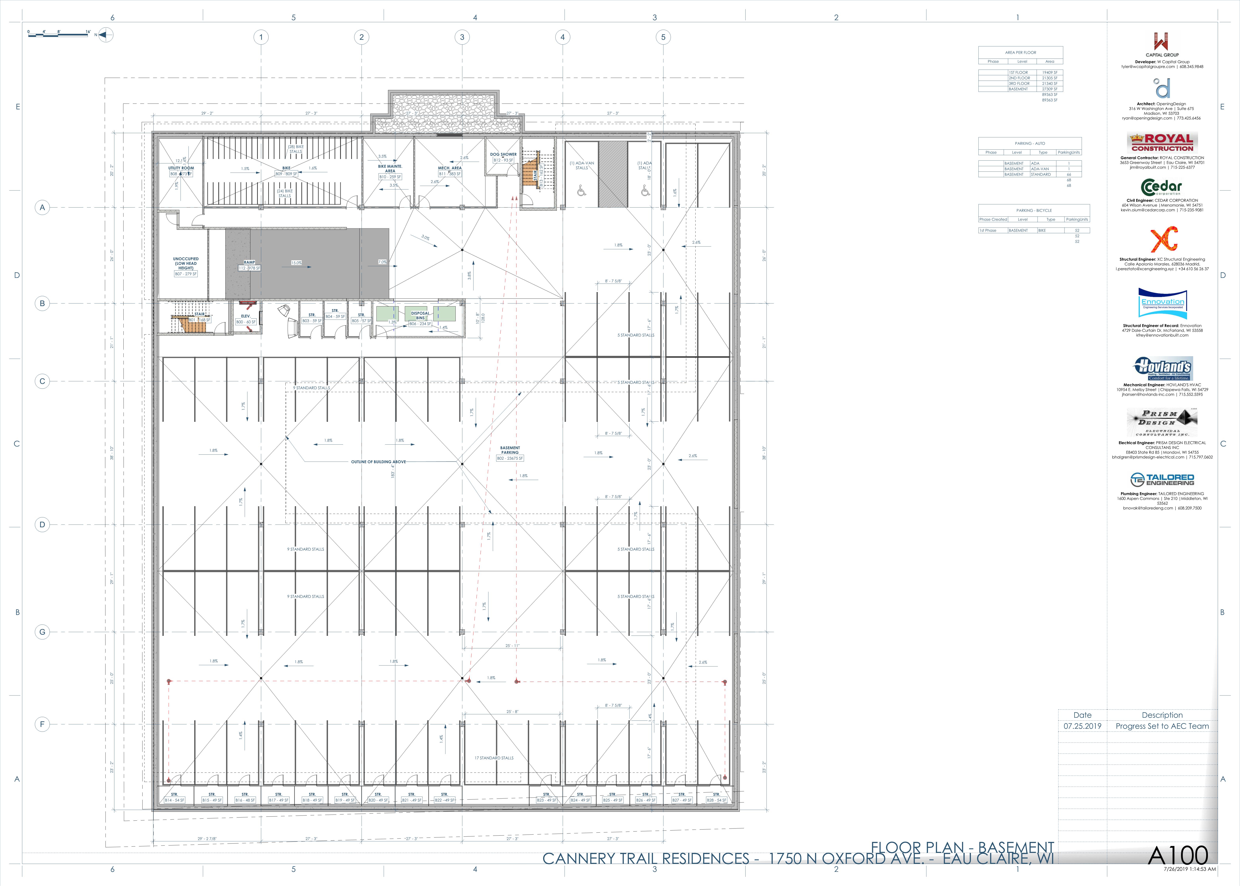
Transfer/20190725 - to Design team - cad backgrounds/20190725 - CTR - Progress Backgrounds Page 001.jpg
