OpeningDesign/CTR/Transfer/20190815 - from Hardward Consultant/DOOR HARDWARE INDEX_Cannery Trail Residences 08-15-19 Page 002.jpg

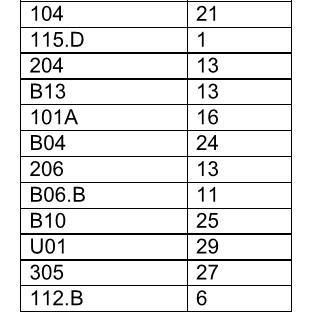
Transfer/20190815 - from Hardward Consultant/DOOR HARDWARE INDEX_Cannery Trail Residences 08-15-19 Page 002.jpg
