OpeningDesign/CTR/XC_struct/calculation_report/annex_res_columns/graphics/resSimplLC/SLS02_bbeamsMy.jpg

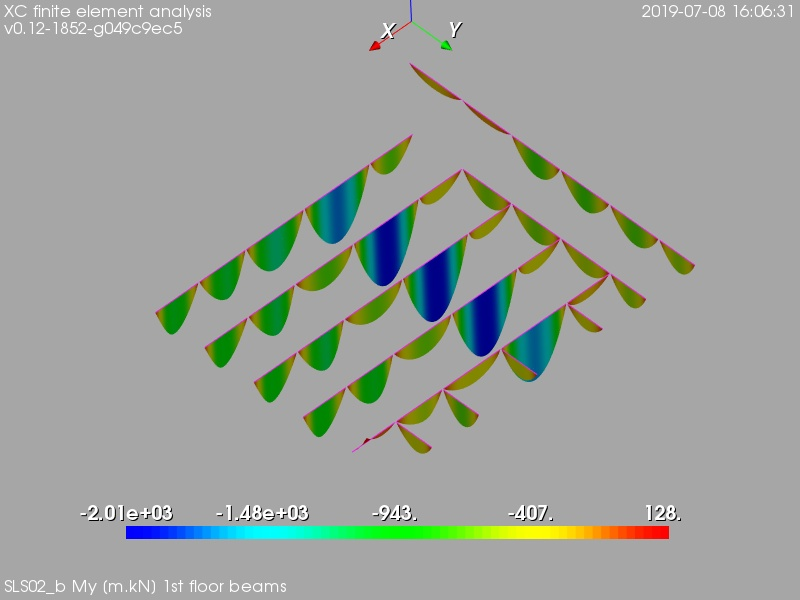
XC_struct/calculation_report/annex_res_columns/graphics/resSimplLC/SLS02_bbeamsMy.jpg
