OpeningDesign/CTR/XC_struct/calculation_report/ramp_wall/resLC/text/graphics/shearULS/wallsCFSect2.jpg

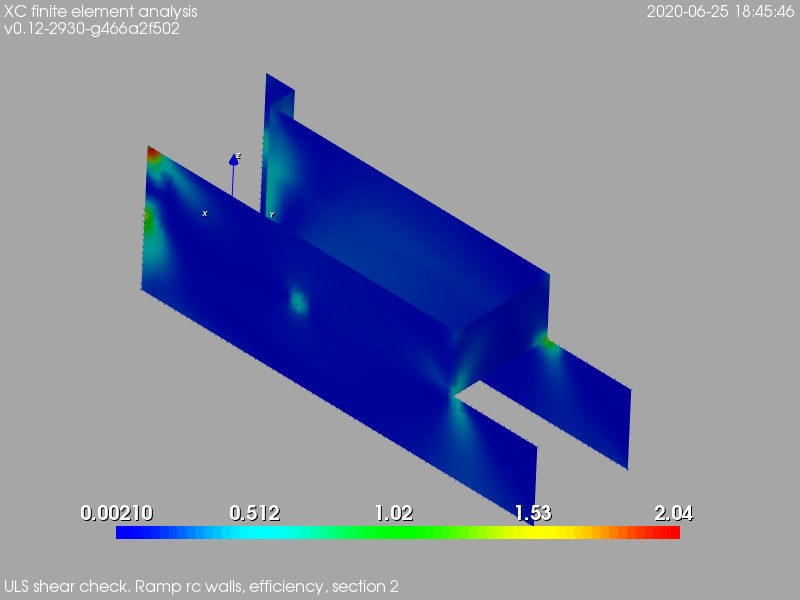
XC_struct/calculation_report/ramp_wall/resLC/text/graphics/shearULS/wallsCFSect2.jpg
