OpeningDesign/CTR/XC_struct/calculation_report/ramp_wall/resLC/text/sections/E1FwallRCSects1NMy.jpeg

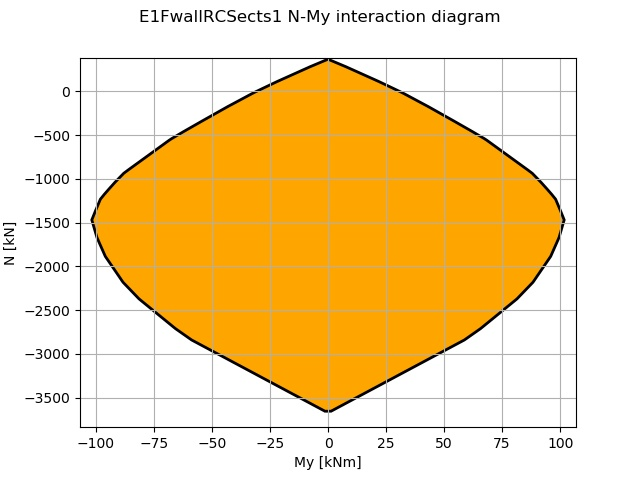
XC_struct/calculation_report/ramp_wall/resLC/text/sections/E1FwallRCSects1NMy.jpeg
