OpeningDesign/CTR/XC_struct/calculation_report/ramp_wall/resLC/text/sections/EBwallRCSects1NMy.jpeg

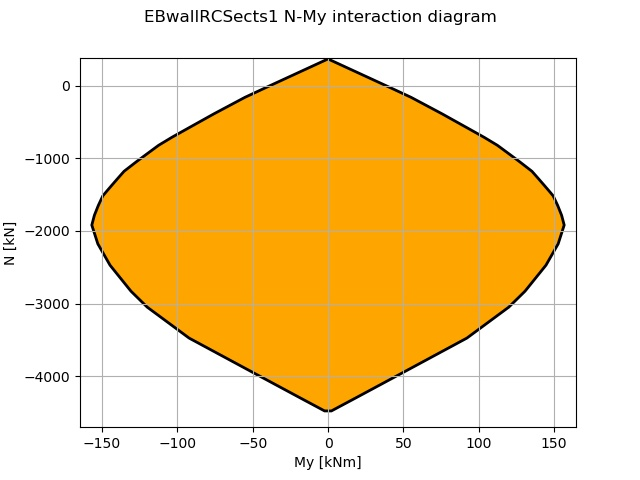
XC_struct/calculation_report/ramp_wall/resLC/text/sections/EBwallRCSects1NMy.jpeg
