OpeningDesign/CTR/XC_struct/calculation_report/ramp_wall/resLC/text/sections/EBwallRCSects2NMz.jpeg

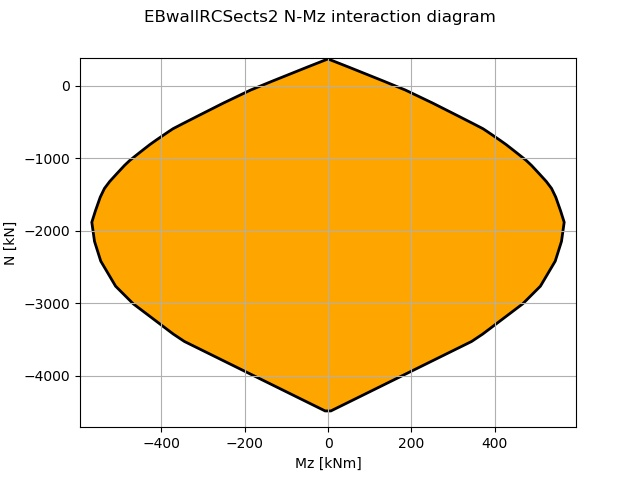
XC_struct/calculation_report/ramp_wall/resLC/text/sections/EBwallRCSects2NMz.jpeg
