OpeningDesign/CTR/XC_struct/calculation_report/ramp_wall/resLC/text/sections/W1FwallRCSects1NMz.jpeg

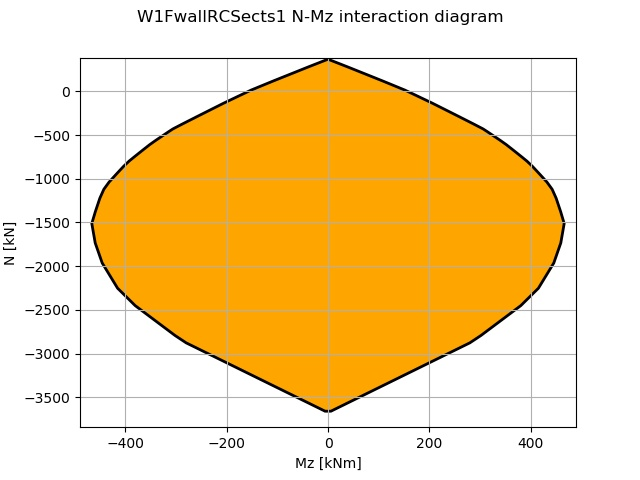
XC_struct/calculation_report/ramp_wall/resLC/text/sections/W1FwallRCSects1NMz.jpeg
