OpeningDesign/CTR/XC_struct/xc_models/wood_structure/stud_wall_design/anchor_bolts/s201_remarks.jpeg

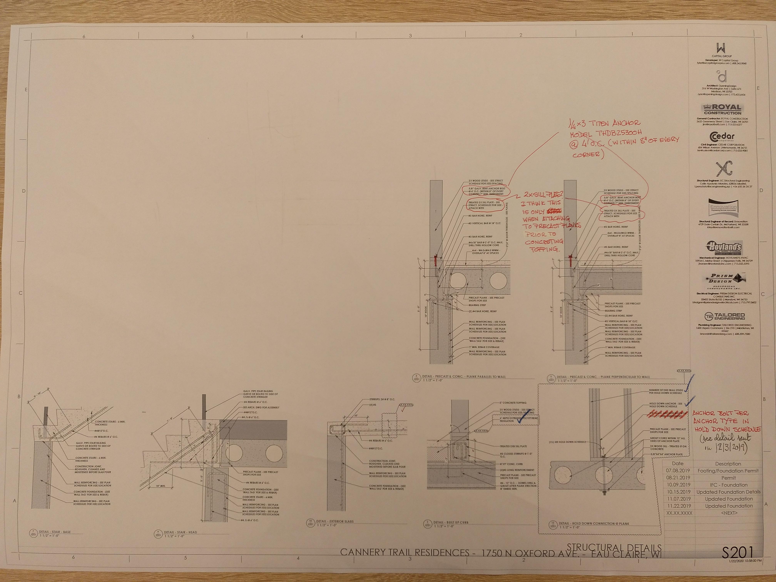
XC_struct/xc_models/wood_structure/stud_wall_design/anchor_bolts/s201_remarks.jpeg
