OpeningDesign/CTR/XC_struct/xc_models/wood_structure/stud_wall_design/anchor_bolts/selected_titen_anchor_bolt.png

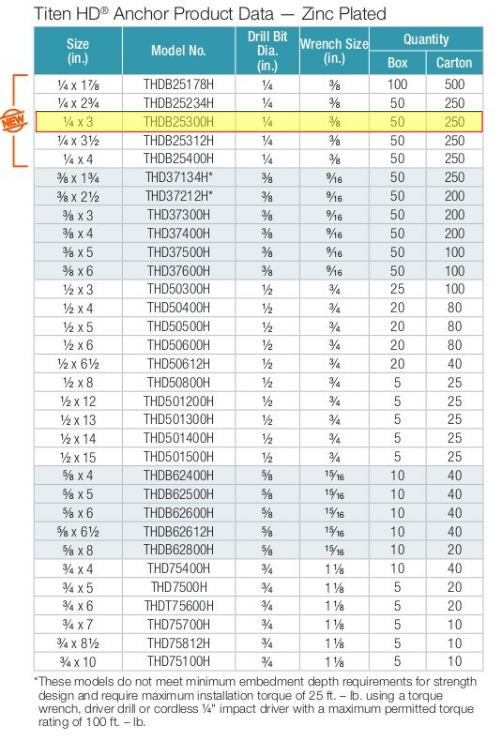
XC_struct/xc_models/wood_structure/stud_wall_design/anchor_bolts/selected_titen_anchor_bolt.png
