OpeningDesign/CTR/XC_struct/xc_models/wood_structure/stud_wall_design/anchor_bolts/titen_anchor_bolt.jpg

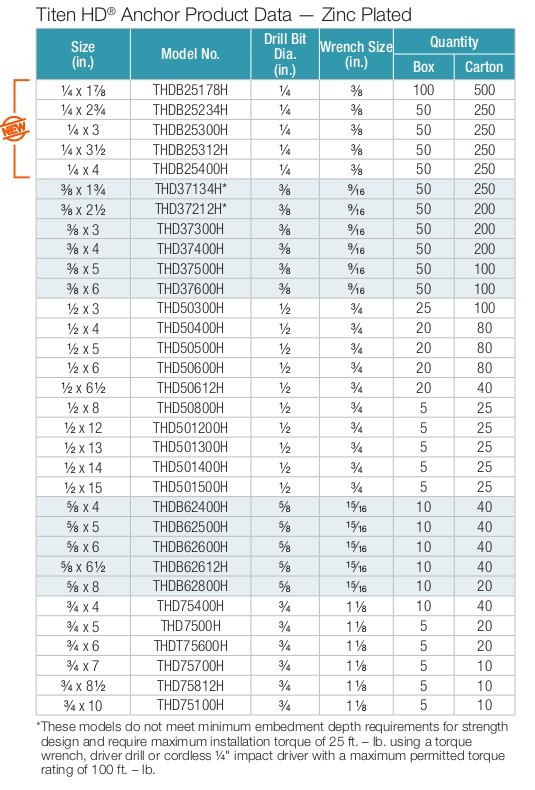
XC_struct/xc_models/wood_structure/stud_wall_design/anchor_bolts/titen_anchor_bolt.jpg
