OpeningDesign/CTR/Products/Uniformat comparison-ALL.xls

A | Substructure | 1 |  |  | A | Substructure | 1 |  | 21-01 00 00 | Substructure
B | Shell | 1 |  |  | A2010310 | Shoring | 5 | -2001300 | 21-02 00 00 | Shell
C | Interiors | 1 |  |  | B1020230 | Beams - Steel | 5 | -2001320 | 21-03 00 00 | Interiors
D | Services | 1 |  |  | B2030900 | Other Exterior Doors | 4 | -2000023 | 21-04 00 00 | Services
E | Equipment and Furnishings | 1 |  |  | D1020110 | Escalators | 5 | -2001350 | 21-05 00 00 | Equipment and Furnishings
F | Special Construction and Demolition | 1 |  |  | D2040 | Rain Water Drainage | 3 | -2001160 | 21-06 00 00 | Special Construction and Demolition
G | Sitework | 1 |  |  | D3090 | Other HVAC Systems/Equip | 3 | -2001140 | 21-07 00 00 | Sitework
A10 | Foundations | 2 | 0 |  | A10 | Foundations | 2 |  | 21-01 10 | Foundations
A20 | Subgrade Enclosures | 2 | 0 |  | A1020100 | Pile Foundations | 4 | -2001300 | 21-01 20 | Subgrade Enclosures
A40 | Slabs-On-Grade | 2 | 0 |  | A1020150 | Piles - Step Tapered | 5 | -2001300 | 21-01 40 | Slabs-On-Grade
A60 | Water and Gas Mitigation | 2 | 0 |  | A1020900 | Other Special Foundation Conditions | 4 | -2001300 | 21-01 60 | Water and Gas Mitigation
A90 | Substructure Related Activities | 2 | 0 |  | A1030400 | Trenches | 4 | -2001300 | 21-01 90 | Substructure Related Activities
B10 | Superstructure | 2 | 0 |  | A2020 | Basement Walls | 3 |  | 21-02 10 | Superstructure
B20 | Exterior Vertical Enclosures | 2 | 0 |  | B1010245 | Columns - Precast | 5 | -2001330 | 21-02 20 | Exterior Vertical Enclosures
B30 | Exterior Horizontal Enclosures | 2 | 0 |  | B1010480 | Wood Beams w/ Wood Joists | 5 | -2001320 | 21-02 30 | Exterior Horizontal Enclosures
C10 | Interior Construction | 2 | 0 |  | B1020240 | Beams - Wood (Dimensional Lumber) | 5 | -2001320 | 21-03 10 | Interior Construction
C20 | Interior Finishes | 2 | 0 |  | B2010152 | Ext. Wall - Brick (Double Wythe) | 5 | -2000011 | 21-03 20 | Interior Finishes
D10 | Conveying | 2 | 0 |  | B30 | Roofing | 2 |  | 21-04 10 | Conveying
D20 | Plumbing | 2 | 0 |  | B3020300 | Gravity Roof Ventilators | 4 | -2001140 | 21-04 20 | Plumbing
D30 | Heating, Ventilation, and Air Conditioning (HVAC) | 2 | 0 |  | C1010600 | Interior Balustrades & Screens | 4 | -2000126 | 21-04 30 | Heating, Ventilation, and Air Conditioning (HVAC)
D40 | Fire Protection | 2 | 0 |  | C1030400 | Fabricated Cabinets & Counters | 4 | -2001000 | 21-04 40 | Fire Protection
D50 | Electrical | 2 | 0 |  | C1030900 | Other Fittings | 4 | -2001350 | 21-04 50 | Electrical
D60 | Communications | 2 | 0 |  | C3020100 | Floor Toppings & Coatings | 4 | -2000032 | 21-04 60 | Communications
D70 | Electronic Safety and Security | 2 | 0 |  | C3030 | Ceiling Finishes | 3 |  | 21-04 70 | Electronic Safety and Security
D80 | Integrated Automation | 2 | 0 |  | D1010100 | Passenger Elevators | 4 | -2001350 | 21-04 80 | Integrated Automation
E10 | Equipment | 2 | 0 |  | D1020200 | Moving Walks | 4 | -2001350 | 21-05 10 | Equipment
E20 | Furnishings | 2 | 0 |  | D2010820 | Water Coolers | 5 | -2001160 | 21-05 20 | Furnishings
F10 | Special Construction | 2 | 0 |  | D2040100 | Pipe & Fittings | 4 | -2001160 | 21-06 10 | Special Construction
F20 | Facility Remediation | 2 | 0 |  | D3040400 | Hot Water Distribution | 4 | -2001140 | 21-06 20 | Facility Remediation
F30 | Demolition | 2 | 0 |  | D3060 | Controls & Instrumentation | 3 | -2001140 | 21-06 30 | Demolition
G10 | Site Preparation | 2 | 0 |  | D3090100 | Special Cooling Systems & Devices | 4 | -2001140 | 21-07 10 | Site Preparation
G20 | Site Improvements | 2 | 0 |  | D5020110 | Receptacles - Wall | 5 | -2001060 | 21-07 20 | Site Improvements
G30 | Liquid and Gas Site Utilities | 2 | 0 |  | E1020300 | Theater & Stage Equipment | 4 | -2001350 | 21-07 30 | Liquid and Gas Site Utilities
G40 | Electrical Site Improvements | 2 | 0 |  | E20 | Furnishings | 2 |  | 21-07 40 | Electrical Site Improvements
G50 | Site Communications | 2 | 0 |  | E2020300 | Movable Rugs & Mats | 4 | -2000080 | 21-07 50 | Site Communications
G90 | Miscellaneous Site Construction | 2 | 0 |  | F1010 | Special Structures | 3 |  | 21-07 90 | Miscellaneous Site Construction
A1010 | Standard Foundations | 3 | 0 |  | A1010 | Standard Foundations | 3 |  | 21-01 10 10 | Standard Foundations
A1020 | Special Foundations | 3 | 0 |  | A1010130 | Pile Caps | 5 | -2001300 | 21-01 10 20 | Special Foundations
A2010 | Walls for Subgrade Enclosures | 3 | 0 |  | A1020110 | Piles - CIP | 5 | -2001300 | 21-01 20 10 | Walls for Subgrade Enclosures
A4010 | Standard Slabs-on-Grade | 3 | 0 |  | A1020160 | Piles - Treated Wood | 5 | -2001300 | 21-01 40 10 | Standard Slabs-on-Grade
A4020 | Structural Slabs-on-Grade | 3 | 0 |  | A1020200 | Grade Beams | 4 | -2001300 | 21-01 40 20 | Structural Slabs-on-Grade
A4030 | Slab Trenches | 3 | 0 |  | A1020210 | Grade Beams - CIP | 5 | -2001300 | 21-01 40 30 | Slab Trenches
A4040 | Pits and Bases | 3 | 0 |  | A1020300 | Caissons | 4 | -2001300 | 21-01 40 40 | Pits and Bases
A4090 | Slab-On-Grade Supplementary Components | 3 | 0 |  | A1020310 | Caissons - Bell | 5 | -2001300 | 21-01 40 90 | Slab-On-Grade Supplementary Components
A6010 | Building Subdrainage | 3 | 0 |  | A1030 | Slab on Grade | 3 |  | 21-01 60 10 | Building Subdrainage
A6020 | Off-Gassing Mitigation | 3 | 0 |  | A1030120 | SOG - Unreinforced | 5 | -2000032 | 21-01 60 20 | Off-Gassing Mitigation
A9010 | Substructure Excavation | 3 | 0 |  | A1030500 | Pits & Bases | 4 | -2001300 | 21-01 90 10 | Substructure Excavation
A9020 | Construction Dewatering | 3 | 0 |  | A1030700 | Under-Slab Insulation | 4 | -2000032 | 21-01 90 20 | Construction Dewatering
A9030 | Excavation Support | 3 | 0 |  | A1030710 | Subdrainage Piping | 5 | -2001160 | 21-01 90 30 | Excavation Support
A9040 | Soil Treatment | 3 | 0 |  | A2010300 | Shoring | 4 | -2001300 | 21-01 90 40 | Soil Treatment
B1010 | Floor Construction | 3 | 0 |  | A2020100 | Basement Wall Construction | 4 | -2000011 | 21-02 10 10 | Floor Construction
B1020 | Roof Construction | 3 | 0 |  | A2020310 | Basement Wall Insulation - Rigid | 5 | -2000011 | 21-02 10 20 | Roof Construction
B1080 | Stairs | 3 | 0 |  | B1010100 | Suspended Basement Floor Construction | 4 | -2000032 | 21-02 10 80 | Stairs
B2010 | Exterior Walls | 3 | 0 |  | B1010250 | Columns - Steel | 5 | -2001330 | 21-02 20 10 | Exterior Walls
B2020 | Exterior Windows | 3 | 0 |  | B1010350 | Joists - Steel | 5 | -2001320 | 21-02 20 20 | Exterior Windows
B2050 | Exterior Doors and Grilles | 3 | 0 |  | B1010380 | Planks - Precast | 5 | -2000032 | 21-02 20 50 | Exterior Doors and Grilles
B2070 | Exterior Louvers and Vents | 3 | 0 |  | B1010422 | CIP Beam & Slab - Two Way | 5 | -2001320 | 21-02 20 70 | Exterior Louvers and Vents
B2080 | Exterior Wall Appurtenances | 3 | 0 |  | B1010434 | W Shape Composite Deck & Slab | 5 | -2001320 | 21-02 20 80 | Exterior Wall Appurtenances
B2090 | Exterior Wall Specialties | 3 | 0 |  | B1010470 | Steel Light Gauge Floor System | 5 | -2001320 | 21-02 20 90 | Exterior Wall Specialties
B3010 | Roofing | 3 | 0 |  | B1010482 | Wood Laminated Beams w/ Wood Joists | 5 | -2001320 | 21-02 30 10 | Roofing
B3020 | Roof Appurtenances | 3 | 0 |  | B1010900 | Fireproofing - Floor Construction | 4 | -2000032 | 21-02 30 20 | Roof Appurtenances
B3040 | Traffic Bearing Horizontal Enclosures | 3 | 0 |  | B1020100 | Flat Roof Framing - Vertical Elements | 4 | -2000011 | 21-02 30 40 | Traffic Bearing Horizontal Enclosures
B3060 | Horizontal Openings | 3 | 0 |  | B1020140 | Columns - CIP | 5 | -2001330 | 21-02 30 60 | Horizontal Openings
B3080 | Overhead Exterior Enclosures | 3 | 0 |  | B1020200 | Flat Roof Framing - Horizontal Elements | 4 | -2001320 | 21-02 30 80 | Overhead Exterior Enclosures
C1010 | Interior Partitions | 3 | 0 |  | B1020245 | Beams - Wood (Laminated) | 5 | -2001320 | 21-03 10 10 | Interior Partitions
C1020 | Interior Windows | 3 | 0 |  | B1020300 | Flat Roof Framing - Systems | 4 | -2000035 | 21-03 10 20 | Interior Windows
C1030 | Interior Doors | 3 | 0 |  | B1020318 | CIP Slabs - Waffle | 5 | -2000035 | 21-03 10 30 | Interior Doors
C1040 | Interior Grilles and Gates | 3 | 0 |  | B1020364 | Joist Girders w/ Steel Joists | 5 | -2001320 | 21-03 10 40 | Interior Grilles and Gates
C1060 | Raised Floor Construction | 3 | 0 |  | B1020382 | Wood Laminated Beams w/ Wood Joists | 5 | -2001320 | 21-03 10 60 | Raised Floor Construction
C1070 | Suspended Ceiling Construction | 3 | 0 |  | B1020600 | Dome Construction | 4 | -2000035 | 21-03 10 70 | Suspended Ceiling Construction
C1090 | Interior Specialties | 3 | 0 |  | B20 | Exterior Enclosure | 2 |  | 21-03 10 90 | Interior Specialties
C2010 | Wall Finishes | 3 | 0 |  | B2010154 | Ext. Wall - Brick Cavity | 5 | -2000011 | 21-03 20 10 | Wall Finishes
C2020 | Interior Fabrications | 3 | 0 |  | B2010400 | Exterior Sun Control Devices | 4 | -2001140 | 21-03 20 20 | Interior Fabrications
C2030 | Flooring | 3 | 0 |  | B2010500 | Balcony Walls & Handrails | 4 | -2000126 | 21-03 20 30 | Flooring
C2040 | Stair Finishes | 3 | 0 |  | B2030100 | Glazed Doors & Entrances | 4 | -2000023 | 21-03 20 40 | Stair Finishes
C2050 | Ceiling Finishes | 3 | 0 |  | B2030230 | Exterior Solid Doors - Wood | 5 | -2000023 | 21-03 20 50 | Ceiling Finishes
D1010 | Vertical Conveying Systems | 3 | 0 |  | B3010 | Roof Coverings | 3 |  | 21-04 10 10 | Vertical Conveying Systems
D1030 | Horizontal Conveying | 3 | 0 |  | B3010150 | Roofing - Shingle & Tile | 5 | -2000035 | 21-04 10 30 | Horizontal Conveying
D1050 | Material Handling | 3 | 0 |  | B3010410 | Base Flashing | 5 | -2000035 | 21-04 10 50 | Material Handling
D1080 | Operable Access Systems | 3 | 0 |  | B3020100 | Glazed Roof Openings | 4 | -2000014 | 21-04 10 80 | Operable Access Systems
D2010 | Domestic Water Distribution | 3 | 0 |  | C | Interiors | 1 |  | 21-04 20 10 | Domestic Water Distribution
D2020 | Sanitary Drainage | 3 | 0 |  | C1010118 | Partitions - Stone Veneer w/ Stud | 5 | -2000011 | 21-04 20 20 | Sanitary Drainage
D2030 | Building Support Plumbing Systems | 3 | 0 |  | C1010140 | Partitions - Drywall w/ Wood Stud | 5 | -2000011 | 21-04 20 30 | Building Support Plumbing Systems
D2050 | General Service Compressed-Air | 3 | 0 |  | C1010190 | Partition Components - Drywall | 5 | -2000011 | 21-04 20 50 | General Service Compressed-Air
D2060 | Process Support Plumbing Systems | 3 | 0 |  | C1010195 | Partition Components - Plaster | 5 | -2000011 | 21-04 20 60 | Process Support Plumbing Systems
D3010 | Facility Fuel Systems | 3 | 0 |  | C1010700 | Interior Windows & Storefronts | 4 | -2000014 | 21-04 30 10 | Facility Fuel Systems
D3020 | Heating Systems | 3 | 0 |  | C1020110 | Interior Doors - Metal | 5 | -2000023 | 21-04 30 20 | Heating Systems
D3030 | Cooling Systems | 3 | 0 |  | C1020300 | Interior Doors with Frames | 4 | -2000023 | 21-04 30 30 | Cooling Systems
D3050 | Facility HVAC Distribution Systems | 3 | 0 |  | C1020500 | Interior Door Wall Opening Elements | 4 | -2000023 | 21-04 30 50 | Facility HVAC Distribution Systems
D3060 | Ventilation | 3 | 0 |  | C1030110 | Toilet Partitions | 5 | -2001160 | 21-04 30 60 | Ventilation
D3070 | Special Purpose HVAC Systems | 3 | 0 |  | C1030320 | Shelving | 5 | -2001350 | 21-04 30 70 | Special Purpose HVAC Systems
D4010 | Fire Suppression | 3 | 0 |  | C1030410 | Cabinets | 5 | -2001000 | 21-04 40 10 | Fire Suppression
D5010 | Facility Power Generation | 3 | 0 |  | C1030910 | Mailboxes | 5 | -2001350 | 21-04 50 10 | Facility Power Generation
D5020 | Electrical Service and Distribution | 3 | 0 |  | C2010200 | Curved Stairs | 4 | -2000120 | 21-04 50 20 | Electrical Service and Distribution
D5030 | General Purpose Electrical Power | 3 | 0 |  | C2020 | Stair Finishes | 3 |  | 21-04 50 30 | General Purpose Electrical Power
D5040 | Lighting | 3 | 0 |  | C30 | Interior Finishes | 2 |  | 21-04 50 40 | Lighting
D5080 | Miscellaneous Electrical Systems | 3 | 0 |  | C3010130 | Wall Finishes - Coverings | 5 | -2000011 | 21-04 50 80 | Miscellaneous Electrical Systems
D6010 | Data Communications | 3 | 0 |  | C3020110 | Concrete Toppings | 5 | -2000032 | 21-04 60 10 | Data Communications
D6020 | Voice Communications | 3 | 0 |  | C3020410 | Flooring - Sheet Goods | 5 | -2000032 | 21-04 60 20 | Voice Communications
D6030 | Audio-Video Communication | 3 | 0 |  | C3020500 | Carpeting | 4 | -2000032 | 21-04 60 30 | Audio-Video Communication
D6090 | Communications Supplementary Components | 3 | 0 |  | C3020800 | Subflooring & Underlayment | 4 | -2000032 | 21-04 60 90 | Communications Supplementary Components
D7010 | Access Control and Intrusion Detection | 3 | 0 |  | C3030100 | Applied Ceiling Finishes | 4 | -2000038 | 21-04 70 10 | Access Control and Intrusion Detection
D7030 | Electronic Surveillance | 3 | 0 |  | C3030130 | Ceiling Finishes - Coverings | 5 | -2000038 | 21-04 70 30 | Electronic Surveillance
D7050 | Detection and Alarm | 3 | 0 |  | C3030200 | Suspended Ceilings | 4 | -2000038 | 21-04 70 50 | Detection and Alarm
D7070 | Electronic Monitoring and Control | 3 | 0 |  | C3030900 | Other Ceiling Finishes | 4 | -2000038 | 21-04 70 70 | Electronic Monitoring and Control
D7090 | Electronic Safety and Security Supplementary Components | 3 | 0 |  | D10 | Conveying | 2 |  | 21-04 70 90 | Electronic Safety and Security Supplementary Components
D8010 | Integrated Automation Facility Controls | 3 | 0 |  | D1010110 | Elevators - Hydraulic | 5 | -2001350 | 21-04 80 10 | Integrated Automation Facility Controls
E1010 | Vehicle and Pedestrian Equipment | 3 | 0 |  | D1020210 | Moving Walks | 5 | -2001350 | 21-05 10 10 | Vehicle and Pedestrian Equipment
E1030 | Commercial Equipment | 3 | 0 |  | D1090400 | Conveyors | 4 | -2001350 | 21-05 10 30 | Commercial Equipment
E1040 | Institutional Equipment | 3 | 0 |  | D2010120 | Water Closets - Group | 5 | -2001160 | 21-05 10 40 | Institutional Equipment
E1060 | Residential Equipment | 3 | 0 |  | D2010320 | Lavatories - Battery Mount | 5 | -2001160 | 21-05 10 60 | Residential Equipment
E1070 | Entertainment and Recreational Equipment | 3 | 0 |  | D2010430 | Sinks - Laboratory | 5 | -2001160 | 21-05 10 70 | Entertainment and Recreational Equipment
E1090 | Other Equipment | 3 | 0 |  | D2010610 | Wash Fountains - Group | 5 | -2001160 | 21-05 10 90 | Other Equipment
E2010 | Fixed Furnishings | 3 | 0 |  | D2010900 | Other Plumbing Fixtures | 4 | -2001160 | 21-05 20 10 | Fixed Furnishings
E2050 | Movable Furnishings | 3 | 0 |  | D2030 | Sanitary Waste | 3 | -2001160 | 21-05 20 50 | Movable Furnishings
F1010 | Integrated Construction | 3 | 0 |  | D2040200 | Roof Drains | 4 | -2001160 | 21-06 10 10 | Integrated Construction
F1020 | Special Structures | 3 | 0 |  | D2090100 | Gas Distribution | 4 | -2001160 | 21-06 10 20 | Special Structures
F1030 | Special Function Construction | 3 | 0 |  | D30 | HVAC | 2 |  | 21-06 10 30 | Special Function Construction
F1050 | Special Facility Components | 3 | 0 |  | D3010300 | Coal Supply System | 4 | -2001140 | 21-06 10 50 | Special Facility Components
F1060 | Athletic and Recreational Special Construction | 3 | 0 |  | D3020100 | Boilers | 4 | -2001140 | 21-06 10 60 | Athletic and Recreational Special Construction
F1080 | Special Instrumentation | 3 | 0 |  | D3030300 | Other Cooling System Components | 4 | -2001140 | 21-06 10 80 | Special Instrumentation
F2010 | Hazardous Materials Remediation | 3 | 0 |  | D3040500 | Chilled Water Distribution | 4 | -2001140 | 21-06 20 10 | Hazardous Materials Remediation
F3010 | Structure Demolition | 3 | 0 |  | D3060100 | Heating Generating Systems | 4 | -2001140 | 21-06 30 10 | Structure Demolition
F3030 | Selective Demolition | 3 | 0 |  | D3060600 | Terminal Devices | 4 | -2001140 | 21-06 30 30 | Selective Demolition
F3050 | Structure Moving | 3 | 0 |  | D3070200 | Air System Testing & Balancing | 4 | -2001140 | 21-06 30 50 | Structure Moving
G1010 | Site Clearing | 3 | 0 |  | D3090200 | Special Humidity Control | 4 | -2001140 | 21-07 10 10 | Site Clearing
G1020 | Site Elements Demolition | 3 | 0 |  | D3090600 | Paint Spray Booth Ventilation | 4 | -2001140 | 21-07 10 20 | Site Elements Demolition
G1030 | Site Element Relocations | 3 | 0 |  | D4010 | Sprinklers | 3 |  | 21-07 10 30 | Site Element Relocations
G1050 | Site Remediation | 3 | 0 |  | D4010200 | Sprinkler Pumping Equipment | 4 | -2001160 | 21-07 10 50 | Site Remediation
G1070 | Site Earthwork | 3 | 0 |  | D4030900 | Other Fire Protection Specialties | 4 | -2001350 | 21-07 10 70 | Site Earthwork
G2010 | Roadways | 3 | 0 |  | D5020115 | Receptacles - Floor | 5 | -2001060 | 21-07 20 10 | Roadways
G2020 | Parking Lots | 3 | 0 |  | D5020280 | Light Poles | 5 | -2001120 | 21-07 20 20 | Parking Lots
G2030 | Pedestrian Plazas and Walkways | 3 | 0 |  | D5030500 | Television Systems | 4 | -2001040 | 21-07 20 30 | Pedestrian Plazas and Walkways
G2040 | Airfields | 3 | 0 |  | D5090200 | Emergency Light & Power Systems | 4 | -2001040 | 21-07 20 40 | Airfields
G2050 | Athletic, Recreational, and Playfield Areas | 3 | 0 |  | E1010 | Commercial Equipment | 3 |  | 21-07 20 50 | Athletic, Recreational, and Playfield Areas
G2060 | Site Development | 3 | 0 |  | E1010200 | Teller & Service Equipment | 4 | -2001350 | 21-07 20 60 | Site Development
G2080 | Landscaping | 3 | 0 |  | E1020100 | Ecclesiastical Equipment | 4 | -2001350 | 21-07 20 80 | Landscaping
G3010 | Water Utilities | 3 | 0 |  | E1020310 | Theater Equipment - Projection | 5 | -2001350 | 21-07 30 10 | Water Utilities
G3020 | Sanitary Sewerage Utilities | 3 | 0 |  | E1020500 | Audio-visual Equipment | 4 | -2001350 | 21-07 30 20 | Sanitary Sewerage Utilities
G3030 | Storm Drainage Utilities | 3 | 0 |  | E1020800 | Medical Equipment | 4 | -2001350 | 21-07 30 30 | Storm Drainage Utilities
G3050 | Site Energy Distribution | 3 | 0 |  | E1030900 | Other Vehicular Equipment | 4 | -2001350 | 21-07 30 50 | Site Energy Distribution
G3060 | Site Fuel Distribution | 3 | 0 |  | E1090300 | Food Service Equipment | 4 | -2001350 | 21-07 30 60 | Site Fuel Distribution
G3090 | Liquid and Gas Site Utilities Supplementary Components | 3 | 0 |  | E1090600 | Window Washing Equipment | 4 | -2001350 | 21-07 30 90 | Liquid and Gas Site Utilities Supplementary Components
G4010 | Site Electric Distribution Systems | 3 | 0 |  | E2010 | Fixed Furnishings | 3 |  | 21-07 40 10 | Site Electric Distribution Systems
G4050 | Site Lighting | 3 | 0 |  | E2010500 | Fixed Multiple Seating | 4 | -2000080 | 21-07 40 50 | Site Lighting
G5010 | Site Communications Systems | 3 | 0 |  | E2020400 | Movable Multiple Seating | 4 | -2000080 | 21-07 50 10 | Site Communications Systems
G9010 | Tunnels | 3 | 0 |  | F1010100 | Air Supported Structures | 4 | -2001320 | 21-07 90 10 | Tunnels
A1010.10 | Wall Foundations | 4 |  |  | A1010100 | Footings & Pile Caps | 4 | -2001300 | 21-01 10 10 10 | Wall Foundations
A1010.30 | Column Foundations | 4 |  |  | A1010110 | Strip Footings | 5 | -2001300 | 21-01 10 10 30 | Column Foundations
A1010.90 | Standard Foundation Supplementary Components | 4 |  |  | A1010120 | Spread Footings | 5 | -2001300 | 21-01 10 10 90 | Standard Foundation Supplementary Components
A1020.10 | Driven Piles | 4 |  |  | A1010200 | Foundation Walls | 4 | -2000011 | 21-01 10 20 10 | Driven Piles
A1020.15 | Bored Piles | 4 |  |  | A1010210 | Foundation Walls - CIP | 5 | -2000011 | 21-01 10 20 15 | Bored Piles
A1020.20 | Caissons | 4 |  |  | A1010220 | Foundation Walls - CMU | 5 | -2000011 | 21-01 10 20 20 | Caissons
A1020.30 | Special Foundation Walls | 4 |  |  | A1010230 | Foundation Walls - Wood | 5 | -2000011 | 21-01 10 20 30 | Special Foundation Walls
A1020.40 | Foundation Anchors | 4 |  |  | A1010300 | Perimeter Drainage | 4 | -2001160 | 21-01 10 20 40 | Foundation Anchors
A1020.50 | Underpinning | 4 |  |  | A1010310 | Footing Drains | 5 | -2001160 | 21-01 10 20 50 | Underpinning
A1020.60 | Raft Foundations | 4 |  |  | A1010400 | Perimeter Insulation | 4 | -2000011 | 21-01 10 20 60 | Raft Foundations
A1020.70 | Pile Caps | 4 |  |  | A1010410 | Perimeter Insulation - Rigid | 5 | -2000011 | 21-01 10 20 70 | Pile Caps
A1020.80 | Grade Beams | 4 |  |  | A1020 | Special Foundations | 3 |  | 21-01 10 20 80 | Grade Beams
A2010.10 | Subgrade Enclosure Wall Construction | 4 |  |  | A1020120 | Piles - Precast Concrete | 5 | -2001300 | 21-01 20 10 10 | Subgrade Enclosure Wall Construction
A2010.20 | Subgrade Enclosure Wall Interior Skin | 4 |  |  | A1020130 | Piles - Steel Pipe | 5 | -2001300 | 21-01 20 10 20 | Subgrade Enclosure Wall Interior Skin
A2010.90 | Subgrade Enclosure Wall Supplementary Components | 4 |  |  | A1020140 | Piles - Steel H | 5 | -2001300 | 21-01 20 10 90 | Subgrade Enclosure Wall Supplementary Components
A4090.10 | Perimeter Insulation | 4 |  |  | A1020400 | Underpinning | 4 | -2001300 | 21-01 40 90 10 | Perimeter Insulation
A4090.20 | Vapor Retarder | 4 |  |  | A1020500 | Dewatering | 4 | -2001260 | 21-01 40 90 20 | Vapor Retarder
A4090.30 | Waterproofing | 4 |  |  | A1020600 | Raft Foundations | 4 | -2001300 | 21-01 40 90 30 | Waterproofing
A4090.50 | Mud Slab | 4 |  |  | A1020700 | Pressure Injected Grouting | 4 | -2001300 | 21-01 40 90 50 | Mud Slab
A4090.60 | Subbase Layer | 4 |  |  | A1020710 | Pressure Injected Footings | 5 | -2001300 | 21-01 40 90 60 | Subbase Layer
A6010.10 | Foundation Drainage | 4 |  |  | A1030100 | Standard Slab on Grade | 4 | -2000032 | 21-01 60 10 10 | Foundation Drainage
A6010.20 | Underslab Drainage | 4 |  |  | A1030110 | SOG - Reinforced | 5 | -2000032 | 21-01 60 10 20 | Underslab Drainage
A6020.10 | Radon Mitigation | 4 |  |  | A1030200 | Structural Slab on Grade | 4 | -2000032 | 21-01 60 20 10 | Radon Mitigation
A6020.50 | Methane Mitigation | 4 |  |  | A1030300 | Inclined Slab on Grade | 4 | -2000032 | 21-01 60 20 50 | Methane Mitigation
A9010.10 | Backfill and Compaction | 4 |  |  | A1030600 | Under-Slab Drainage | 4 | -2001160 | 21-01 90 10 10 | Backfill and Compaction
A9030.10 | Anchor Tiebacks | 4 |  |  | A20 | Basement Construction | 2 |  | 21-01 90 30 10 | Anchor Tiebacks
A9030.20 | Cofferdams | 4 |  |  | A2010 | Basement Excavation | 3 |  | 21-01 90 30 20 | Cofferdams
A9030.40 | Cribbing and Walers | 4 |  |  | A2010100 | Excavation for Basements | 4 | -2001300 | 21-01 90 30 40 | Cribbing and Walers
A9030.60 | Ground Freezing | 4 |  |  | A2010110 | Basement Excavation & Backfill | 5 | -2001300 | 21-01 90 30 60 | Ground Freezing
A9030.70 | Slurry Walls | 4 |  |  | A2010200 | Structural Backfill & Compaction | 4 | -2001300 | 21-01 90 30 70 | Slurry Walls
B1010.10 | Floor Structural Frame | 4 |  |  | A2020110 | Basement Walls - CIP | 5 | -2000011 | 21-02 10 10 10 | Floor Structural Frame
B1010.20 | Floor Decks, Slabs, and Toppings | 4 |  |  | A2020120 | Basement Walls - CMU | 5 | -2000011 | 21-02 10 10 20 | Floor Decks, Slabs, and Toppings
B1010.30 | Balcony Floor Construction | 4 |  |  | A2020130 | Basement Walls - Wood | 5 | -2000011 | 21-02 10 10 30 | Balcony Floor Construction
B1010.40 | Mezzanine Floor Construction | 4 |  |  | A2020200 | Moisture Protection | 4 | -2000011 | 21-02 10 10 40 | Mezzanine Floor Construction
B1010.50 | Ramps | 4 |  |  | A2020210 | Foundation Dampproofing | 5 | -2000011 | 21-02 10 10 50 | Ramps
B1010.90 | Floor Construction Supplementary Components | 4 |  |  | A2020300 | Basement Wall Insulation | 4 | -2000011 | 21-02 10 10 90 | Floor Construction Supplementary Components
B1020.10 | Roof Structural Frame | 4 |  |  | A2020400 | Interior Skin | 4 | -2000011 | 21-02 10 20 10 | Roof Structural Frame
B1020.20 | Roof Decks, Slabs, and Sheathing | 4 |  |  | B | Shell | 1 |  | 21-02 10 20 20 | Roof Decks, Slabs, and Sheathing
B1020.30 | Canopy Construction | 4 |  |  | B10 | Superstructure | 2 |  | 21-02 10 20 30 | Canopy Construction
B1020.90 | Roof Construction Supplementary Components | 4 |  |  | B1010 | Floor Construction | 3 |  | 21-02 10 20 90 | Roof Construction Supplementary Components
B1080.10 | Stair Construction | 4 |  |  | B1010200 | Upper Floor Framing - Vertical Elements | 4 | -2001330 | 21-02 10 80 10 | Stair Construction
B1080.30 | Stair Soffits | 4 |  |  | B1010210 | Bearing Walls - CIP | 5 | -2000011 | 21-02 10 80 30 | Stair Soffits
B1080.50 | Stair Railings | 4 |  |  | B1010215 | Bearing Walls - Block | 5 | -2000011 | 21-02 10 80 50 | Stair Railings
B1080.60 | Fire Escapes | 4 |  |  | B1010220 | Bearing Walls - Drywall w/Studs | 5 | -2000011 | 21-02 10 80 60 | Fire Escapes
B1080.70 | Metal Walkways | 4 |  |  | B1010225 | Bearing Walls - Plaster w/Studs | 5 | -2000011 | 21-02 10 80 70 | Metal Walkways
B1080.80 | Ladders | 4 |  |  | B1010240 | Columns - CIP | 5 | -2001330 | 21-02 10 80 80 | Ladders
B2010.10 | Exterior Wall Veneer | 4 |  |  | B1010255 | Columns - Wood | 5 | -2001330 | 21-02 20 10 10 | Exterior Wall Veneer
B2010.20 | Exterior Wall Construction | 4 |  |  | B1010300 | Upper Floor Framing - Horizontal Elements | 4 | -2001320 | 21-02 20 10 20 | Exterior Wall Construction
B2010.30 | Exterior Wall Interior Skin | 4 |  |  | B1010310 | Beams - CIP | 5 | -2001320 | 21-02 20 10 30 | Exterior Wall Interior Skin
B2010.40 | Fabricated Exterior Wall Assemblies | 4 |  |  | B1010320 | Beams - Precast | 5 | -2001320 | 21-02 20 10 40 | Fabricated Exterior Wall Assemblies
B2010.50 | Parapets | 4 |  |  | B1010325 | Beams - Precast Double T | 5 | -2001320 | 21-02 20 10 50 | Parapets
B2010.60 | Equipment Screens | 4 |  |  | B1010330 | Beams - Steel | 5 | -2001320 | 21-02 20 10 60 | Equipment Screens
B2010.80 | Exterior Wall Supplementary Components | 4 |  |  | B1010340 | Beams - Wood (Dimensional Lumber) | 5 | -2001320 | 21-02 20 10 80 | Exterior Wall Supplementary Components
B2010.90 | Exterior Wall Opening Supplementary Components | 4 |  |  | B1010345 | Beams - Wood (Laminated) | 5 | -2001320 | 21-02 20 10 90 | Exterior Wall Opening Supplementary Components
B2020.10 | Exterior Operating Windows | 4 |  |  | B1010355 | Joists - Wood (Dimensional Lumber) | 5 | -2001320 | 21-02 20 20 10 | Exterior Operating Windows
B2020.20 | Exterior Fixed Windows | 4 |  |  | B1010358 | Joists - Wood (Manufactured) | 5 | -2001320 | 21-02 20 20 20 | Exterior Fixed Windows
B2020.30 | Exterior Window Wall | 4 |  |  | B1010370 | Deck - Metal | 5 | -2000032 | 21-02 20 20 30 | Exterior Window Wall
B2020.50 | Exterior Special Function Windows | 4 |  |  | B1010375 | Deck - Wood | 5 | -2000032 | 21-02 20 20 50 | Exterior Special Function Windows
B2050.10 | Exterior Entrance Doors | 4 |  |  | B1010400 | Upper Floor Framing - Systems | 4 | -2001320 | 21-02 20 50 10 | Exterior Entrance Doors
B2050.20 | Exterior Utility Doors | 4 |  |  | B1010410 | CIP Slabs - One Way | 5 | -2000032 | 21-02 20 50 20 | Exterior Utility Doors
B2050.30 | Exterior Oversize Doors | 4 |  |  | B1010412 | CIP Slabs - Flat Plate | 5 | -2000032 | 21-02 20 50 30 | Exterior Oversize Doors
B2050.40 | Exterior Special Function Doors | 4 |  |  | B1010414 | CIP Slabs - Flat Plate w/Drop Panels | 5 | -2000032 | 21-02 20 50 40 | Exterior Special Function Doors
B2050.60 | Exterior Grilles | 4 |  |  | B1010416 | CIP Slabs - Multispan Joist | 5 | -2000032 | 21-02 20 50 60 | Exterior Grilles
B2050.70 | Exterior Gates | 4 |  |  | B1010418 | CIP Slabs - Waffle | 5 | -2000032 | 21-02 20 50 70 | Exterior Gates
B2050.90 | Exterior Door Supplementary Components | 4 |  |  | B1010420 | CIP Beam & Slab - One Way | 5 | -2001320 | 21-02 20 50 90 | Exterior Door Supplementary Components
B2070.10 | Exterior Louvers | 4 |  |  | B1010430 | Composite Beam & Slab | 5 | -2001320 | 21-02 20 70 10 | Exterior Louvers
B2070.50 | Exterior Vents | 4 |  |  | B1010432 | Composite Beam, Deck & Slab | 5 | -2001320 | 21-02 20 70 50 | Exterior Vents
B2080.10 | Exterior Fixed Grilles and Screens | 4 |  |  | B1010440 | Precast Beams w/ Precast Planks | 5 | -2001320 | 21-02 20 80 10 | Exterior Fixed Grilles and Screens
B2080.30 | Exterior Opening Protection Devices | 4 |  |  | B1010442 | Precast Beams w/Precast Double T | 5 | -2001320 | 21-02 20 80 30 | Exterior Opening Protection Devices
B2080.50 | Exterior Balcony Walls and Railings | 4 |  |  | B1010460 | Steel Girders w/ Steel Beams | 5 | -2001320 | 21-02 20 80 50 | Exterior Balcony Walls and Railings
B2080.70 | Exterior Fabrications | 4 |  |  | B1010462 | Steel Beams w/ Steel Joists | 5 | -2001320 | 21-02 20 80 70 | Exterior Fabrications
B2080.80 | Bird Control Devices | 4 |  |  | B1010464 | Joist Girders w/ Steel Joists | 5 | -2001320 | 21-02 20 80 80 | Bird Control Devices
B3010.10 | Steep Slope Roofing | 4 |  |  | B1010500 | Balcony Floor Construction | 4 | -2000032 | 21-02 30 10 10 | Steep Slope Roofing
B3010.50 | Low-Slope Roofing | 4 |  |  | B1010600 | Ramps | 4 | -2000180 | 21-02 30 10 50 | Low-Slope Roofing
B3010.70 | Canopy Roofing | 4 |  |  | B1010700 | Exterior Stairs & Fire Escapes | 4 | -2000120 | 21-02 30 10 70 | Canopy Roofing
B3010.90 | Roofing Supplementary Components | 4 |  |  | B1010800 | Floor Raceway Systems | 4 | -2000032 | 21-02 30 10 90 | Roofing Supplementary Components
B3020.10 | Roof Accessories | 4 |  |  | B1010910 | Steel Beam Fireproofing | 5 | -2001320 | 21-02 30 20 10 | Roof Accessories
B3020.30 | Roof Specialties | 4 |  |  | B1010920 | Steel Column Fireproofing | 5 | -2001320 | 21-02 30 20 30 | Roof Specialties
B3020.70 | Rainwater Management | 4 |  |  | B1020 | Roof Construction | 3 |  | 21-02 30 20 70 | Rainwater Management
B3040.10 | Traffic Bearing Coatings | 4 |  |  | B1020110 | Bearing Walls - CIP | 5 | -2000011 | 21-02 30 40 10 | Traffic Bearing Coatings
B3040.30 | Horizontal Waterproofing Membrane | 4 |  |  | B1020115 | Bearing Walls - Block | 5 | -2000011 | 21-02 30 40 30 | Horizontal Waterproofing Membrane
B3040.50 | Wear Surfaces | 4 |  |  | B1020120 | Bearing Walls - Drywall w/Studs | 5 | -2000011 | 21-02 30 40 50 | Wear Surfaces
B3040.90 | Horizontal Enclosure Supplementary Components | 4 |  |  | B1020125 | Bearing Walls - Plaster w/Studs | 5 | -2000011 | 21-02 30 40 90 | Horizontal Enclosure Supplementary Components
B306010 | Roof Windows and Skylights | 4 |  |  | B1020145 | Columns - Precast | 5 | -2001330 | 21-02 30 60 10 | Roof Windows and Skylights
B3060.50 | Vents and Hatches | 4 |  |  | B1020150 | Columns - Steel | 5 | -2001330 | 21-02 30 60 50 | Vents and Hatches
B3060.90 | Horizontal Opening Supplementary Components | 4 |  |  | B1020155 | Columns - Wood | 5 | -2001330 | 21-02 30 60 90 | Horizontal Opening Supplementary Components
B3080.10 | Exterior Ceilings | 4 |  |  | B1020210 | Beams - CIP | 5 | -2001320 | 21-02 30 80 10 | Exterior Ceilings
B3080.20 | Exterior Soffits | 4 |  |  | B1020220 | Beams - Precast | 5 | -2001320 | 21-02 30 80 20 | Exterior Soffits
B3080.30 | Exterior Bulkheads | 4 |  |  | B1020225 | Beams - Precast Double T | 5 | -2001320 | 21-02 30 80 30 | Exterior Bulkheads
C1010.10 | Interior Fixed Partitions | 4 |  |  | B1020250 | Joists - Steel | 5 | -2001320 | 21-03 10 10 10 | Interior Fixed Partitions
C1010.20 | Interior Glazed Partitions | 4 |  |  | B1020255 | Joists - Wood (Dimensional Lumber) | 5 | -2001320 | 21-03 10 10 20 | Interior Glazed Partitions
C1010.40 | Interior Demountable Partitions | 4 |  |  | B1020258 | Joists - Wood (Manufactured) | 5 | -2001320 | 21-03 10 10 40 | Interior Demountable Partitions
C1010.50 | Interior Operable Partitions | 4 |  |  | B1020260 | Deck - Metal | 5 | -2000035 | 21-03 10 10 50 | Interior Operable Partitions
C1010.70 | Interior Screens | 4 |  |  | B1020265 | Deck - Wood | 5 | -2000035 | 21-03 10 10 70 | Interior Screens
C1010.90 | Interior Partition Supplementary Components | 4 |  |  | B1020270 | Planks - Precast | 5 | -2000035 | 21-03 10 10 90 | Interior Partition Supplementary Components
C1020.10 | Interior Operating Windows | 4 |  |  | B1020310 | CIP Slabs - One Way | 5 | -2000035 | 21-03 10 20 10 | Interior Operating Windows
C1020.20 | Interior Fixed Windows | 4 |  |  | B1020312 | CIP Slabs - Flat Plate | 5 | -2000035 | 21-03 10 20 20 | Interior Fixed Windows
C1020.50 | Interior Special Function Windows | 4 |  |  | B1020314 | CIP Slabs - Flat Plate w/Drop Panels | 5 | -2000035 | 21-03 10 20 50 | Interior Special Function Windows
C1020.90 | Interior Window Supplementary Components | 4 |  |  | B1020316 | CIP Slabs - Multispan Joist | 5 | -2000035 | 21-03 10 20 90 | Interior Window Supplementary Components
C1030.10 | Interior Swinging Doors | 4 |  |  | B1020320 | CIP Beam & Slab - One Way | 5 | -2001320 | 21-03 10 30 10 | Interior Swinging Doors
C1030.20 | Interior Entrance Doors | 4 |  |  | B1020322 | CIP Beam & Slab - Two Way | 5 | -2001320 | 21-03 10 30 20 | Interior Entrance Doors
C1030.25 | Interior Sliding Doors | 4 |  |  | B1020330 | Composite Beam & Slab | 5 | -2001320 | 21-03 10 30 25 | Interior Sliding Doors
C1030.30 | Interior Folding Doors | 4 |  |  | B1020332 | Composite Beam, Deck & Slab | 5 | -2001320 | 21-03 10 30 30 | Interior Folding Doors
C1030.40 | Interior Coiling Doors | 4 |  |  | B1020334 | W Shape Composite Deck & Slab | 5 | -2001320 | 21-03 10 30 40 | Interior Coiling Doors
C1030.50 | Interior Panel Doors | 4 |  |  | B1020340 | Precast Beams w/ Precast Planks | 5 | -2001320 | 21-03 10 30 50 | Interior Panel Doors
C1030.70 | Interior Special Function Doors | 4 |  |  | B1020342 | Precast Beams w/Precast Double T | 5 | -2001320 | 21-03 10 30 70 | Interior Special Function Doors
C1030.80 | Interior Access Doors and Panels | 4 |  |  | B1020360 | Steel Girders w/ Steel Beams | 5 | -2001320 | 21-03 10 30 80 | Interior Access Doors and Panels
C1030.90 | Interior Door Supplementary Components | 4 |  |  | B1020362 | Steel Beams w/ Steel Joists | 5 | -2001320 | 21-03 10 30 90 | Interior Door Supplementary Components
C1040.10 | Interior Grilles | 4 |  |  | B1020370 | Steel Light Gauge Floor System | 5 | -2001320 | 21-03 10 40 10 | Interior Grilles
C1040.50 | Interior Gates | 4 |  |  | B1020380 | Wood Beams w/ Wood Joists | 5 | -2001320 | 21-03 10 40 50 | Interior Gates
C1060.10 | Access Flooring | 4 |  |  | B1020400 | Pitched Roof Construction | 4 | -2000035 | 21-03 10 60 10 | Access Flooring
C1060.30 | Platform/Stage Floors | 4 |  |  | B1020500 | Vaulted Roof Construction | 4 | -2000035 | 21-03 10 60 30 | Platform/Stage Floors
C1070.10 | Acoustical Suspended Ceilings | 4 |  |  | B1020700 | Fabric (Tensile) Roof Construction | 4 | -2000035 | 21-03 10 70 10 | Acoustical Suspended Ceilings
C1070.20 | Suspended Plaster and Gypsum Board Ceilings | 4 |  |  | B1020800 | Canopies | 4 | -2000035 | 21-03 10 70 20 | Suspended Plaster and Gypsum Board Ceilings
C1070.50 | Specialty Suspended Ceilings | 4 |  |  | B1020900 | Fireproofing - Roof Construction | 4 | -2000035 | 21-03 10 70 50 | Specialty Suspended Ceilings
C1070.70 | Special Function Suspended Ceilings | 4 |  |  | B1020910 | Steel Beam Fireproofing | 5 | -2000035 | 21-03 10 70 70 | Special Function Suspended Ceilings
C1070.90 | Ceiling Suspension Components | 4 |  |  | B1020920 | Steel Column Fireproofing | 5 | -2000035 | 21-03 10 70 90 | Ceiling Suspension Components
C1090.10 | Interior Railings and Handrails | 4 |  |  | B2010 | Exterior Walls | 3 |  | 21-03 10 90 10 | Interior Railings and Handrails
C1090.15 | Interior Louvers | 4 |  |  | B2010100 | Exterior Wall Construction | 4 | -2000011 | 21-03 10 90 15 | Interior Louvers
C1090.20 | Information Specialties | 4 |  |  | B2010110 | Ext. Wall - CIP | 5 | -2000011 | 21-03 10 90 20 | Information Specialties
C1090.25 | Compartments and Cubicles | 4 |  |  | B2010120 | Ext. Wall - Precast | 5 | -2000011 | 21-03 10 90 25 | Compartments and Cubicles
C1090.30 | Service Walls | 4 |  |  | B2010125 | Ext. Wall - Precast Lintels & Specialties | 5 | -2000011 | 21-03 10 90 30 | Service Walls
C1090.35 | Wall and Door Protection | 4 |  |  | B2010130 | Ext. Wall - Tilt-up | 5 | -2000011 | 21-03 10 90 35 | Wall and Door Protection
C1090.40 | Toilet, Bath, and Laundry Accessories | 4 |  |  | B2010140 | Ext. Wall - CMU | 5 | -2000011 | 21-03 10 90 40 | Toilet, Bath, and Laundry Accessories
C1090.45 | Interior Gas Lighting | 4 |  |  | B2010142 | Ext. Wall - CMU Cavity | 5 | -2000011 | 21-03 10 90 45 | Interior Gas Lighting
C1090.50 | Fireplaces and Stoves | 4 |  |  | B2010144 | Ext. Wall - CMU Composite | 5 | -2000011 | 21-03 10 90 50 | Fireplaces and Stoves
C1090.60 | Safety Specialties | 4 |  |  | B2010146 | Ext. Wall - CMU Lintels & Specialties | 5 | -2000011 | 21-03 10 90 60 | Safety Specialties
C1090.70 | Storage Specialties | 4 |  |  | B2010148 | Ext. Wall - Glass Block | 5 | -2000011 | 21-03 10 90 70 | Storage Specialties
C1090.90 | Other Interior Specialties | 4 |  |  | B2010150 | Ext. Wall - Brick (Single Wythe) | 5 | -2000011 | 21-03 10 90 90 | Other Interior Specialties
C2010.10 | Tile Wall Finish | 4 |  |  | B2010156 | Ext. Wall - Brick Composite | 5 | -2000011 | 21-03 20 10 10 | Tile Wall Finish
C2010.20 | Wall Paneling | 4 |  |  | B2010158 | Ext. Wall - Brick Veneer w/ Stud | 5 | -2000011 | 21-03 20 10 20 | Wall Paneling
C2010.30 | Wall Coverings | 4 |  |  | B2010160 | Ext. Wall - Stone Veneer w/ Stud | 5 | -2000011 | 21-03 20 10 30 | Wall Coverings
C2010.35 | Wall Carpeting | 4 |  |  | B2010170 | Ext. Wall - Metal Siding Supports | 5 | -2000011 | 21-03 20 10 35 | Wall Carpeting
C2010.50 | Stone Facing | 4 |  |  | B2010175 | Ext. Wall - Metal Siding Panels | 5 | -2000011 | 21-03 20 10 50 | Stone Facing
C2010.60 | Special Wall Surfacing | 4 |  |  | B2010180 | Ext. Wall - Wood Stud w/ Siding & Shingles | 5 | -2000011 | 21-03 20 10 60 | Special Wall Surfacing
C2010.70 | Wall Painting and Coating | 4 |  |  | B2010185 | Ext. Wall - Wood Stud w/ Stucco | 5 | -2000011 | 21-03 20 10 70 | Wall Painting and Coating
C2010.80 | Acoustical Wall Treatment | 4 |  |  | B2010200 | Parapets | 4 | -2000011 | 21-03 20 10 80 | Acoustical Wall Treatment
C2010.90 | Wall Finish Supplementary Components | 4 |  |  | B2010300 | Exterior Louvers, Screens & Fencing | 4 | -2000014 | 21-03 20 10 90 | Wall Finish Supplementary Components
C2030.10 | Flooring Treatment | 4 |  |  | B2010600 | Exterior Soffits | 4 | -2000035 | 21-03 20 30 10 | Flooring Treatment
C2030.20 | Tile Flooring | 4 |  |  | B2020 | Exterior Windows | 3 |  | 21-03 20 30 20 | Tile Flooring
C2030.30 | Specialty Flooring | 4 |  |  | B2020100 | Windows | 4 | -2000014 | 21-03 20 30 30 | Specialty Flooring
C2030.40 | Masonry Flooring | 4 |  |  | B2020110 | Windows - Aluminum | 5 | -2000014 | 21-03 20 30 40 | Masonry Flooring
C2030.45 | Wood Flooring | 4 |  |  | B2020120 | Windows - Steel | 5 | -2000014 | 21-03 20 30 45 | Wood Flooring
C2030.50 | Resilient Flooring | 4 |  |  | B2020130 | Windows - Wood | 5 | -2000014 | 21-03 20 30 50 | Resilient Flooring
C2030.60 | Terrazzo Flooring | 4 |  |  | B2020200 | Curtain Walls | 4 | -2000011 | 21-03 20 30 60 | Terrazzo Flooring
C2030.70 | Fluid-Applied Flooring | 4 |  |  | B2020210 | Curtain Walls - Framing | 5 | -2000171 | 21-03 20 30 70 | Fluid-Applied Flooring
C2030.75 | Carpeting | 4 |  |  | B2020220 | Curtain Walls - Panels | 5 | -2000170 | 21-03 20 30 75 | Carpeting
C2030.80 | Athletic Flooring | 4 |  |  | B2020300 | Storefronts | 4 | -2000170 | 21-03 20 30 80 | Athletic Flooring
C2030.85 | Entrance Flooring | 4 |  |  | B2020400 | Screened Openings | 4 | -2000014 | 21-03 20 30 85 | Entrance Flooring
C2030.90 | Flooring Supplementary Components | 4 |  |  | B2030 | Exterior Doors | 3 |  | 21-03 20 30 90 | Flooring Supplementary Components
C2040.20 | Tile Stair Finish | 4 |  |  | B2030110 | Exterior Glazed Doors - Aluminum | 5 | -2000023 | 21-03 20 40 20 | Tile Stair Finish
C2040.40 | Masonry Stair Finish | 4 |  |  | B2030120 | Exterior Glazed Doors - Steel | 5 | -2000023 | 21-03 20 40 40 | Masonry Stair Finish
C2040.45 | Wood Stair Finish | 4 |  |  | B2030130 | Exterior Glazed Doors - Wood | 5 | -2000023 | 21-03 20 40 45 | Wood Stair Finish
C2040.50 | Resilient Stair Finish | 4 |  |  | B2030200 | Solid Exterior Doors | 4 | -2000023 | 21-03 20 40 50 | Resilient Stair Finish
C2040.60 | Terrazzo Stair Finish | 4 |  |  | B2030210 | Exterior Solid Doors - Aluminum | 5 | -2000023 | 21-03 20 40 60 | Terrazzo Stair Finish
C2040.75 | Carpeted Stair Finish | 4 |  |  | B2030220 | Exterior Solid Doors - Steel | 5 | -2000023 | 21-03 20 40 75 | Carpeted Stair Finish
C2050.10 | Plaster and Gypsum Board Finish | 4 |  |  | B2030300 | Revolving Doors | 4 | -2000023 | 21-03 20 50 10 | Plaster and Gypsum Board Finish
C2050.20 | Ceiling Paneling | 4 |  |  | B2030400 | Overhead Doors & Roll-up Grilles | 4 | -2000023 | 21-03 20 50 20 | Ceiling Paneling
C2050.70 | Ceiling Painting and Coating | 4 |  |  | B2030410 | Overhead Doors | 5 | -2000023 | 21-03 20 50 70 | Ceiling Painting and Coating
C2050.80 | Acoustical Ceiling Treatment | 4 |  |  | B2030420 | Roll-up Grilles | 5 | -2000023 | 21-03 20 50 80 | Acoustical Ceiling Treatment
C2050.90 | Ceiling Finish Supplementary Components | 4 |  |  | B2030500 | Door Wall Opening Elements | 4 | -2000023 | 21-03 20 50 90 | Ceiling Finish Supplementary Components
D1010.10 | Elevators | 4 |  |  | B3010100 | Roof Finishes | 4 | -2000035 | 21-04 10 10 10 | Elevators
D1010.20 | Lifts | 4 |  |  | B3010110 | Roofing - Built-up | 5 | -2000035 | 21-04 10 10 20 | Lifts
D1010.30 | Escalators | 4 |  |  | B3010120 | Roofing - Single Ply Membrane | 5 | -2000035 | 21-04 10 10 30 | Escalators
D1010.50 | Dumbwaiters | 4 |  |  | B3010130 | Roofing - Preformed Metal | 5 | -2000035 | 21-04 10 10 50 | Dumbwaiters
D1010.60 | Moving Ramps | 4 |  |  | B3010140 | Roofing - Formed Metal | 5 | -2000035 | 21-04 10 10 60 | Moving Ramps
D1030.10 | Moving Walks | 4 |  |  | B3010200 | Traffic Toppings & Paving Membranes | 4 | -2000035 | 21-04 10 30 10 | Moving Walks
D1030.30 | Turntables | 4 |  |  | B3010300 | Roof Insulation & Fill | 4 | -2000035 | 21-04 10 30 30 | Turntables
D1030.50 | Passenger Loading Bridges | 4 |  |  | B3010310 | Roof Insulation - Rigid | 5 | -2000035 | 21-04 10 30 50 | Passenger Loading Bridges
D1030.70 | People Movers | 4 |  |  | B3010400 | Roof Flashing & Trim | 4 | -2000035 | 21-04 10 30 70 | People Movers
D1050.10 | Cranes | 4 |  |  | B3010420 | Roof Edges | 5 | -2000035 | 21-04 10 50 10 | Cranes
D1050.20 | Hoists | 4 |  |  | B3010430 | Roof Flashing | 5 | -2000035 | 21-04 10 50 20 | Hoists
D1050.30 | Derricks | 4 |  |  | B3010500 | Roof Eaves & Soffits | 4 | -2000035 | 21-04 10 50 30 | Derricks
D1050.40 | Conveyors | 4 |  |  | B3010600 | Gutters & Downspouts | 4 | -2000035 | 21-04 10 50 40 | Conveyors
D1050.50 | Baggage Handling Equipment | 4 |  |  | B3010610 | Gutters | 5 | -2000035 | 21-04 10 50 50 | Baggage Handling Equipment
D1050.60 | Chutes | 4 |  |  | B3010620 | Downspouts | 5 | -2000035 | 21-04 10 50 60 | Chutes
D1050.70 | Pneumatic Tube Systems | 4 |  |  | B3020 | Roof Openings | 3 |  | 21-04 10 50 70 | Pneumatic Tube Systems
D1080.10 | Suspended Scaffolding | 4 |  |  | B3020110 | Skylights | 5 | -2000014 | 21-04 10 80 10 | Suspended Scaffolding
D1080.20 | Rope Climbers | 4 |  |  | B3020200 | Roof Hatches | 4 | -2000014 | 21-04 10 80 20 | Rope Climbers
D1080.30 | Elevating Platforms | 4 |  |  | B3020210 | Roof Hatches | 5 | -2000014 | 21-04 10 80 30 | Elevating Platforms
D1080.40 | Powered Scaffolding | 4 |  |  | B3020220 | Smoke Vents | 5 | -2000014 | 21-04 10 80 40 | Powered Scaffolding
D1080.50 | Building Envelope Access | 4 |  |  | B3020230 | Roof Accessories | 5 | -2000014 | 21-04 10 80 50 | Building Envelope Access
D2010.10 | Facility Potable-Water Storage Tanks | 4 |  |  | C10 | Interior Construction | 2 |  | 21-04 20 10 10 | Facility Potable-Water Storage Tanks
D2010.20 | Domestic Water Equipment | 4 |  |  | C1010 | Partitions | 3 |  | 21-04 20 10 20 | Domestic Water Equipment
D2010.40 | Domestic Water Piping | 4 |  |  | C1010100 | Fixed Partitions | 4 | -2000011 | 21-04 20 10 40 | Domestic Water Piping
D2010.60 | Plumbing Fixtures | 4 |  |  | C1010110 | Partitions - Brick, Solid | 5 | -2000011 | 21-04 20 10 60 | Plumbing Fixtures
D2010.90 | Domestic Water Distribution Supplementary Components | 4 |  |  | C1010115 | Partitions - Brick Veneer w/ Stud | 5 | -2000011 | 21-04 20 10 90 | Domestic Water Distribution Supplementary Components
D2020.10 | Sanitary Sewerage Equipment | 4 |  |  | C1010120 | Partitions - CMU | 5 | -2000011 | 21-04 20 20 10 | Sanitary Sewerage Equipment
D2020.30 | Sanitary Sewerage Piping | 4 |  |  | C1010130 | Partitions - Glass Block | 5 | -2000011 | 21-04 20 20 30 | Sanitary Sewerage Piping
D2020.90 | Sanitary Drainage Supplementary Components | 4 |  |  | C1010135 | Partitions - Tile | 5 | -2000011 | 21-04 20 20 90 | Sanitary Drainage Supplementary Components
D2030.10 | Stormwater Drainage Equipment | 4 |  |  | C1010145 | Partitions - Drywall w/ Metal Stud | 5 | -2000011 | 21-04 20 30 10 | Stormwater Drainage Equipment
D2030.20 | Stormwater Drainage Piping | 4 |  |  | C1010150 | Partitions - Plaster w/ Wood Stud | 5 | -2000011 | 21-04 20 30 20 | Stormwater Drainage Piping
D2030.30 | Facility Stormwater Drains | 4 |  |  | C1010155 | Partitions - Plaster w/ Metal Stud | 5 | -2000011 | 21-04 20 30 30 | Facility Stormwater Drains
D2030.60 | Gray Water Systems | 4 |  |  | C1010180 | Partition Components - Wood Framing | 5 | -2000011 | 21-04 20 30 60 | Gray Water Systems
D2030.90 | Building Support Plumbing System Supplementary Components | 4 |  |  | C1010185 | Partition Components - Metal Framing | 5 | -2000011 | 21-04 20 30 90 | Building Support Plumbing System Supplementary Components
D2060.10 | Compressed-Air Systems | 4 |  |  | C1010200 | Demountable Partitions | 4 | -2000011 | 21-04 20 60 10 | Compressed-Air Systems
D2060.20 | Vacuum Systems | 4 |  |  | C1010210 | Partitions- Demountable, Drywall | 5 | -2000011 | 21-04 20 60 20 | Vacuum Systems
D2060.30 | Gas Systems | 4 |  |  | C1010300 | Retractable Partitions | 4 | -2000011 | 21-04 20 60 30 | Gas Systems
D2060.40 | Chemical-Waste Systems | 4 |  |  | C1010310 | Partitions - Folding | 5 | -2000011 | 21-04 20 60 40 | Chemical-Waste Systems
D2060.50 | Processed Water Systems | 4 |  |  | C1010400 | Site Built Toilet Partitions | 4 | -2001350 | 21-04 20 60 50 | Processed Water Systems
D2060.90 | Process Support Plumbing System Supplementary Components | 4 |  |  | C1010500 | Site Built Compartments & Cubicles | 4 | -2001350 | 21-04 20 60 90 | Process Support Plumbing System Supplementary Components
D3010.10 | Fuel Piping | 4 |  |  | C1010710 | Interior Glazed Openings | 5 | -2000014 | 21-04 30 10 10 | Fuel Piping
D3010.30 | Fuel Pumps | 4 |  |  | C1020 | Interior Doors | 3 |  | 21-04 30 10 30 | Fuel Pumps
D3010.50 | Fuel Storage Tanks | 4 |  |  | C1020100 | Interior Doors | 4 | -2000023 | 21-04 30 10 50 | Fuel Storage Tanks
D3020.10 | Heat Generation | 4 |  |  | C1020120 | Interior Doors - Wood | 5 | -2000023 | 21-04 30 20 10 | Heat Generation
D3020.30 | Thermal Heat Storage | 4 |  |  | C1020200 | Interior Door Frames | 4 | -2000023 | 21-04 30 20 30 | Thermal Heat Storage
D3020.70 | Decentralized Heating Equipment | 4 |  |  | C1020210 | Interior Door Frames - Metal | 5 | -2000023 | 21-04 30 20 70 | Decentralized Heating Equipment
D3020.90 | Heating System Supplementary Components | 4 |  |  | C1020220 | Interior Door Frames - Wood | 5 | -2000023 | 21-04 30 20 90 | Heating System Supplementary Components
D3030.10 | Central Cooling | 4 |  |  | C1020310 | Interior Metal Doors with Metal Frames | 5 | -2000023 | 21-04 30 30 10 | Central Cooling
D3030.30 | Evaporative Air-Cooling | 4 |  |  | C1020320 | Interior Wood Doors with Metal Frames | 5 | -2000023 | 21-04 30 30 30 | Evaporative Air-Cooling
D3030.50 | Thermal Cooling Storage | 4 |  |  | C1020330 | Interior Wood Doors with Wood Frames | 5 | -2000023 | 21-04 30 30 50 | Thermal Cooling Storage
D3030.70 | Decentralized Cooling | 4 |  |  | C1020400 | Interior Door Hardware | 4 | -2000023 | 21-04 30 30 70 | Decentralized Cooling
D3030.90 | Cooling System Supplementary Components | 4 |  |  | C1020410 | Door Hardware | 5 | -2000023 | 21-04 30 30 90 | Cooling System Supplementary Components
D3050.10 | Facility Hydronic Distribution | 4 |  |  | C1020600 | Interior Door Sidelights & Transoms | 4 | -2000023 | 21-04 30 50 10 | Facility Hydronic Distribution
D3050.30 | Facility Steam Distribution | 4 |  |  | C1020700 | Interior Hatches & Access Doors | 4 | -2000023 | 21-04 30 50 30 | Facility Steam Distribution
D3050.50 | HVAC Air Distribution | 4 |  |  | C1030 | Fittings | 3 |  | 21-04 30 50 50 | HVAC Air Distribution
D3050.90 | Facility Distribution Systems Supplementary Components | 4 |  |  | C1030100 | Fabricated Compartments & Cubicles | 4 | -2001350 | 21-04 30 50 90 | Facility Distribution Systems Supplementary Components
D3060.10 | Supply Air | 4 |  |  | C1030120 | Telephone Enclosures | 5 | -2001350 | 21-04 30 60 10 | Supply Air
D3060.20 | Return Air | 4 |  |  | C1030200 | Bath & Toilet Accessories | 4 | -2001350 | 21-04 30 60 20 | Return Air
D3060.30 | Exhaust Air | 4 |  |  | C1030210 | Bath & Toilet Accessories - Commercial | 5 | -2001160 | 21-04 30 60 30 | Exhaust Air
D3060.40 | Outside Air | 4 |  |  | C1030220 | Bath & Toilet Accessories - Residential | 5 | -2001160 | 21-04 30 60 40 | Outside Air
D3060.60 | Air-to-Air Energy Recovery | 4 |  |  | C1030230 | Hospital Curtains | 5 | -2001350 | 21-04 30 60 60 | Air-to-Air Energy Recovery
D3060.70 | HVAC Air Cleaning | 4 |  |  | C1030300 | Storage Specialties | 4 | -2001350 | 21-04 30 60 70 | HVAC Air Cleaning
D3060.90 | Ventilation Supplementary Components | 4 |  |  | C1030310 | Lockers | 5 | -2001350 | 21-04 30 60 90 | Ventilation Supplementary Components
D3070.10 | Snow Melting | 4 |  |  | C1030330 | Parts Bins | 5 | -2001350 | 21-04 30 70 10 | Snow Melting
D4010.10 | Water-Based Fire-Suppression | 4 |  |  | C1030500 | Identifying/Visual Aid Specialties | 4 | -2001350 | 21-04 40 10 10 | Water-Based Fire-Suppression
D4010.50 | Fire-Extinguishing | 4 |  |  | C1030510 | Signs | 5 | -2001350 | 21-04 40 10 50 | Fire-Extinguishing
D4010.90 | Fire Suppression Supplementary Components | 4 |  |  | C1030520 | Building Directory Boards | 5 | -2001350 | 21-04 40 10 90 | Fire Suppression Supplementary Components
D4030 | Fire Protection Specialties | 4 |  |  | C1030530 | Bulletin Boards | 5 | -2001350 | 21-04 40 30 | Fire Protection Specialties
D4030.10 | Fire Protection Cabinets | 4 |  |  | C1030540 | Chalkboards & Whiteboards | 5 | -2001350 | 21-04 40 30 10 | Fire Protection Cabinets
D4030.30 | Fire Extinguishers | 4 |  |  | C1030600 | Internal Traffic Protection Aids | 4 | -2001350 | 21-04 40 30 30 | Fire Extinguishers
D4030.50 | Breathing Air Replenishment Systems | 4 |  |  | C1030610 | Turnstiles | 5 | -2001350 | 21-04 40 30 50 | Breathing Air Replenishment Systems
D4030.70 | Fire Extinguisher Accessories | 4 |  |  | C1030700 | Integrated Appurtenances | 4 | -2001350 | 21-04 40 30 70 | Fire Extinguisher Accessories
D5010.10 | Packaged Generator Assemblies | 4 |  |  | C20 | Stairs | 2 |  | 21-04 50 10 10 | Packaged Generator Assemblies
D5010.20 | Battery Equipment | 4 |  |  | C2010 | Stair Construction | 3 |  | 21-04 50 10 20 | Battery Equipment
D5010.30 | Photovoltaic Collectors | 4 |  |  | C2010100 | Regular Stairs | 4 | -2000120 | 21-04 50 10 30 | Photovoltaic Collectors
D5010.40 | Fuel Cells | 4 |  |  | C2010110 | Stairs - CIP | 5 | -2000120 | 21-04 50 10 40 | Fuel Cells
D5010.60 | Power Filtering and Conditioning | 4 |  |  | C2010120 | Stairs - Precast | 5 | -2000120 | 21-04 50 10 60 | Power Filtering and Conditioning
D5010.70 | Transfer Switches | 4 |  |  | C2010130 | Stairs - Steel | 5 | -2000120 | 21-04 50 10 70 | Transfer Switches
D5010.90 | Facility Power Generation Supplementary Components | 4 |  |  | C2010140 | Stairs - Wood | 5 | -2000120 | 21-04 50 10 90 | Facility Power Generation Supplementary Components
D5020.10 | Electrical Service | 4 |  |  | C2010300 | Spiral Stairs | 4 | -2000120 | 21-04 50 20 10 | Electrical Service
D5020.30 | Power Distribution | 4 |  |  | C2010310 | Spiral Stairs - Metal | 5 | -2000120 | 21-04 50 20 30 | Power Distribution
D5020.70 | Facility Grounding | 4 |  |  | C2010320 | Spiral Stairs - Wood | 5 | -2000120 | 21-04 50 20 70 | Facility Grounding
D5020.90 | Electrical Service and Distribution Supplementary Components | 4 |  |  | C2010400 | Stair Handrails/Balustrades | 4 | -2000126 | 21-04 50 20 90 | Electrical Service and Distribution Supplementary Components
D5030.10 | Branch Wiring System | 4 |  |  | C2020100 | Stair, Tread & Landing Finishes | 4 | -2000120 | 21-04 50 30 10 | Branch Wiring System
D5030.50 | Wiring Devices | 4 |  |  | C2020200 | Stair Soffit Finishes | 4 | -2000120 | 21-04 50 30 50 | Wiring Devices
D5030.90 | General Purpose Electrical Power Supplementary Components | 4 |  |  | C2020300 | Stair Handrail & Balustrade Finishes | 4 | -2000126 | 21-04 50 30 90 | General Purpose Electrical Power Supplementary Components
D5040.10 | Lighting Control | 4 |  |  | C3010 | Wall Finishes | 3 |  | 21-04 50 40 10 | Lighting Control
D5040.20 | Branch Wiring for Lighting | 4 |  |  | C3010100 | Wall Finishes | 4 | -2000011 | 21-04 50 40 20 | Branch Wiring for Lighting
D5040.50 | Lighting Fixtures | 4 |  |  | C3010110 | Wall Finishes - Paint | 5 | -2000011 | 21-04 50 40 50 | Lighting Fixtures
D5040.90 | Lighting Supplementary Components | 4 |  |  | C3010120 | Wall Finishes - Coatings | 5 | -2000011 | 21-04 50 40 90 | Lighting Supplementary Components
D5080.10 | Lightning Protection | 4 |  |  | C3010140 | Wall Finishes - Paneling | 5 | -2000011 | 21-04 50 80 10 | Lightning Protection
D5080.40 | Cathodic Protection | 4 |  |  | C3010150 | Wall Finishes - Tile | 5 | -2000011 | 21-04 50 80 40 | Cathodic Protection
D5080.70 | Transient Voltage Suppression | 4 |  |  | C3010300 | Column Finishes | 4 | -2000100 | 21-04 50 80 70 | Transient Voltage Suppression
D5080.90 | Miscellaneous Electrical Systems Supplementary Components | 4 |  |  | C3020 | Floor Finishes | 3 |  | 21-04 50 80 90 | Miscellaneous Electrical Systems Supplementary Components
D6010.10 | Data Communications Network Equipment | 4 |  |  | C3020120 | Acrylic Coatings | 5 | -2000032 | 21-04 60 10 10 | Data Communications Network Equipment
D6010.20 | Data Communications Hardware | 4 |  |  | C3020130 | Epoxy Coatings | 5 | -2000032 | 21-04 60 10 20 | Data Communications Hardware
D6010.30 | Data Communications Peripheral Data Equipment | 4 |  |  | C3020200 | Traffic Membranes | 4 | -2000032 | 21-04 60 10 30 | Data Communications Peripheral Data Equipment
D6010.50 | Data Communications Software | 4 |  |  | C3020300 | Hardeners & Sealers | 4 | -2000032 | 21-04 60 10 50 | Data Communications Software
D6010.60 | Data Communication Program and Integration Services | 4 |  |  | C3020400 | Flooring | 4 | -2000032 | 21-04 60 10 60 | Data Communication Program and Integration Services
D6020.10 | Voice Communications Switching and Routing Equipment | 4 |  |  | C3020420 | Flooring - Terrazzo | 5 | -2000032 | 21-04 60 20 10 | Voice Communications Switching and Routing Equipment
D6020.20 | Voice Communications Terminal Equipment | 4 |  |  | C3020430 | Flooring - Tile | 5 | -2000032 | 21-04 60 20 20 | Voice Communications Terminal Equipment
D6020.30 | Voice Communications Messaging | 4 |  |  | C3020440 | Flooring - VCT | 5 | -2000032 | 21-04 60 20 30 | Voice Communications Messaging
D6020.40 | Call Accounting | 4 |  |  | C3020450 | Flooring - Wood | 5 | -2000032 | 21-04 60 20 40 | Call Accounting
D6020.50 | Call Management | 4 |  |  | C3020490 | Flooring - Other | 5 | -2000032 | 21-04 60 20 50 | Call Management
D6030.10 | Audio-Video Systems | 4 |  |  | C3020510 | Carpet | 5 | -2000032 | 21-04 60 30 10 | Audio-Video Systems
D6030.50 | Electronic Digital Systems | 4 |  |  | C3020520 | Carpet Tile | 5 | -2000032 | 21-04 60 30 50 | Electronic Digital Systems
D6060 | Distributed Communications and Monitoring | 4 |  |  | C3020600 | Bases, Curbs & Trim | 4 | -2000032 | 21-04 60 60 | Distributed Communications and Monitoring
D6060.10 | Distributed Audio-Video Communications Systems | 4 |  |  | C3020610 | Base - Vinyl & Rubber | 5 | -2000032 | 21-04 60 60 10 | Distributed Audio-Video Communications Systems
D6060.30 | Healthcare Communications and Monitoring | 4 |  |  | C3020620 | Base - Wood | 5 | -2000032 | 21-04 60 60 30 | Healthcare Communications and Monitoring
D6060.50 | Distributed Systems | 4 |  |  | C3020700 | Access Pedestal Flooring | 4 | -2000032 | 21-04 60 60 50 | Distributed Systems
D6090.10 | Supplementary Components | 4 |  |  | C3020810 | Subflooring & Underlayment - Wood | 5 | -2000032 | 21-04 60 90 10 | Supplementary Components
D7010.10 | Access Control | 4 |  |  | C3030110 | Ceiling Finishes - Paint | 5 | -2000038 | 21-04 70 10 10 | Access Control
D7010.50 | Intrusion Detection | 4 |  |  | C3030120 | Ceiling Finishes - Coatings | 5 | -2000038 | 21-04 70 10 50 | Intrusion Detection
D7030.10 | Video Surveillance | 4 |  |  | C3030140 | Ceiling Finishes - Paneling | 5 | -2000038 | 21-04 70 30 10 | Video Surveillance
D7030.50 | Electronic Personal Protection | 4 |  |  | C3030150 | Ceiling Finishes - Tile | 5 | -2000038 | 21-04 70 30 50 | Electronic Personal Protection
D7050.10 | Fire Detection and Alarm | 4 |  |  | C3030210 | Suspended Ceilings - Acoustical | 5 | -2000038 | 21-04 70 50 10 | Fire Detection and Alarm
D7050.20 | Radiation Detection and Alarm | 4 |  |  | C3030220 | Suspended Ceilings - Gypsum Board | 5 | -2000038 | 21-04 70 50 20 | Radiation Detection and Alarm
D7050.30 | Fuel-Gas Detection and Alarm | 4 |  |  | C3030230 | Suspended Ceilings - Plaster | 5 | -2000038 | 21-04 70 50 30 | Fuel-Gas Detection and Alarm
D7050.40 | Fuel-Oil Detection and Alarm | 4 |  |  | C3030300 | Drywall & Plaster Ceiling Components | 4 | -2000038 | 21-04 70 50 40 | Fuel-Oil Detection and Alarm
D7050.50 | Refrigeration Detection and Alarm | 4 |  |  | C3030310 | Ceiling Components - Drywall | 5 | -2000038 | 21-04 70 50 50 | Refrigeration Detection and Alarm
D7050.60 | Water Intrusion Detection and Alarm | 4 |  |  | C3030320 | Ceiling components - Plaster | 5 | -2000038 | 21-04 70 50 60 | Water Intrusion Detection and Alarm
D7070.10 | Electronic Detention Monitoring and Control | 4 |  |  | D | Services | 1 |  | 21-04 70 70 10 | Electronic Detention Monitoring and Control
D7090.10 | Supplementary Components | 4 |  |  | D1010 | Elevators and Lifts | 3 |  | 21-04 70 90 10 | Supplementary Components
D8010.10 | Integrated Automation Control of Equipment | 4 |  |  | D1010130 | Elevators - Oil Hydraulic | 5 | -2001350 | 21-04 80 10 10 | Integrated Automation Control of Equipment
D8010.20 | Integrated Automation Control of Conveying Equipment | 4 |  |  | D1010140 | Elevators - Traction Geared | 5 | -2001350 | 21-04 80 10 20 | Integrated Automation Control of Conveying Equipment
D8010.30 | Integrated Automation Control of Fire-Suppression Systems | 4 |  |  | D1010150 | Elevators - Traction Gearless | 5 | -2001350 | 21-04 80 10 30 | Integrated Automation Control of Fire-Suppression Systems
D8010.40 | Integrated Automation Control of Plumbing Systems | 4 |  |  | D1010200 | Freight Elevators | 4 | -2001350 | 21-04 80 10 40 | Integrated Automation Control of Plumbing Systems
D8010.50 | Integrated Automation Control of HVAC Systems | 4 |  |  | D1010210 | Elevators - Freight | 5 | -2001350 | 21-04 80 10 50 | Integrated Automation Control of HVAC Systems
D8010.60 | Integrated Automation Control of Electrical Systems | 4 |  |  | D1010300 | Lifts | 4 | -2001350 | 21-04 80 10 60 | Integrated Automation Control of Electrical Systems
D8010.70 | Integrated Automation Control of Communication Systems | 4 |  |  | D1010310 | Lifts - Passenger | 5 | -2001350 | 21-04 80 10 70 | Integrated Automation Control of Communication Systems
D8010.80 | Integrated Automation Control of Electronic Safety and Security Systems | 4 |  |  | D1020 | Escalators and Moving Walks | 3 | -2001350 | 21-04 80 10 80 | Integrated Automation Control of Electronic Safety and Security Systems
D8010.90 | Integrated Automation Supplementary Components | 4 |  |  | D1020100 | Escalators | 4 | -2001350 | 21-04 80 10 90 | Integrated Automation Supplementary Components
E1010.10 | Vehicle Servicing Equipment | 4 |  |  | D1090 | Other Conveying Systems | 3 | -2001350 | 21-05 10 10 10 | Vehicle Servicing Equipment
E1010.30 | Interior Parking Control Equipment | 4 |  |  | D1090100 | Dumbwaiters | 4 | -2001350 | 21-05 10 10 30 | Interior Parking Control Equipment
E1010.50 | Loading Dock Equipment | 4 |  |  | D1090200 | Pneumatic Tube Systems | 4 | -2001350 | 21-05 10 10 50 | Loading Dock Equipment
E1010.70 | Interior Pedestrian Control Equipment | 4 |  |  | D1090300 | Hoists & Cranes | 4 | -2001350 | 21-05 10 10 70 | Interior Pedestrian Control Equipment
E1030.10 | Mercantile and Service Equipment | 4 |  |  | D1090410 | Conveyors - Horizontal & Inclined | 5 | -2001350 | 21-05 10 30 10 | Mercantile and Service Equipment
E1030.20 | Vault Equipment | 4 |  |  | D1090420 | Conveyors - Vertical | 5 | -2001350 | 21-05 10 30 20 | Vault Equipment
E1030.25 | Teller and Service Equipment | 4 |  |  | D1090500 | Chutes | 4 | -2001350 | 21-05 10 30 25 | Teller and Service Equipment
E1030.30 | Refrigerated Display Equipment | 4 |  |  | D1090510 | Chutes - Linen & Refuse | 5 | -2001350 | 21-05 10 30 30 | Refrigerated Display Equipment
E1030.35 | Commercial Laundry and Dry Cleaning Equipment | 4 |  |  | D1090520 | Chutes - Mail | 5 | -2001350 | 21-05 10 30 35 | Commercial Laundry and Dry Cleaning Equipment
E1030.40 | Maintenance Equipment | 4 |  |  | D1090600 | Turntables | 4 | -2001350 | 21-05 10 30 40 | Maintenance Equipment
E1030.50 | Hospitality Equipment | 4 |  |  | D1090700 | Baggage Handling & Loading Systems | 4 | -2001350 | 21-05 10 30 50 | Hospitality Equipment
E1030.55 | Unit Kitchens | 4 |  |  | D1090800 | Transportation Systems | 4 | -2001350 | 21-05 10 30 55 | Unit Kitchens
E1030.60 | Photographic Processing Equipment | 4 |  |  | D20 | Plumbing | 2 |  | 21-05 10 30 60 | Photographic Processing Equipment
E1030.70 | Postal, Packaging, and Shipping Equipment | 4 |  |  | D2010 | Plumbing Fixtures | 3 |  | 21-05 10 30 70 | Postal, Packaging, and Shipping Equipment
E1030.75 | Office Equipment | 4 |  |  | D2010100 | Water Closets | 4 | -2001160 | 21-05 10 30 75 | Office Equipment
E1030.80 | Foodservice Equipment | 4 |  |  | D2010110 | Water Closets - Single | 5 | -2001160 | 21-05 10 30 80 | Foodservice Equipment
E1040.10 | Educational and Scientific Equipment | 4 |  |  | D2010200 | Urinals | 4 | -2001160 | 21-05 10 40 10 | Educational and Scientific Equipment
E1040.20 | Healthcare Equipment | 4 |  |  | D2010210 | Urinals - Single | 5 | -2001160 | 21-05 10 40 20 | Healthcare Equipment
E1040.40 | Religious Equipment | 4 |  |  | D2010220 | Urinals - Battery Mount | 5 | -2001160 | 21-05 10 40 40 | Religious Equipment
E1040.60 | Security Equipment | 4 |  |  | D2010300 | Lavatories | 4 | -2001160 | 21-05 10 40 60 | Security Equipment
E1040.70 | Detention Equipment | 4 |  |  | D2010310 | Lavatories - Single | 5 | -2001160 | 21-05 10 40 70 | Detention Equipment
E1060.10 | Residential Appliances | 4 |  |  | D2010400 | Sinks | 4 | -2001160 | 21-05 10 60 10 | Residential Appliances
E1060.50 | Retractable Stairs | 4 |  |  | D2010410 | Sinks - Kitchen | 5 | -2001160 | 21-05 10 60 50 | Retractable Stairs
E1060.70 | Residential Ceiling Fans | 4 |  |  | D2010420 | Sinks - Laundry | 5 | -2001160 | 21-05 10 60 70 | Residential Ceiling Fans
E1070.10 | Theater and Stage Equipment | 4 |  |  | D2010440 | Sinks - Service | 5 | -2001160 | 21-05 10 70 10 | Theater and Stage Equipment
E1070.20 | Musical Equipment | 4 |  |  | D2010500 | Bathtubs | 4 | -2001160 | 21-05 10 70 20 | Musical Equipment
E1070.50 | Athletic Equipment | 4 |  |  | D2010510 | Bathtubs | 5 | -2001160 | 21-05 10 70 50 | Athletic Equipment
E1070.60 | Recreational Equipment | 4 |  |  | D2010600 | Wash Fountains | 4 | -2001160 | 21-05 10 70 60 | Recreational Equipment
E1090.10 | Solid Waste Handling Equipment | 4 |  |  | D2010700 | Showers | 4 | -2001160 | 21-05 10 90 10 | Solid Waste Handling Equipment
E1090.30 | Agricultural Equipment | 4 |  |  | D2010710 | Showers | 5 | -2001160 | 21-05 10 90 30 | Agricultural Equipment
E1090.40 | Horticultural Equipment | 4 |  |  | D2010800 | Drinking Fountains & Coolers | 4 | -2001160 | 21-05 10 90 40 | Horticultural Equipment
E1090.60 | Decontamination Equipment | 4 |  |  | D2010810 | Drinking Fountains | 5 | -2001160 | 21-05 10 90 60 | Decontamination Equipment
E2010.10 | Fixed Art | 4 |  |  | D2010910 | Bidets | 5 | -2001160 | 21-05 20 10 10 | Fixed Art
E2010.20 | Window Treatments | 4 |  |  | D2020 | Domestic Water Distribution | 3 | -2001160 | 21-05 20 10 20 | Window Treatments
E2010.30 | Casework | 4 |  |  | D2020100 | Cold Water Service | 4 | -2001160 | 21-05 20 10 30 | Casework
E2010.70 | Fixed Multiple Seating | 4 |  |  | D2020200 | Hot Water Service | 4 | -2001160 | 21-05 20 10 70 | Fixed Multiple Seating
E2010.90 | Other Fixed Furnishings | 4 |  |  | D2020300 | Domestic Water Supply Equipment | 4 | -2001160 | 21-05 20 10 90 | Other Fixed Furnishings
E2050.10 | Movable Art | 4 |  |  | D2030100 | Waste Piping | 4 | -2001160 | 21-05 20 50 10 | Movable Art
E2050.30 | Furniture | 4 |  |  | D2030200 | Vent Piping | 4 | -2001160 | 21-05 20 50 30 | Furniture
E2050.40 | Accessories | 4 |  |  | D2030300 | Floor Drains | 4 | -2001160 | 21-05 20 50 40 | Accessories
E2050.60 | Movable Multiple Seating | 4 |  |  | D2030400 | Sanitary Waste Equipment | 4 | -2001160 | 21-05 20 50 60 | Movable Multiple Seating
E2050.90 | Other Movable Furnishings | 4 |  |  | D2030500 | Pipe Insulation | 4 | -2001160 | 21-05 20 50 90 | Other Movable Furnishings
F1010.10 | Building Modules | 4 |  |  | D2040300 | Rainwater Drainage Equipment | 4 | -2001160 | 21-06 10 10 10 | Building Modules
F1010.50 | Manufactured/Fabricated Rooms | 4 |  |  | D2040400 | Pipe Insulation | 4 | -2001160 | 21-06 10 10 50 | Manufactured/Fabricated Rooms
F1010.70 | Modular Mezzanines | 4 |  |  | D2090 | Other Plumbing Systems | 3 | -2001160 | 21-06 10 10 70 | Modular Mezzanines
F1020.10 | Fabric Structures | 4 |  |  | D2090200 | Acid Waste Systems | 4 | -2001160 | 21-06 10 20 10 | Fabric Structures
F1020.20 | Space Frames | 4 |  |  | D2090300 | Interceptors | 4 | -2001160 | 21-06 10 20 20 | Space Frames
F1020.30 | Geodesic Structures | 4 |  |  | D2090400 | Pool Piping & Equipment | 4 | -2001160 | 21-06 10 20 30 | Geodesic Structures
F1020.40 | Manufacturer-Engineered Structures | 4 |  |  | D2090500 | Decorative Fountain Piping & Devices | 4 | -2001160 | 21-06 10 20 40 | Manufacturer-Engineered Structures
F1020.60 | Manufactured Canopies | 4 |  |  | D2090600 | Special Water Systems | 4 | -2001160 | 21-06 10 20 60 | Manufactured Canopies
F1020.65 | Rammed Earth Construction | 4 |  |  | D2090800 | Piping & Fittings | 4 | -2001160 | 21-06 10 20 65 | Rammed Earth Construction
F1020.70 | Towers | 4 |  |  | D2090900 | Misc. Other Plumbing Systems | 4 | -2001160 | 21-06 10 20 70 | Towers
F1030.10 | Sound and Vibration Control | 4 |  |  | D3010 | Energy Supply | 3 |  | 21-06 10 30 10 | Sound and Vibration Control
F1030.30 | Seismic Control | 4 |  |  | D3010100 | Oil Supply System | 4 | -2001140 | 21-06 10 30 30 | Seismic Control
F1030.50 | Radiation Protection | 4 |  |  | D3010200 | Gas Supply System | 4 | -2001140 | 21-06 10 30 50 | Radiation Protection
F1050.10 | Pools | 4 |  |  | D3010400 | Steam Supply System | 4 | -2001140 | 21-06 10 50 10 | Pools
F1050.20 | Interior Fountains | 4 |  |  | D3010500 | Hot Water Supply System | 4 | -2001140 | 21-06 10 50 20 | Interior Fountains
F1050.30 | Interior Water Features | 4 |  |  | D3010600 | Chilled Water Supply System | 4 | -2001140 | 21-06 10 50 30 | Interior Water Features
F1050.40 | Aquariums | 4 |  |  | D3010700 | Solar Energy Systems | 4 | -2001140 | 21-06 10 50 40 | Aquariums
F1050.50 | Amusement Park Structures and Equipment | 4 |  |  | D3010800 | Wind Energy System | 4 | -2001140 | 21-06 10 50 50 | Amusement Park Structures and Equipment
F1050.60 | Ice Rinks | 4 |  |  | D3010900 | Fuel Cell Systems | 4 | -2001140 | 21-06 10 50 60 | Ice Rinks
F1050.70 | Animal Containment | 4 |  |  | D3020 | Heat Generating Systems | 3 | -2001140 | 21-06 10 50 70 | Animal Containment
F1060.10 | Indoor Soccer Boards | 4 |  |  | D3020200 | Boiler Room Piping & Specialties | 4 | -2001140 | 21-06 10 60 10 | Indoor Soccer Boards
F1060.20 | Safety Netting | 4 |  |  | D3020300 | Auxiliary Equipment | 4 | -2001140 | 21-06 10 60 20 | Safety Netting
F1060.30 | Arena Football Boards | 4 |  |  | D3020400 | Insulation | 4 | -2001140 | 21-06 10 60 30 | Arena Football Boards
F1060.40 | Floor Sockets | 4 |  |  | D3030 | Cooling Generating Systems | 3 | -2001140 | 21-06 10 60 40 | Floor Sockets
F1060.50 | Athletic and Recreational Court Walls | 4 |  |  | D3030100 | Chilled Water Systems | 4 | -2001140 | 21-06 10 60 50 | Athletic and Recreational Court Walls
F1060.60 | Demountable Athletic Surfaces | 4 |  |  | D3030200 | Direct Expansion Systems | 4 | -2001140 | 21-06 10 60 60 | Demountable Athletic Surfaces
F1080.10 | Stress Instrumentation | 4 |  |  | D3040 | Distribution Systems | 3 | -2001140 | 21-06 10 80 10 | Stress Instrumentation
F1080.20 | Seismic Instrumentation | 4 |  |  | D3040100 | Air Distribution Systems | 4 | -2001140 | 21-06 10 80 20 | Seismic Instrumentation
F1080.40 | Meteorological Instrumentation | 4 |  |  | D3040200 | Exhaust Ventilation Systems | 4 | -2001140 | 21-06 10 80 40 | Meteorological Instrumentation
F1080.60 | Earth Movement Monitoring | 4 |  |  | D3040300 | Steam Distribution Systems | 4 | -2001140 | 21-06 10 80 60 | Earth Movement Monitoring
F2010.10 | Transportation and Disposal of Hazardous Materials | 4 |  |  | D3040600 | Change-over Distribution Systems | 4 | -2001140 | 21-06 20 10 10 | Transportation and Disposal of Hazardous Materials
F2010.20 | Asbestos Remediation | 4 |  |  | D3040700 | Glycol Distribution Systems | 4 | -2001140 | 21-06 20 10 20 | Asbestos Remediation
F2010.30 | Lead Remediation | 4 |  |  | D3050 | Terminal & Package Units | 3 | -2001140 | 21-06 20 10 30 | Lead Remediation
F2010.40 | Polychlorinate Biphenyl Remediation | 4 |  |  | D3050100 | Terminal Self-Contained Units | 4 | -2001140 | 21-06 20 10 40 | Polychlorinate Biphenyl Remediation
F2010.50 | Mold Remediation | 4 |  |  | D3050200 | Package Units | 4 | -2001140 | 21-06 20 10 50 | Mold Remediation
F3010.10 | Building Demolition | 4 |  |  | D3060200 | Cooling Generating Systems | 4 | -2001140 | 21-06 30 10 10 | Building Demolition
F3010.30 | Tower Demolition | 4 |  |  | D3060300 | Heating/Cooling Air Handling Units | 4 | -2001140 | 21-06 30 10 30 | Tower Demolition
F3010.50 | Bridge Demolition | 4 |  |  | D3060400 | Exhaust & Ventilating Systems | 4 | -2001140 | 21-06 30 10 50 | Bridge Demolition
F3010.70 | Dam Demolition | 4 |  |  | D3060500 | Hoods & Exhaust Systems | 4 | -2001140 | 21-06 30 10 70 | Dam Demolition
F3030.10 | Selective Building Demolition | 4 |  |  | D3060700 | Energy Monitoring & Control | 4 | -2001140 | 21-06 30 30 10 | Selective Building Demolition
F3030.30 | Selective Interior Demolition | 4 |  |  | D3060800 | Building Automation Systems | 4 | -2001140 | 21-06 30 30 30 | Selective Interior Demolition
F3030.50 | Selective Bridge Demolition | 4 |  |  | D3070 | Systems Testing & Balancing | 3 | -2001140 | 21-06 30 30 50 | Selective Bridge Demolition
F3030.70 | Selective Historic Demolition | 4 |  |  | D3070100 | Piping System Testing & Balancing | 4 | -2001140 | 21-06 30 30 70 | Selective Historic Demolition
F3050.10 | Structure Relocation | 4 |  |  | D3070300 | HVAC Commissioning | 4 | -2001140 | 21-06 30 50 10 | Structure Relocation
F3050.30 | Structure Raising | 4 |  |  | D3070900 | Other System Testing & Balancing | 4 | -2001140 | 21-06 30 50 30 | Structure Raising
G1010.10 | Clearing and Grubbing | 4 |  |  | D3090300 | Dust & Fume Collectors | 4 | -2001140 | 21-07 10 10 10 | Clearing and Grubbing
G1010.30 | Tree and Shrub Removal and Trimming | 4 |  |  | D3090400 | Air Curtains | 4 | -2001140 | 21-07 10 10 30 | Tree and Shrub Removal and Trimming
G1010.50 | Earth Stripping and Stockpiling | 4 |  |  | D3090500 | Air Purifiers | 4 | -2001140 | 21-07 10 10 50 | Earth Stripping and Stockpiling
G1020.10 | Utility Demolition | 4 |  |  | D3090700 | General Construction Items (HVAC) | 4 | -2001140 | 21-07 10 20 10 | Utility Demolition
G1020.30 | Infrastructure Demolition | 4 |  |  | D3090900 | Misc. Other HVAC Systems & Equipment | 4 | -2001140 | 21-07 10 20 30 | Infrastructure Demolition
G1020.50 | Selective Site Demolition | 4 |  |  | D40 | Fire Protection | 2 |  | 21-07 10 20 50 | Selective Site Demolition
G1030.10 | Utility Relocation | 4 |  |  | D4010100 | Sprinkler Water Supply | 4 | -2001160 | 21-07 10 30 10 | Utility Relocation
G1050.10 | Physical Decontamination | 4 |  |  | D4010300 | Wet Sprinkler Systems | 4 | -2001160 | 21-07 10 50 10 | Physical Decontamination
G1050.15 | Chemical Decontamination | 4 |  |  | D4010400 | Dry Sprinkler Systems | 4 | -2001160 | 21-07 10 50 15 | Chemical Decontamination
G1050.20 | Thermal Decontamination | 4 |  |  | D4020 | Standpipes | 3 | -2001160 | 21-07 10 50 20 | Thermal Decontamination
G1050.25 | Biological Decontamination | 4 |  |  | D4020100 | Standpipe Water Supply | 4 | -2001160 | 21-07 10 50 25 | Biological Decontamination
G1050.30 | Remediation Soil Stabilization | 4 |  |  | D4020200 | Pumping Equipment | 4 | -2001160 | 21-07 10 50 30 | Remediation Soil Stabilization
G1050.40 | Site Containment | 4 |  |  | D4020300 | Standpipe Equipment | 4 | -2001160 | 21-07 10 50 40 | Site Containment
G1050.45 | Sinkhole Remediation | 4 |  |  | D4020400 | Fire Hose Equipment | 4 | -2001160 | 21-07 10 50 45 | Sinkhole Remediation
G1050.50 | Hazardous Waste Drum Handling | 4 |  |  | D4030 | Fire Protection Specialties | 3 | -2001160 | 21-07 10 50 50 | Hazardous Waste Drum Handling
G1050.60 | Contaminated Site Material Removal | 4 |  |  | D4030100 | Fire Extinguishers | 4 | -2001350 | 21-07 10 50 60 | Contaminated Site Material Removal
G1050.80 | Water Remediation | 4 |  |  | D4030200 | Fire Extinguisher Cabinets | 4 | -2001350 | 21-07 10 50 80 | Water Remediation
G1070.10 | Grading | 4 |  |  | D4090 | Other Fire Protection Systems | 3 | -2001350 | 21-07 10 70 10 | Grading
G1070.20 | Excavation and Fill | 4 |  |  | D4090100 | Carbon Dioxide Systems | 4 | -2001350 | 21-07 10 70 20 | Excavation and Fill
G1070.30 | Embankments | 4 |  |  | D4090200 | Foam Generating Equipment | 4 | -2001350 | 21-07 10 70 30 | Embankments
G1070.35 | Erosion and Sedimentation Controls | 4 |  |  | D4090300 | Clean Agent System | 4 | -2001350 | 21-07 10 70 35 | Erosion and Sedimentation Controls
G1070.40 | Soil Stabilization | 4 |  |  | D4090400 | Dry Chemical Systems | 4 | -2001350 | 21-07 10 70 40 | Soil Stabilization
G1070.45 | Rock Stabilization | 4 |  |  | D4090500 | Hood & Duct Fire Protection | 4 | -2001350 | 21-07 10 70 45 | Rock Stabilization
G1070.50 | Soil Reinforcement | 4 |  |  | D4090900 | Misc. Other Fire Protection Systems | 4 | -2001350 | 21-07 10 70 50 | Soil Reinforcement
G1070.55 | Slope Protection | 4 |  |  | D50 | Electrical | 2 |  | 21-07 10 70 55 | Slope Protection
G1070.60 | Gabions | 4 |  |  | D5010 | Electrical Service/Distribution | 3 |  | 21-07 10 70 60 | Gabions
G1070.65 | Riprap | 4 |  |  | D5010100 | High Tension Service & Distribution | 4 | -2001060 | 21-07 10 70 65 | Riprap
G1070.70 | Wetlands | 4 |  |  | D5010200 | Low Tension Service & Distribution | 4 | -2001060 | 21-07 10 70 70 | Wetlands
G1070.80 | Earth Dams | 4 |  |  | D5020 | Lighting and Branch Wiring | 3 |  | 21-07 10 70 80 | Earth Dams
G1070.90 | Site Soil Treatment | 4 |  |  | D5020100 | Branch Wiring & Devices | 4 |  | 21-07 10 70 90 | Site Soil Treatment
G2010.10 | Roadway Pavement | 4 |  |  | D5020120 | Switches - Wall | 5 | -2001060 | 21-07 20 10 10 | Roadway Pavement
G2010.20 | Roadway Curbs and Gutters | 4 |  |  | D5020200 | Lighting Equipment | 4 |  | 21-07 20 10 20 | Roadway Curbs and Gutters
G2010.40 | Roadway Appurtenances | 4 |  |  | D5020210 | Lighting - Fluorescent | 5 | -2001120 | 21-07 20 10 40 | Roadway Appurtenances
G2010.70 | Roadway Lighting | 4 |  |  | D5020220 | Lighting - Incandescent | 5 | -2001120 | 21-07 20 10 70 | Roadway Lighting
G2010.80 | Vehicle Fare Collection | 4 |  |  | D5020230 | Lighting - High Intensity | 5 | -2001120 | 21-07 20 10 80 | Vehicle Fare Collection
G2020.10 | Parking Lot Pavement | 4 |  |  | D5030 | Communications and Security | 3 |  | 21-07 20 20 10 | Parking Lot Pavement
G2020.20 | Parking Lot Curbs and Gutters | 4 |  |  | D5030100 | Public Address & Music Systems | 4 | -2001040 | 21-07 20 20 20 | Parking Lot Curbs and Gutters
G2020.40 | Parking Lot Appurtenances | 4 |  |  | D5030200 | Intercommunication & Paging Systems | 4 | -2001040 | 21-07 20 20 40 | Parking Lot Appurtenances
G2020.70 | Parking Lot Lighting | 4 |  |  | D5030300 | Telephone Systems | 4 | -2001040 | 21-07 20 20 70 | Parking Lot Lighting
G2020.80 | Exterior Parking Control Equipment | 4 |  |  | D5030400 | Call Systems | 4 | -2001040 | 21-07 20 20 80 | Exterior Parking Control Equipment
G2030.10 | Pedestrian Pavement | 4 |  |  | D5030600 | Data Networking | 4 | -2001040 | 21-07 20 30 10 | Pedestrian Pavement
G2030.20 | Pedestrian Pavement Curbs and Gutters | 4 |  |  | D5030700 | Fire Alarm Systems | 4 | -2001040 | 21-07 20 30 20 | Pedestrian Pavement Curbs and Gutters
G2030.30 | Exterior Steps and Ramps | 4 |  |  | D5030800 | Security & Detection Systems | 4 | -2001040 | 21-07 20 30 30 | Exterior Steps and Ramps
G2030.40 | Pedestrian Pavement Appurtenances | 4 |  |  | D5030900 | Other Communications & Security Systems | 4 | -2001040 | 21-07 20 30 40 | Pedestrian Pavement Appurtenances
G2030.70 | Plaza and Walkway Lighting | 4 |  |  | D5090 | Other Electrical Systems | 3 |  | 21-07 20 30 70 | Plaza and Walkway Lighting
G2030.80 | Exterior Pedestrian Control Equipment | 4 |  |  | D5090100 | Grounding Systems | 4 | -2001040 | 21-07 20 30 80 | Exterior Pedestrian Control Equipment
G2040.10 | Aviation Pavement | 4 |  |  | D5090300 | Floor Raceway Systems | 4 | -2001040 | 21-07 20 40 10 | Aviation Pavement
G2040.20 | Aviation Pavement Curbs and Gutters | 4 |  |  | D5090400 | General Construction Items (Elect.) | 4 | -2001040 | 21-07 20 40 20 | Aviation Pavement Curbs and Gutters
G2040.40 | Aviation Pavement Appurtenances | 4 |  |  | D5090900 | Misc. Other Electrical Systems | 4 | -2001040 | 21-07 20 40 40 | Aviation Pavement Appurtenances
G2040.70 | Airfield Lighting | 4 |  |  | E | Equipment & Furnishings | 1 |  | 21-07 20 40 70 | Airfield Lighting
G2040.80 | Airfield Signaling and Control Equipment | 4 |  |  | E10 | Equipment | 2 |  | 21-07 20 40 80 | Airfield Signaling and Control Equipment
G2050.10 | Athletic Areas | 4 |  |  | E1010100 | Security & Vault Equipment | 4 | -2001350 | 21-07 20 50 10 | Athletic Areas
G2050.30 | Recreational Areas | 4 |  |  | E1010110 | Security Equipment | 5 | -2001350 | 21-07 20 50 30 | Recreational Areas
G2050.50 | Playfield Areas | 4 |  |  | E1010120 | Vault Equipment | 5 | -2001350 | 21-07 20 50 50 | Playfield Areas
G2060.10 | Exterior Fountains | 4 |  |  | E1010300 | Registration Equipment | 4 | -2001350 | 21-07 20 60 10 | Exterior Fountains
G2060.20 | Fences and Gates | 4 |  |  | E1010400 | Checkroom Equipment | 4 | -2001350 | 21-07 20 60 20 | Fences and Gates
G2060.25 | Site Furnishings | 4 |  |  | E1010500 | Mercantile Equipment | 4 | -2001350 | 21-07 20 60 25 | Site Furnishings
G2060.30 | Exterior Signage | 4 |  |  | E1010510 | Display Cases | 5 | -2001350 | 21-07 20 60 30 | Exterior Signage
G2060.35 | Flagpoles | 4 |  |  | E1010520 | Checkout Counters | 5 | -2001350 | 21-07 20 60 35 | Flagpoles
G2060.40 | Covers and Shelters | 4 |  |  | E1010600 | Laundry & Dry Cleaning Equipment | 4 | -2001350 | 21-07 20 60 40 | Covers and Shelters
G2060.45 | Exterior Gas Lighting | 4 |  |  | E1010610 | Laundry Equipment - Washers & Dryers | 5 | -2001350 | 21-07 20 60 45 | Exterior Gas Lighting
G2060.50 | Site Equipment | 4 |  |  | E1010620 | Laundry Equipment - Ironers | 5 | -2001350 | 21-07 20 60 50 | Site Equipment
G2060.60 | Retaining Walls | 4 |  |  | E1010700 | Vending Equipment | 4 | -2001350 | 21-07 20 60 60 | Retaining Walls
G2060.70 | Site Bridges | 4 |  |  | E1010800 | Office Equipment | 4 | -2001350 | 21-07 20 60 70 | Site Bridges
G2060.80 | Site Screening Devices | 4 |  |  | E1010900 | Other Commercial Equipment | 4 | -2001350 | 21-07 20 60 80 | Site Screening Devices
G2060.85 | Site Specialties | 4 |  |  | E1020 | Institutional Equipment | 3 |  | 21-07 20 60 85 | Site Specialties
G2080.10 | Planting Irrigation | 4 |  |  | E1020110 | Ecclesiastical Equipment - Steeples & Bells | 5 | -2001350 | 21-07 20 80 10 | Planting Irrigation
G2080.20 | Turf and Grasses | 4 |  |  | E1020120 | Ecclesiastical Equipment - Baptismals & Fonts | 5 | -2001350 | 21-07 20 80 20 | Turf and Grasses
G2080.30 | Plants | 4 |  |  | E1020130 | Ecclesiastical Equipment - Pews | 5 | -2000080 | 21-07 20 80 30 | Plants
G2080.50 | Planting Accessories | 4 |  |  | E1020200 | Library Equipment | 4 | -2001350 | 21-07 20 80 50 | Planting Accessories
G2080.70 | Landscape Lighting | 4 |  |  | E1020210 | Library Equipment - Carrels | 5 | -2000080 | 21-07 20 80 70 | Landscape Lighting
G2080.80 | Landscaping Activities | 4 |  |  | E1020230 | Library Equipment - Shelves & Desks | 5 | -2000080 | 21-07 20 80 80 | Landscaping Activities
G3010.10 | Site Domestic Water Distribution | 4 |  |  | E1020320 | Theater Equipment - Lights & Tracks | 5 | -2001120 | 21-07 30 10 10 | Site Domestic Water Distribution
G3010.30 | Site Fire Protection Water Distribution | 4 |  |  | E1020330 | Theater Equipment - Curtains | 5 | -2001350 | 21-07 30 10 30 | Site Fire Protection Water Distribution
G3010.50 | Site Irrigation Water Distribution | 4 |  |  | E1020400 | Instrumental Equipment | 4 | -2001350 | 21-07 30 10 50 | Site Irrigation Water Distribution
G3020.10 | Sanitary Sewerage Utility Connection | 4 |  |  | E1020600 | Detention Equipment | 4 | -2001350 | 21-07 30 20 10 | Sanitary Sewerage Utility Connection
G3020.20 | Sanitary Sewerage Piping | 4 |  |  | E1020700 | Laboratory Equipment | 4 | -2001350 | 21-07 30 20 20 | Sanitary Sewerage Piping
G3020.40 | Utility Septic Tanks | 4 |  |  | E1020710 | Laboratory Equipment | 5 | -2001350 | 21-07 30 20 40 | Utility Septic Tanks
G3020.50 | Sanitary Sewerage Structures | 4 |  |  | E1020720 | Laboratory Cabinets & Countertops | 5 | -2001350 | 21-07 30 20 50 | Sanitary Sewerage Structures
G3020.60 | Sanitary Sewerage Lagoons | 4 |  |  | E1020730 | Laboratory Hoods | 5 | -2001350 | 21-07 30 20 60 | Sanitary Sewerage Lagoons
G3030.10 | Storm Drainage Utility Connection | 4 |  |  | E1020810 | Medical Furniture & Equipment | 5 | -2001350 | 21-07 30 30 10 | Storm Drainage Utility Connection
G3030.20 | Storm Drainage Piping | 4 |  |  | E1020820 | X-ray Equipment | 5 | -2001350 | 21-07 30 30 20 | Storm Drainage Piping
G3030.30 | Culverts | 4 |  |  | E1020900 | Other Institutional Equipment | 4 | -2001350 | 21-07 30 30 30 | Culverts
G3030.40 | Site Storm Water Drains | 4 |  |  | E1030 | Vehicular Equipment | 3 |  | 21-07 30 30 40 | Site Storm Water Drains
G3030.50 | Storm Drainage Pumps | 4 |  |  | E1030100 | Vehicular Service Equipment | 4 | -2001350 | 21-07 30 30 50 | Storm Drainage Pumps
G3030.60 | Site Subdrainage | 4 |  |  | E1030200 | Parking Control Equipment | 4 | -2001350 | 21-07 30 30 60 | Site Subdrainage
G3030.70 | Storm Drainage Ponds and Reservoirs | 4 |  |  | E1030300 | Loading Dock Equipment | 4 | -2001350 | 21-07 30 30 70 | Storm Drainage Ponds and Reservoirs
G3050.10 | Site Hydronic Heating Distribution | 4 |  |  | E1090 | Other Equipment | 3 |  | 21-07 30 50 10 | Site Hydronic Heating Distribution
G3050.20 | Site Steam Energy Distribution | 4 |  |  | E1090100 | Maintenance Equipment | 4 | -2001350 | 21-07 30 50 20 | Site Steam Energy Distribution
G3050.40 | Site Hydronic Cooling Distribution | 4 |  |  | E1090200 | Solid Waste Handling Equipment | 4 | -2001350 | 21-07 30 50 40 | Site Hydronic Cooling Distribution
G3060.10 | Site Gas Distribution | 4 |  |  | E1090310 | Food Service - Cabinets & Countertops | 5 | -2001350 | 21-07 30 60 10 | Site Gas Distribution
G3060.20 | Site Fuel-Oil Distribution | 4 |  |  | E1090320 | Food Service - Appliances & Equipment | 5 | -2001350 | 21-07 30 60 20 | Site Fuel-Oil Distribution
G3060.30 | Site Gasoline Distribution | 4 |  |  | E1090330 | Food Service - Walk-in Refrigerators | 5 | -2001350 | 21-07 30 60 30 | Site Gasoline Distribution
G3060.40 | Site Diesel Fuel Distribution | 4 |  |  | E1090400 | Residential Equipment | 4 | -2001350 | 21-07 30 60 40 | Site Diesel Fuel Distribution
G3060.60 | Site Aviation Fuel Distribution | 4 |  |  | E1090500 | Darkroom Equipment | 4 | -2001350 | 21-07 30 60 60 | Site Aviation Fuel Distribution
G3090.10 | Supplementary Components | 4 |  |  | E1090900 | Other Equipment | 4 | -2001350 | 21-07 30 90 10 | Supplementary Components
G4010.10 | Electrical Utility Services | 4 |  |  | E2010100 | Fixed Artwork | 4 | -2000080 | 21-07 40 10 10 | Electrical Utility Services
G4010.20 | Electric Transmission and Distribution | 4 |  |  | E2010200 | Fixed Casework | 4 | -2001000 | 21-07 40 10 20 | Electric Transmission and Distribution
G4010.30 | Electrical Substations | 4 |  |  | E2010300 | Window Treatments | 4 | -2001350 | 21-07 40 10 30 | Electrical Substations
G4010.40 | Electrical Transformers | 4 |  |  | E2010310 | Window Treatments - Blinds | 5 | -2001350 | 21-07 40 10 40 | Electrical Transformers
G4010.50 | Electrical Switchgear and Protection Devices | 4 |  |  | E2010320 | Window Treatments - Shades | 5 | -2001350 | 21-07 40 10 50 | Electrical Switchgear and Protection Devices
G4010.70 | Site Grounding | 4 |  |  | E2010330 | Window Treatments - Draperies | 5 | -2001350 | 21-07 40 10 70 | Site Grounding
G4010.90 | Electrical Distribution System Instrumentation and Controls | 4 |  |  | E2010400 | Fixed Floor Grilles & Mats | 4 | -2001350 | 21-07 40 10 90 | Electrical Distribution System Instrumentation and Controls
G4050.10 | Area Lighting | 4 |  |  | E2010600 | Fixed Interior Landscaping | 4 | -2001360 | 21-07 40 50 10 | Area Lighting
G4050.20 | Flood Lighting | 4 |  |  | E2020 | Moveable Furnishings | 3 | -2000080 | 21-07 40 50 20 | Flood Lighting
G4050.50 | Building Illumination | 4 |  |  | E2020100 | Movable Artwork | 4 | -2000080 | 21-07 40 50 50 | Building Illumination
G4050.90 | Exterior Lighting Supplementary Components | 4 |  |  | E2020200 | Furniture & Accessories | 4 | -2000080 | 21-07 40 50 90 | Exterior Lighting Supplementary Components
G5010.10 | Site Communications Structures | 4 |  |  | E2020500 | Movable Interior Landscaping | 4 | -2000080 | 21-07 50 10 10 | Site Communications Structures
G5010.30 | Site Communications Distribution | 4 |  |  | F | Special Construction & Demolition | 1 |  | 21-07 50 10 30 | Site Communications Distribution
G5010.50 | Wireless Communications Distribution | 4 |  |  | F10 | Special Construction | 2 |  | 21-07 50 10 50 | Wireless Communications Distribution
G9010.10 | Vehicular Tunnels | 4 |  |  | F1010200 | Pre-engineered Structures | 4 | -2001320 | 21-07 90 10 10 | Vehicular Tunnels
G9010.20 | Pedestrian Tunnels | 4 |  |  | F1010300 | Other Special Structures | 4 | -2001320 | 21-07 90 10 20 | Pedestrian Tunnels
G9010.40 | Service Tunnels | 4 |  |  | F1020 | Integrated Construction | 3 |  | 21-07 90 10 40 | Service Tunnels
G9010.90 | Tunnel Construction Related Activities | 4 |  |  | F1020100 | Integrated Assemblies | 4 | -2001350 | 21-07 90 10 90 | Tunnel Construction Related Activities
 |  | Revit |  | Revit
CSI Uniformat 2010 |  |  |  |  | Revit Assembly Codes OOTB |  |  |  | Omniclass 2011 Table 21 , G
 |  |  |  |  | F1020200 | Special Purpose Rooms | 4 | -2001350
 |  |  |  |  | F1020300 | Other Integrated Construction | 4 | -2001350
 |  |  |  |  | F1030 | Special Construction Systems | 3
 |  |  |  |  | F1030100 | Sound, Vibration & Seismic Construction | 4 | -2001350
 |  |  |  |  | F1030200 | Radiation Protection | 4 | -2001350
 |  |  |  |  | F1030300 | Special Security Systems | 4 | -2001350
 |  |  |  |  | F1030400 | Vaults | 4 | -2001350
 |  |  |  |  | F1030900 | Other Special Construction Systems | 4 | -2001350
 |  |  |  |  | F1040 | Special Facilities | 3
 |  |  |  |  | F1040100 | Aquatic Facilities | 4 | -2001350
 |  |  |  |  | F1040200 | Ice Rinks | 4 | -2001350
 |  |  |  |  | F1040300 | Site Constructed Incinerators | 4 | -2001350
 |  |  |  |  | F1040400 | Kennels & Animal Shelters | 4 | -2001350
 |  |  |  |  | F1040500 | Liquid & Gas Storage Tanks | 4 | -2001350
 |  |  |  |  | F1040900 | Other Special Facilities | 4 | -2001350
 |  |  |  |  | F1050 | Special Controls & Instrumentation | 3
 |  |  |  |  | F1050100 | Recording Instrumentation | 4 | -2001350
 |  |  |  |  | F1050200 | Building Automation Systems | 4 | -2001350
 |  |  |  |  | F1050900 | Other Special Control& Instrumentation | 4 | -2001350
 |  |  |  |  | F20 | Selective Building Demolition | 2
 |  |  |  |  | F2010 | Building Elements Demolition | 3
 |  |  |  |  | F2010100 | Building Interior Demolition | 4
 |  |  |  |  | F2010200 | Building Exterior Demolition | 4
 |  |  |  |  | F2020 | Hazardous Components Abatement | 3
 |  |  |  |  | F2020100 | Removal of Hazardous Components | 4 | -2001260
 |  |  |  |  | F2020200 | Encapsulation of Hazardous Components | 4 | -2001260
 |  |  |  |  | G | Building Sitework | 1
 |  |  |  |  | G10 | Site Preparation | 2
 |  |  |  |  | G1010 | Site Clearing | 3
 |  |  |  |  | G1010100 | Clearing & Grubbing | 4 | -2001260
 |  |  |  |  | G1010200 | Tree Removal & Thinning | 4 | -2001260
 |  |  |  |  | G1020 | Site Demolition and Relocations | 3
 |  |  |  |  | G1020100 | Building Demolition | 4 | -2001260
 |  |  |  |  | G1020200 | Demolition of Site Components | 4 | -2001260
 |  |  |  |  | G1020300 | Relocation of Buildings | 4 | -2001260
 |  |  |  |  | G1020400 | Utilities Relocation | 4 | -2001260
 |  |  |  |  | G1030 | Site Earthwork | 3
 |  |  |  |  | G1030100 | Site Grading Excavation & Disposal | 4 | -2001340
 |  |  |  |  | G1030200 | Borrow Fill | 4 | -2001340
 |  |  |  |  | G1030300 | Soil Stabilization & Treatment | 4 | -2001340
 |  |  |  |  | G1030400 | Site Dewatering | 4 | -2001340
 |  |  |  |  | G1030500 | Site Shoring | 4 | -2001340
 |  |  |  |  | G1030600 | Embankments | 4 | -2001340
 |  |  |  |  | G1030700 | Erosion Control | 4 | -2001340
 |  |  |  |  | G1030800 | Utilities Trenching | 4 | -2001340
 |  |  |  |  | G1040 | Hazardous Waste Remediation | 3
 |  |  |  |  | G1040100 | Removal of Contaminated Soil | 4 | -2001260
 |  |  |  |  | G1040200 | Soil Restoration & Treatment | 4 | -2001260
 |  |  |  |  | G1040900 | Other Hazardous Waste Remediation | 4 | -2001260
 |  |  |  |  | G20 | Site Improvement | 2
 |  |  |  |  | G2010 | Roadways | 3
 |  |  |  |  | G2010100 | Roadway Bases & Sub-Bases | 4 | -2001220
 |  |  |  |  | G2010200 | Roadway Paving & Surfacing | 4 | -2001220
 |  |  |  |  | G2010300 | Curbs, Gutters & Drains | 4 | -2001220
 |  |  |  |  | G2010400 | Guardrails & Barriers | 4 | -2001220
 |  |  |  |  | G2010500 | Painted Lines & Markings | 4 | -2001220
 |  |  |  |  | G2010600 | Signage | 4 | -2001220
 |  |  |  |  | G2010700 | Vehicular Bridges | 4 | -2001220
 |  |  |  |  | G2020 | Parking Lots | 3
 |  |  |  |  | G2020100 | Parking Lot Bases & Sub-Bases | 4 | -2001180
 |  |  |  |  | G2020200 | Parking Lot Paving & Surfacing | 4 | -2001180
 |  |  |  |  | G2020300 | Curbs, Gutters & Drains | 4 | -2001180
 |  |  |  |  | G2020400 | Guardrails & Barriers | 4 | -2001180
 |  |  |  |  | G2020500 | Parking Booths & Equipment | 4 | -2001180
 |  |  |  |  | G2020600 | Painted Lines & Markings | 4 | -2001180
 |  |  |  |  | G2020700 | Signage | 4 | -2001180
 |  |  |  |  | G2030 | Pedestrian Paving | 3
 |  |  |  |  | G2030100 | Bases & Sub-Bases | 4 | -2001260
 |  |  |  |  | G2030200 | Sidewalks | 4 | -2001260
 |  |  |  |  | G2030300 | Brick & Tile Plazas | 4 | -2001260
 |  |  |  |  | G2030400 | Edging | 4 | -2001260
 |  |  |  |  | G2030500 | Exterior Steps & Ramps | 4 | -2001260
 |  |  |  |  | G2030600 | Pedestrian Bridges | 4 | -2001260
 |  |  |  |  | G2040 | Site Development | 3
 |  |  |  |  | G2040100 | Fences & Gates | 4 | -2001260
 |  |  |  |  | G2040200 | Retaining Walls | 4 | -2001260
 |  |  |  |  | G2040300 | Terracing & Perimeter Walls | 4 | -2001260
 |  |  |  |  | G2040400 | Signage | 4 | -2001260
 |  |  |  |  | G2040500 | Site Furnishings | 4 | -2001260
 |  |  |  |  | G2040600 | Fountains, Pools & Watercourses | 4 | -2001260
 |  |  |  |  | G2040700 | Playing Fields | 4 | -2001260
 |  |  |  |  | G2040800 | Flagpoles | 4 | -2001260
 |  |  |  |  | G2040900 | Other Site Development | 4 | -2001260
 |  |  |  |  | G2050 | Landscaping | 3
 |  |  |  |  | G2050100 | Fine Grading & Soil Preparation | 4 | -2001360
 |  |  |  |  | G2050200 | Erosion Control Measures | 4 | -2001360
 |  |  |  |  | G2050300 | Vehicular Bridges | 4 | -2001360
 |  |  |  |  | G2050400 | Seeding & Sodding | 4 | -2001360
 |  |  |  |  | G2050500 | Planting | 4 | -2001360
 |  |  |  |  | G2050600 | Planters | 4 | -2001360
 |  |  |  |  | G2050700 | Irrigation Systems | 4 | -2001360
 |  |  |  |  | G2050900 | Other Landscape Features | 4 | -2001360
 |  |  |  |  | G30 | Site Mechanical Utilities | 2
 |  |  |  |  | G3010 | Water Supply | 3
 |  |  |  |  | G3010100 | Potable Water Distribution & Storage | 4 | -2001260
 |  |  |  |  | G3010200 | Non Potable Water Distribution & Storage | 4 | -2001260
 |  |  |  |  | G3010300 | Well Systems | 4 | -2001260
 |  |  |  |  | G3010400 | Fire Protection Distribution & Storage | 4 | -2001260
 |  |  |  |  | G3010500 | Pumping Stations | 4 | -2001260
 |  |  |  |  | G3010600 | Package Water Treatment Plants | 4 | -2001260
 |  |  |  |  | G3020 | Sanitary Sewer | 3
 |  |  |  |  | G3020100 | Sewage Piping | 4 | -2001260
 |  |  |  |  | G3020200 | Manholes & Cleanouts | 4 | -2001260
 |  |  |  |  | G3020300 | Septic Disposal Systems | 4 | -2001260
 |  |  |  |  | G3020400 | Lift Stations | 4 | -2001260
 |  |  |  |  | G3020500 | Packaged Water Waste Treatment Plants | 4 | -2001260
 |  |  |  |  | G3030 | Storm Sewer | 3
 |  |  |  |  | G3030100 | Storm Sewer Piping | 4 | -2001260
 |  |  |  |  | G3030200 | Manholes | 4 | -2001260
 |  |  |  |  | G3030300 | Headwalls & Catch Basins | 4 | -2001260
 |  |  |  |  | G3030400 | Lift Stations | 4 | -2001260
 |  |  |  |  | G3030500 | Retention Ponds | 4 | -2001260
 |  |  |  |  | G3030600 | Ditches & Culverts | 4 | -2001260
 |  |  |  |  | G3040 | Heating Distribution | 3
 |  |  |  |  | G3040100 | Steam Supply | 4 | -2001260
 |  |  |  |  | G3040200 | Condensate Return | 4 | -2001260
 |  |  |  |  | G3040300 | Hot Water Supply System | 4 | -2001260
 |  |  |  |  | G3040400 | Pumping Stations | 4 | -2001260
 |  |  |  |  | G3050 | Cooling Distribution | 3
 |  |  |  |  | G3050100 | Chilled Water Piping | 4 | -2001260
 |  |  |  |  | G3050200 | Wells for Cooling/Heating | 4 | -2001260
 |  |  |  |  | G3050300 | Pumping Stations | 4 | -2001260
 |  |  |  |  | G3050400 | Cooling Towers on Site | 4 | -2001260
 |  |  |  |  | G3060 | Fuel Distribution | 3
 |  |  |  |  | G3060100 | Fuel Piping | 4 | -2001260
 |  |  |  |  | G3060200 | Fuel Equipment | 4 | -2001260
 |  |  |  |  | G3060300 | Fuel Storage Tanks | 4 | -2001260
 |  |  |  |  | G3060400 | Fuel Dispensing Stations | 4 | -2001260
 |  |  |  |  | G3090 | Other Site Mechanical Utilities | 3
 |  |  |  |  | G3090100 | Industrial Waste Systems | 4 | -2001260
 |  |  |  |  | G3090200 | POL Distribution Systems | 4 | -2001260
 |  |  |  |  | G40 | Site Electrical Utilities | 2
 |  |  |  |  | G4010 | Electrical Distribution | 3
 |  |  |  |  | G4010100 | Substations | 4 | -2001260
 |  |  |  |  | G4010200 | Overhead Power Distribution | 4 | -2001260
 |  |  |  |  | G4010300 | Underground Power Distribution | 4 | -2001260
 |  |  |  |  | G4020 | Site Lighting | 3
 |  |  |  |  | G4020100 | Site Fixtures & Transformers | 4 | -2001260
 |  |  |  |  | G4020200 | Site Lighting Poles | 4 | -2001260
 |  |  |  |  | G4020300 | Wiring Conduits & Ductbanks | 4 | -2001260
 |  |  |  |  | G4020400 | Site Lighting Controls | 4 | -2001260
 |  |  |  |  | G4030 | Site Communication and Security | 3
 |  |  |  |  | G4030100 | Site Communications Systems | 4 | -2001260
 |  |  |  |  | G4030200 | Site Security & Alarm Systems | 4 | -2001260
 |  |  |  |  | G4040 | Other Site Electrical Utilities | 3
 |  |  |  |  | G4040100 | Cathodic Protection | 4 | -2001260
 |  |  |  |  | G4040200 | Site Emergency Power Generation | 4 | -2001260
 |  |  |  |  | G90 | Other Site Construction | 2
 |  |  |  |  | G9010 | Service and Pedestrian Tunnels | 3
 |  |  |  |  | G9010100 | Service Tunnels | 4 | -2001260
 |  |  |  |  | G9010200 | Trench Boxes | 4 | -2001260
 |  |  |  |  | G9010300 | Pedestrian Tunnels | 4 | -2001260
 |  |  |  |  | G9090 | Other Site Systems/Equipment | 3
 |  |  |  |  | G9090100 | Snow Melting Systems | 4 | -2001260
