OpeningDesign/CTR/XC_struct/xc_models/concrete_structure/footings_model/bearing_pressures.ods

Foundation | Worst | Vertical | Capacity
 | combination | load (kN) | factor
A1 | SLS04_a | -356.20 | 0.33 | -356203.177512063
A2 | SLS02_a | -644.78 | 0.60 | -644783.375789382
A3 | SLS02_a | -950.92 | 0.88 | -950919.785414999
A4 | SLS02_a | -881.82 | 0.82 | -881823.494723676
A5 | SLS04_b | -933.03 | 0.86 | -933025.803604793
B1 | SLS02_a | -429.53 | 0.36 | -429531.14687972
B2 | SLS02_a | -670.79 | 0.56 | -670793.896589334
B3 | SLS02_a | -1,030.65 | 0.86 | -1030654.59603588
B4 | SLS02_a | -968.24 | 0.80 | -968243.012142857
B5 | SLS04_b | -972.32 | 0.81 | -972316.618446986
C1 | SLS02_a | -1,460.67 | 0.99 | -1460674.59932403
C2 | SLS02_a | -1,742.45 | 0.99 | -1742449.38209939
C3 | SLS02_a | -1,750.31 | 0.99 | -1750308.72105841
C4 | SLS02_a | -1,751.62 | 0.99 | -1751624.92859094
C5 | SLS02_a | -1,660.02 | 0.94 | -1660022.90250694
D1 | SLS02_a | -1,648.12 | 1.02 | -1648115.18761229
D2 | SLS04_a | -1,950.01 | 1.01 | -1950010.9858643
D3 | SLS04_a | -1,959.12 | 1.02 | -1959115.54635968
D4 | SLS04_a | -1,960.14 | 1.02 | -1960137.00407632
D5 | SLS04_a | -1,838.69 | 0.96 | -1838687.19405608
F1 | SLS02_a | -1,090.88 | 0.82 | -1090875.04347262
F2 | SLS02_a | -997.32 | 0.75 | -997316.986748519
F3 | SLS02_a | -1,011.87 | 0.76 | -1011866.20243065
F4 | SLS02_a | -1,005.30 | 0.75 | -1005304.64520423
F5 | SLS04_b | -741.90 | 0.56 | -741902.470344851
G1 | SLS02_a | -1,496.86 | 0.93 | -1496862.96639827
G2 | SLS02_a | -1,256.06 | 0.78 | -1256055.44218362
G3 | SLS02_a | -1,227.94 | 0.76 | -1227939.08701163
G4 | SLS02_a | -1,137.75 | 0.70 | -1137751.24666422
G5 | SLS04_b | -1,167.26 | 0.72 | -1167262.33537698
