OpeningDesign/CTR/Transfer/20190814 - Wall Sections - Ref Callouts & Material tags updates/CTR - 1st Phase - Details - B - Sheet - A503 - DETAILS - STAIRS.jpg

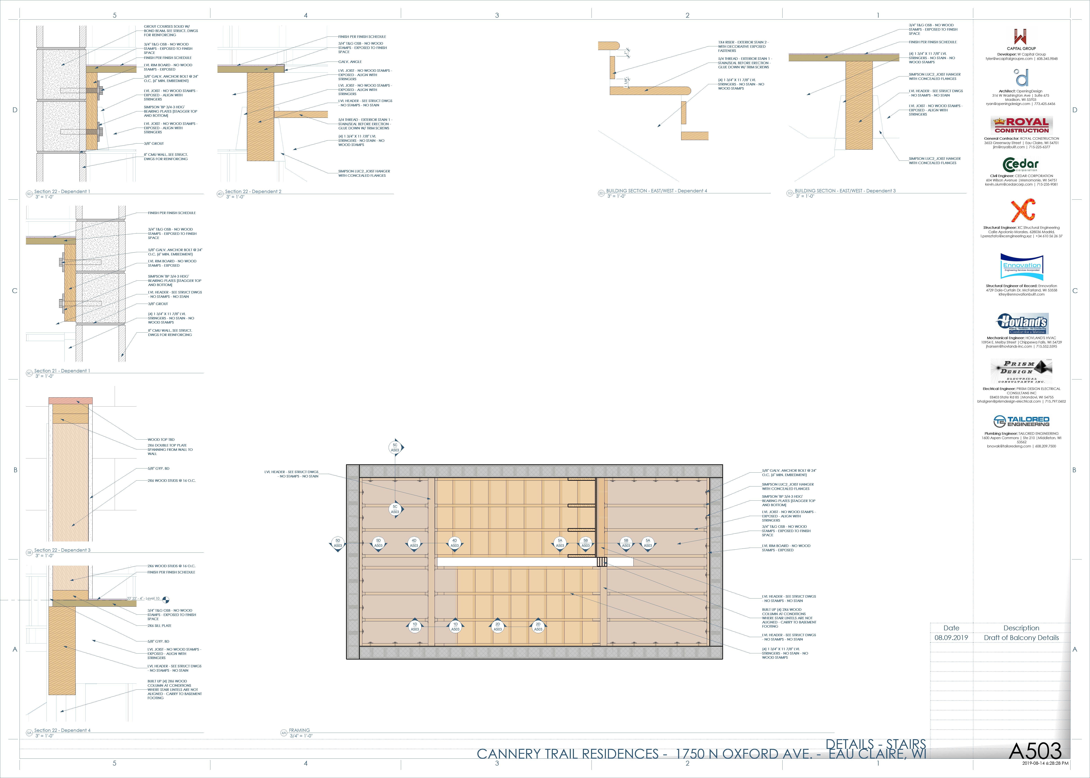
Transfer/20190814 - Wall Sections - Ref Callouts & Material tags updates/CTR - 1st Phase - Details - B - Sheet - A503 - DETAILS - STAIRS.jpg
