OpeningDesign/CTR/Transfer/20190814 - Wall Sections - Ref Callouts & Material tags updates/CTR - 1st Phase - Shell - Sheet - A402 - WALL SECTION.jpg

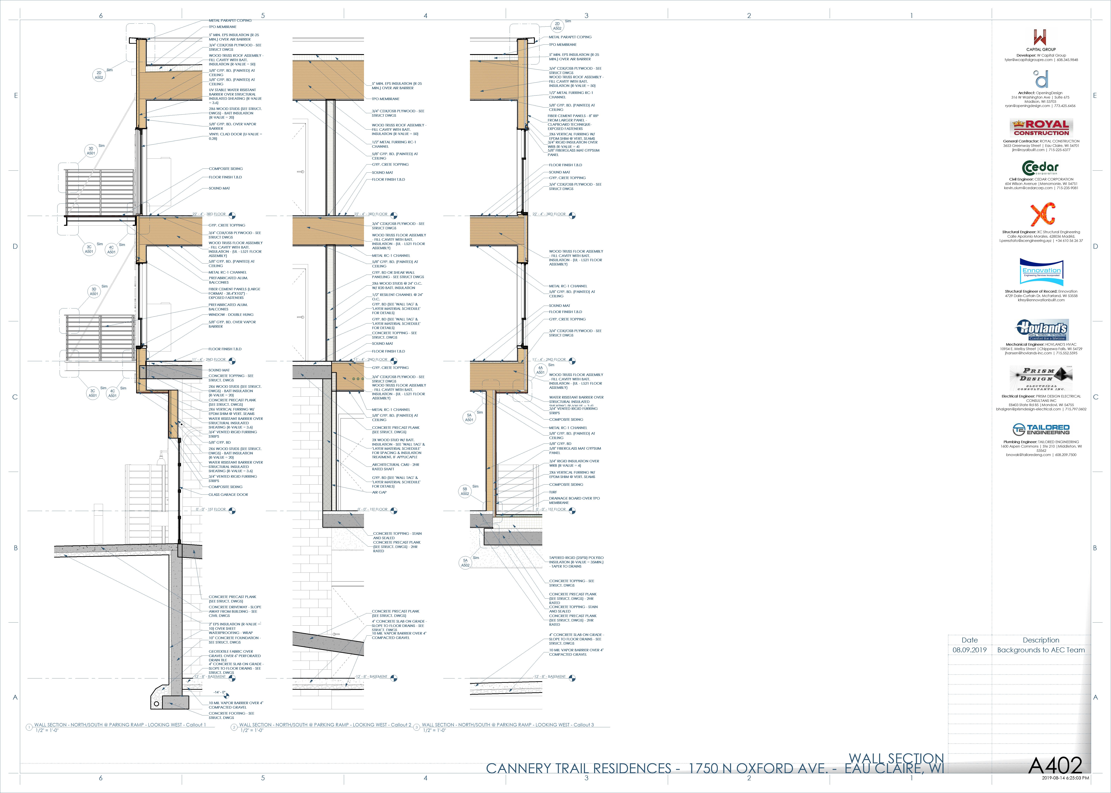
Transfer/20190814 - Wall Sections - Ref Callouts & Material tags updates/CTR - 1st Phase - Shell - Sheet - A402 - WALL SECTION.jpg
