OpeningDesign/CTR/XC_struct/xc_models/concrete_structure/basement_walls/lintel_24_span_modif_20191126/20191213_revision/lintel_model.dxf

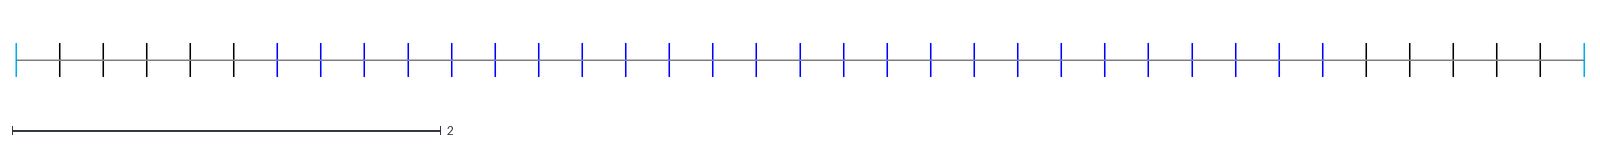
[picture p389: CAD file, 2020-07-19]
XC_struct/xc_models/concrete_structure/basement_walls/lintel_24_span_modif_20191126/20191213_revision/lintel_model.dxf
7.32 x 0.154
