OpeningDesign/CTR/XC_struct/xc_models/wood_structure/kurt_jack_trusses_proposal/model.dxf

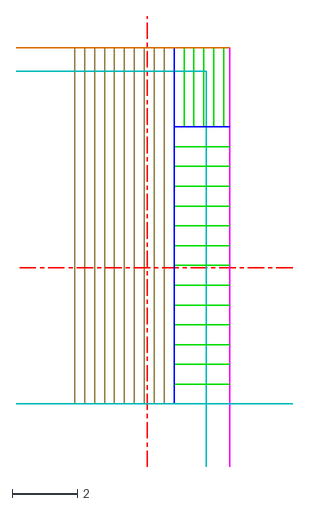
[picture p390: CAD file, 2020-07-19]
XC_struct/xc_models/wood_structure/kurt_jack_trusses_proposal/model.dxf
8.48 x 13.8
