OpeningDesign/CTR/XC_struct/xc_models/wood_structure/stud_wall_design/tributary_areas.dxf

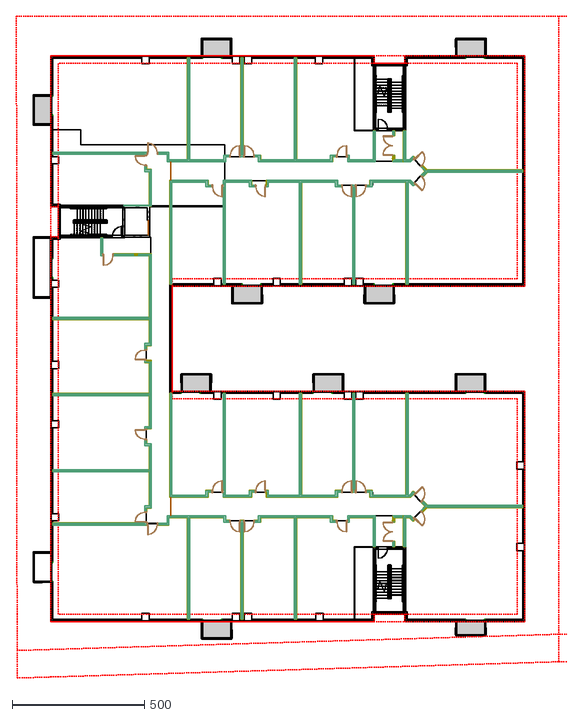
[picture p391: CAD file, 2020-07-19]
XC_struct/xc_models/wood_structure/stud_wall_design/tributary_areas.dxf
2078.9 x 2501.4
