OpeningDesign/CTR/Transfer/20180904 - CAD floor plans from Madison/Willy-Floor Plan - FLOOR PLAN - 1ST FLOOR.dxf

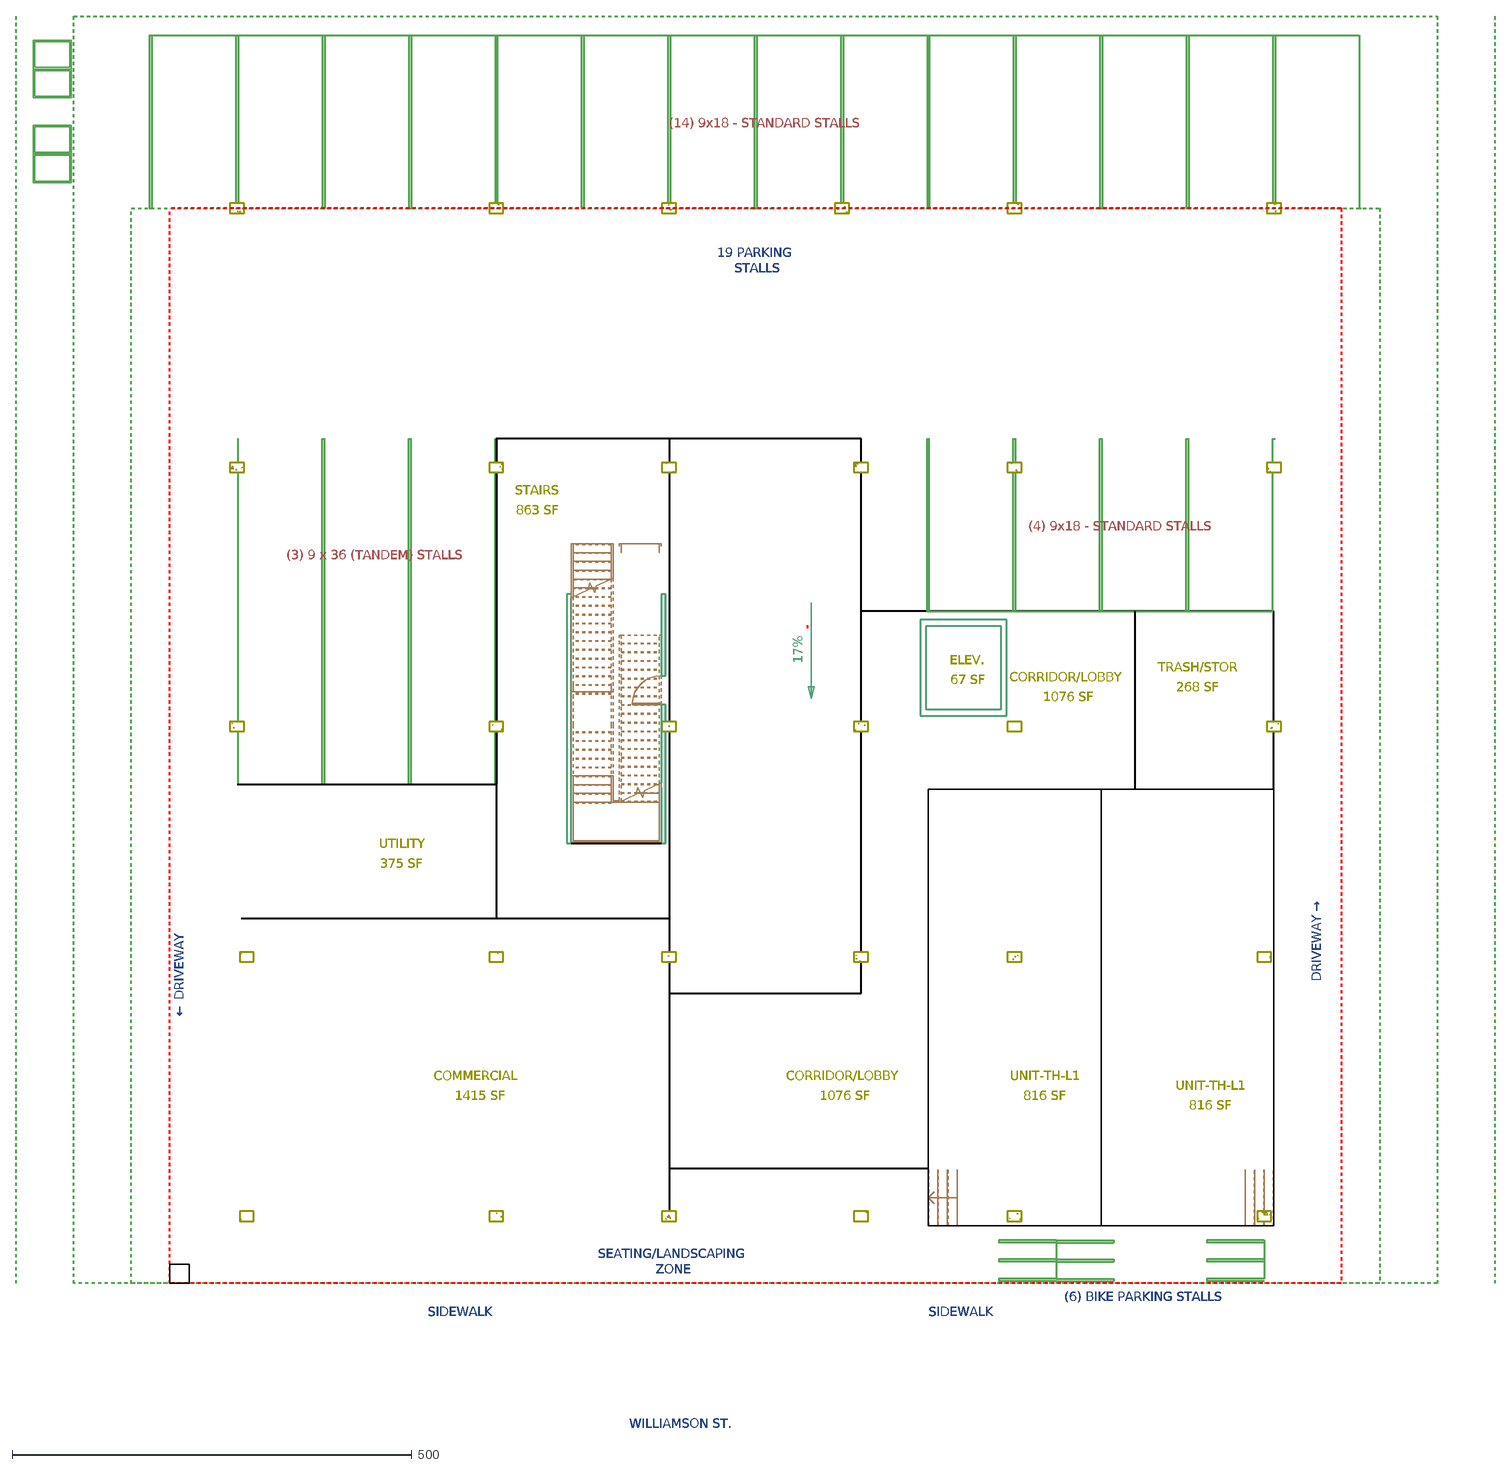
[picture p392: CAD file, 2019-05-28]
Transfer/20180904 - CAD floor plans from Madison/Willy-Floor Plan - FLOOR PLAN - 1ST FLOOR.dxf
1415 SF
COMMERCIAL
816 SF
UNIT-TH-L1
←
DRIVEWAY
→
19 PARKING
STALLS
268 SF
TRASH/STOR
SIDEWALK
WILLIAMSON ST.
(14) 9x18 - STANDARD STALLS
(3) 9 x 36 (TANDEM) STALLS
(4) 9x18 - STANDARD STALLS
SEATING/LANDSCAPING
ZONE
17%
(6) BIKE PARKING STALLS
375 SF
UTILITY
863 SF
STAIRS
1076 SF
CORRIDOR/LOBBY
67 SF
ELEV.
