OpeningDesign/CTR/XC_struct/xc_models/wood_structure/kurt_jack_trusses_proposal/model2.dxf

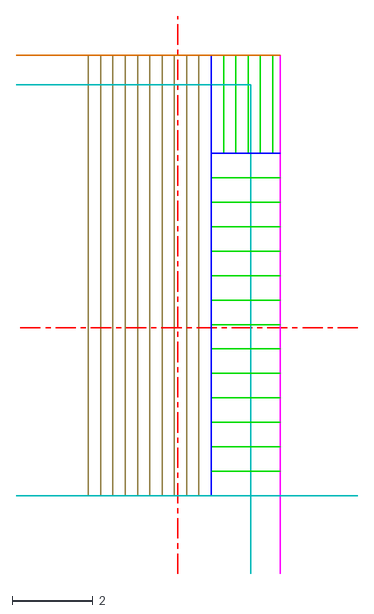
[picture p393: CAD file, 2020-07-19]
XC_struct/xc_models/wood_structure/kurt_jack_trusses_proposal/model2.dxf
8.48 x 13.8
