OpeningDesign/CTR/Transfer/20180904 - CAD floor plans from Madison/Willy-Floor Plan - FLOOR PLAN - 5TH FLOOR.dxf

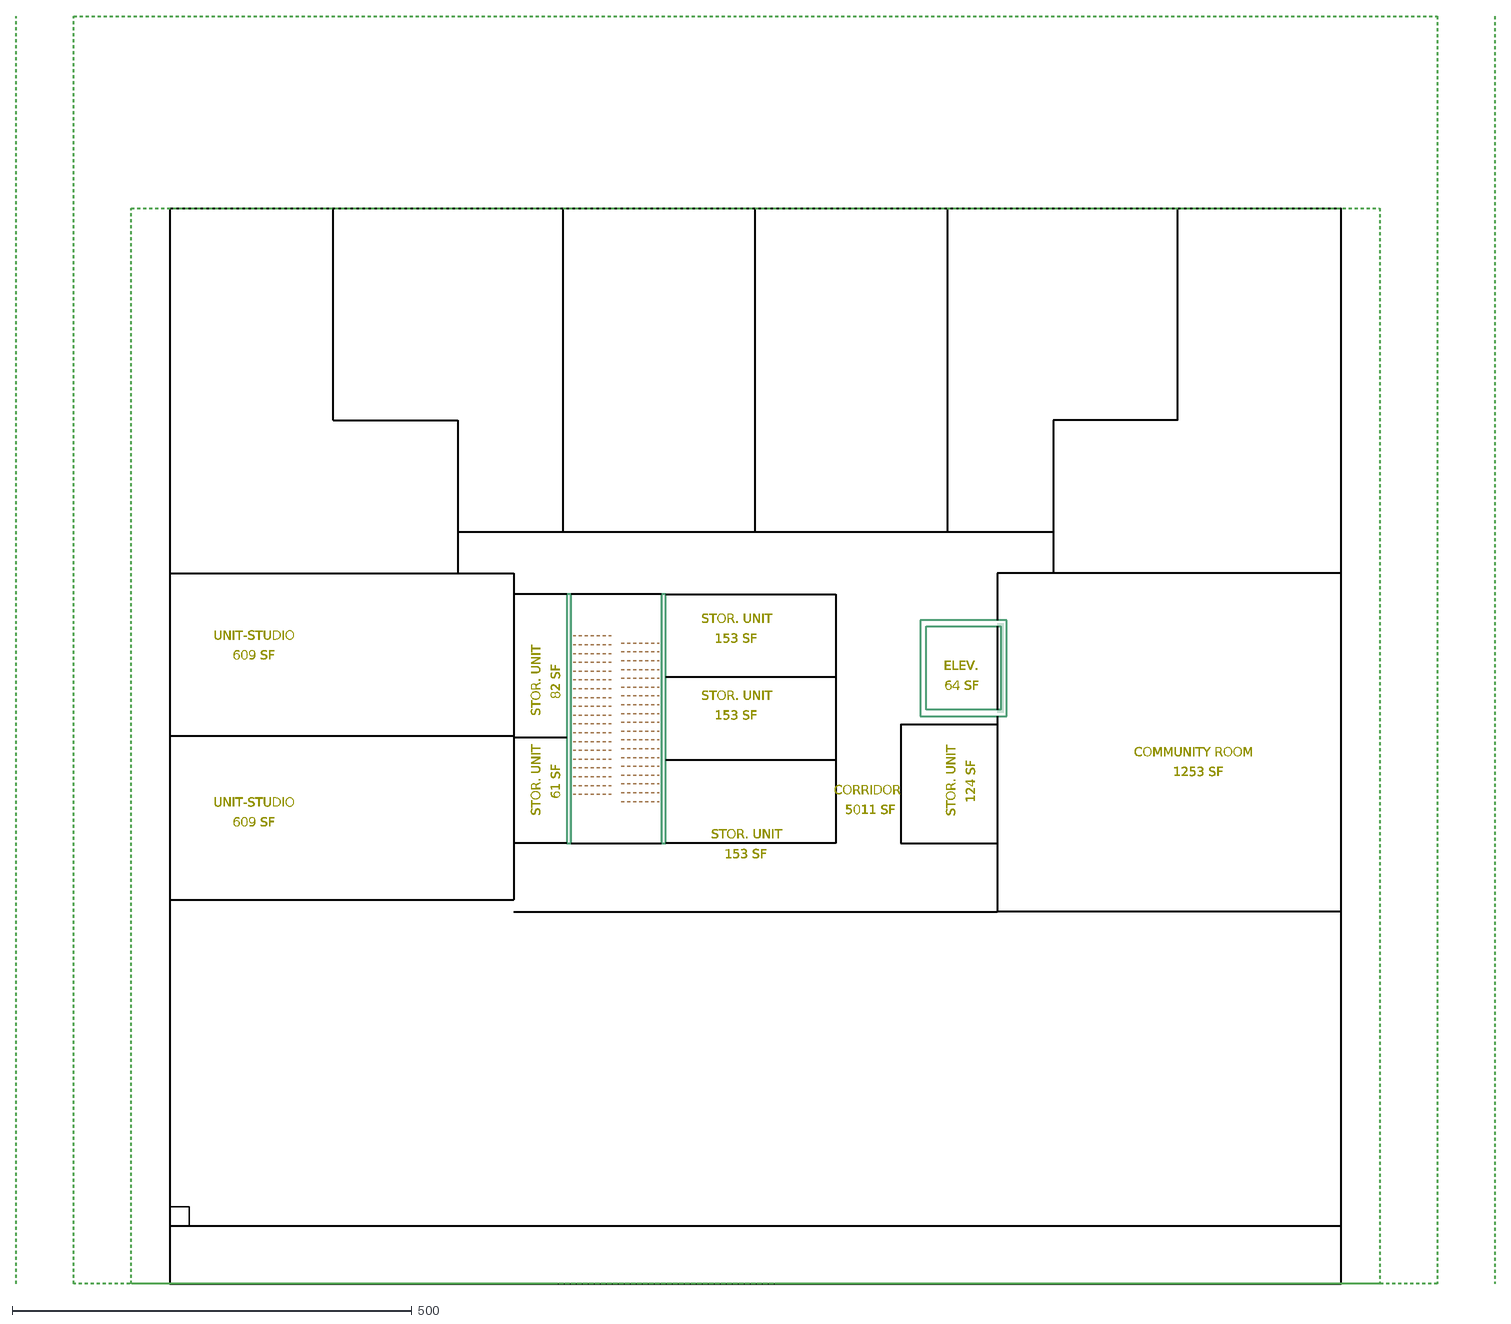
[picture p394: CAD file, 2019-05-28]
Transfer/20180904 - CAD floor plans from Madison/Willy-Floor Plan - FLOOR PLAN - 5TH FLOOR.dxf
609 SF
UNIT-STUDIO
1253 SF
COMMUNITY ROOM
82 SF
STOR. UNIT
61 SF
153 SF
124 SF
5011 SF
CORRIDOR
64 SF
ELEV.
