OpeningDesign/CTR/Transfer/20200122 - to MECH - elevations and sections for coordination/CTR - 1st Phase - Shell - Sheet - A201 - ELEVATIONS - BUILDING.jpg

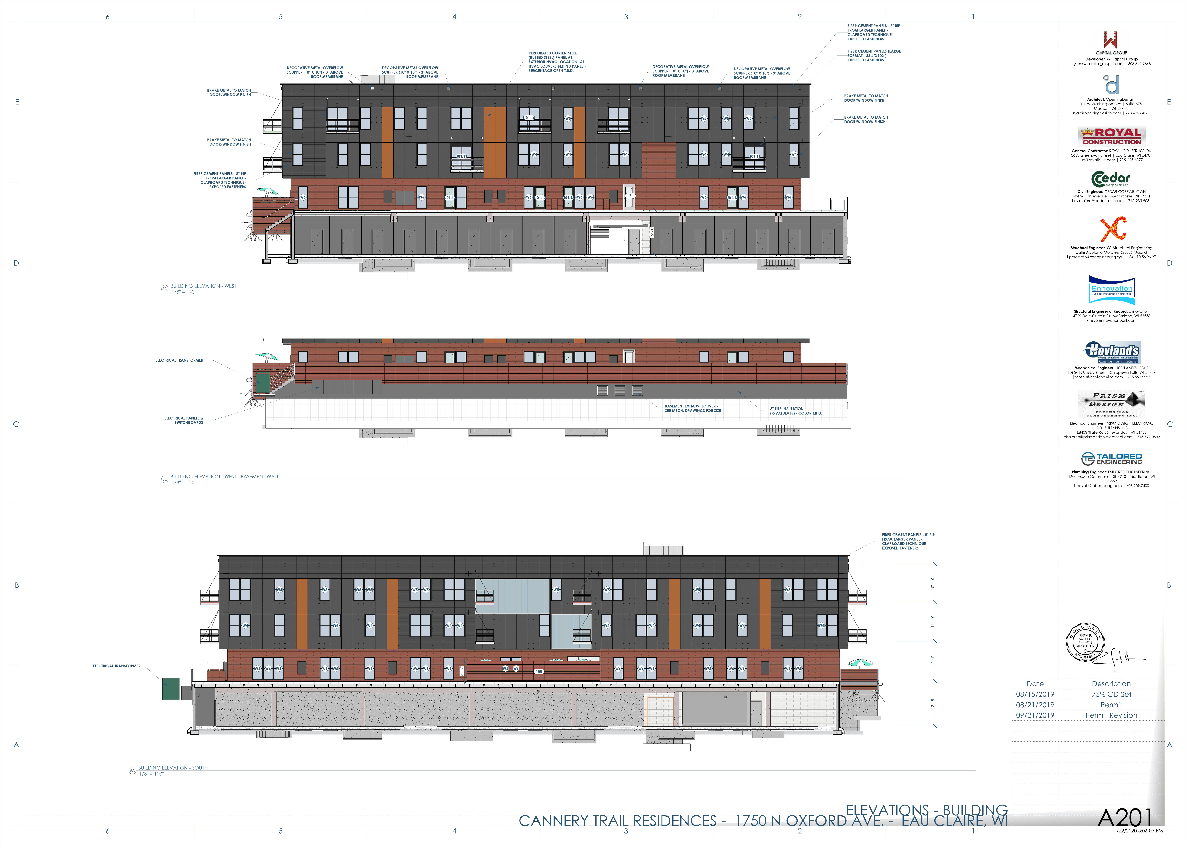
Transfer/20200122 - to MECH - elevations and sections for coordination/CTR - 1st Phase - Shell - Sheet - A201 - ELEVATIONS - BUILDING.jpg
