OpeningDesign/CTR/Transfer/Internal/20200715 - Internal full set print/CTR - 1st Phase - Common Walls - Sheet - A021 - LIFE SAFETY.jpg

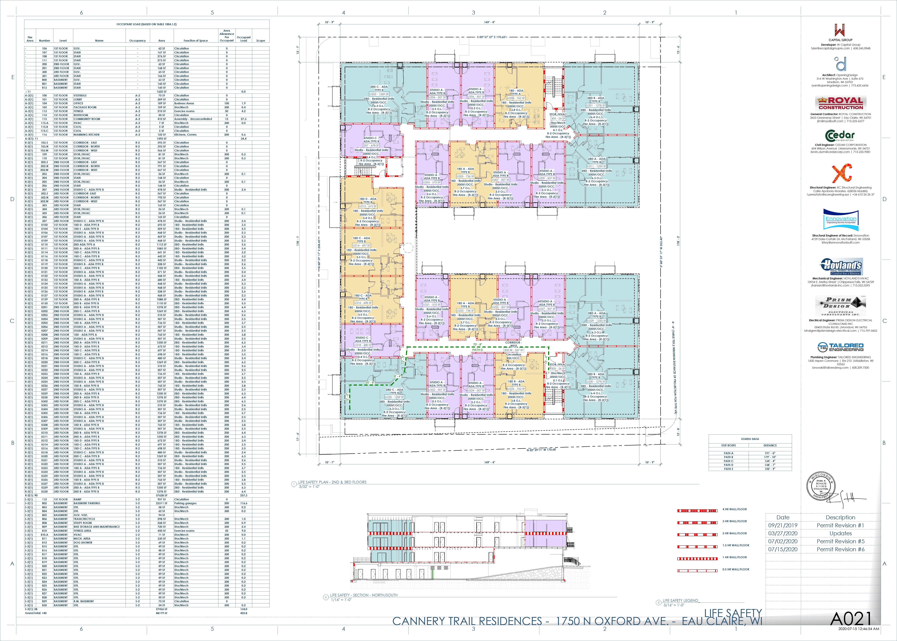
Transfer/Internal/20200715 - Internal full set print/CTR - 1st Phase - Common Walls - Sheet - A021 - LIFE SAFETY.jpg
