OpeningDesign/CTR/Transfer/Internal/20200715 - Internal full set print/CTR - 1st Phase - Common Walls - Sheet - A103 - FLOOR PLAN - 3RD FLOOR.jpg

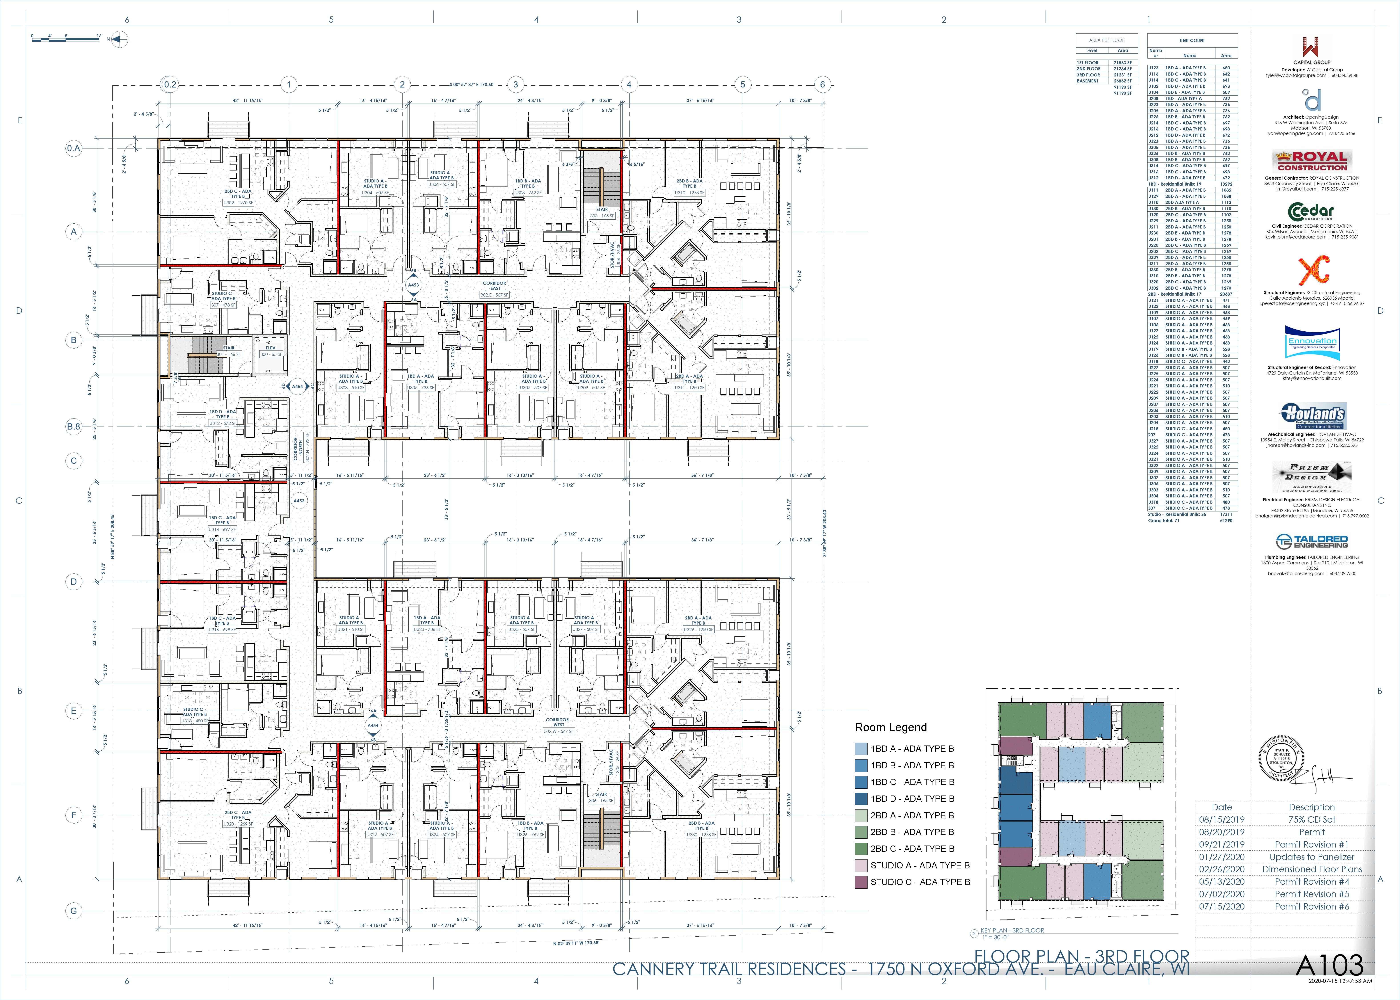
Transfer/Internal/20200715 - Internal full set print/CTR - 1st Phase - Common Walls - Sheet - A103 - FLOOR PLAN - 3RD FLOOR.jpg
