OpeningDesign/CTR/Transfer/Internal/20200715 - Internal full set print/CTR - 1st Phase - Common Walls - Sheet - A410-B - ENLARGED FLOOR PLAN - BASEMENT WEST.jpg

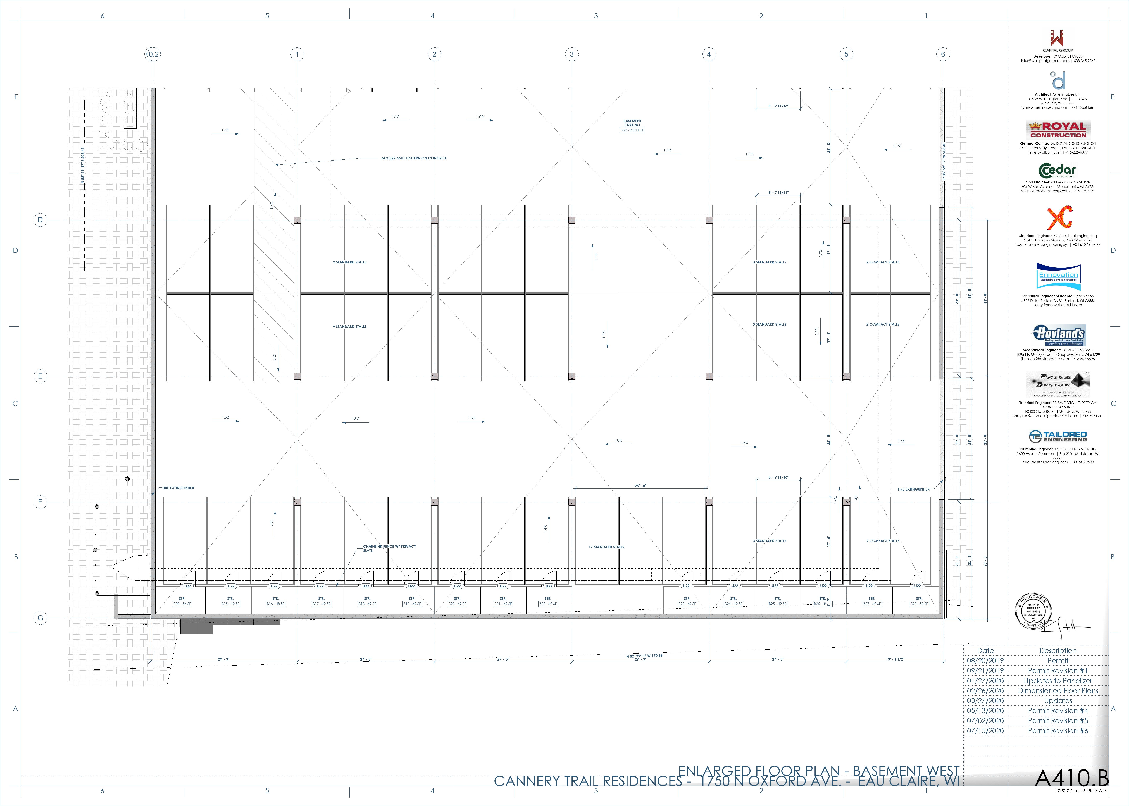
Transfer/Internal/20200715 - Internal full set print/CTR - 1st Phase - Common Walls - Sheet - A410-B - ENLARGED FLOOR PLAN - BASEMENT WEST.jpg
