OpeningDesign/CTR/Transfer/Internal/20200715 - Internal full set print/CTR - 1st Phase - Common Walls - Sheet - A420 - RCP PLANS - BASEMENT.jpg

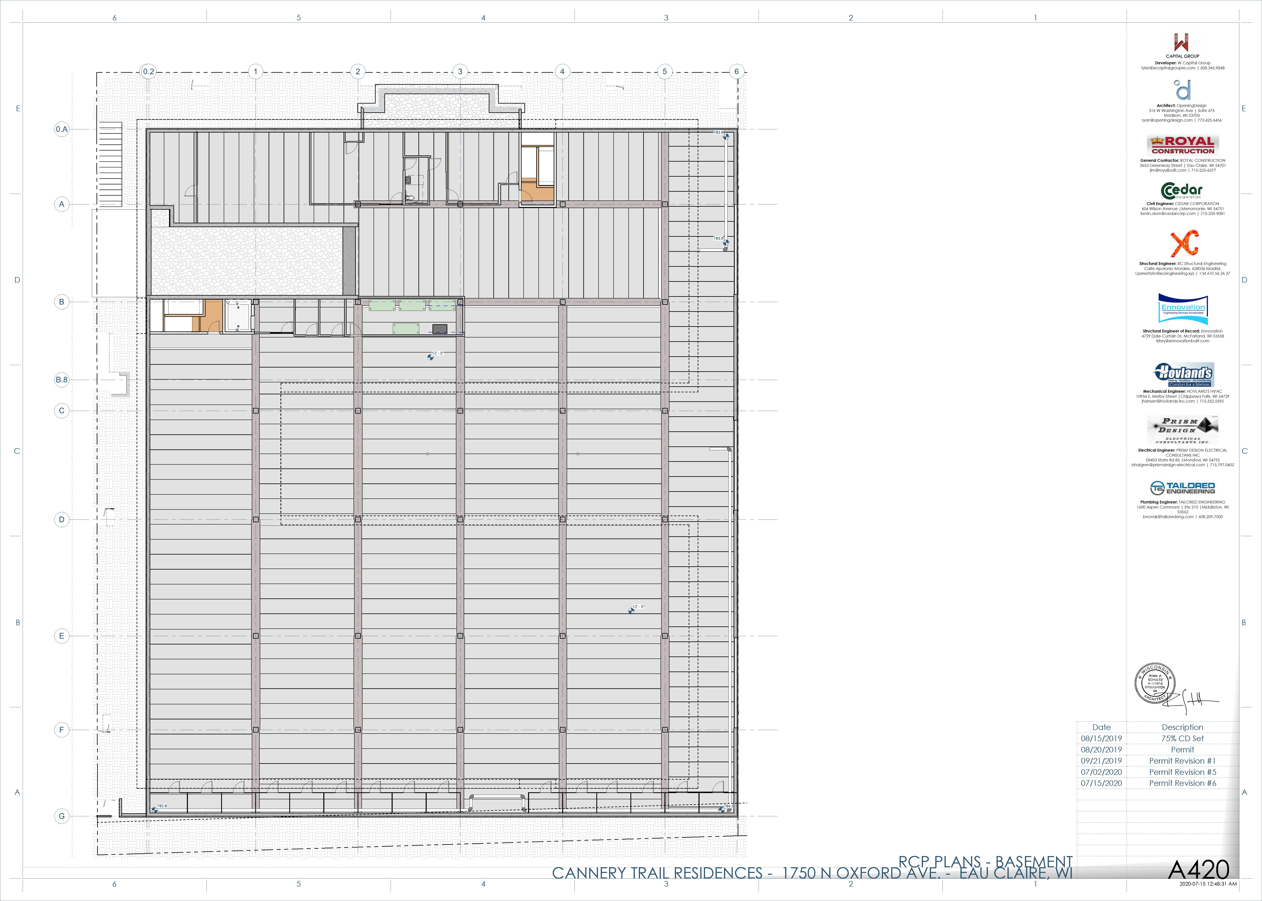
Transfer/Internal/20200715 - Internal full set print/CTR - 1st Phase - Common Walls - Sheet - A420 - RCP PLANS - BASEMENT.jpg
