OpeningDesign/CTR/Transfer/Internal/20200715 - Internal full set print/CTR - 1st Phase - Common Walls - Sheet - D0 - DIAGRAM - FLOOR PLAN - BASEMENT.jpg

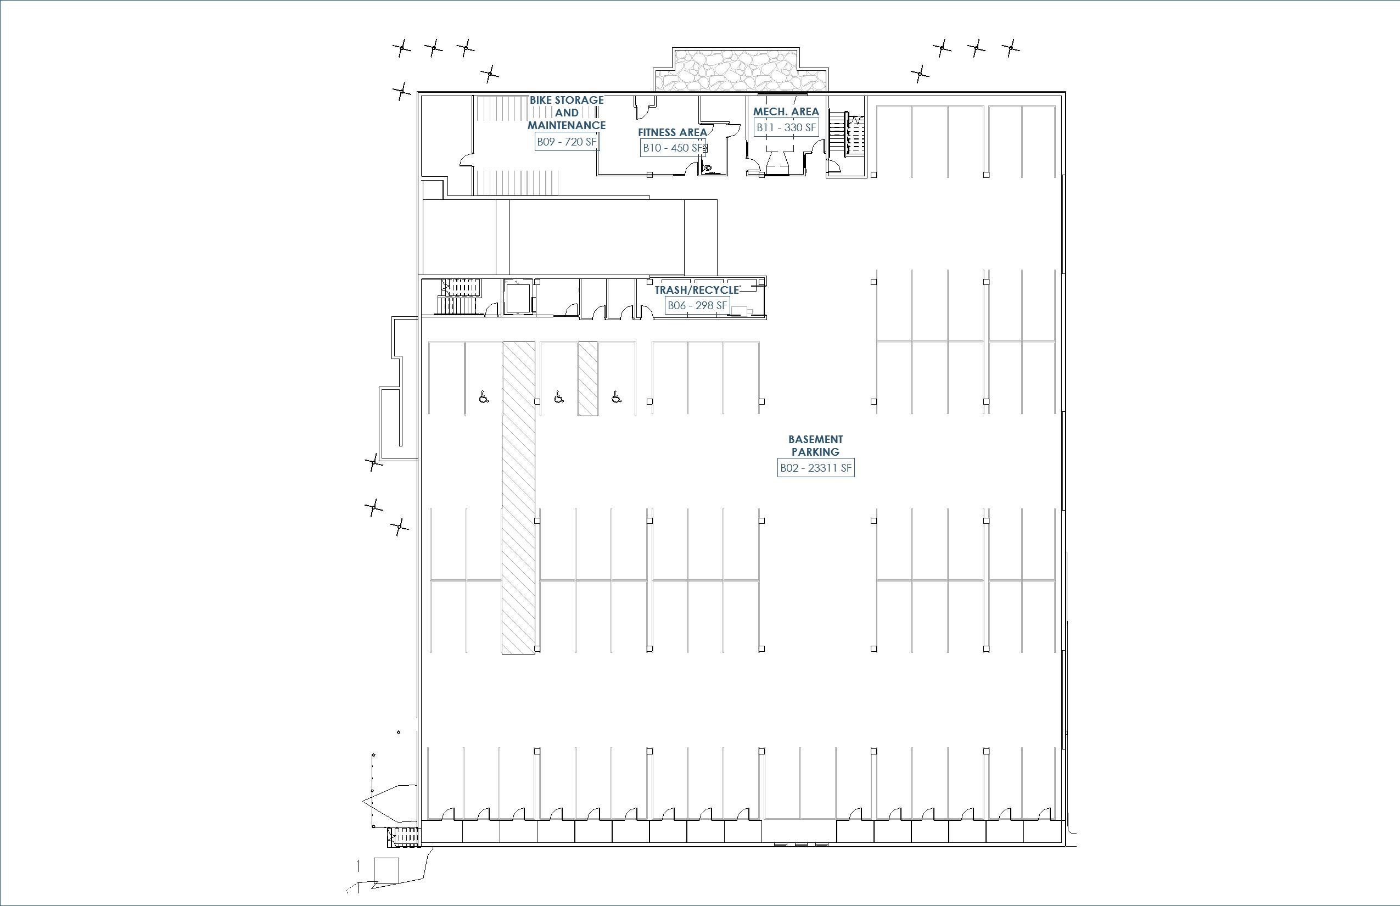
Transfer/Internal/20200715 - Internal full set print/CTR - 1st Phase - Common Walls - Sheet - D0 - DIAGRAM - FLOOR PLAN - BASEMENT.jpg
