OpeningDesign/CTR/Transfer/Internal/20200715 - Internal full set print/CTR - 1st Phase - Common Walls - Sheet - D1 - DIAGRAM - FLOOR PLAN - 1ST.jpg

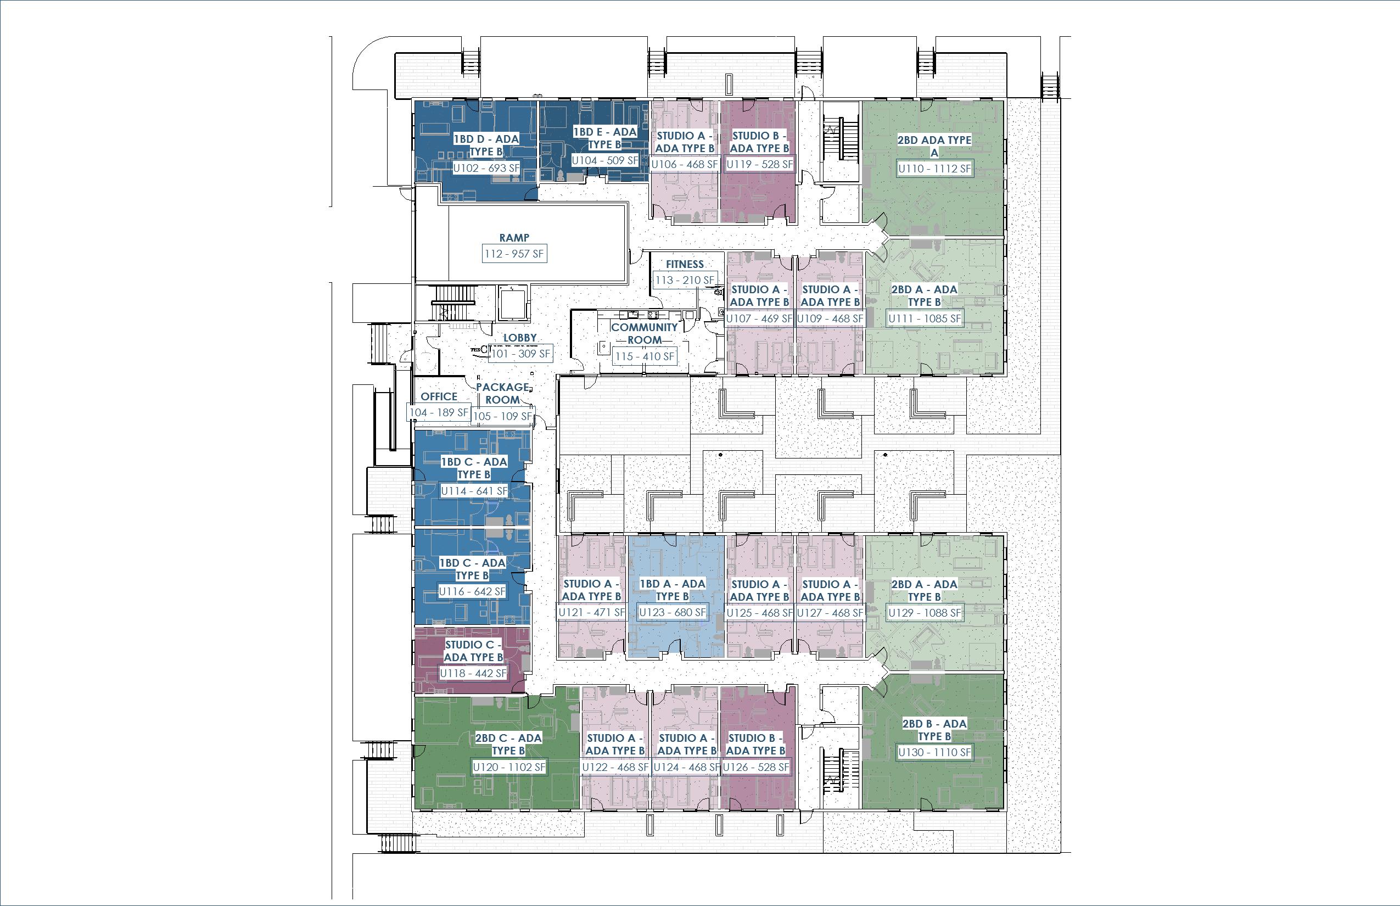
Transfer/Internal/20200715 - Internal full set print/CTR - 1st Phase - Common Walls - Sheet - D1 - DIAGRAM - FLOOR PLAN - 1ST.jpg
