OpeningDesign/CTR/Transfer/Internal/20200715 - Internal full set print/CTR - 1st Phase - Details - B - Sheet - A503 - DETAILS - STAIRS.jpg

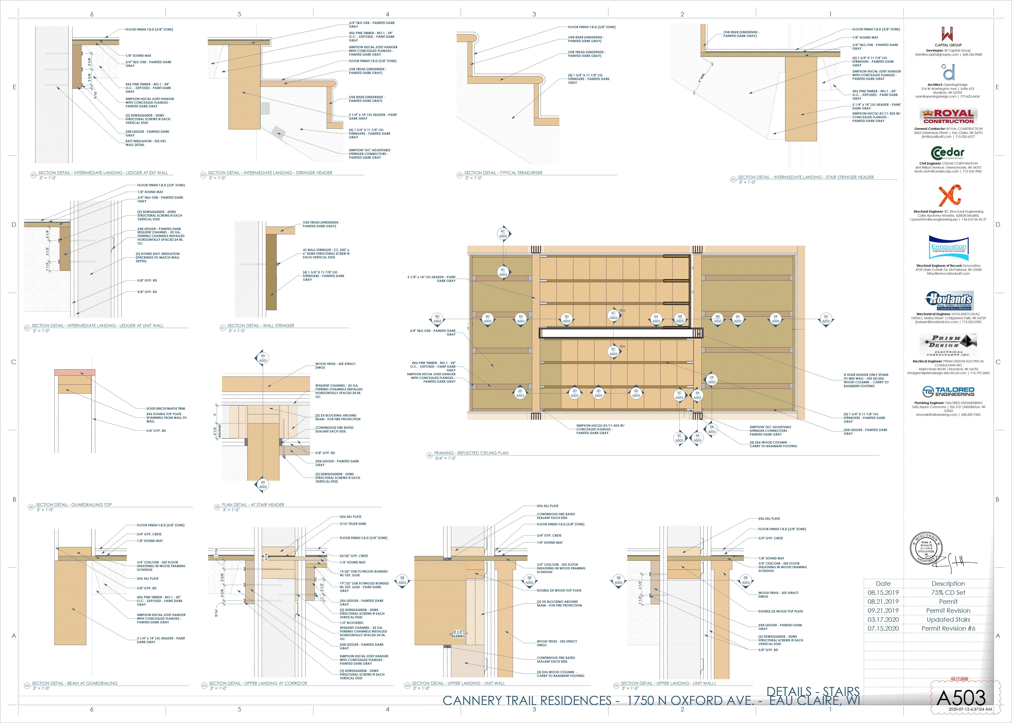
Transfer/Internal/20200715 - Internal full set print/CTR - 1st Phase - Details - B - Sheet - A503 - DETAILS - STAIRS.jpg
