OpeningDesign/CTR/Transfer/Internal/20200715 - Internal full set print/CTR - 1st Phase - Details - C - Planter - Sheet - A504 - DETAILS - PLANTER.jpg

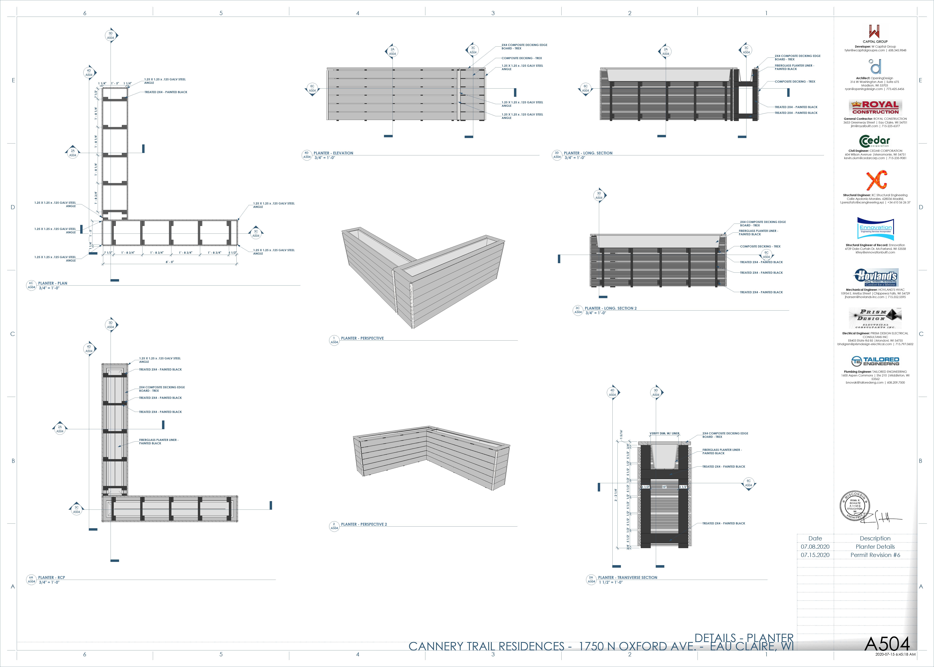
Transfer/Internal/20200715 - Internal full set print/CTR - 1st Phase - Details - C - Planter - Sheet - A504 - DETAILS - PLANTER.jpg
