OpeningDesign/CTR/Transfer/Internal/20200715 - Internal full set print/CTR - 1st Phase - Partition Details - Sheet - A800 - PARTITION DETAILS.jpg

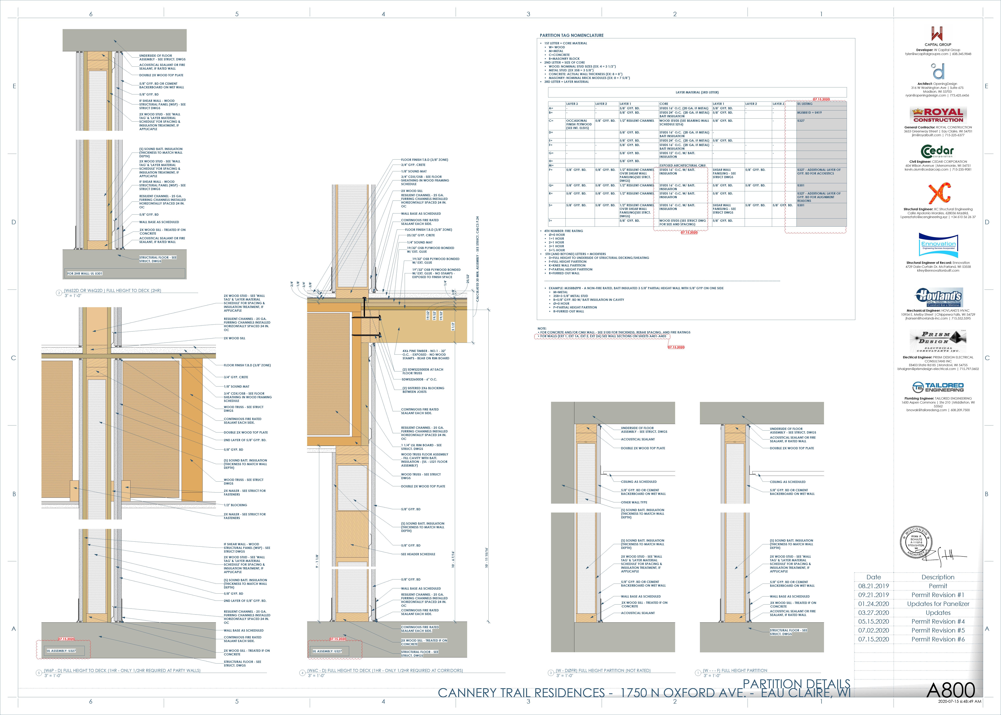
Transfer/Internal/20200715 - Internal full set print/CTR - 1st Phase - Partition Details - Sheet - A800 - PARTITION DETAILS.jpg
