OpeningDesign/CTR/Transfer/Internal/20200715 - Internal full set print/CTR - 1st Phase - Shell - Sheet - A402 - SECTIONS - WALL.jpg

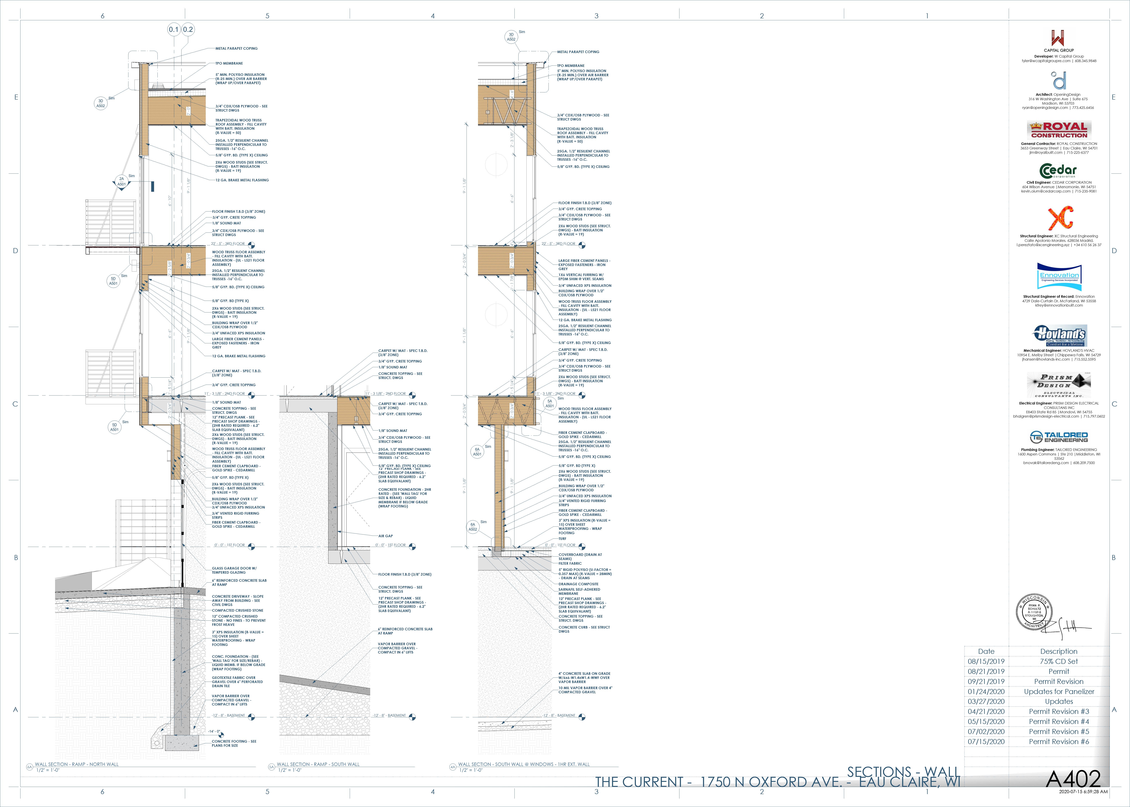
Transfer/Internal/20200715 - Internal full set print/CTR - 1st Phase - Shell - Sheet - A402 - SECTIONS - WALL.jpg
