OpeningDesign/CTR/Transfer/Internal/20200715 - Internal full set print/CTR - 1st Phase - Structure - Sheet - S101 - ENLARGED PLANS.jpg

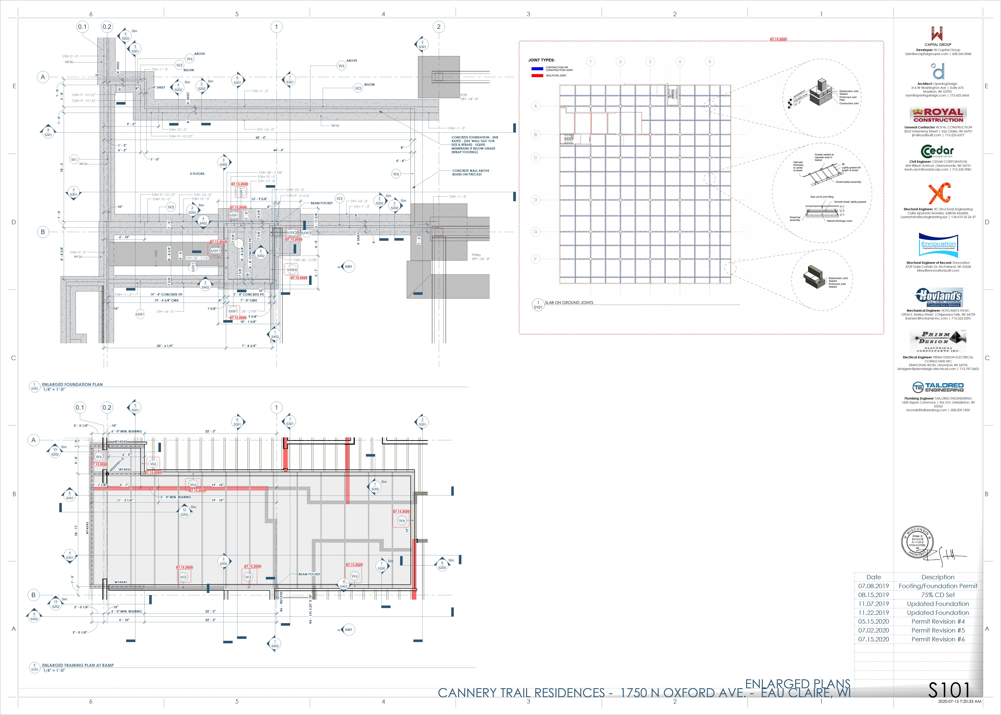
Transfer/Internal/20200715 - Internal full set print/CTR - 1st Phase - Structure - Sheet - S101 - ENLARGED PLANS.jpg
