OpeningDesign/CTR/Transfer/Internal/20200715 - Internal full set print/CTR - 1st Phase - Structure - Sheet - S201 - STRUCTURAL DETAILS.jpg

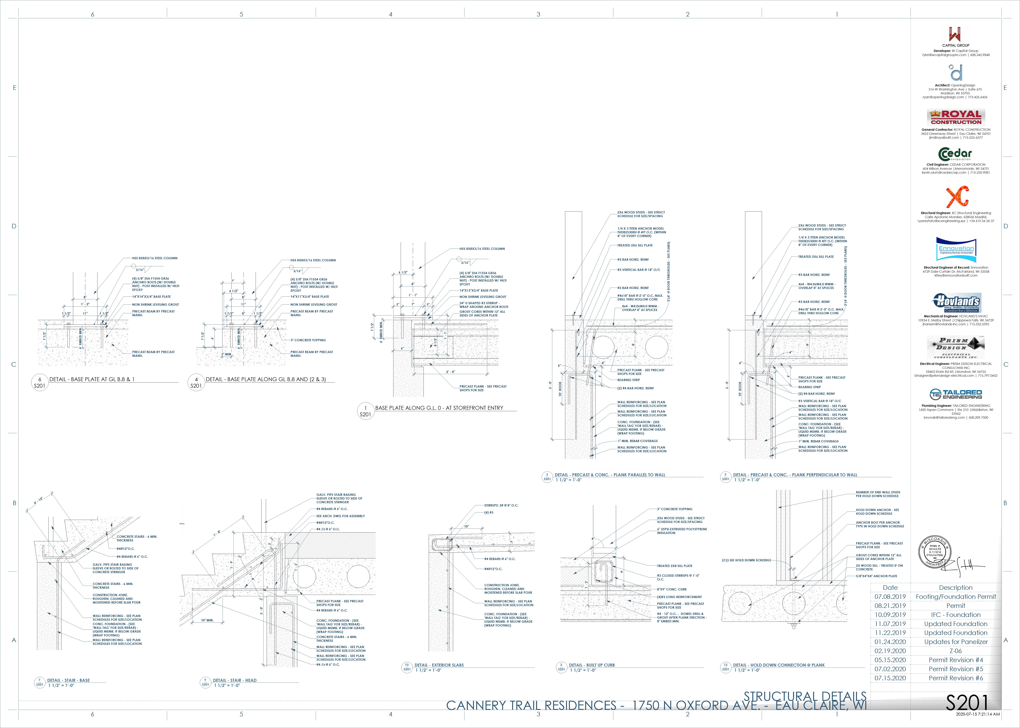
Transfer/Internal/20200715 - Internal full set print/CTR - 1st Phase - Structure - Sheet - S201 - STRUCTURAL DETAILS.jpg
