OpeningDesign/CTR/Transfer/Internal/20200715 - Internal full set print/CTR - 1st Phase - Structure - Sheet - S211 - FRAMING PLAN - 2ND FLOOR.jpg

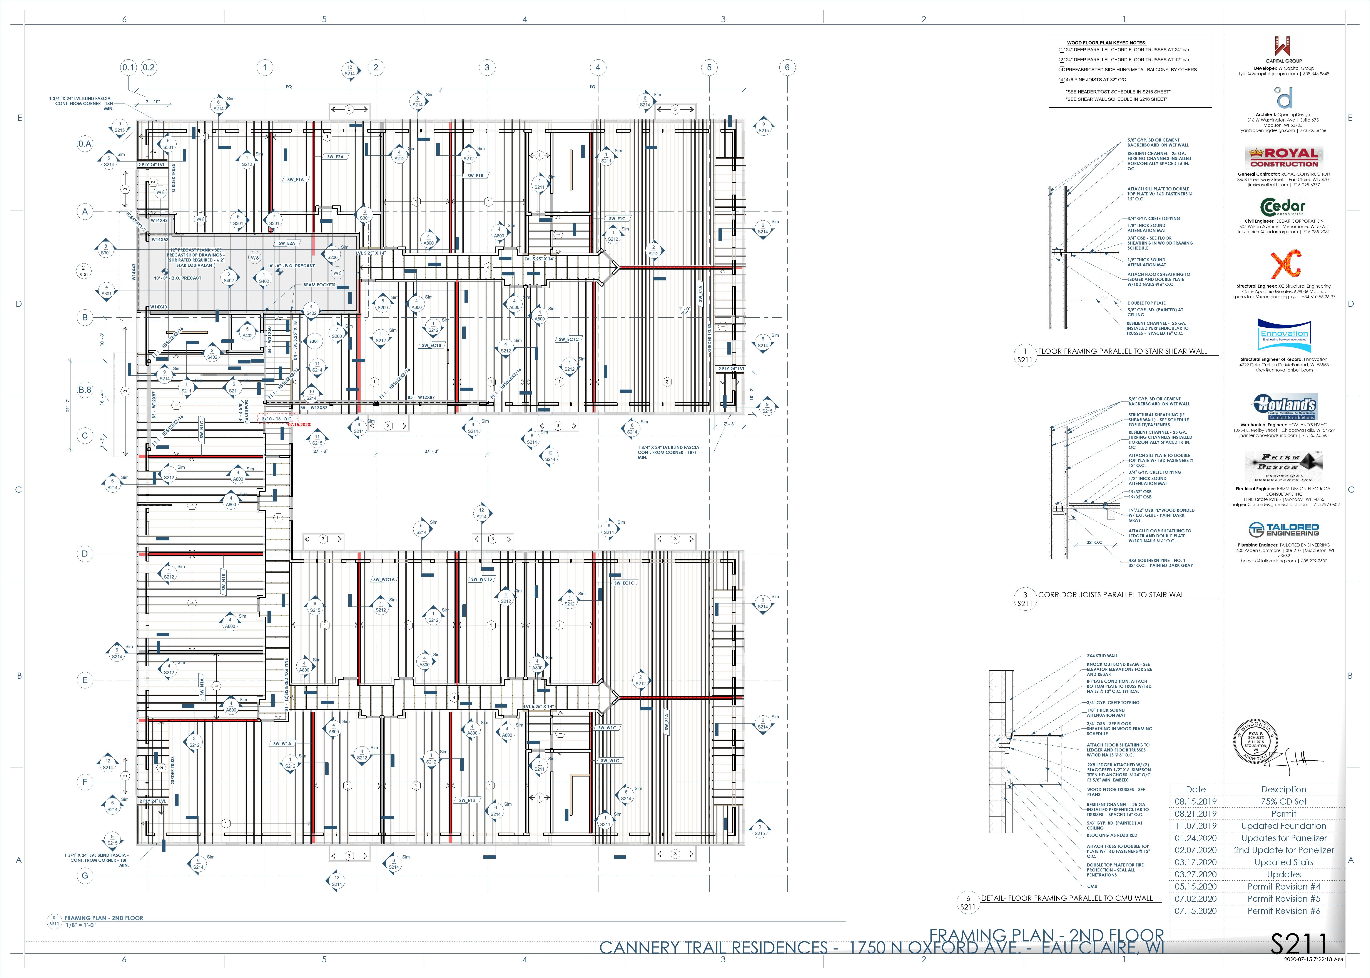
Transfer/Internal/20200715 - Internal full set print/CTR - 1st Phase - Structure - Sheet - S211 - FRAMING PLAN - 2ND FLOOR.jpg
