OpeningDesign/CTR/Transfer/Internal/20200715 - Internal full set print/CTR - 1st Phase - Structure - Sheet - S212 - FRAMING PLAN - 3RD FLOOR.jpg

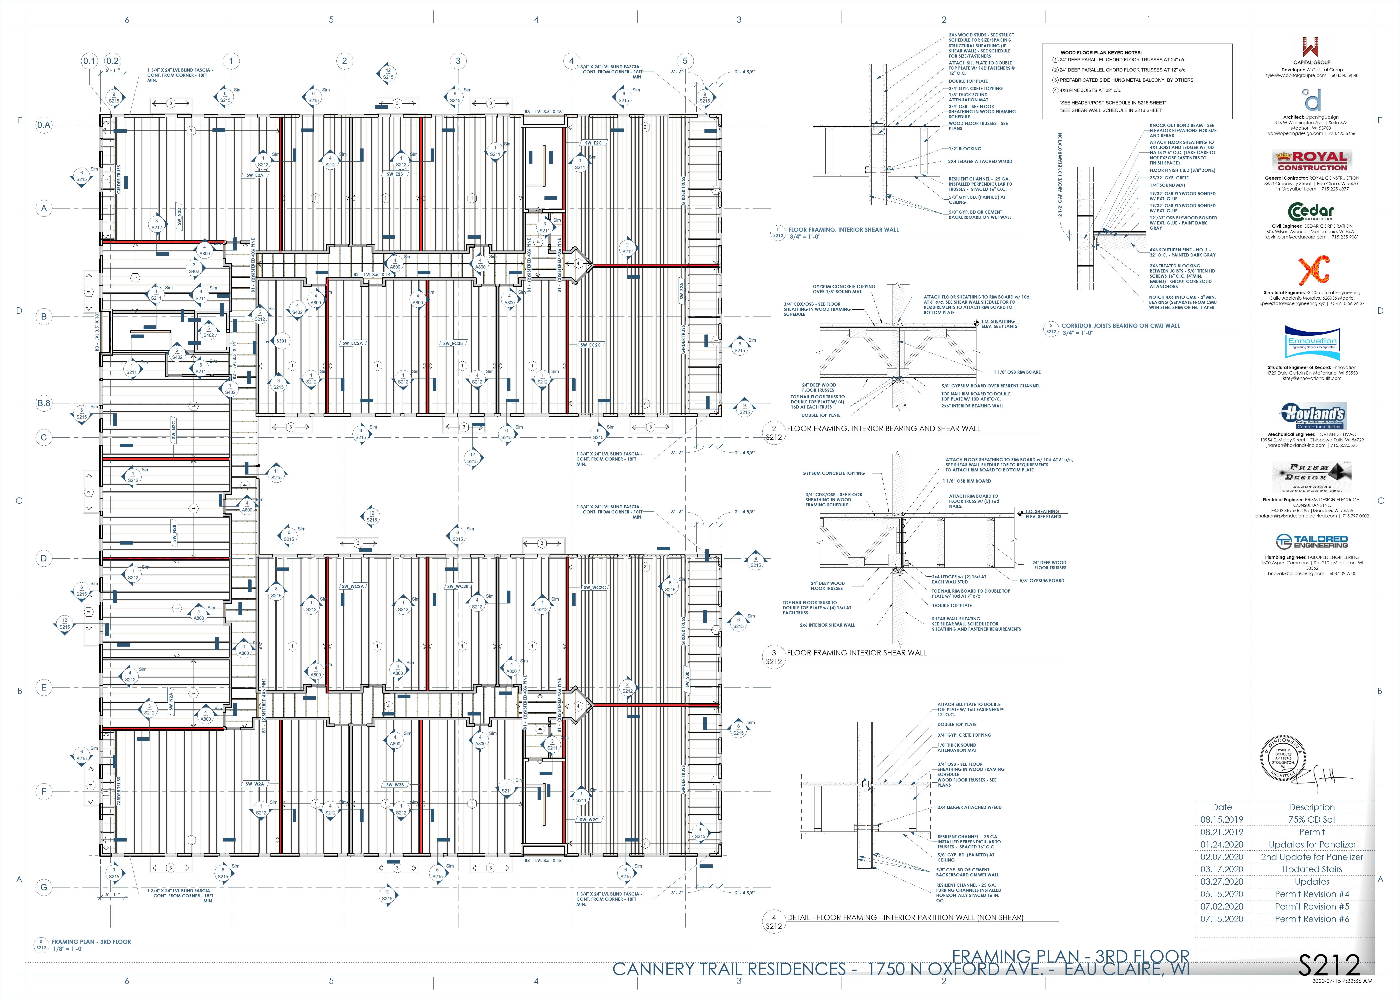
Transfer/Internal/20200715 - Internal full set print/CTR - 1st Phase - Structure - Sheet - S212 - FRAMING PLAN - 3RD FLOOR.jpg
