OpeningDesign/CTR/Transfer/Internal/20200715 - Internal full set print/CTR - 1st Phase - Unit Layouts - Sheet - A411-B - ENLARGED PLAN 1ST - AREA B (SOUTHEAST).jpg

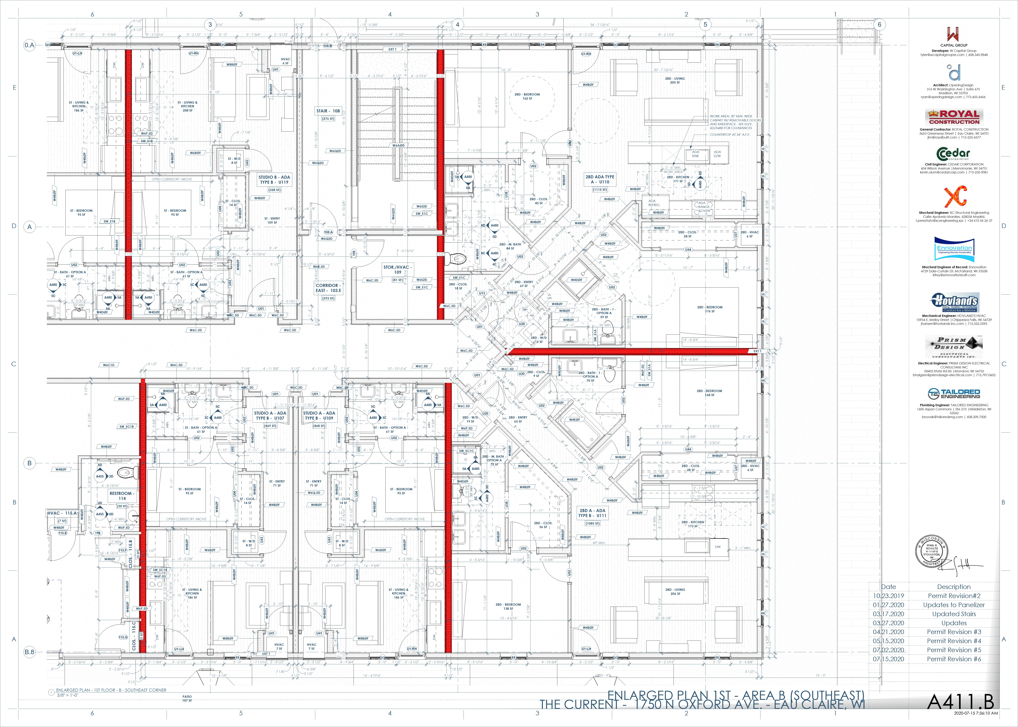
Transfer/Internal/20200715 - Internal full set print/CTR - 1st Phase - Unit Layouts - Sheet - A411-B - ENLARGED PLAN 1ST - AREA B (SOUTHEAST).jpg
