OpeningDesign/CTR/Transfer/Internal/20200715 - Internal full set print/CTR - 1st Phase - Unit Layouts - Sheet - A411-D - ENLARGED PLAN 1ST - AREA D (SOUTHCENTER).jpg

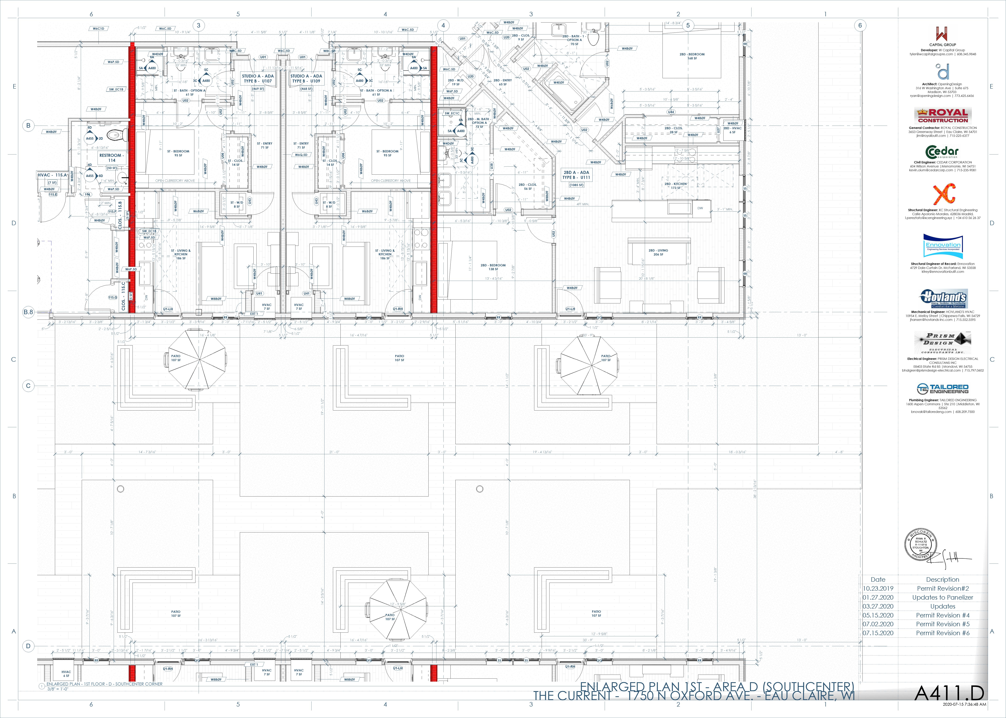
Transfer/Internal/20200715 - Internal full set print/CTR - 1st Phase - Unit Layouts - Sheet - A411-D - ENLARGED PLAN 1ST - AREA D (SOUTHCENTER).jpg
