OpeningDesign/CTR/Transfer/Internal/20200715 - Internal full set print/CTR - 1st Phase - Unit Layouts - Sheet - A412-A - ENLARGED PLAN 2ND - AREA A (NORTHEAST).jpg

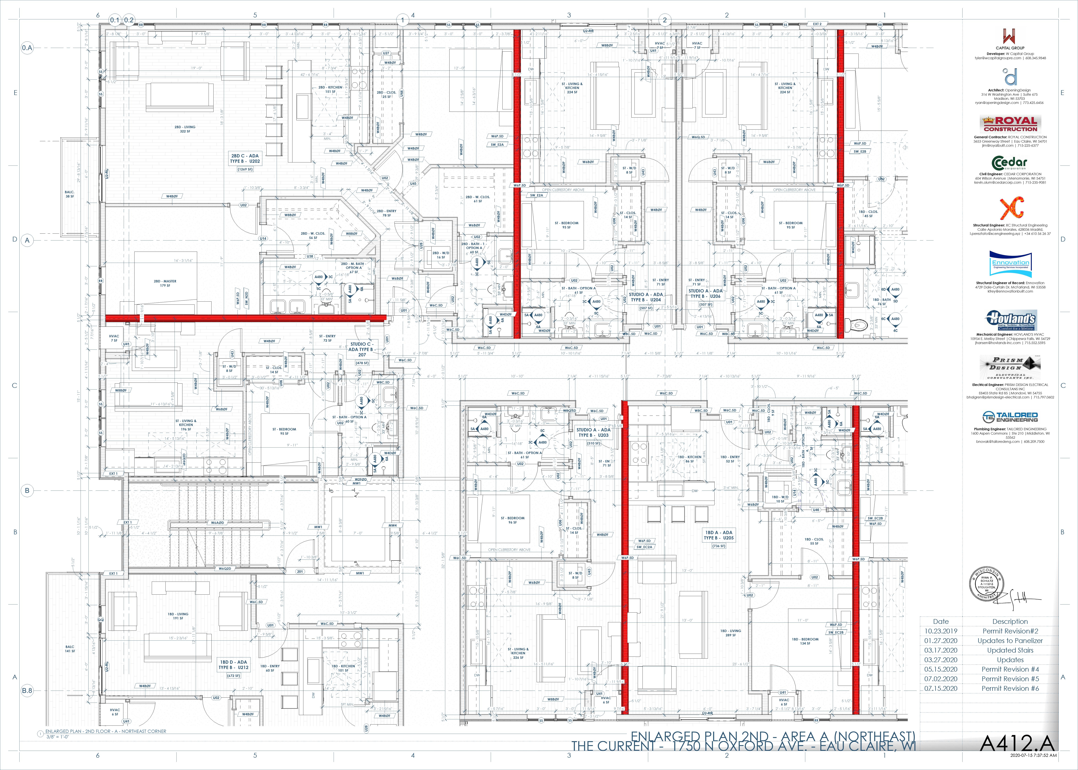
Transfer/Internal/20200715 - Internal full set print/CTR - 1st Phase - Unit Layouts - Sheet - A412-A - ENLARGED PLAN 2ND - AREA A (NORTHEAST).jpg
