OpeningDesign/CTR/Transfer/Internal/20200715 - Internal full set print/CTR - 1st Phase - Unit Layouts - Sheet - A412-C - ENLARGED PLAN 2ND - AREA C (NORTHCENTER).jpg

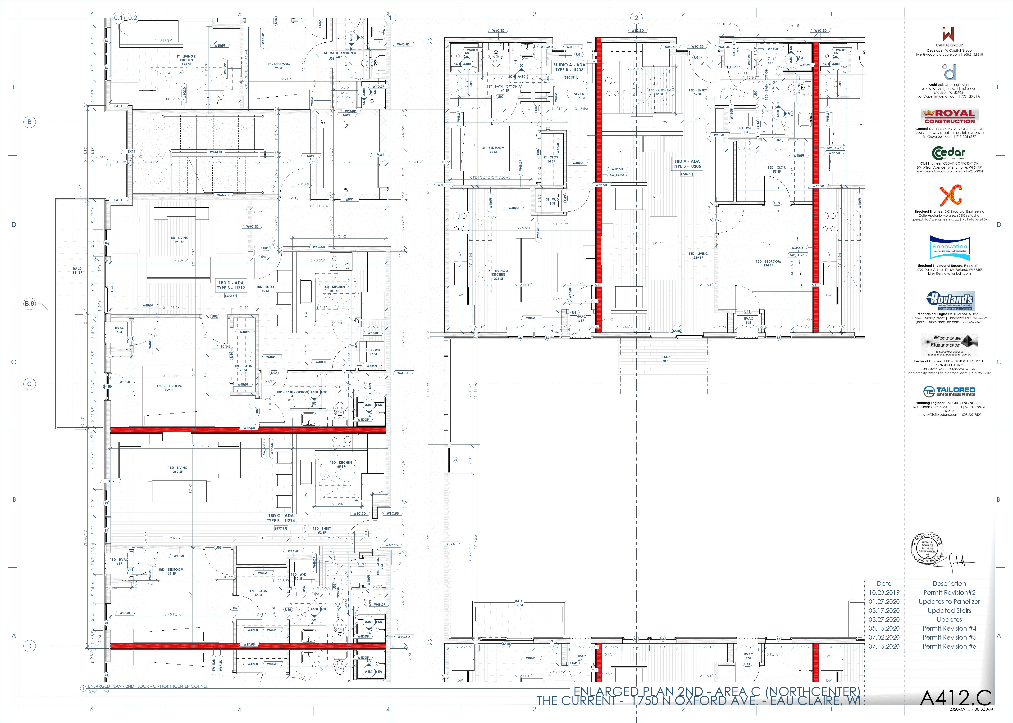
Transfer/Internal/20200715 - Internal full set print/CTR - 1st Phase - Unit Layouts - Sheet - A412-C - ENLARGED PLAN 2ND - AREA C (NORTHCENTER).jpg
