OpeningDesign/CTR/Transfer/Internal/20200715 - Internal full set print/CTR - 1st Phase - Unit Layouts - Sheet - A470 - 1ST FLOOR STUDIO UNITS.jpg

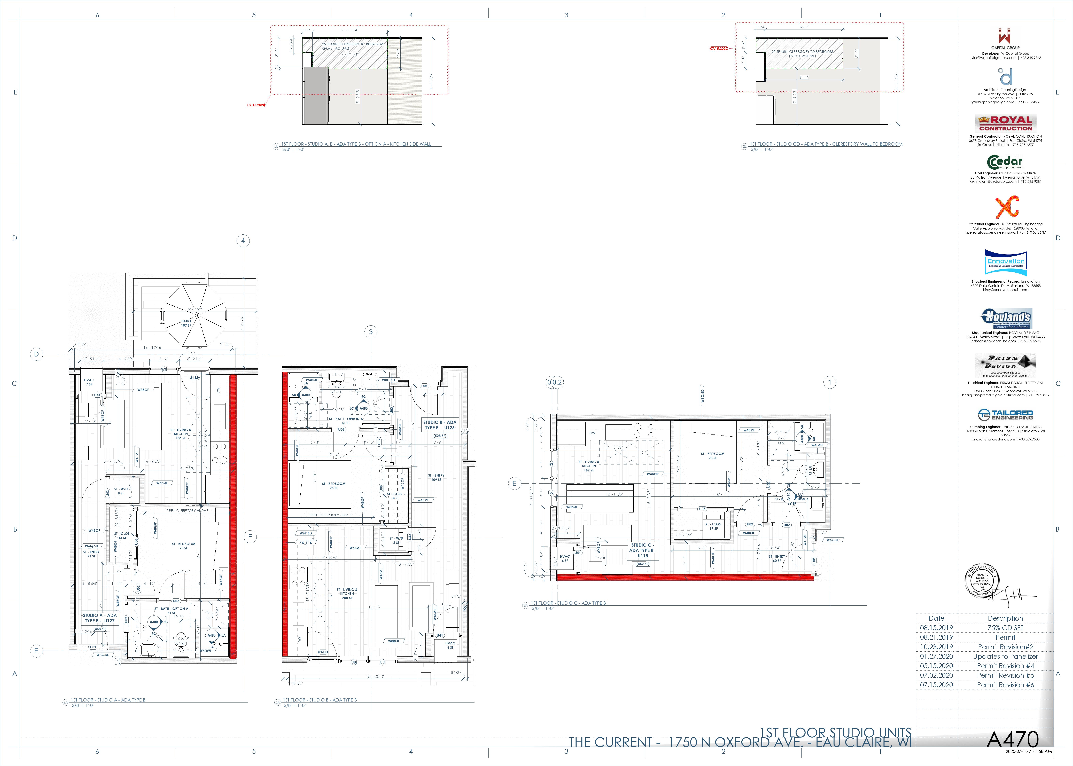
Transfer/Internal/20200715 - Internal full set print/CTR - 1st Phase - Unit Layouts - Sheet - A470 - 1ST FLOOR STUDIO UNITS.jpg
