OpeningDesign/CTR/Transfer/Internal/20200715 - Internal full set print/CTR - 1st Phase - Unit Layouts - Sheet - A475 - 2ND FLOOR STUDIO UNITS.jpg

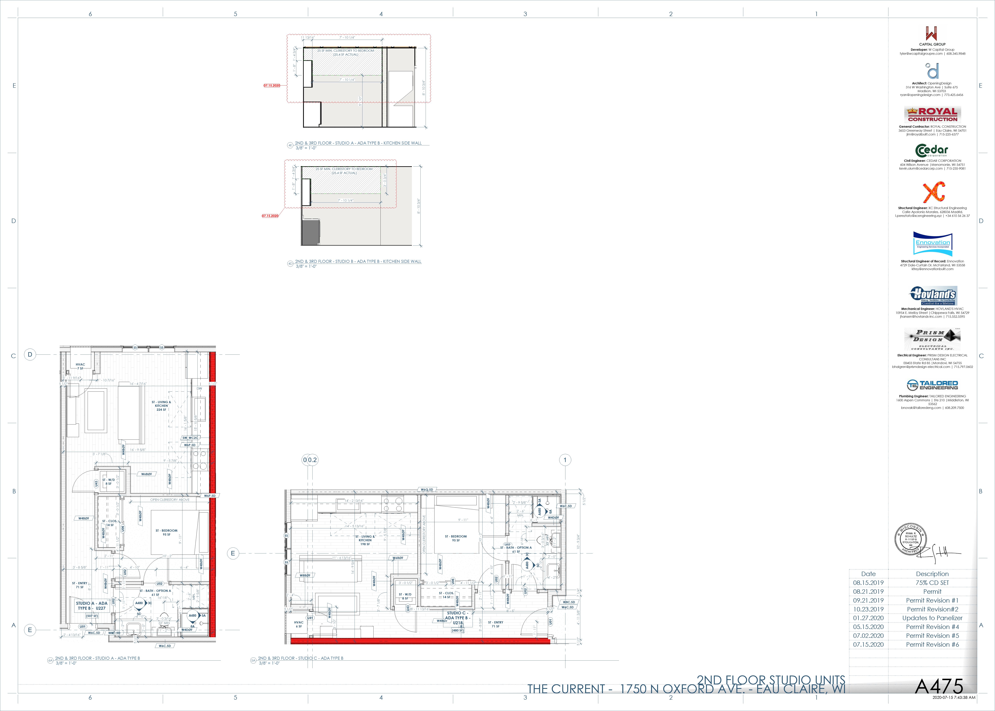
Transfer/Internal/20200715 - Internal full set print/CTR - 1st Phase - Unit Layouts - Sheet - A475 - 2ND FLOOR STUDIO UNITS.jpg
