OpeningDesign/CTR/Transfer/Internal/20200715 - Internal full set print/CTR - 1st Phase -Stairs & Elevators - Sheet - A461 - STAIRS - WEST.jpg

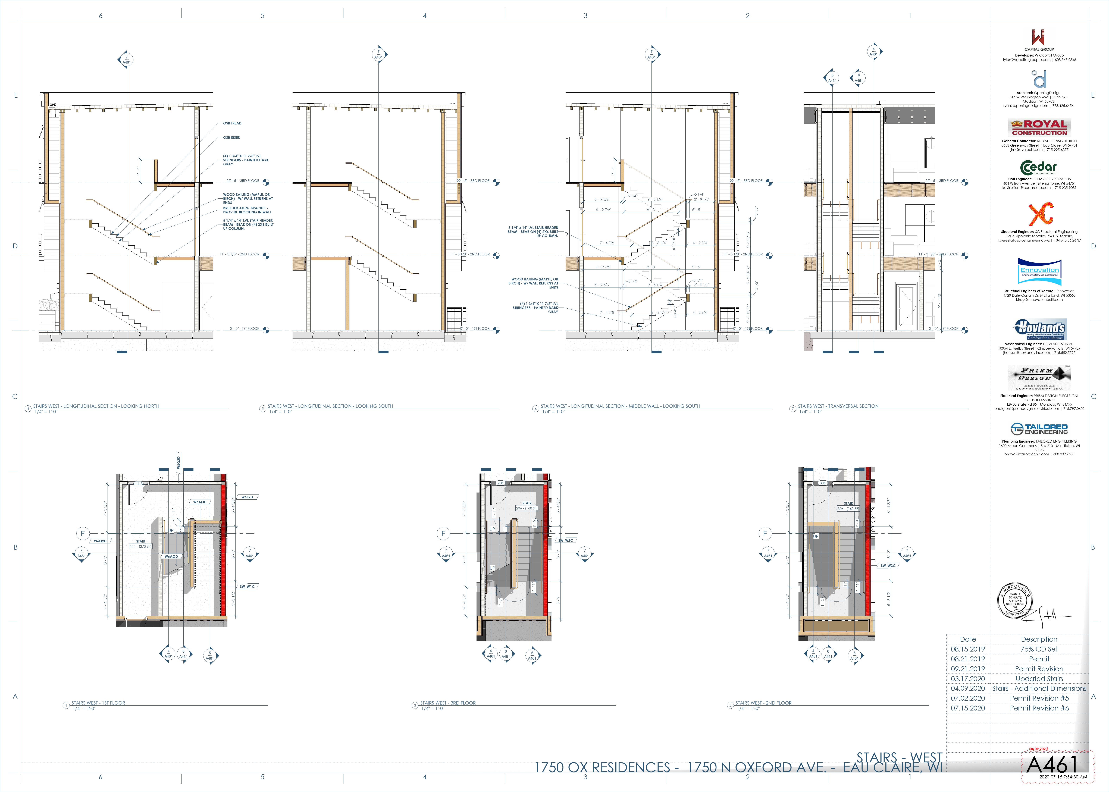
Transfer/Internal/20200715 - Internal full set print/CTR - 1st Phase -Stairs & Elevators - Sheet - A461 - STAIRS - WEST.jpg
