OpeningDesign/CTR/Transfer/Internal/20200715 - Internal full set print/CTR - 1st Phase -Stairs & Elevators - Sheet - A463 - STAIRS - ELEVATOR NORTH & SECTIONS.jpg

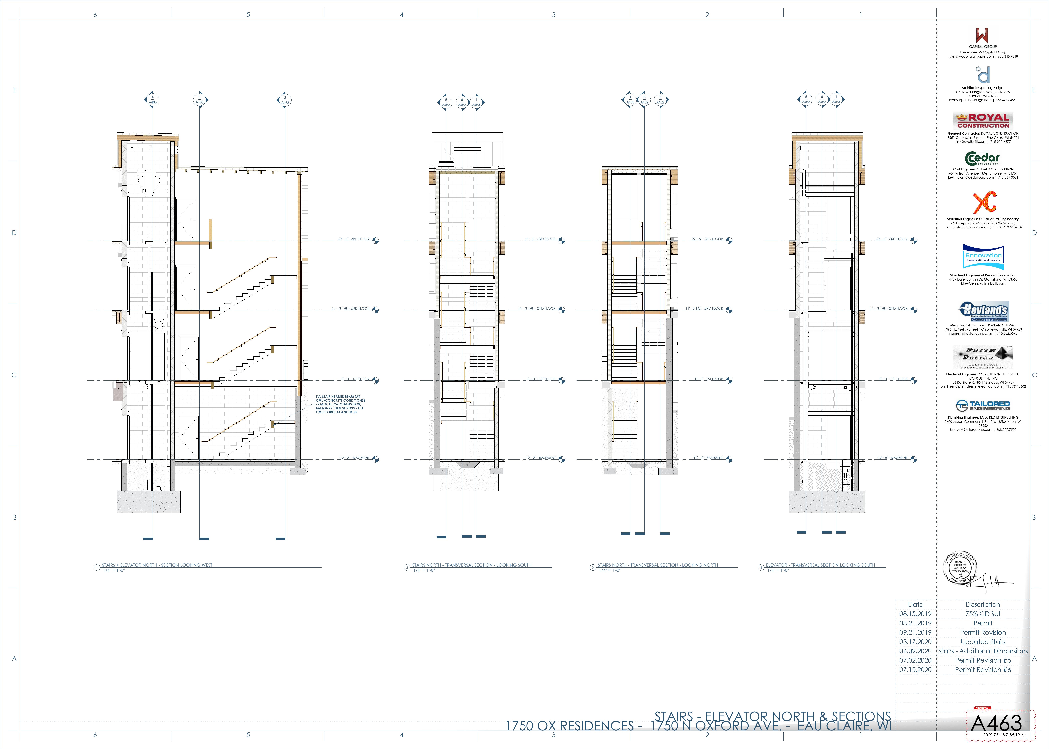
Transfer/Internal/20200715 - Internal full set print/CTR - 1st Phase -Stairs & Elevators - Sheet - A463 - STAIRS - ELEVATOR NORTH & SECTIONS.jpg
