OpeningDesign/CTR/XC_struct/xc_models/concrete_structure/basement_walls/results/RW1.tex

\begin{table}
\begin{center}
\begin{tabular}[H]{|l|}
\hline
\multicolumn{1}{|c|}{\textsc{RW1}}\\
\hline
\begin{tabular}{c|l}
\begin{minipage}{85mm}
\vspace{2mm}
\begin{center}

\end{center}
\vspace{1pt}
\end{minipage} & 
\begin{tabular}{l}
\textsc{Wall geometry}\\
Stem top thickness: \\
$b_{top}= 0.15\ m$\\
Stem height: \\
$h_{stem}= 2.28\ m$\\
Stem bottom thickness: \\
$b_{bottom}= 0.15\ m$\\
Footing thickness: \\
$b_{footing}= 0.36\ m$\\
\end{tabular} \\
\end{tabular} \\
\hline
\begin{tabular}{llll}
\multicolumn{3}{c}{\textsc{Materials}}\\
  Concrete: C4000 &   Steel: A615G60 &   Concrete cover: 55 mm\\
\end{tabular} \\
\hline
\end{tabular}
\caption{Wall materials and dimensions RW1} \label{tb_def_RW1}
\end{center}
\end{table}
\begin{center}
\begin{tabular}[H]{|l|c|c|c|}
\hline
\multicolumn{4}{|c|}{\textsc{wall: RW1 stability check}}\\
\hline
Vérification:  & $F_{disp}$ & $F_{req}$ & Combination\\
\hline
Overturning:  & 52061658217230.98 & 1.00 & EQ1615\\
Sliding:  & 110619259907919.80 & 1.00 & EQ1609B\\
Bearing capacity:  & 2.12 & 1.00 & EQ1609B\\
Adm. pressure:  & 3.07 & 1.00 & EQ1609B\\
\hline
\multicolumn{4}{|l|}{$F_{avail.}$: available security.}\\
\multicolumn{4}{|l|}{$F_{req}$: required security.}\\
\hline
\end{tabular}
\end{center}
\begin{center}
\begin{tabular}[H]{|l|c|c|c|}
\hline
\multicolumn{3}{|c|}{\textsc{Wall: RW1 rotation check}}\\
\hline
$\beta_{disp} (\permil)$ & $\beta_{req}(\permil)$ & Combination\\
\hline
0.00 & 2.00 & ELS00\\
\hline
\multicolumn{3}{|l|}{$\beta_{disp}$: wall maximum computed rotation.}\\
\multicolumn{3}{|l|}{$\beta_{req}$: wall maximum admissible rotation.}\\
\hline
\end{tabular}
\end{center}
\bottomcaption{RW1 wall reinforcement} \label{tb_RW1}
\tablefirsthead{\hline
\multicolumn{1}{|c|}{\textsc{RW1 wall reinforcement}}\\\hline
}
\tablehead{\hline
\multicolumn{1}{|c|}{\textsc{RW1 (suite)}}\\\hline
}
\tabletail{\hline \multicolumn{1}{|r|}{../..}\\\hline}
\tablelasttail{\hline}
\begin{center}
\begin{supertabular}[H]{|l|}
\hline
\textbf{Reinforcement 1 (outside reinforcement dowels) :} \\
  RC section dimensions; b= 1.00 m, h= 0.15 m\\
  diam: 16 mm, spacing: 300 mm  reinf. development L=0.34 m (22 diameters).\\
  diam: 19 mm, spacing: 300 mm  reinf. development L=0.61 m (32 diameters).\\
  area: As=  16.13 cm2/m areaMin:   2.73 cm2/m  F(As)= 5.90 OK!\\
  Bending check: Md=   0.00 kN m, MR=  46.39kN m  F(M)= 95600283742882.08 OK!\\
  Shear check: Vd=   0.00 kN,  VR= 119.62 kN  F(V)= 561569571420180.06 OK!\\
  Stress check: M=   0.00 kN m, $\sigma_s$=   0.00 MPa\\
    $\sigma_{lim}$= 230.00 MPa  F($\sigma_s$)= 104896492382790.08 OK!\\
\textbf{Reinforcement 3 (footing top reinforcement):}\\
  RC section dimensions; b= 1.00 m, h= 0.36 m\\
  diam: 16 mm, spacing: 300 mm  reinf. development L=0.34 m (22 diameters).\\
  diam: 19 mm, spacing: 300 mm  reinf. development L=0.61 m (32 diameters).\\
  area: As=  16.13 cm2/m areaMin:   6.38 cm2/m  F(As)= 2.53 OK!\\
  Bending check: Md=   0.57 kN m, MR= 152.86kN m  F(M)= 266.26 OK!\\
  Shear check: Vd=   2.97 kN,  VR= 279.12 kN  F(V)= 93.99 OK!\\
  Stress check: M=   0.57 kN m, $\sigma_s$=   1.11 MPa\\
    $\sigma_{lim}$= 230.00 MPa  F($\sigma_s$)= 206.86 OK!\\
\textbf{Reinforcement 4 (inside reinforcement dowels):}\\
  diam: 10 mm, spacing: 150 mm  reinf. development L=0.30 m (32 diameters).\\
  area: As=   4.73 cm2/m areaMin:   1.72 cm2/m  F(As)= 2.75 OK!\\
\textbf{Reinforcement 5 (inside stem reinforcement):}\\
  RC section dimensions; b= 1.00 m, h= 0.15 m\\
  diam: 16 mm, spacing: 300 mm  reinf. development L=0.34 m (22 diameters).\\
  area: As=   6.67 cm2/m areaMin:   2.73 cm2/m  F(As)= 2.44 OK!\\
  Bending check: Md=   0.00 kN m, MR=  19.36kN m  F(M)= 59369020279281.52 OK!\\
  Shear check: Vd=   0.00 kN,  VR= 119.62 kN  F(V)= 417743911060147.50 OK!\\
  Stress check: M=   0.00 kN m, $\sigma_s$=   0.00 MPa\\
    $\sigma_{lim}$= 230.00 MPa  F($\sigma_s$)= 64488482374619.54 OK!\\
\textbf{Reinforcement 6 (stem top transverse reinforcement):}\\
  RC section dimensions; b= 1.00 m, h= 0.15 m\\
  diam: 13 mm, spacing: 150 mm  reinf. development L=0.30 m (24 diameters).\\
  area: As=   8.60 cm2/m areaMin:   2.73 cm2/m  F(As)= 3.14 OK!\\
\textbf{Reinforcement 7 (footing bottom transverse reinforcement):}\\
  diam: 10 mm, spacing: 150 mm  reinf. development L=0.30 m (32 diameters).\\
  area: As=   4.73 cm2/m areaMin:   3.23 cm2/m  F(As)= 1.47 OK!\\
\textbf{Reinforcement 8 (footing bottom longitudinal reinforcement):}\\
  diam: 16 mm, spacing: 300 mm  reinf. development L=0.34 m (22 diameters).\\
  diam: 19 mm, spacing: 300 mm  reinf. development L=0.61 m (32 diameters).\\
  area: As=  16.13 cm2/m areaMin:   6.38 cm2/m  F(As)= 2.53 OK!\\
\textbf{Reinforcement 9 (footing top longitudinal reinforcement):}\\
  diam: 16 mm, spacing: 300 mm  reinf. development L=0.34 m (22 diameters).\\
  diam: 19 mm, spacing: 300 mm  reinf. development L=0.61 m (32 diameters).\\
  area: As=  16.13 cm2/m areaMin:   6.38 cm2/m  F(As)= 2.53 OK!\\
\textbf{Reinforcement 10 (footing skin reinforcement):}\\
  --\\
\textbf{Reinforcement 11 (stem outside longitudinal reinforcement):}\\
  diam: 13 mm, spacing: 150 mm  reinf. development L=0.30 m (24 diameters).\\
  area: As=   8.60 cm2/m areaMin:   2.73 cm2/m  F(As)= 3.14 OK!\\
\textbf{Reinforcement 12 (stem inside longitudinal reinforcement):}\\
  diam: 13 mm, spacing: 150 mm  reinf. development L=0.30 m (24 diameters).\\
  area: As=   8.60 cm2/m areaMin:   2.73 cm2/m  F(As)= 3.14 OK!\\
\textbf{Reinforcement 13 (stem top skin reinforcement):}\\
  --\\
\hline
\end{supertabular}
\end{center}
