OpeningDesign/CTR/XC_struct/xc_models/concrete_structure/ramp_RCwalls_foundation/results/RWpinned_east.tex

\begin{table}
\begin{center}
\begin{tabular}[H]{|l|}
\hline
\multicolumn{1}{|c|}{\textsc{RWpinned_east}}\\
\hline
\begin{tabular}{c|l}
\begin{minipage}{85mm}
\vspace{2mm}
\begin{center}

\end{center}
\vspace{1pt}
\end{minipage} & 
\begin{tabular}{l}
\textsc{Wall geometry}\\
Stem top thickness: \\
$b_{top}= 0.25\ m$\\
Stem height: \\
$h_{stem}= 3.51\ m$\\
Stem bottom thickness: \\
$b_{bottom}= 0.25\ m$\\
Footing thickness: \\
$b_{footing}= 0.36\ m$\\
\end{tabular} \\
\end{tabular} \\
\hline
\begin{tabular}{llll}
\multicolumn{3}{c}{\textsc{Materials}}\\
  Concrete: C4000 &   Steel: A615G60 &   Concrete cover: 55 mm\\
\end{tabular} \\
\hline
\end{tabular}
\caption{Wall materials and dimensions RWpinned_east} \label{tb_def_RWpinned_east}
\end{center}
\end{table}
\begin{center}
\begin{tabular}[H]{|l|c|c|c|}
\hline
\multicolumn{4}{|c|}{\textsc{wall: RWpinned_east stability check}}\\
\hline
Vérification:  & $F_{disp}$ & $F_{req}$ & Combination\\
\hline
Overturning:  & -4094.47 & 1.00 & EQ1609A\\
Sliding:  & 1.87 & 1.00 & EQ1609A\\
Bearing capacity:  & 0.58 & 1.00 & EQ1611B\\
Adm. pressure:  & 0.91 & 1.00 & EQ1611B\\
\hline
\multicolumn{4}{|l|}{$F_{avail.}$: available security.}\\
\multicolumn{4}{|l|}{$F_{req}$: required security.}\\
\hline
\end{tabular}
\end{center}
\begin{center}
\begin{tabular}[H]{|l|c|c|c|}
\hline
\multicolumn{3}{|c|}{\textsc{Wall: RWpinned_east rotation check}}\\
\hline
$\beta_{disp} (\permil)$ & $\beta_{req}(\permil)$ & Combination\\
\hline
-0.85 & 2.00 & ELS00\\
\hline
\multicolumn{3}{|l|}{$\beta_{disp}$: wall maximum computed rotation.}\\
\multicolumn{3}{|l|}{$\beta_{req}$: wall maximum admissible rotation.}\\
\hline
\end{tabular}
\end{center}
\bottomcaption{RWpinned_east wall reinforcement} \label{tb_RWpinned_east}
\tablefirsthead{\hline
\multicolumn{1}{|c|}{\textsc{Reinforcements mur RWpinned_east}}\\\hline
}
\tablehead{\hline
\multicolumn{1}{|c|}{\textsc{RWpinned_east (suite)}}\\\hline
}
\tabletail{\hline \multicolumn{1}{|r|}{../..}\\\hline}
\tablelasttail{\hline}
\begin{center}
\begin{supertabular}[H]{|l|}
\hline
\textbf{Reinforcement 1 (outside reinforcement dowels) :} \\
  RC section dimensions; b= 1.00 m, h= 0.25 m\\
  diam: 16 mm, spacing: 300 mm  reinf. development L=0.34 m (22 diameters).\\
  area: As=   6.67 cm2/m areaMin:   4.56 cm2/m  F(As)= 1.46 OK!\\
  Bending check: Md=   3.66 kN m, MR=  41.36kN m  F(M)= 11.29 OK!\\
  Shear check: Vd=  47.27 kN,  VR= 199.37 kN  F(V)= 4.22 OK!\\
  Stress check: M=   3.66 kN m, $\sigma_s$=  24.05 MPa\\
    $\sigma_{lim}$= 230.00 MPa  F($\sigma_s$)= 9.56 OK!\\
\textbf{Reinforcement 3 (footing top reinforcement):}\\
  RC section dimensions; b= 1.00 m, h= 0.36 m\\
  diam: 13 mm, spacing: 300 mm  reinf. development L=0.30 m (24 diameters).\\
  area: As=   4.30 cm2/m areaMin:   6.38 cm2/m  F(As)= 0.67 Error!\\
  Bending check: Md=   2.01 kN m, MR=  41.09kN m  F(M)= 20.46 OK!\\
  Shear check: Vd=   4.48 kN,  VR= 279.12 kN  F(V)= 62.35 OK!\\
  Stress check: M=   2.01 kN m, $\sigma_s$=  14.59 MPa\\
    $\sigma_{lim}$= 230.00 MPa  F($\sigma_s$)= 15.76 OK!\\
\textbf{Reinforcement 4 (inside reinforcement dowels):}\\
  diam: 10 mm, spacing: 300 mm  reinf. development L=0.30 m (32 diameters).\\
  area: As=   2.37 cm2/m areaMin:   0.86 cm2/m  F(As)= 2.75 OK!\\
\textbf{Reinforcement 5 (inside stem reinforcement):}\\
  RC section dimensions; b= 1.00 m, h= 0.25 m\\
  diam: 16 mm, spacing: 300 mm  reinf. development L=0.34 m (22 diameters).\\
  area: As=   6.67 cm2/m areaMin:   4.56 cm2/m  F(As)= 1.46 OK!\\
  Bending check: Md=  41.78 kN m, MR=  41.36kN m  F(M)= 0.99 $\sim$ OK!\\
  Shear check: Vd=   5.62 kN,  VR= 199.37 kN  F(V)= 35.50 OK!\\
  Stress check: M=  41.78 kN m, $\sigma_s$= 274.18 MPa\\
    $\sigma_{lim}$= 230.00 MPa  F($\sigma_s$)= 0.84 Error!\\
\textbf{Reinforcement 6 (stem top transverse reinforcement):}\\
  RC section dimensions; b= 1.00 m, h= 0.25 m\\
  diam: 13 mm, spacing: 150 mm  reinf. development L=0.30 m (24 diameters).\\
  area: As=   8.60 cm2/m areaMin:   4.56 cm2/m  F(As)= 1.89 OK!\\
\textbf{Reinforcement 7 (footing bottom transverse reinforcement):}\\
  diam: 10 mm, spacing: 150 mm  reinf. development L=0.30 m (32 diameters).\\
  area: As=   4.73 cm2/m areaMin:   1.33 cm2/m  F(As)= 3.55 OK!\\
\textbf{Reinforcement 8 (footing bottom longitudinal reinforcement):}\\
  diam: 16 mm, spacing: 300 mm  reinf. development L=0.34 m (22 diameters).\\
  area: As=   6.67 cm2/m areaMin:   6.38 cm2/m  F(As)= 1.04 OK!\\
\textbf{Reinforcement 9 (footing top longitudinal reinforcement):}\\
  diam: 16 mm, spacing: 300 mm  reinf. development L=0.34 m (22 diameters).\\
  area: As=   6.67 cm2/m areaMin:   6.38 cm2/m  F(As)= 1.04 OK!\\
\textbf{Reinforcement 10 (footing skin reinforcement):}\\
  --\\
\textbf{Reinforcement 11 (stem outside longitudinal reinforcement):}\\
  diam: 13 mm, spacing: 300 mm  reinf. development L=0.30 m (24 diameters).\\
  area: As=   4.30 cm2/m areaMin:   4.56 cm2/m  F(As)= 0.94 Error!\\
\textbf{Reinforcement 12 (stem inside longitudinal reinforcement):}\\
  diam: 13 mm, spacing: 300 mm  reinf. development L=0.30 m (24 diameters).\\
  area: As=   4.30 cm2/m areaMin:   4.56 cm2/m  F(As)= 0.94 Error!\\
\textbf{Reinforcement 13 (stem top skin reinforcement):}\\
  --\\
\hline
\end{supertabular}
\end{center}
