OpeningDesign/CTR/XC_struct/xc_models/wood_structure/stud_wall_design/facade_walls/1st_floor_AB_facade_studs_results.txt

wind load: 0.3462528  kN/m
Live load reduction factor:  0.51384907302
*****  1st floor facade stud.  ******
wall height=  2.794  m
stud height=  2.6416  m
stud spacing=  0.4064  m
sections dimensions:  38.1x139.7  mm
EQ1609 0 28697.4 
*************** comb:  EQ1609
axial load: 11.6626356499  kN 2621.86545782  lb
bending moment: 0.0  kN m 0.0  lb ft
compression stress:  2.19116623171  MPa 317.801668471  psi
unbraced lenght x: 0.3  m
unbraced lenght y: 2.6416  m
Fc'=  3.9590537362  MPa
Fb'=  5.35205745  MPa
E'=  3.0336944  GPa
stud stability factor Cp=  0.792016513131
stud capacity =  21.0723406447  kN
FcE1=  6.97432767226  MPa
FcE2=  40.2208356356  MPa
RB=  0.765291181727  m
FbE=  14.3198861538  MPa
capacity factor CF=  0.306314714605
EQ1608 0 15250 
*************** comb:  EQ1608
axial load: 6.1976  kN 1393.2762584  lb
bending moment: 0.0  kN m 0.0  lb ft
compression stress:  1.16439990456  MPa 168.881861668  psi
unbraced lenght x: 0.3  m
unbraced lenght y: 2.6416  m
Fc'=  3.9590537362  MPa
Fb'=  5.35205745  MPa
E'=  3.0336944  GPa
stud stability factor Cp=  0.792016513131
stud capacity =  21.0723406447  kN
FcE1=  6.97432767226  MPa
FcE2=  40.2208356356  MPa
RB=  0.765291181727  m
FbE=  14.3198861538  MPa
capacity factor CF=  0.0865010799137
EQ1612 207.752 15245.7 
*************** comb:  EQ1612
axial load: 6.1958614208  kN 1392.88541015  lb
bending moment: 0.181212715871  kN m 133.6556351  lb ft
compression stress:  1.16407326175  MPa 168.834486153  psi
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
Fc'=  3.9590537362  MPa
Fb'=  5.35205745  MPa
E'=  3.0336944  GPa
stud stability factor Cp=  0.792016513131
stud capacity =  21.0723406447  kN
FcE1=  6.97432767226  MPa
FcE2=  40.2208356356  MPa
RB=  0.765291181727  m
FbE=  14.3198861538  MPa
capacity factor CF=  0.0672605543102
