OpeningDesign/CTR/XC_struct/xc_models/wood_structure/stud_wall_design/facade_walls/2nd_floor_AB_facade_studs_results.txt

wind load: 0.3462528  kN/m
Live load reduction factor:  0.573147799002
*****  2nd floor facade stud.  ******
wall height=  2.794  m
stud height=  2.6416  m
stud spacing=  0.4064  m
sections dimensions:  38.1x139.7  mm
EQ1609 0 19202.1 
*************** comb:  EQ1609
axial load: 7.80372061071  kN 1754.34662677  lb
bending moment: 0.0  kN m 0.0  lb ft
compression stress:  1.4661565016  MPa 212.647938666  psi
unbraced lenght x: 0.3  m
unbraced lenght y: 2.6416  m
Fc'=  3.9590537362  MPa
Fb'=  5.35205745  MPa
E'=  3.0336944  GPa
stud stability factor Cp=  0.792016513131
stud capacity =  21.0723406447  kN
FcE1=  6.97432767226  MPa
FcE2=  40.2208356356  MPa
RB=  0.765291181727  m
FbE=  14.3198861538  MPa
capacity factor CF=  0.137144333496
EQ1608 0 9940 
*************** comb:  EQ1608
axial load: 4.039616  kN 908.142033344  lb
bending moment: 0.0  kN m 0.0  lb ft
compression stress:  0.758959675495  MPa 110.077751147  psi
unbraced lenght x: 0.3  m
unbraced lenght y: 2.6416  m
Fc'=  3.9590537362  MPa
Fb'=  5.35205745  MPa
E'=  3.0336944  GPa
stud stability factor Cp=  0.792016513131
stud capacity =  21.0723406447  kN
FcE1=  6.97432767226  MPa
FcE2=  40.2208356356  MPa
RB=  0.765291181727  m
FbE=  14.3198861538  MPa
capacity factor CF=  0.0367497687691
EQ1612 207.752 9935.72 
*************** comb:  EQ1612
axial load: 4.0378774208  kN 907.751185093  lb
bending moment: 0.181212715871  kN m 133.6556351  lb ft
compression stress:  0.758633032689  MPa 110.030375632  psi
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
Fc'=  3.9590537362  MPa
Fb'=  5.35205745  MPa
E'=  3.0336944  GPa
stud stability factor Cp=  0.792016513131
stud capacity =  21.0723406447  kN
FcE1=  6.97432767226  MPa
FcE2=  40.2208356356  MPa
RB=  0.765291181727  m
FbE=  14.3198861538  MPa
capacity factor CF=  0.0319078699187
