OpeningDesign/CTR/XC_struct/xc_models/wood_structure/stud_wall_design/facade_walls/3rd_floor_AB_facade_studs_results.txt

wind load: 0.3462528  kN/m
Live load reduction factor:  1.0
*****  3rd floor facade stud.  ******
wall height=  2.794  m
stud height=  2.6416  m
stud spacing=  0.4064  m
sections dimensions:  38.1x139.7  mm
EQ1609 0 8900 
*************** comb:  EQ1609
axial load: 3.61696  kN 813.12516064  lb
bending moment: 0.0  kN m 0.0  lb ft
compression stress:  0.679551419709  MPa 98.5605618918  psi
unbraced lenght x: 0.3  m
unbraced lenght y: 2.6416  m
Fc'=  3.9590537362  MPa
Fb'=  5.35205745  MPa
E'=  3.0336944  GPa
stud stability factor Cp=  0.792016513131
stud capacity =  21.0723406447  kN
FcE1=  6.97432767226  MPa
FcE2=  40.2208356356  MPa
RB=  0.765291181727  m
FbE=  14.3198861538  MPa
capacity factor CF=  0.0294619749098
EQ1608 0 3510 
*************** comb:  EQ1608
axial load: 1.426464  kN 320.681945376  lb
bending moment: 0.0  kN m 0.0  lb ft
compression stress:  0.268002863278  MPa 38.8705137348  psi
unbraced lenght x: 0.3  m
unbraced lenght y: 2.6416  m
Fc'=  3.9590537362  MPa
Fb'=  5.35205745  MPa
E'=  3.0336944  GPa
stud stability factor Cp=  0.792016513131
stud capacity =  21.0723406447  kN
FcE1=  6.97432767226  MPa
FcE2=  40.2208356356  MPa
RB=  0.765291181727  m
FbE=  14.3198861538  MPa
capacity factor CF=  0.00666328431628
EQ1612 207.752 3505.72 
*************** comb:  EQ1612
axial load: 1.4247254208  kN 320.291097125  lb
bending moment: 0.181212715871  kN m 133.6556351  lb ft
compression stress:  0.267676220472  MPa 38.8231382198  psi
unbraced lenght x: 0.3  m
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
Fc'=  3.9590537362  MPa
Fb'=  5.35205745  MPa
E'=  3.0336944  GPa
stud stability factor Cp=  0.792016513131
stud capacity =  21.0723406447  kN
FcE1=  6.97432767226  MPa
FcE2=  40.2208356356  MPa
RB=  0.765291181727  m
FbE=  14.3198861538  MPa
capacity factor CF=  0.0108058608923
