OpeningDesign/CTR/XC_struct/xc_models/concrete_structure/basement_walls/results/schema_T2a.tex

\begin{figure}
\begin{center}
\begin{tikzpicture}[y=0.80pt,x=0.80pt,xscale= 2.5,yscale= 2.5, inner sep=0pt, outer sep=0pt,line join=round,even odd rule,line width=1.0pt]
            \fill (176.984374221,84.3793033022) circle [radius=0.5pt];
            \fill (176.984374221,78.8647326725) circle [radius=0.5pt];
            \fill (65.4822318516,84.3793033022) circle [radius=0.5pt];
            \fill (65.4822318516,78.8647326725) circle [radius=0.5pt];
            \fill (103.992364728,91.9808524344) circle [radius=0.5pt];
            \fill (103.579827654,99.4694980504) circle [radius=0.5pt];
            \fill (103.16729058,106.958143666) circle [radius=0.5pt];
            \fill (102.754753505,114.446789282) circle [radius=0.5pt];
            \fill (102.342216431,121.935434898) circle [radius=0.5pt];
            \fill (101.929679357,129.424080515) circle [radius=0.5pt];
            \fill (101.517142282,136.912726131) circle [radius=0.5pt];
            \fill (101.104605208,144.401371747) circle [radius=0.5pt];
            \fill (100.692068134,151.890017363) circle [radius=0.5pt];
            \fill (100.279531059,159.378662979) circle [radius=0.5pt];
            \fill (99.8669939851,166.867308595) circle [radius=0.5pt];
            \fill (99.4544569108,174.355954211) circle [radius=0.5pt];
            \fill (99.0419198365,181.844599827) circle [radius=0.5pt];
            \fill (98.6293827621,189.333245443) circle [radius=0.5pt];
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
            \node[align=center] at (121.347726731,163.346595998) {\scriptsize 2};
            \node[align=center,rotate= 93.8117523216] at (115.451952958,149.951952951) {\scriptsize Armature extérieure voile};
            \node[align=center] at (178.85738297,120.072670821) {\scriptsize 3};
            \node[align=center] at (153.634598007,114.273420575) {\scriptsize Armature supérieure semelle};
            \node[align=center] at (49.577122033,121.820772683) {\scriptsize 4};
            \node[align=center,rotate= 90.0] at (43.6580181681,121.637535593) {\scriptsize Armature intérieure en attente};
            \node[align=center] at (80.8112888853,164.094505215) {\scriptsize 5};
            \node[align=center,rotate= 90.0] at (74.8921850204,143.911268125) {\scriptsize Armature intérieure voile};
            \node[align=center] at (112.752598884,240.485528924) {\scriptsize 6};
            \node[align=center] at (119.593654573,227.760174784) {\scriptsize Armature couronnement};
            \node[align=center] at (117.38239102,56.06684562) {\scriptsize 7};
            \node[align=center] at (101.089169463,49.6237488043) {\scriptsize Armature inférieure semelle};
            \node[align=center] at (156.154483435,65.4035591023) {\scriptsize 8};
            \node[align=center] at (188.160107662,65.1388289508) {\scriptsize Armature long. inférieure semelle};
            \node[align=center] at (156.154483435,93.6033013945) {\scriptsize 9};
            \node[align=center] at (188.160107662,93.338571243) {\scriptsize Armature long. supérieure semelle};
            \node[align=center] at (56.0,80.6279321629) {\scriptsize 10};
            \node[align=center] at (30.0095613646,80.3632020114) {\scriptsize Armature de peau semelle};
            \node[align=center] at (36.8195348972,77.5871634597) {\scriptsize (si nécessaire)};
            \node[align=center] at (122.036258436,191.096444933) {\scriptsize 11};
            \node[align=center] at (153.077256075,190.831714782) {\scriptsize Armature long. extérieure voile};
            \node[align=center] at (72.1400989936,191.096444933) {\scriptsize 12};
            \node[align=center] at (40.7952132241,190.831714782) {\scriptsize Armature long. intérieure voile};
            \node[align=center] at (89.5575518254,229.612529284) {\scriptsize 13};
            \node[align=center] at (57.6013089556,230.640404171) {\scriptsize Armature de peau couronnement};
            \node[align=center] at (70.4706946023,227.985466673) {\scriptsize (si nécessaire)};
            \node[align=center] at (167.5,80.6279321629) {\scriptsize 10};
            \node[align=center] at (141.455549938,80.3632020114) {\scriptsize Armature de peau semelle};
            \node[align=center] at (148.265523471,77.5871634597) {\scriptsize (si nécessaire)};
            \node[align=center,color=red] at (52.5117340804,17.0) {\scriptsize   $\phi$ 16 mm, e= 30 cm};
            \node[align=center,color=red] at (52.5117340804,13.0) {\scriptsize   $\phi$ 19 mm, e= 30 cm};
            \node[align=center,color=red] at (140,166) {\scriptsize   $\phi$ 13 mm, e= 15 cm};
            \node[align=center,color=red] at (140,162) {\scriptsize  - };
            \node[align=center,color=red] at (158,124) {\scriptsize   $\phi$ 16 mm, e= 30 cm};
            \node[align=center,color=red] at (158,120) {\scriptsize   $\phi$ 19 mm, e= 30 cm};
            \node[align=center,color=red] at (25,124) {\scriptsize   $\phi$ 10 mm, e= 15 cm};
            \node[align=center,color=red] at (25,120) {\scriptsize  - };
            \node[align=center,color=red] at (55,166) {\scriptsize   $\phi$ 10 mm, e= 15 cm};
            \node[align=center,color=red] at (55,162) {\scriptsize  - };
            \node[align=center,color=red] at (135,244) {\scriptsize   $\phi$ 13 mm, e= 15 cm};
            \node[align=center,color=red] at (135,240) {\scriptsize  - };
            \node[align=center,color=red] at (90,46) {\scriptsize   $\phi$ 10 mm, e= 15 cm};
            \node[align=center,color=red] at (90,42) {\scriptsize  - };
            \node[align=center,color=red] at (180,61) {\scriptsize   $\phi$ 16 mm, e= 30 cm};
            \node[align=center,color=red] at (180,57) {\scriptsize   $\phi$ 19 mm, e= 30 cm};
            \node[align=center,color=red] at (195,90) {\scriptsize   $\phi$ 16 mm, e= 30 cm};
            \node[align=center,color=red] at (195,86) {\scriptsize   $\phi$ 19 mm, e= 30 cm};
            \node[align=center,color=red] at (135,187) {\scriptsize   $\phi$ 13 mm, e= 15 cm};
            \node[align=center,color=red] at (135,183) {\scriptsize  - };
            \node[align=center,color=red] at (25,187) {\scriptsize   $\phi$ 13 mm, e= 15 cm};
            \node[align=center,color=red] at (25,183) {\scriptsize  - };
\end{tikzpicture}
\end{center}
\caption{Schéma armatures mur T2a} \label{fg_T2a}
\end{figure}
