OpeningDesign/CTR/XC_struct/xc_models/concrete_structure/model_precast_layout/calculations/wall_reactions.ods

Sheet: wall_reactions
North | SnowL | 562,278.31 | 55.88 | 10.06
North | LiveL | 1,211,113.43 | 55.88 | 21.67
North | Wind_NS | -845,031.22 | 55.88 | -15.12
North | Wind_WE | -74,308.88 | 55.88 | -1.33
North | DeadL | 1,762,410.24 | 55.88 | 31.54
South | SnowL | 449,192.37 | 55.88 | 16.08 | Two floors in phase 2
South | LiveL | 794,491.53 | 55.88 | 28.44 | Two floors in phase 2
South | Wind_NS | 277,907.87 | 55.88 | 9.95 | Two floors in phase 2
South | Wind_WE | -12,749.93 | 55.88 | -0.46 | Two floors in phase 2
South | DeadL | 1,149,863.27 | 55.88 | 41.15 | Two floors in phase 2
East | SnowL | 587,347.87 | 49.11 | 11.96
East | LiveL | 1,166,074.78 | 49.11 | 23.75
East | Wind_NS | -3,545.88 | 49.11 | -0.07
East | Wind_WE | 636,673.69 | 49.11 | 12.97
East | DeadL | 1,515,750.40 | 49.11 | 30.87
West | SnowL | 737,578.43 | 49.11 | 15.02
West | LiveL | 1,333,226.24 | 49.11 | 27.15
West | Wind_NS | -9,722.88 | 49.11 | -0.20
West | Wind_WE | -648,437.50 | 49.11 | -13.20
West | DeadL | 1,463,742.26 | 49.11 | 29.81

Sheet: horizontal_reactions
fy= | 413 | Mpa
fyd= | 359
 |  |  |  |  | Load combination: 1.2*D+W+L
 |  | Rh (kN) |  | Rh (kN/m) | Rh (kN/m) | As (cm2/m)
North | SnowL | -1006.41914635684 | 55.88 | -0.02
North | LiveL | -3178.37896286642 | 55.88 | -0.06
North | Wind_NS | -217047.155200329 | 55.88 | -3.88 | 4.03624978698807 | 0.112430356183512
North | Wind_WE | 2848.79290006983 | 55.88 | 0.05
North | DeadL | -4433.41994474867 | 55.88 | -0.08
South | SnowL | 380.305895776978 | 55.88 | 0.01
South | LiveL | 2075.20401620256 | 55.88 | 0.04
South | Wind_NS | -322181.218246315 | 55.88 | -5.77 | 5.81453204248152 | 0.161964680849067
South | Wind_WE | -458.210563764067 | 55.88 | -0.01
South | DeadL | 549.690226124597 | 55.88 | 0.01
East | SnowL | -8056.24976714436 | 49.11 | -0.16
East | LiveL | -25990.393371659 | 49.11 | -0.53
East | Wind_NS | -4373.10106130095 | 49.11 | -0.09 | 6.94570610987747 | 0.19347370779603
East | Wind_WE | -267438.692061414 | 49.11 | -5.45
East | DeadL | -39705.632332142 | 49.11 | -0.81
