OpeningDesign/CTR/XC_struct/xc_models/concrete_structure/model_precast_layout/calculations/wall_reactions_nodes.ods

Sheet: wall_North_reactions
6089 | DeadL | 12,419.02
17283 | DeadL | 13,397.26
3 | DeadL | 0.00
10043 | DeadL | 13,516.78
4 | DeadL | 0.00
6085 | DeadL | 12,465.76
14424 | DeadL | 11,844.68
14133 | DeadL | 14,108.71
5 | DeadL | 0.00
23030 | DeadL | 4,998.20
8875 | DeadL | 12,836.93
6083 | DeadL | 14,053.07
17287 | DeadL | 14,161.44
14 | DeadL | 0.00
6095 | DeadL | 12,105.02
6094 | DeadL | 12,221.59
6 | DeadL | 0.00
8890 | DeadL | 14,789.79
0 | DeadL | 22,579.69
14135 | DeadL | 13,595.95
17292 | DeadL | 16,761.58
571 | DeadL | 0.00
8873 | DeadL | 7,670.55
6090 | DeadL | 12,463.74
8876 | DeadL | 13,294.89
1 | DeadL | 0.00
8884 | DeadL | 14,596.13
8877 | DeadL | 13,498.48
8878 | DeadL | 13,767.59
8891 | DeadL | 14,765.74
14426 | DeadL | 11,531.12
15 | DeadL | 0.00
8879 | DeadL | 13,950.70
8880 | DeadL | 14,127.24
13993 | DeadL | 12,962.41
8903 | DeadL | 12,839.83
8881 | DeadL | 14,271.85
23028 | DeadL | 8,232.97
8882 | DeadL | 14,399.06
17285 | DeadL | 13,376.43
570 | DeadL | 0.00
17 | DeadL | 0.00
14128 | DeadL | 16,741.97
569 | DeadL | 0.00
13 | DeadL | 0.00
14136 | DeadL | 13,362.17
6087 | DeadL | 12,216.99
17290 | DeadL | 15,497.43
6092 | DeadL | 12,421.48
568 | DeadL | 0.00
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
