OpeningDesign/CTR/XC_struct/xc_models/concrete_structure/basement_walls/results/T5.jpeg

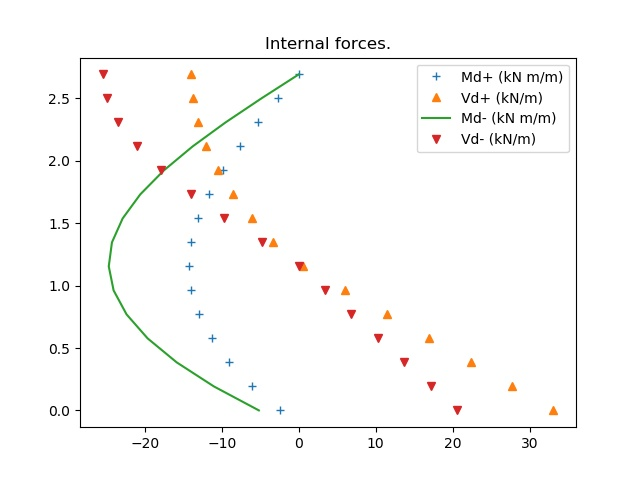
XC_struct/xc_models/concrete_structure/basement_walls/results/T5.jpeg
