OpeningDesign/CTR/XC_struct/xc_models/concrete_structure/ramp_RCwalls_foundation/results/RWpinned_west.jpeg

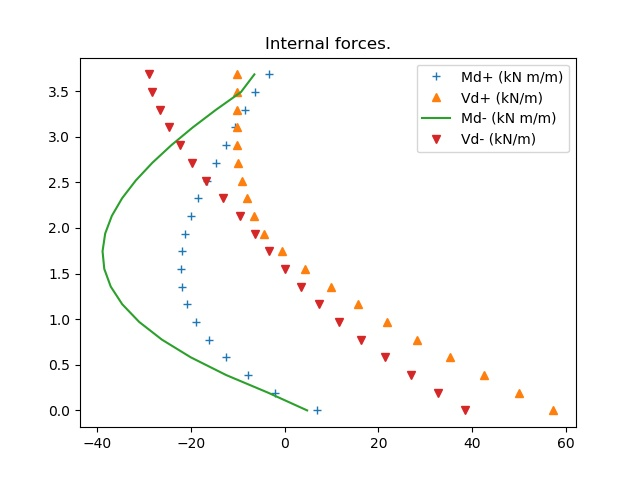
XC_struct/xc_models/concrete_structure/ramp_RCwalls_foundation/results/RWpinned_west.jpeg
