OpeningDesign/CTR/Transfer/20200618 - to State - PERMIT REVISIONS 5/A462 - STAIRS - ELEVATOR NORTH.pdf

1

B

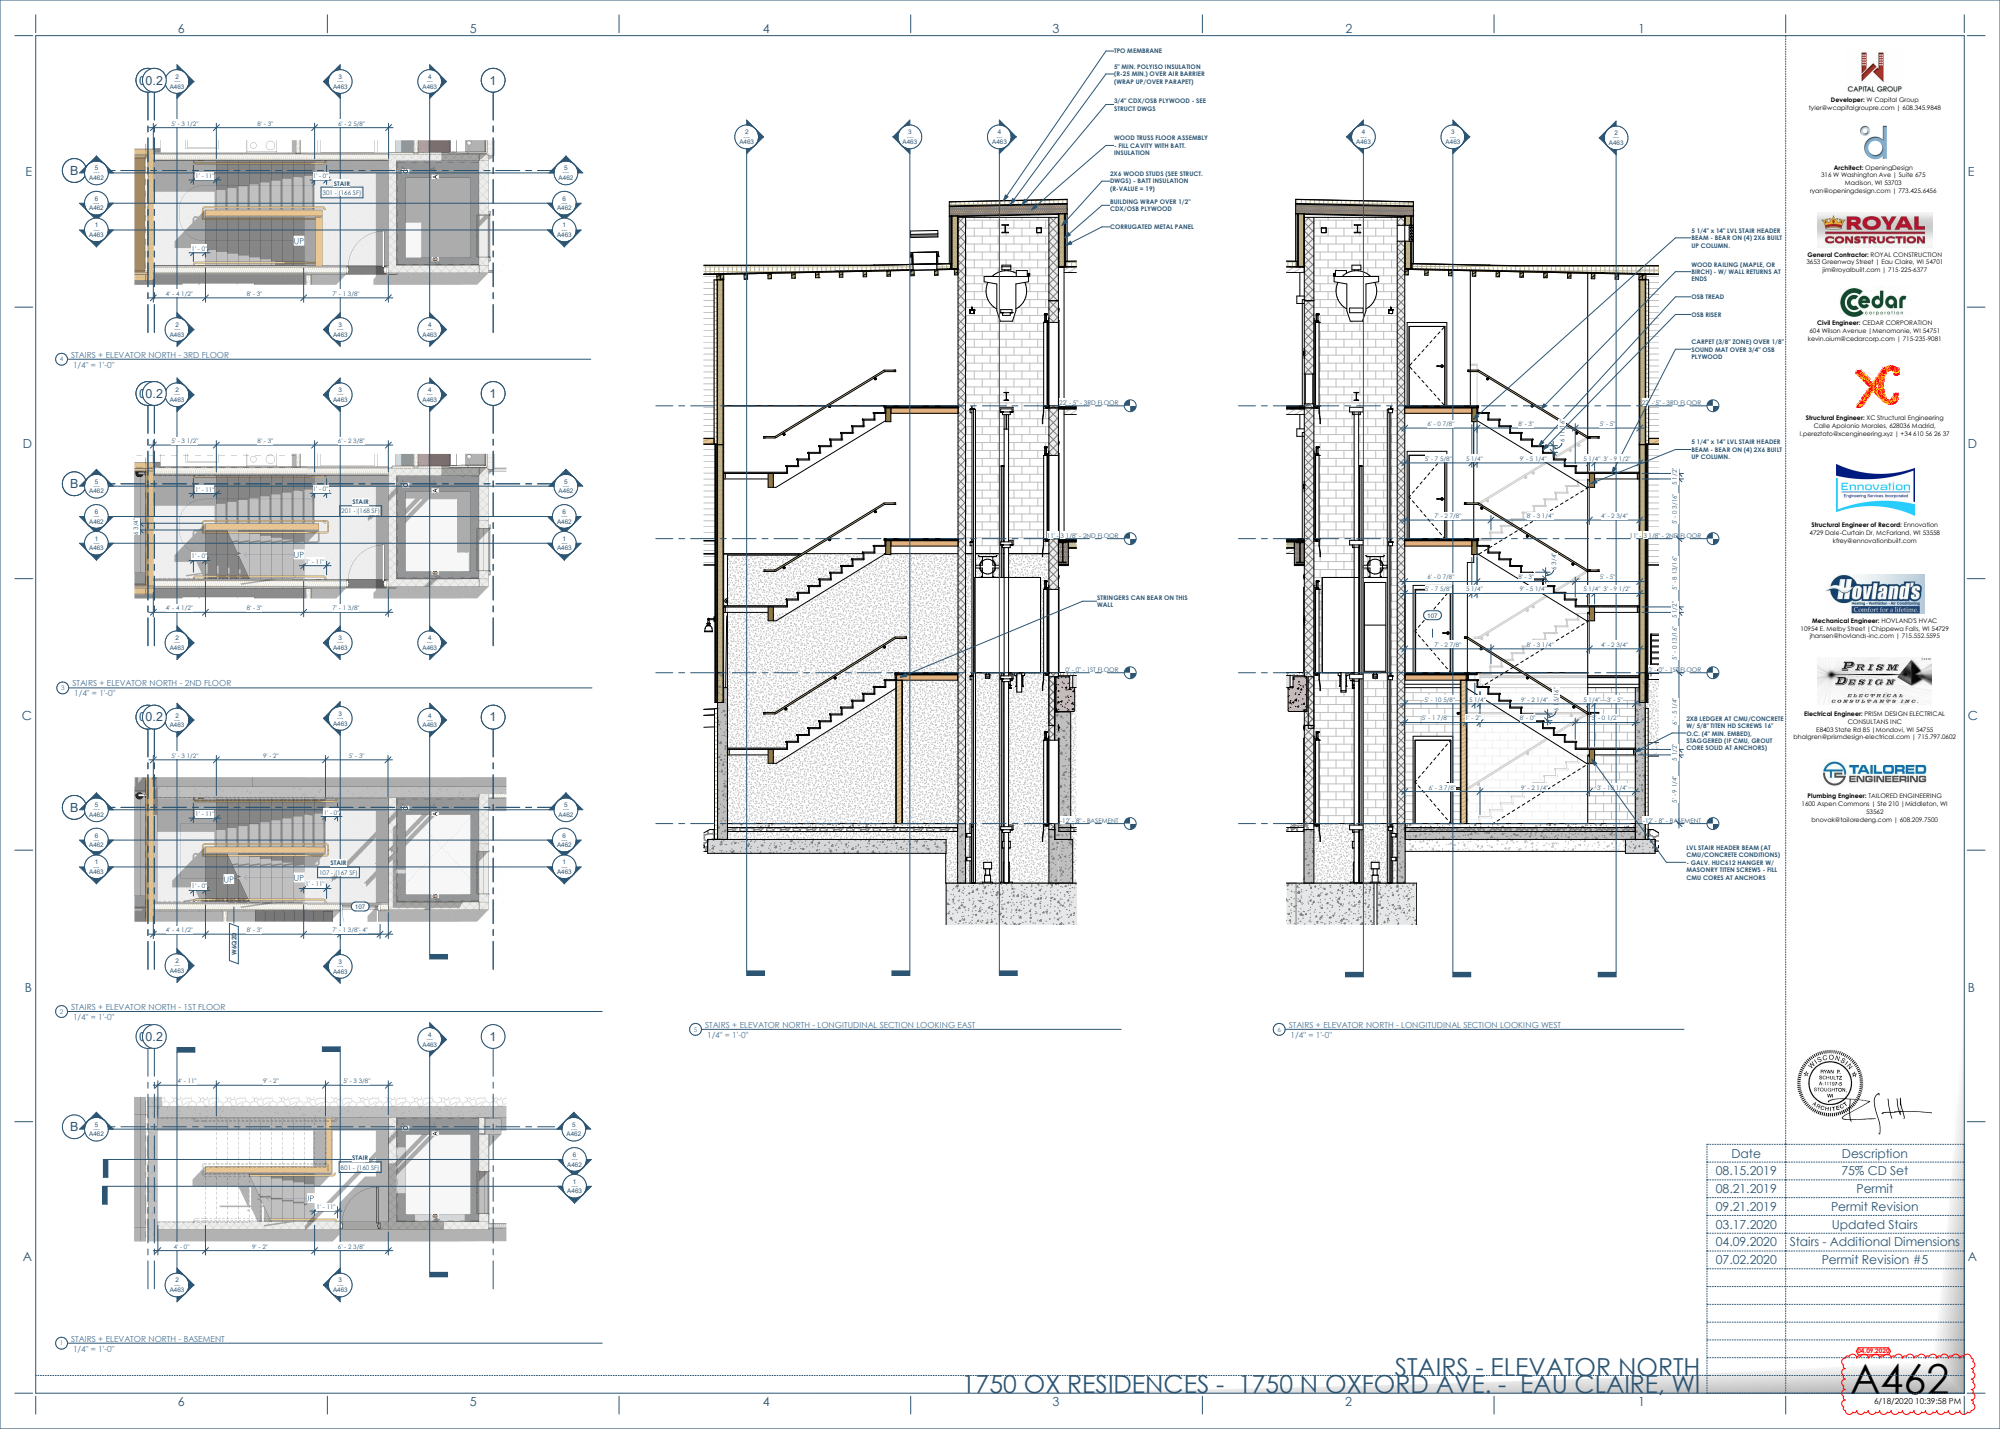
[picture p443: page 1]
STAIR; 0' - 0" - 1ST FLOOR; 11' - 3 1/8" - 2ND FLOOR; -12' - 8" - BASEMENT; 22' - 5" - 3RD FLOOR; TPO MEMBRANE; OSB TREAD; OSB RISER; Madison, WI 53703; CONSULTANS INC; Date; Description

5" MIN. POLYISO INSULATION
(R-25 MIN.) OVER AIR BARRIER
(WRAP UP/OVER PARAPET)

Developer: W Capital Group

3/4" CDX/OSB PLYWOOD - SEE
STRUCT DWGS

tyler@wcapitalgroupre.com | 608.345.9848

WOOD TRUSS FLOOR ASSEMBLY
- FILL CAVITY WITH BATT.
INSULATION

Architect: OpeningDesign
316 W Washington Ave | Suite 675

2X6 WOOD STUDS (SEE STRUCT.
DWGS) - BATT INSULATION
(R-VALUE = 19)

ryan@openingdesign.com | 773.425.6456

BUILDING WRAP OVER 1/2"
CDX/OSB PLYWOOD

CORRUGATED METAL PANEL

5 1/4" x 14" LVL STAIR HEADER
BEAM - BEAR ON (4) 2X6 BUILT
UP COLUMN.

General Contractor: ROYAL CONSTRUCTION
3653 Greenway Street | Eau Claire, WI 54701
jim@royalbuilt.com | 715-225-6377

WOOD RAILING (MAPLE, OR
BIRCH) - W/ WALL RETURNS AT
ENDS

Civil Engineer: CEDAR CORPORATION
604 Wilson Avenue |Menomonie, WI 54751
kevin.oium@cedarcorp.com | 715-235-9081

CARPET (3/8" ZONE) OVER 1/8"
SOUND MAT OVER 3/4" OSB
PLYWOOD

STAIRS + ELEVATOR NORTH - 3RD FLOOR

Structural Engineer: XC Structural Engineering
Calle Apolonio Morales, 628036 Madrid,
l.pereztato@xcengineering.xyz | +34 610 56 26 37

Structural Engineer of Record: Ennovation
4729 Dale-Curtain Dr, McFarland, WI 53558

kfrey@ennovationbuilt.com

STRINGERS CAN BEAR ON THIS
WALL

Mechanical Engineer: HOVLAND'S HVAC
10954 E. Melby Street |Chippewa Falls, WI 54729
jhansen@hovlands-inc.com | 715.552.5595

STAIRS + ELEVATOR NORTH - 2ND FLOOR

Electrical Engineer: PRISM DESIGN ELECTRICAL

2X8 LEDGER AT CMU/CONCRETE
W/ 5/8" TITEN HD SCREWS 16"
O.C. (4" MIN. EMBED),
STAGGERED (IF CMU, GROUT
CORE SOLID AT ANCHORS)

E8403 State Rd 85 |Mondovi, WI 54755

bhalgren@prismdesign-electrical.com | 715.797.0602

Plumbing Engineer: TAILORED ENGINEERING
1600 Aspen Commons | Ste 210 |Middleton, WI

bnovak@tailoredeng.com | 608.209.7500

LVL STAIR HEADER BEAM (AT
CMU/CONCRETE CONDITIONS)
- GALV. HUC612 HANGER W/
MASONRY TITEN SCREWS - FILL
CMU CORES AT ANCHORS

STAIRS + ELEVATOR NORTH - 1ST FLOOR

STAIRS + ELEVATOR NORTH - LONGITUDINAL SECTION LOOKING EAST

STAIRS + ELEVATOR NORTH - LONGITUDINAL SECTION LOOKING WEST

08.15.2019 75% CD Set
08.21.2019 Permit
09.21.2019 Permit Revision
03.17.2020 Updated Stairs
04.09.2020 Stairs - Additional Dimensions
07.02.2020 Permit Revision #5

STAIRS + ELEVATOR NORTH - BASEMENT

STAIRS - ELEVATOR NORTH

1750 OX RESIDENCES - 1750 N OXFORD AVE. - EAU CLAIRE, WI
