OpeningDesign/CTR/Transfer/20200717 - from STRUCT - suggested fix for hacked stud/studs_reinforcement.png

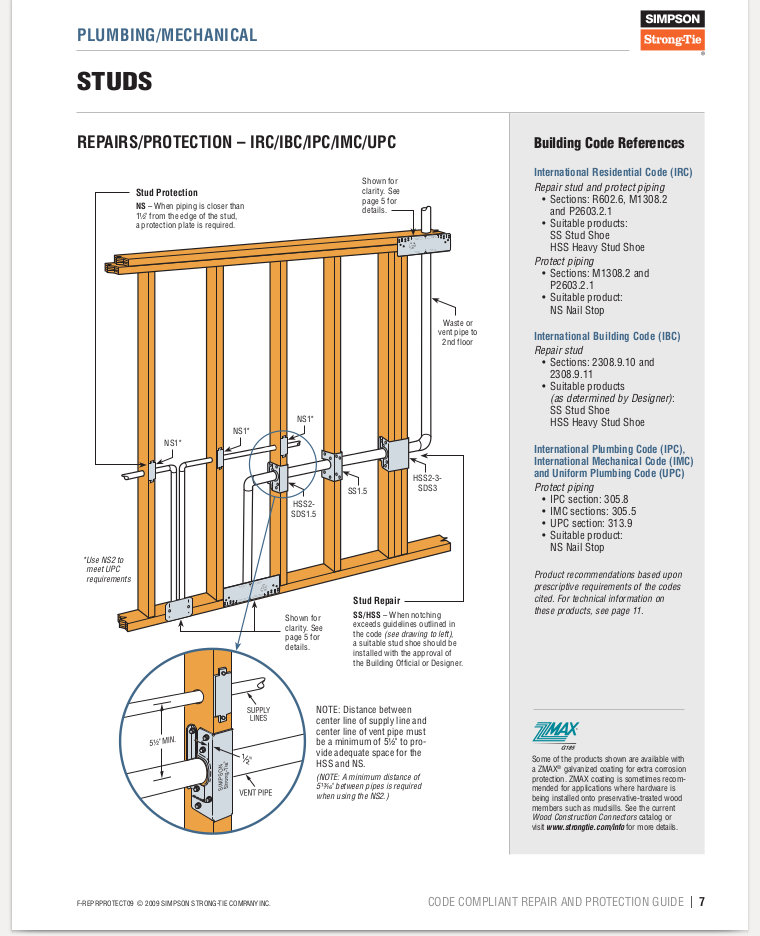
Transfer/20200717 - from STRUCT - suggested fix for hacked stud/studs_reinforcement.png
