OpeningDesign/CTR/Transfer/20200717 - from STRUCT - suggested fix for hacked stud/top_and_bottom_plates_repair.png

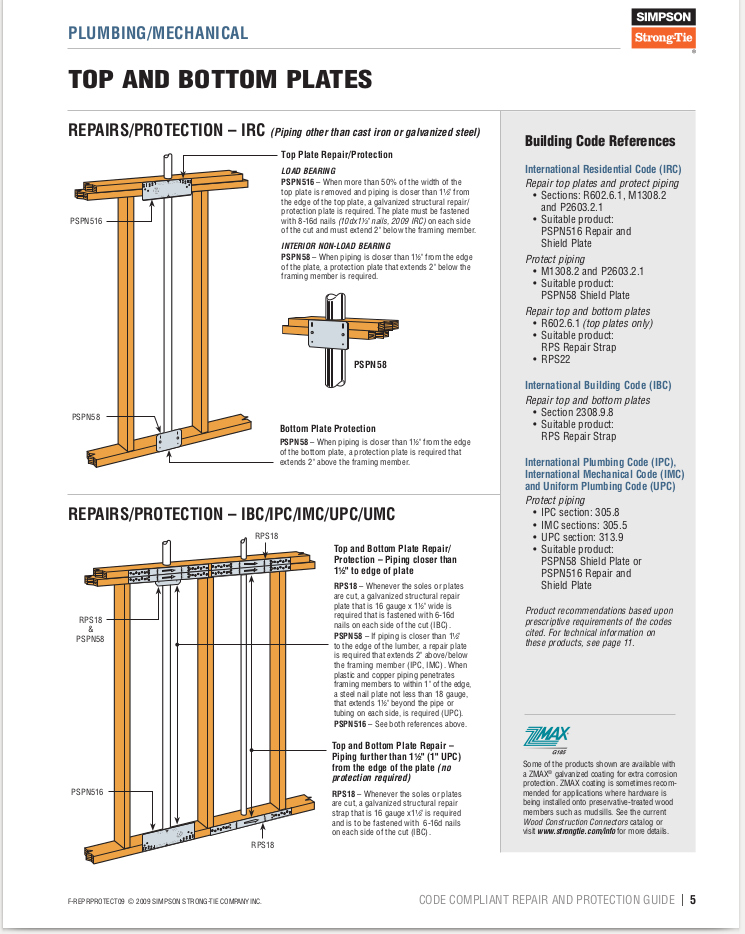
Transfer/20200717 - from STRUCT - suggested fix for hacked stud/top_and_bottom_plates_repair.png
