OpeningDesign/CTR/XC_struct/xc_models/concrete_structure/ramp_RCwalls_foundation/details/1st_floor/the_problem_to_solve.tif

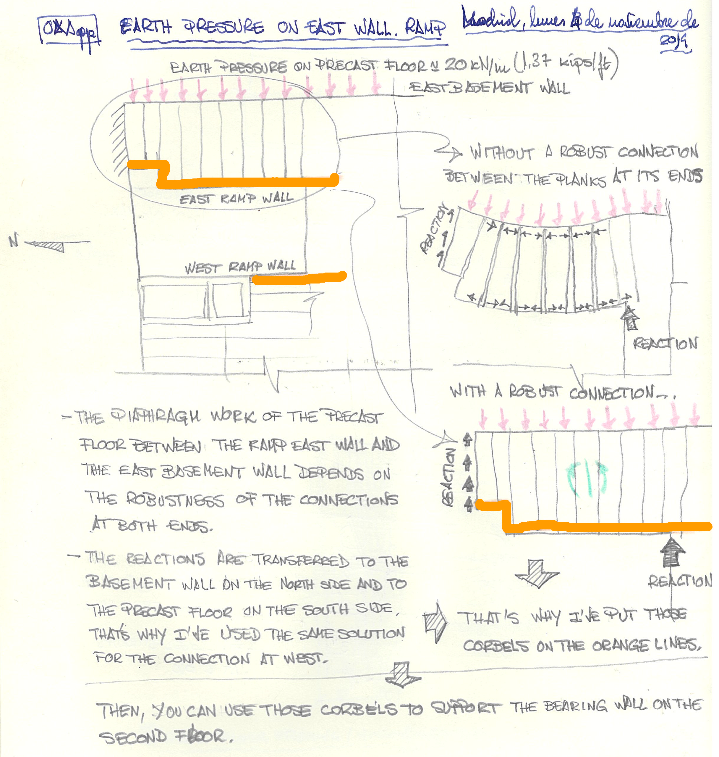
XC_struct/xc_models/concrete_structure/ramp_RCwalls_foundation/details/1st_floor/the_problem_to_solve.tif
