OpeningDesign/CTR/Transfer/20200804 - to GC - approved plans and signed cover sheet/A200 - ELEVATIONS - BUILDING.pdf

5 | 4 | 3 | 2 | 1
6 | 0.20.1

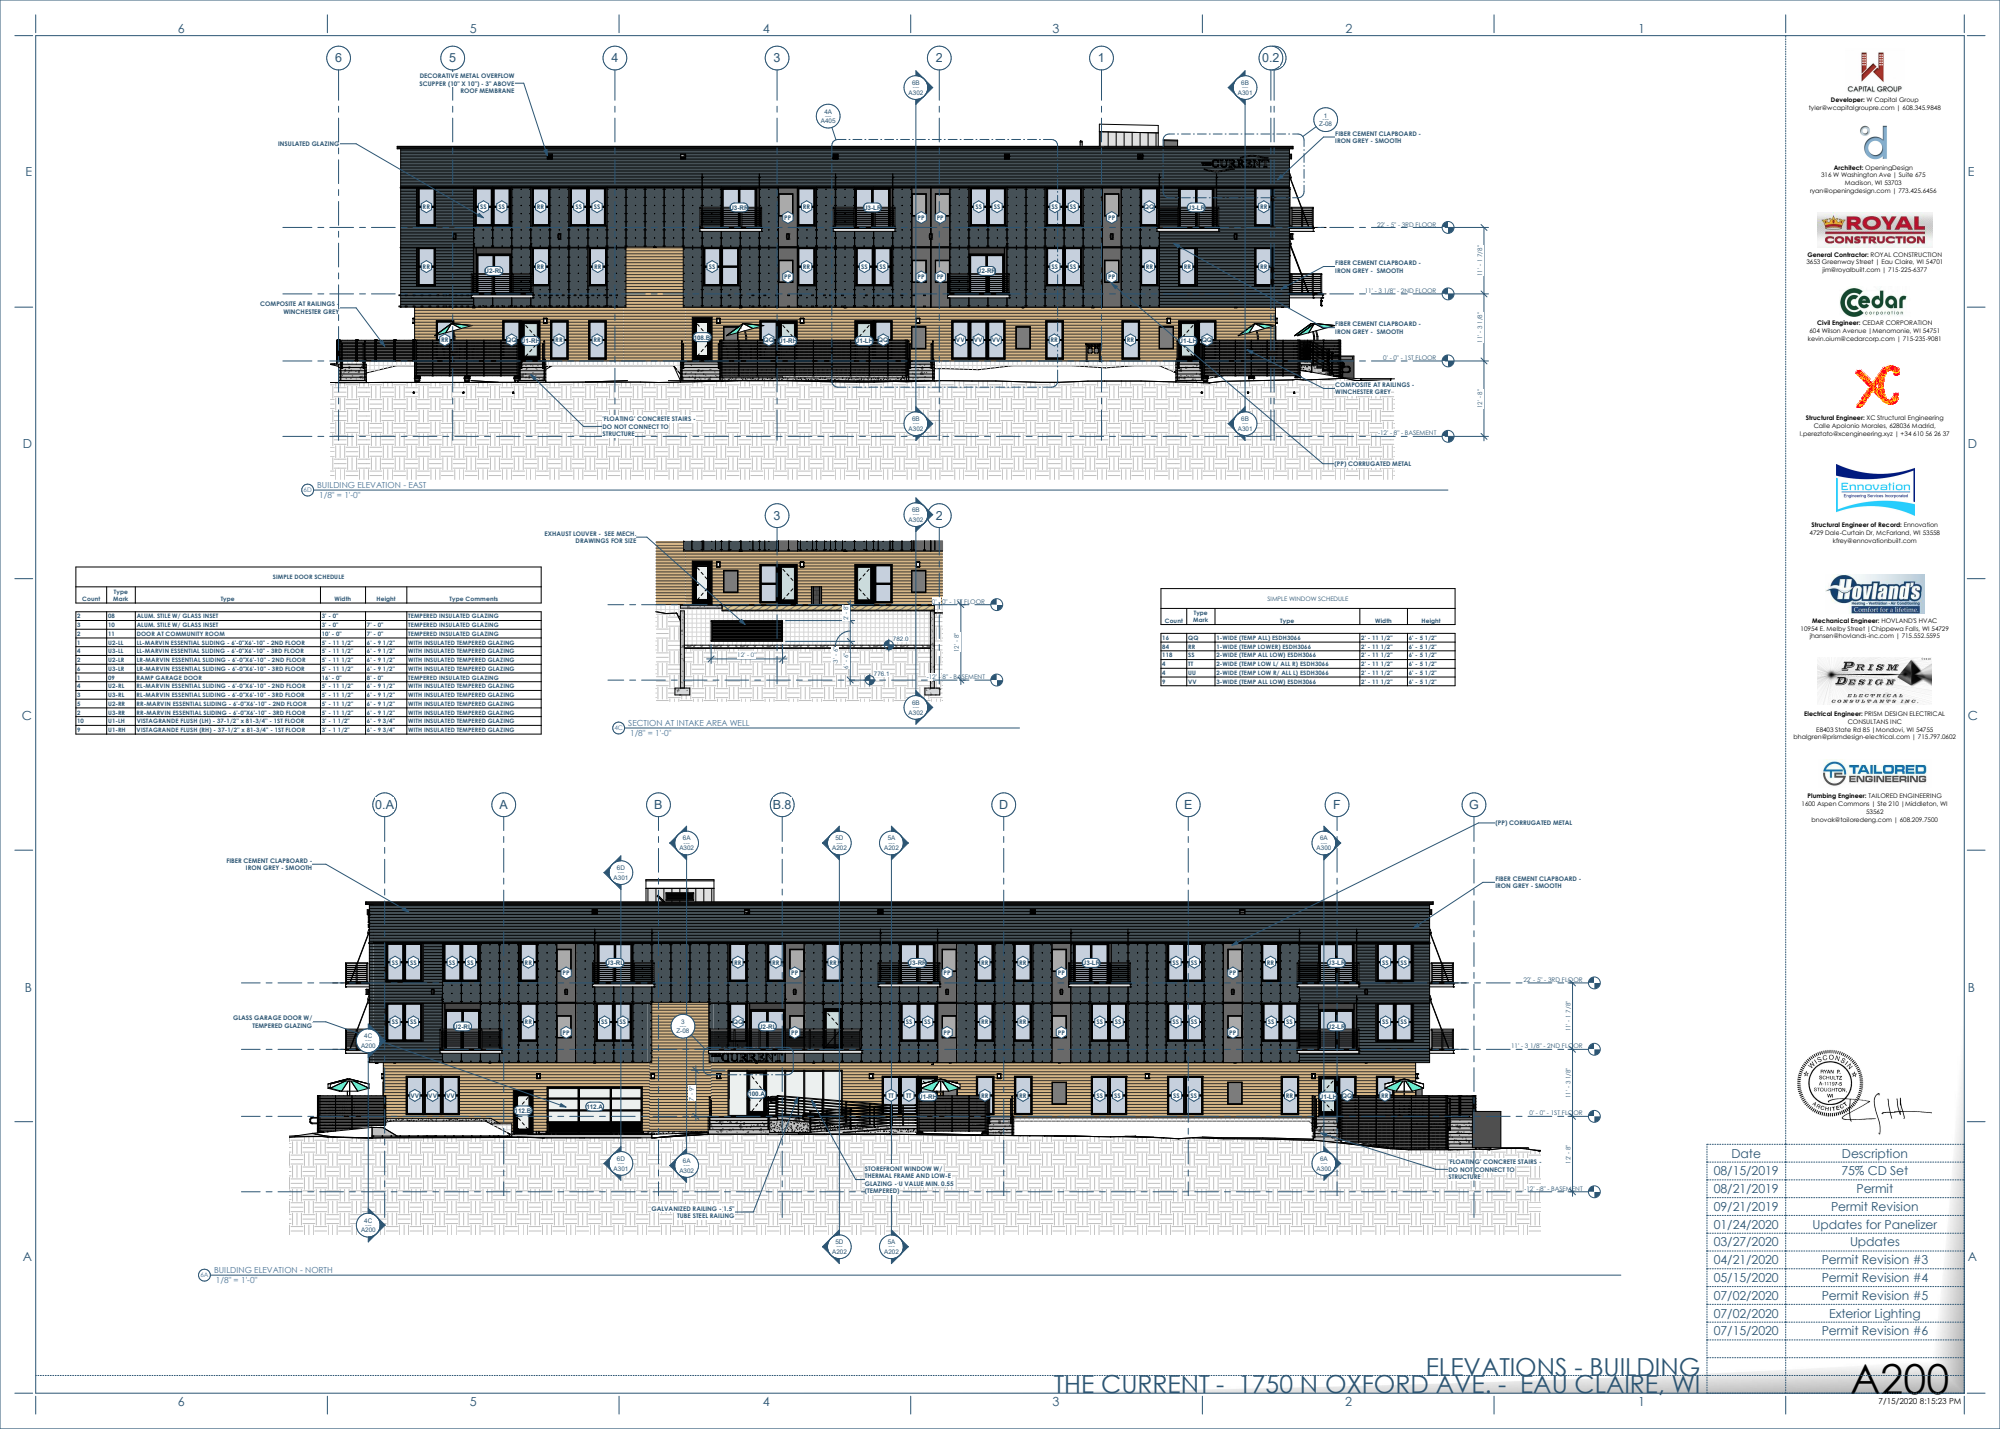
[picture p447: page 1]
0' - 0" - 1ST FLOOR; 11' - 3 1/8" - 2ND FLOOR; -12' - 8" - BASEMENT; 22' - 5" - 3RD FLOOR; FIBER CEMENT CLAPBOARD - IRON GREY - SMOOTH; ROOF MEMBRANE; INSULATED GLAZING; WINCHESTER GREY; TEMPERED GLAZING; GALVANIZED RAILING - 1.5"; Madison, WI 53703; CONSULTANS INC; ELEVATIONS - BUILDING; Date; Description; 75% CD Set; Permit; Permit Revision; Updates for Panelizer; Updates; Permit Revision #3; Permit Revision #4; Permit Revision #5; Exterior Lighting; Permit Revision #6; Count; Type; Mark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

DECORATIVE METAL OVERFLOW
SCUPPER (10" X 10") - 3" ABOVE

Developer: W Capital Group

tyler@wcapitalgroupre.com | 608.345.9848

Architect: OpeningDesign
316 W Washington Ave | Suite 675

ryan@openingdesign.com | 773.425.6456

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

FIBER CEMENT CLAPBOARD -
IRON GREY - SMOOTH

COMPOSITE AT RAILINGS -

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

WINCHESTER GREY

'FLOATING' CONCRETE STAIRS -
DO NOT CONNECT TO
STRUCTURE

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

(PP) CORRUGATED METAL

1/8" = 1'-0" ⁶D BUILDING ELEVATION - EAST

Structural Engineer of Record: Ennovation
4729 Dale-Curtain Dr, McFarland, WI 53558

EXHAUST LOUVER - SEE MECH.

DRAWINGS FOR SIZE

kfrey@ennovationbuilt.com

SIMPLE DOOR SCHEDULE

SIMPLE WINDOW SCHEDULE

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

Electrical Engineer: PRISM DESIGN ELECTRICAL

1/8" = 1'-0" ⁴C SECTION AT INTAKE AREA WELL

E8403 State Rd 85 |Mondovi, WI 54755

bhalgren@prismdesign-electrical.com | 715.797.0602

Plumbing Engineer: TAILORED ENGINEERING
1600 Aspen Commons | Ste 210 |Middleton, WI

bnovak@tailoredeng.com | 608.209.7500

GLASS GARAGE DOOR W/

STOREFRONT WINDOW W/
THERMAL FRAME AND LOW-E
GLAZING - U VALUE MIN. 0.55
(TEMPERED)

TUBE STEEL RAILING

1/8" = 1'-0" ⁶A BUILDING ELEVATION - NORTH

THE CURRENT - 1750 N OXFORD AVE. - EAU CLAIRE, WI
