OpeningDesign/CTR/Transfer/20200618 - to State - PERMIT REVISIONS 5/A461 - STAIRS - WEST.pdf

E
E

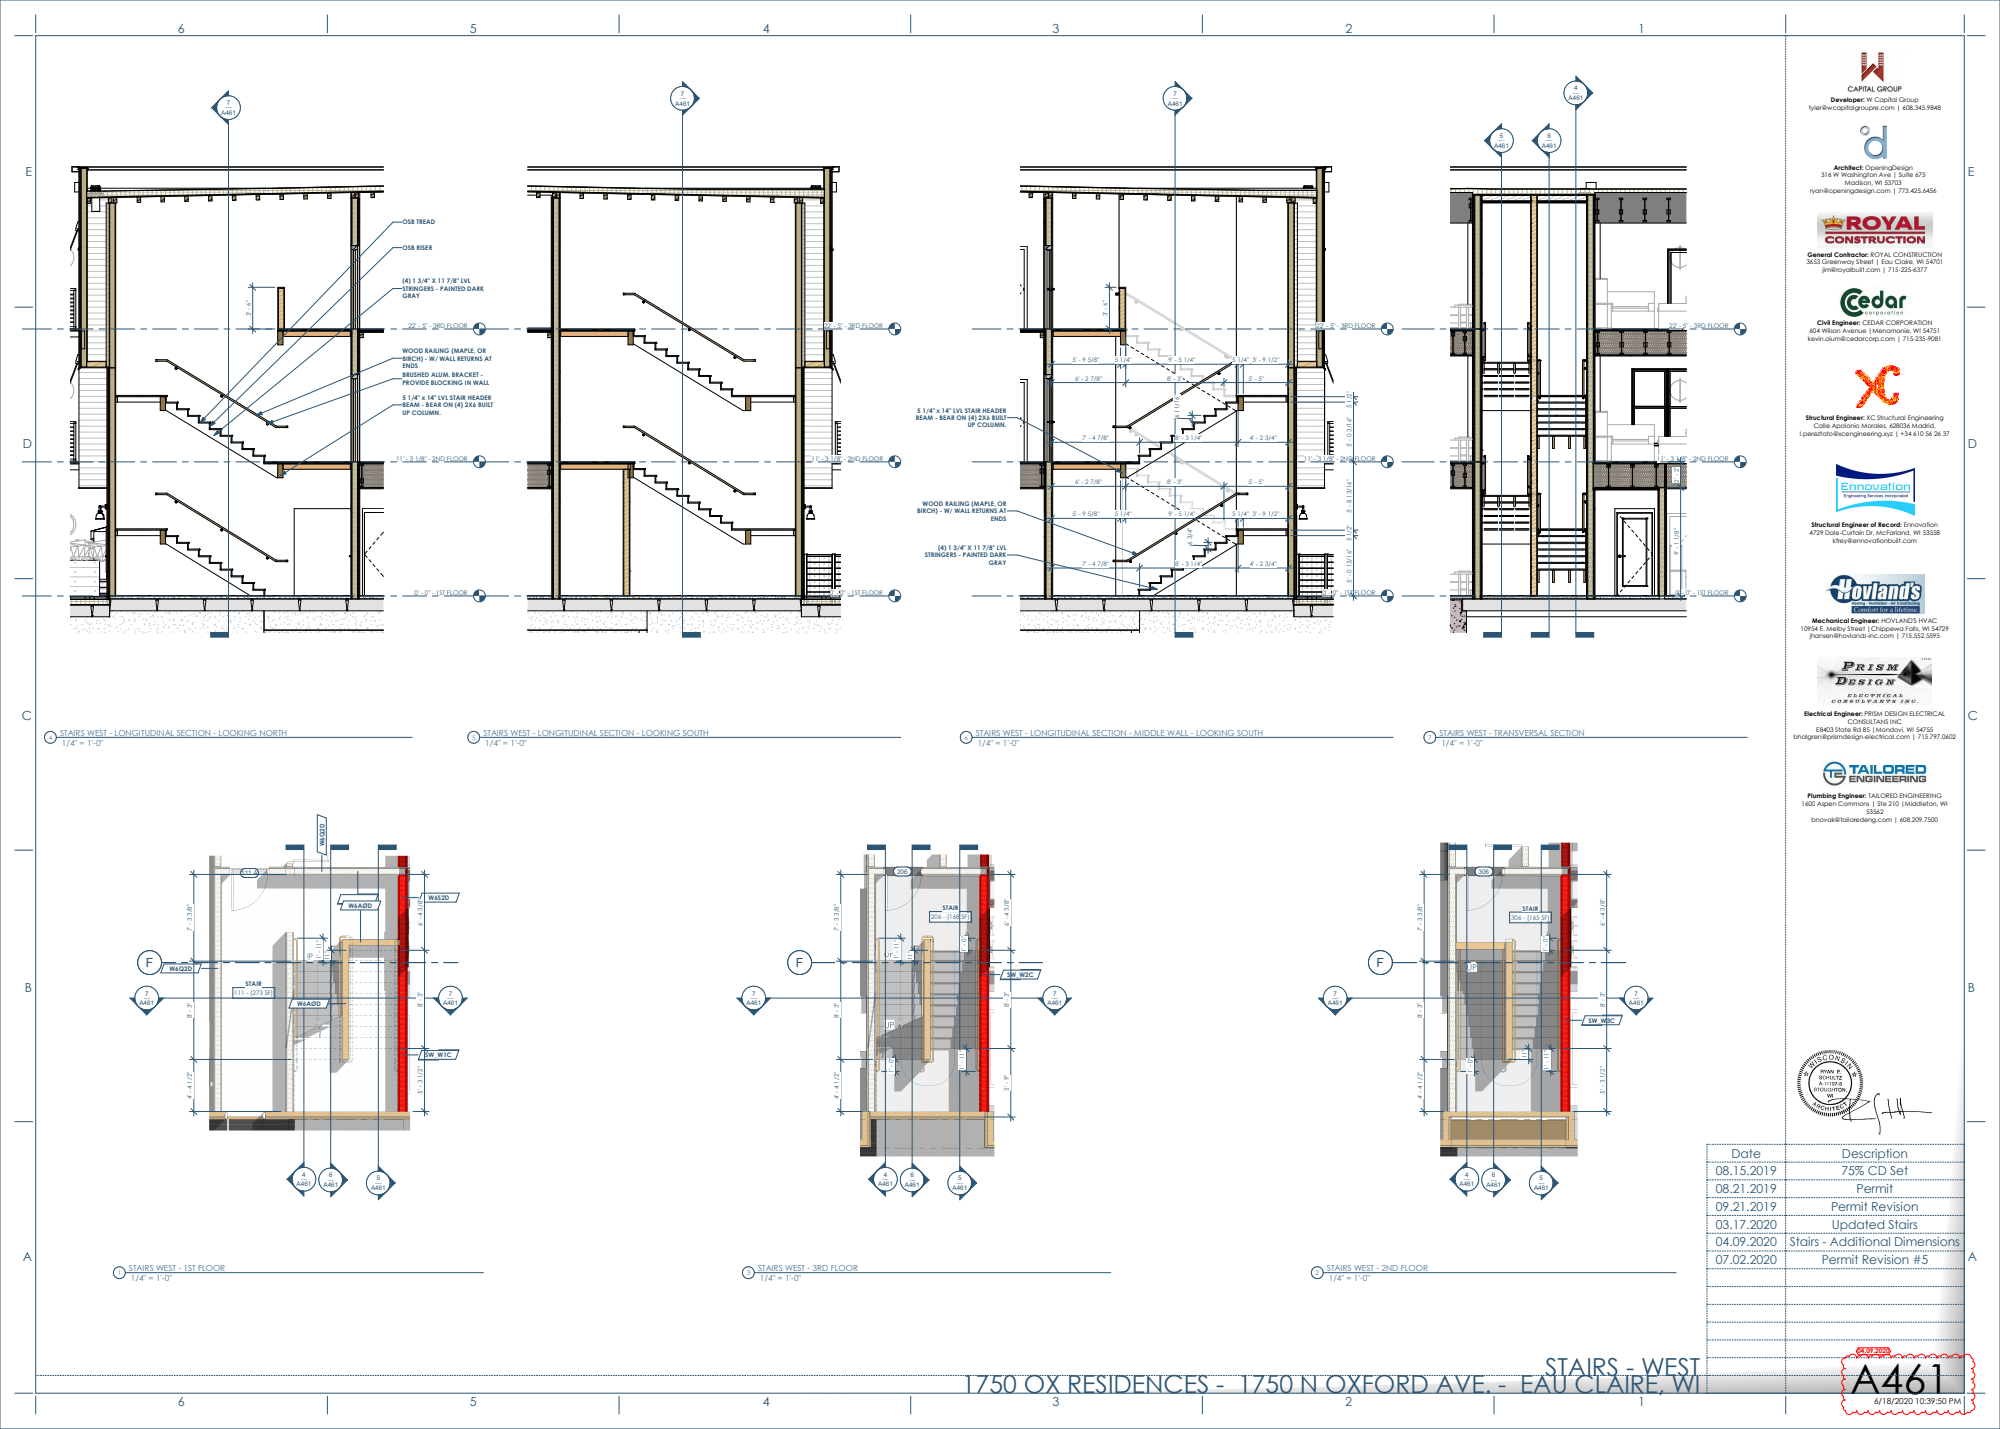
[picture p457: page 1]
STAIR; W6AØD; 0' - 0" - 1ST FLOOR; 11' - 3 1/8" - 2ND FLOOR; 22' - 5" - 3RD FLOOR; OSB RISER; OSB TREAD; UP COLUMN.; GRAY; ENDS; Madison, WI 53703; CONSULTANS INC; STAIRS - WEST; STAIRS WEST - 2ND FLOOR; STAIRS WEST - 3RD FLOOR; STAIRS WEST - TRANSVERSAL SECTION; Date; Description

Developer: W Capital Group

tyler@wcapitalgroupre.com | 608.345.9848

Architect: OpeningDesign
316 W Washington Ave | Suite 675

ryan@openingdesign.com | 773.425.6456

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

(4) 1 3/4" X 11 7/8" LVL
STRINGERS - PAINTED DARK
GRAY

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

WOOD RAILING (MAPLE, OR
BIRCH) - W/ WALL RETURNS AT
ENDS
BRUSHED ALUM. BRACKET -
PROVIDE BLOCKING IN WALL

5 1/4" x 14" LVL STAIR HEADER
BEAM - BEAR ON (4) 2X6 BUILT
UP COLUMN.

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

Structural Engineer of Record: Ennovation
4729 Dale-Curtain Dr, McFarland, WI 53558

kfrey@ennovationbuilt.com

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

Electrical Engineer: PRISM DESIGN ELECTRICAL

E8403 State Rd 85 |Mondovi, WI 54755

STAIRS WEST - LONGITUDINAL SECTION - LOOKING NORTH

STAIRS WEST - LONGITUDINAL SECTION - LOOKING SOUTH

STAIRS WEST - LONGITUDINAL SECTION - MIDDLE WALL - LOOKING SOUTH

bhalgren@prismdesign-electrical.com | 715.797.0602

Plumbing Engineer: TAILORED ENGINEERING
1600 Aspen Commons | Ste 210 |Middleton, WI

bnovak@tailoredeng.com | 608.209.7500

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

STAIRS WEST - 1ST FLOOR

1750 OX RESIDENCES - 1750 N OXFORD AVE. - EAU CLAIRE, WI
