OpeningDesign/CTR/Transfer/20200618 - to State - PERMIT REVISIONS 5/S210 - FRAMING - 1ST FLOOR.pdf

1

2

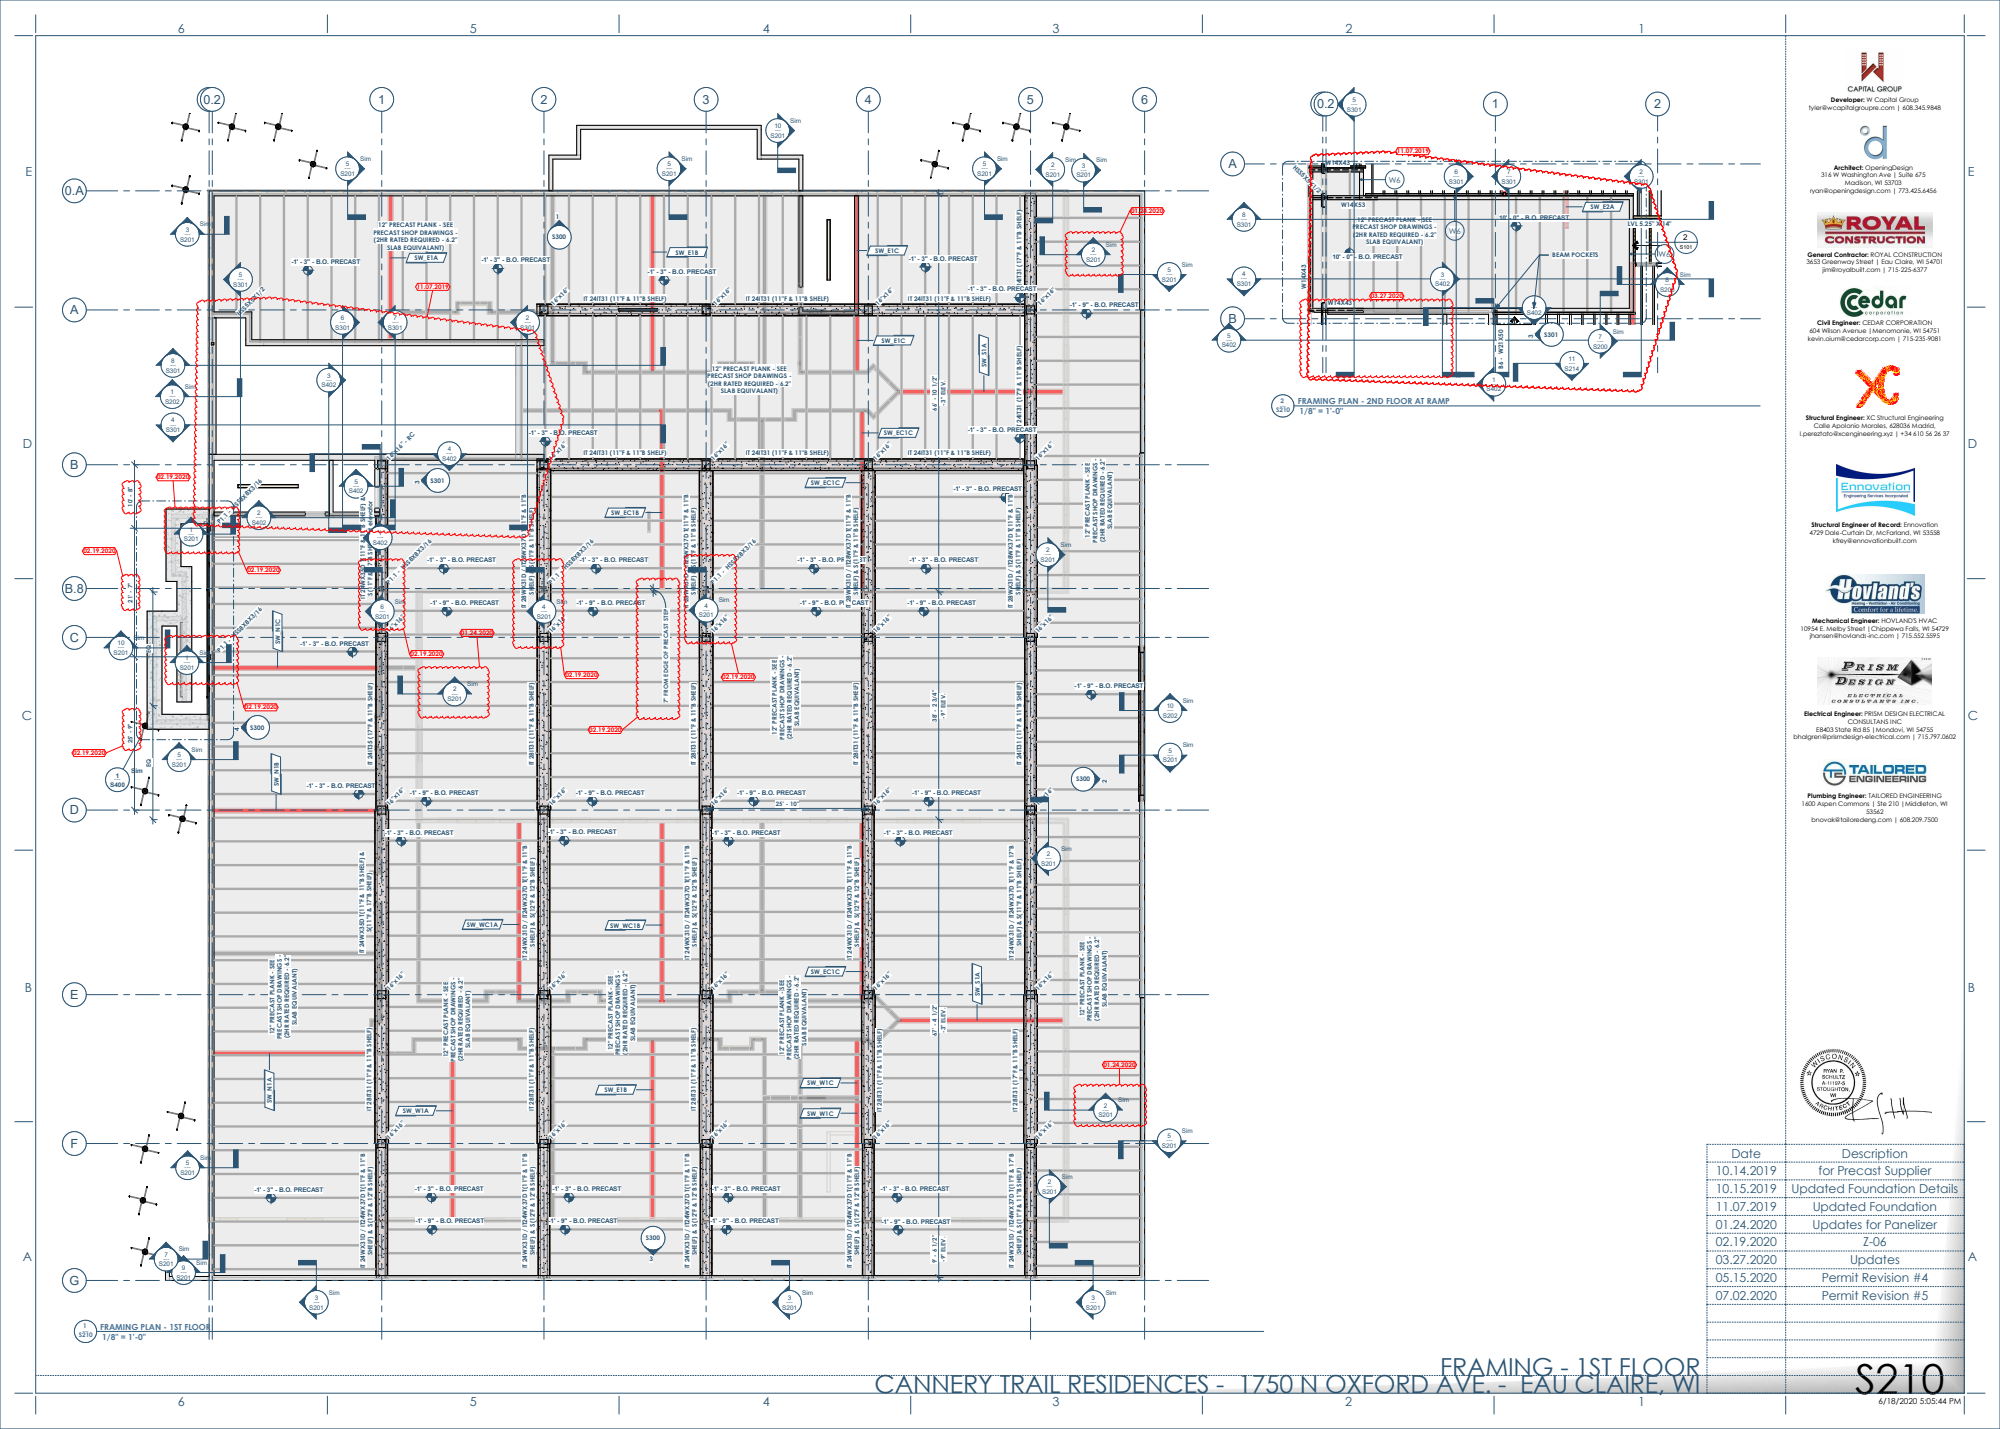
[picture p458: page 1]
-9" ELEV. -3" ELEV.; -9" ELEV.; -3" ELEV.; -1' - 9" - B.O. PRECAST; -1' - 3" - B.O. PRECAST; - 9" - B.O. PRECAST; PRECAST; IT 28IT31 (17"F & 11"B SHELF); IT 28IT31 (11"F & 11"B SHELF); IT 24IT31 (11"F & 11"B SHELF); SHELF) & S(11"F & 11"B SHELF); IT 24WX35D T(11"F & 11"B SHELF) &; SHELF) & S(12"F & 12"B SHELF); S(11"F & 17"B SHELF); (2HR RATED REQUIRED - 6.2"; SLAB EQUIVALANT); P1.1 - HSS8X8X3/16; HSS5X5X1/2; Sim ---; Sim --- ¹⁰ S201; Sim --- --- S400; Sim; Sim --- 0.1; Sim --- B.8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

Developer: W Capital Group

tyler@wcapitalgroupre.com | 608.345.9848

Architect: OpeningDesign
316 W Washington Ave | Suite 675

ryan@openingdesign.com | 773.425.6456

IT 24IT31 (17"F & 11"B SHELF)

12" PRECAST PLANK - SEE
PRECAST SHOP DRAWINGS -
(2HR RATED REQUIRED - 6.2"
SLAB EQUIVALANT)

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

2 FRAMING PLAN - 2ND FLOOR AT RAMP

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

S(11"F & 17"B SHELF) at elevator IT 24IT35 (17"F & 11"B SHELF)

Structural Engineer of Record: Ennovation
4729 Dale-Curtain Dr, McFarland, WI 53558

Sim ---2

kfrey@ennovationbuilt.com

7" FROM EDGE OF PRECAST STEP

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

Electrical Engineer: PRISM DESIGN ELECTRICAL

E8403 State Rd 85 |Mondovi, WI 54755

bhalgren@prismdesign-electrical.com | 715.797.0602

Plumbing Engineer: TAILORED ENGINEERING
1600 Aspen Commons | Ste 210 |Middleton, WI

bnovak@tailoredeng.com | 608.209.7500

10.14.2019 for Precast Supplier
10.15.2019 Updated Foundation Details
11.07.2019 Updated Foundation
01.24.2020 Updates for Panelizer
03.27.2020 Updates

S210 FRAMING - 1ST FLOOR CANNERY TRAIL RESIDENCES - 1750 N OXFORD AVE. - EAU CLAIRE, WI ⁻⁻⁻ 1/8" = 1'-0" S210
