OpeningDesign/CTR/Transfer/20191014 - to state - permit revisions 2/A104 - FLOOR PLANS - ROOF PLAN.pdf

# A301 --- ⁶B A301 --- TPO MEMBRANE TPO MEMBRANE

E

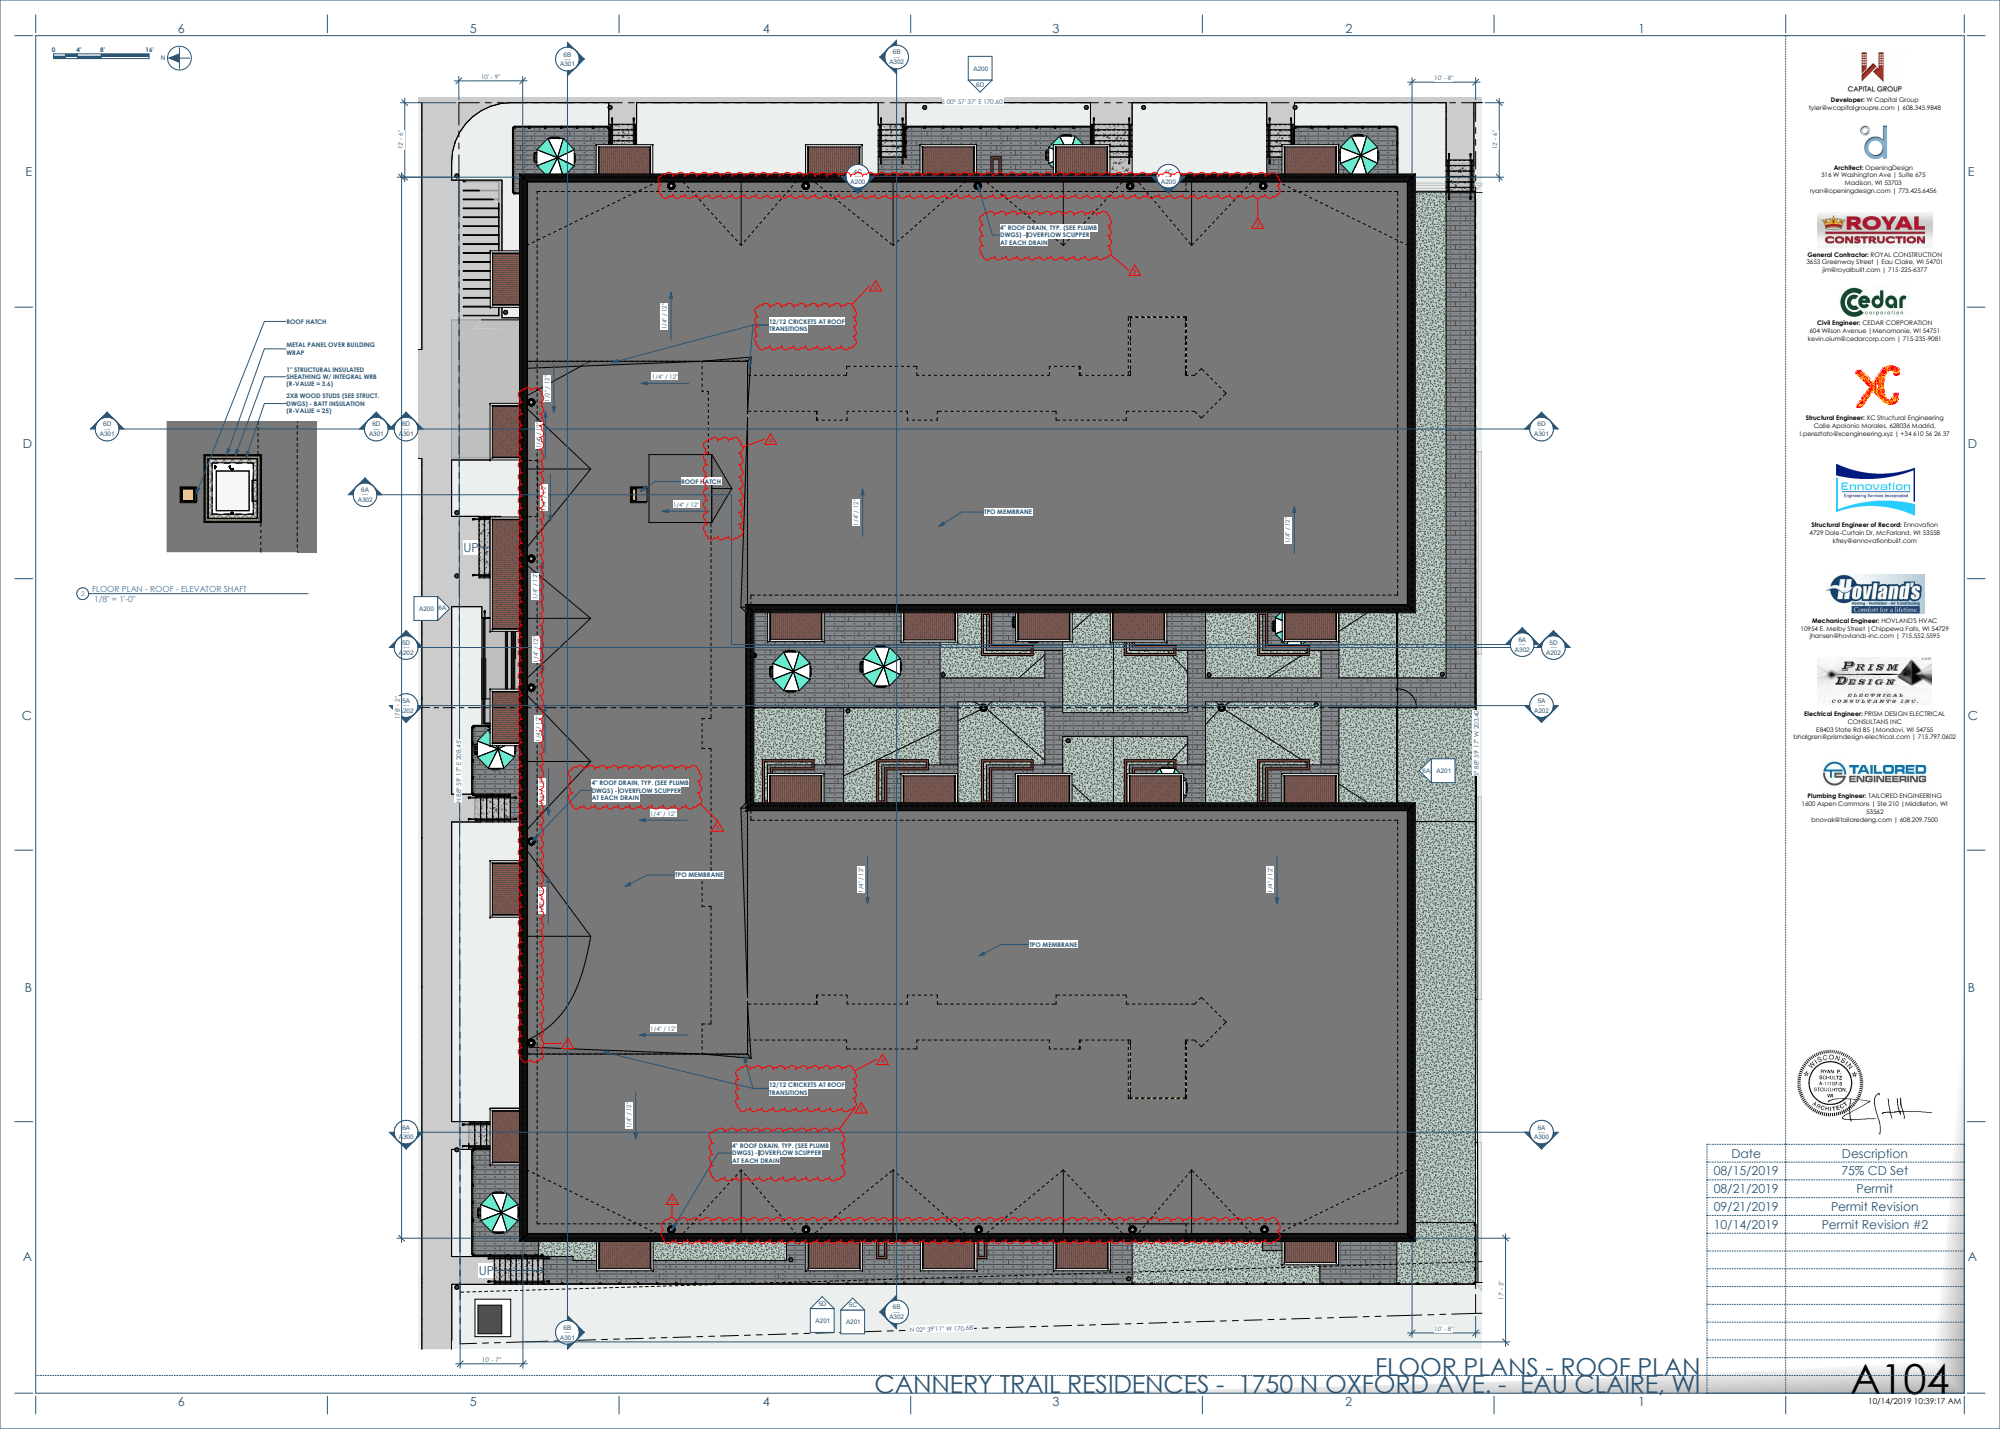
[picture p459: page 1]
TPO MEMBRANE; ROOF HATCH; 6D A301 --- 2X8 WOOD STUDS (SEE STRUCT. DWGS) - BATT INSULATION (R-VALUE = 25); Madison, WI 53703; CONSULTANS INC; Date; Description; 75% CD Set; Permit; Permit Revision; Permit Revision #2

Developer: W Capital Group

tyler@wcapitalgroupre.com | 608.345.9848

Architect: OpeningDesign
316 W Washington Ave | Suite 675

ryan@openingdesign.com | 773.425.6456

4" ROOF DRAIN, TYP. (SEE PLUMB
DWGS) - OVERFLOW SCUPPER
AT EACH DRAIN

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

12/12 CRICKETS AT ROOF
TRANSITIONS

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

METAL PANEL OVER BUILDING
WRAP

1" STRUCTURAL INSULATED
SHEATHING W/ INTEGRAL WRB
(R-VALUE = 3.6)

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

Structural Engineer of Record: Ennovation
4729 Dale-Curtain Dr, McFarland, WI 53558

kfrey@ennovationbuilt.com

1/8" = 1'-0" ² FLOOR PLAN - ROOF - ELEVATOR SHAFT

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

Electrical Engineer: PRISM DESIGN ELECTRICAL

E8403 State Rd 85 |Mondovi, WI 54755

bhalgren@prismdesign-electrical.com | 715.797.0602

Plumbing Engineer: TAILORED ENGINEERING
1600 Aspen Commons | Ste 210 |Middleton, WI

bnovak@tailoredeng.com | 608.209.7500

FLOOR PLANS - ROOF PLAN CANNERY TRAIL RESIDENCES - 1750 N OXFORD AVE. - EAU CLAIRE, WI
