OpeningDesign/CTR/Transfer/20200804 - to GC - approved plans and signed cover sheet/A202 - ELEVATIONS - BUILDING.pdf

1 | 2 | 3 | 4 | 5
0.10.2 | 6

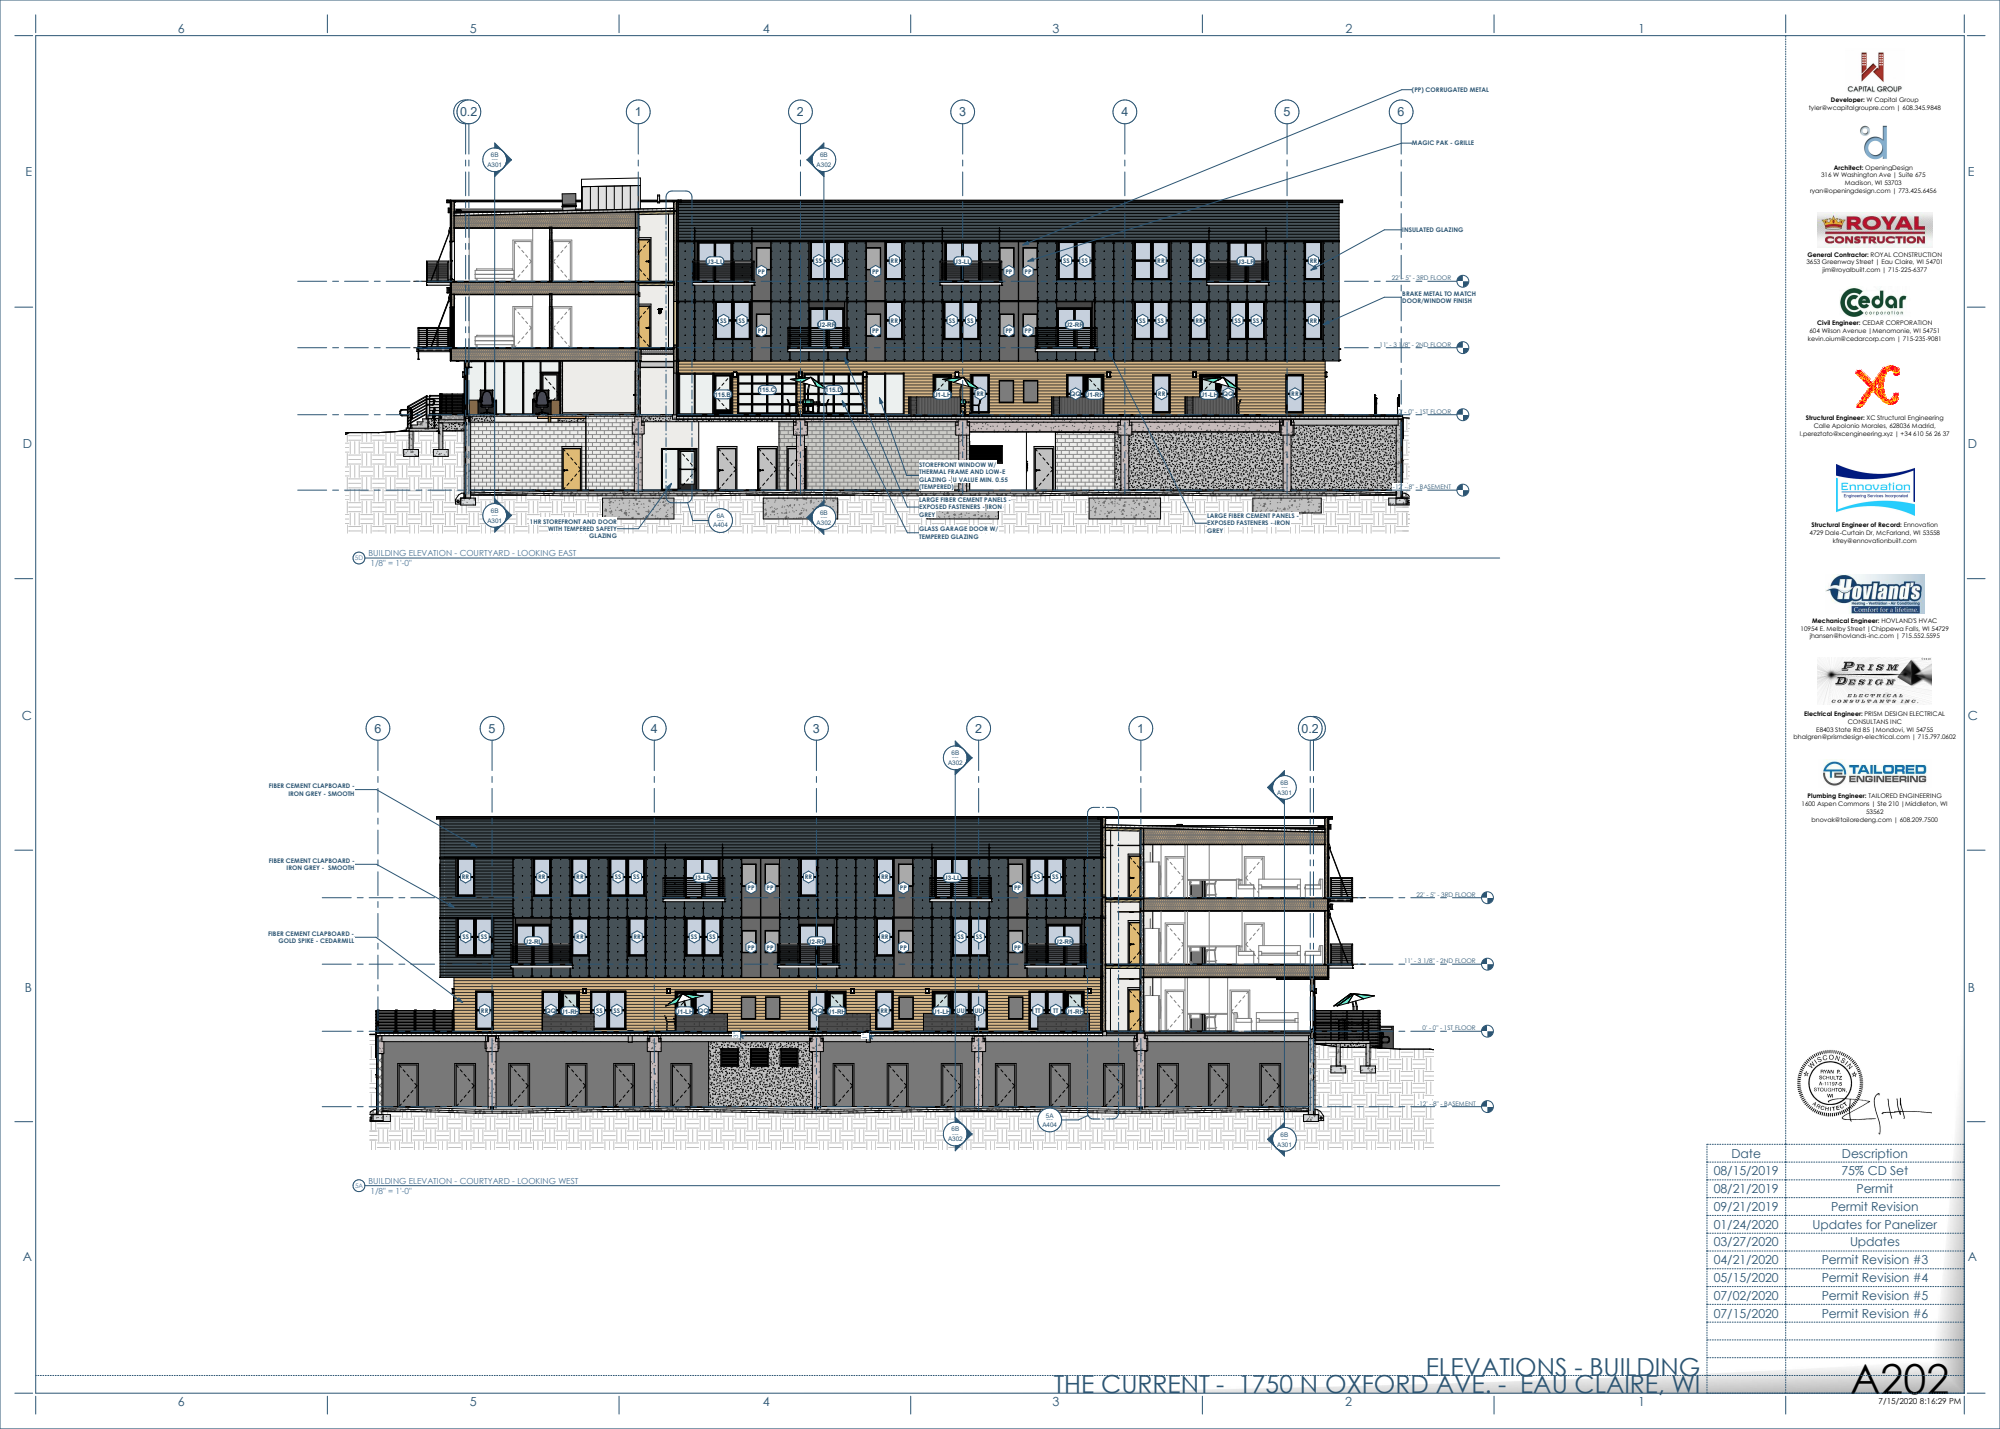
[picture p460: page 1]
0' - 0" - 1ST FLOOR; 11' - 3 1/8" - 2ND FLOOR; -12' - 8" - BASEMENT; 22' - 5" - 3RD FLOOR; GREY; LARGE FIBER CEMENT PANELS -; INSULATED GLAZING; GLAZING; Madison, WI 53703; CONSULTANS INC; ELEVATIONS - BUILDING; Date; Description; 75% CD Set; Permit; Permit Revision; Updates for Panelizer; Updates; Permit Revision #3; Permit Revision #4; Permit Revision #5; Permit Revision #6

(PP) CORRUGATED METAL

Developer: W Capital Group

tyler@wcapitalgroupre.com | 608.345.9848

MAGIC PAK - GRILLE

Architect: OpeningDesign
316 W Washington Ave | Suite 675

ryan@openingdesign.com | 773.425.6456

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

BRAKE METAL TO MATCH
DOOR/WINDOW FINISH

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

STOREFRONT WINDOW W/
THERMAL FRAME AND LOW-E
GLAZING - U VALUE MIN. 0.55
(TEMPERED)

LARGE FIBER CEMENT PANELS -
EXPOSED FASTENERS - IRON

1HR STOREFRONT AND DOOR

GREY

WITH TEMPERED SAFETY

GLASS GARAGE DOOR W/
TEMPERED GLAZING

Structural Engineer of Record: Ennovation
4729 Dale-Curtain Dr, McFarland, WI 53558

kfrey@ennovationbuilt.com

1/8" = 1'-0" ⁵D BUILDING ELEVATION - COURTYARD - LOOKING EAST

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

Electrical Engineer: PRISM DESIGN ELECTRICAL

E8403 State Rd 85 |Mondovi, WI 54755

bhalgren@prismdesign-electrical.com | 715.797.0602

FIBER CEMENT CLAPBOARD -

IRON GREY - SMOOTH

Plumbing Engineer: TAILORED ENGINEERING
1600 Aspen Commons | Ste 210 |Middleton, WI

bnovak@tailoredeng.com | 608.209.7500

GOLD SPIKE - CEDARMILL

1/8" = 1'-0" ⁵A BUILDING ELEVATION - COURTYARD - LOOKING WEST

THE CURRENT - 1750 N OXFORD AVE. - EAU CLAIRE, WI
