OpeningDesign/CTR/Transfer/20200804 - to GC - approved plans and signed cover sheet/A201 - ELEVATIONS - BUILDING.pdf

# 11' - 3 1/8" - 2ND FLOOR -12' - 8" - BASEMENT

1 | 2 | 3 | 4 | 5

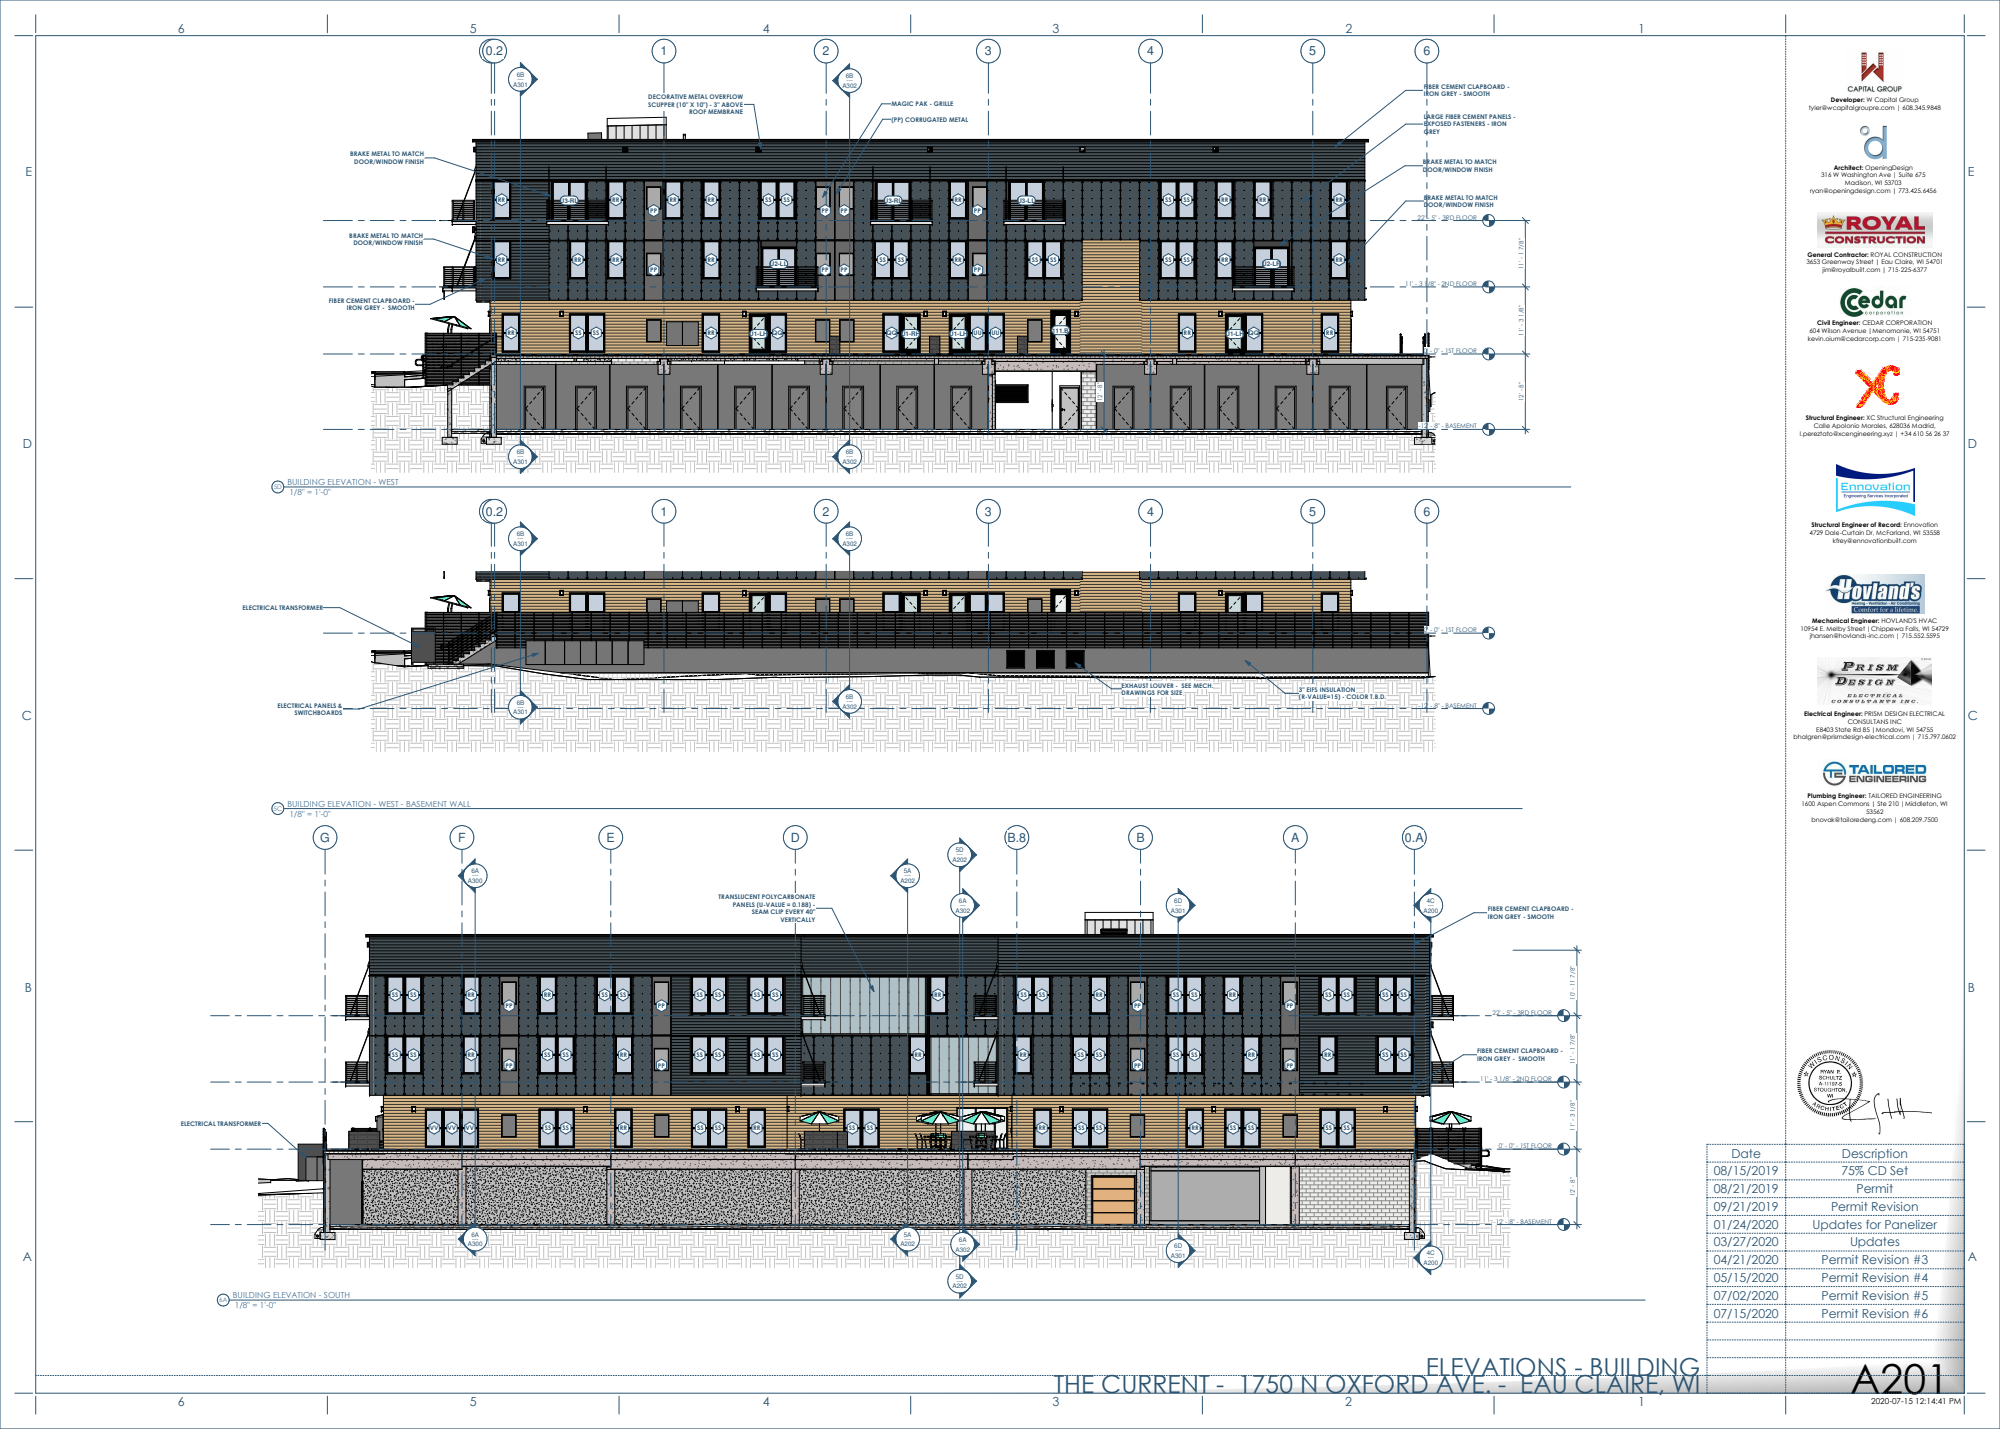
[picture p461: page 1]
0' - 0" - 1ST FLOOR; 22' - 5" - 3RD FLOOR; FIBER CEMENT CLAPBOARD - IRON GREY - SMOOTH LARGE FIBER CEMENT PANELS - EXPOSED FASTENERS - IRON GREY BRAKE METAL TO MATCH DOOR/WINDOW FINISH; ROOF MEMBRANE; 11' - 3 1/8" - 2ND FLOOR -12' - 8" - BASEMENT; FIBER CEMENT CLAPBOARD - IRON GREY - SMOOTH FIBER CEMENT CLAPBOARD - IRON GREY - SMOOTH; 4C A200 --- ⁴C A200 --- ELECTRICAL TRANSFORMER; SSRR VV; SSSS; SSRR; SS SSSS; TRANSLUCENT POLYCARBONATE PANELS (U-VALUE = 0.188) -; VERTICALLY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

DECORATIVE METAL OVERFLOW
SCUPPER (10" X 10") - 3" ABOVE

Developer: W Capital Group

MAGIC PAK - GRILLE

tyler@wcapitalgroupre.com | 608.345.9848

(PP) CORRUGATED METAL

BRAKE METAL TO MATCH
DOOR/WINDOW FINISH

Architect: OpeningDesign
316 W Washington Ave | Suite 675

ryan@openingdesign.com | 773.425.6456

11' - 1 7/8" 11' - 3 1/8" 12' - 8" FIBER CEMENT CLAPBOARD - IRON GREY - SMOOTH

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

1/8" = 1'-0" ⁵D BUILDING ELEVATION - WEST

Structural Engineer of Record: Ennovation
4729 Dale-Curtain Dr, McFarland, WI 53558

kfrey@ennovationbuilt.com

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

Electrical Engineer: PRISM DESIGN ELECTRICAL

E8403 State Rd 85 |Mondovi, WI 54755

bhalgren@prismdesign-electrical.com | 715.797.0602

Plumbing Engineer: TAILORED ENGINEERING
1600 Aspen Commons | Ste 210 |Middleton, WI

1/8" = 1'-0" ⁵C BUILDING ELEVATION - WEST - BASEMENT WALL

bnovak@tailoredeng.com | 608.209.7500

SEAM CLIP EVERY 40"

1/8" = 1'-0" ⁶A BUILDING ELEVATION - SOUTH

ELEVATIONS - BUILDING THE CURRENT - 1750 N OXFORD AVE. - EAU CLAIRE, WI
