OpeningDesign/CTR/CA/Site Reports and Photos/20200515/13.20.21.jpg

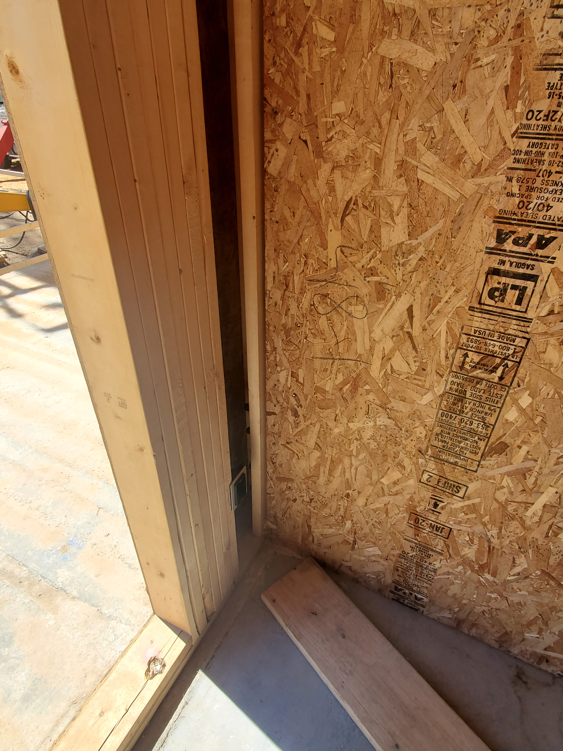
CA/Site Reports and Photos/20200515/13.20.21.jpg
