OpeningDesign/CTR/CA/Site Reports and Photos/20200515/13.22.09.jpg

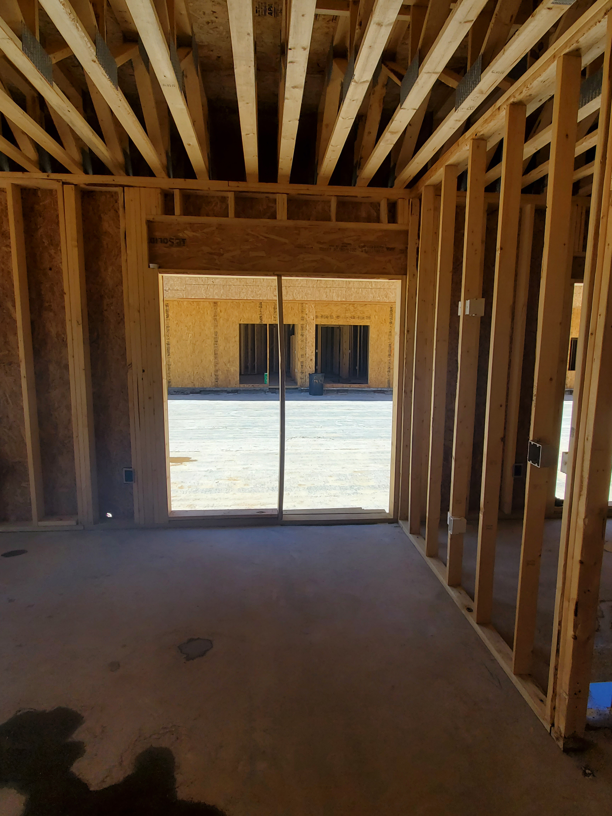
CA/Site Reports and Photos/20200515/13.22.09.jpg
