OpeningDesign/CTR/CA/Site Reports and Photos/20201221/2020-12-21 12.57.19.jpg

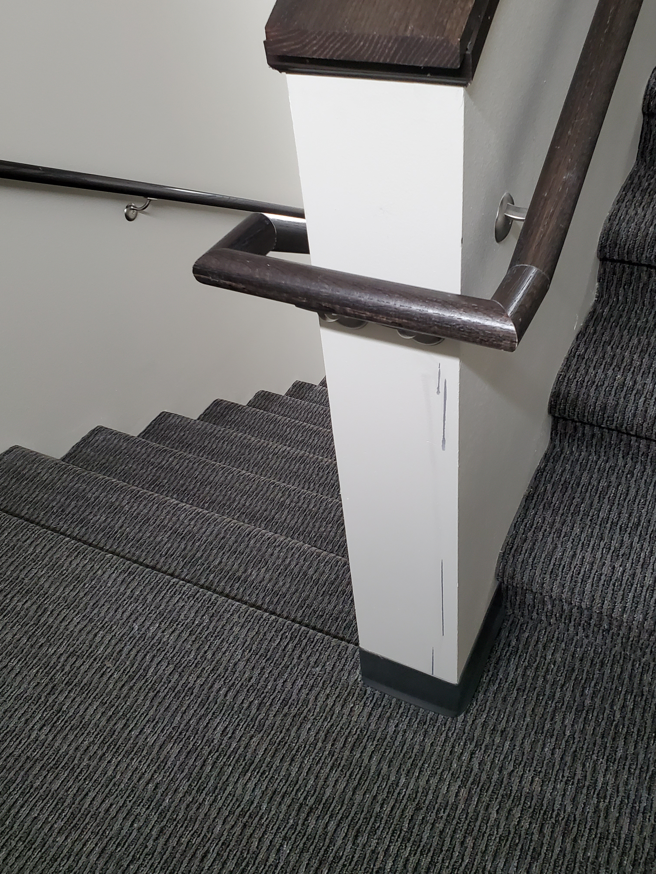
CA/Site Reports and Photos/20201221/2020-12-21 12.57.19.jpg
